LeonLenclos/camera-obscura/contenu/technique/abaque.md

**Ces abaques ont étés mesurés empiriquement avec la première série de process lens testée, à priori, ces objectifs ne seront pas utilisés dans la remorque.**

En fait c'est drôle parce que à l'époque où on a fait ces abaques on avait vraiment zéro connaissance théorique. Un peu après on a appris l'existence de *la relation de conjugaison* :

> l'inverse de la focale est égale à la somme des inverses des distances objet-lentille et image-lentille

Et du coup ces données quand on les regarde aujourd'hui on peut voir qu'ils vérifient cette loi (de manière très approximative car on ne mesurait pas vraiment les distances au centre optique de la lentille). 

## Les abaques

Pour le Apo-Nikkor 610mm posé contre la vitre à l'intérieur de la CO

| Distance Objet-Vitre | Distance Vitre-Image |
|---|---|
| 70 cm | 320 cm |
| 100 cm | 155 cm |
| 200 cm | 91 cm |
| 800 cm | 70 cm |
| infini | 68 cm |

Pour le Apo-Nikkor 610mm sur la planchette du soufflet de la caméra 04 (sprinter)

| Distance Objet-planchette | Distance plachette-Image |
|---|---|
| 295 cm | 77 cm |
| 149 cm | 100 cm |
| 110 cm | 125 cm |
| 97 cm | 150 cm |

Pour le Rotenstock 360mm posé contre la vitre à l'intérieur de la CO

| Distance Objet-Vitre | Distance Vitre-Image |
|---|---|
| 40 cm | 172 cm |
| 70 cm | 72 cm |
| 100 cm | 57 cm |
| 200 cm | 46 cm |
| 800 cm | 41 cm |
| infini | 39 cm |

Pour le Wray Lustrar 1060 mm sur la planchette du soufflet de la caméra 04 (sprinter)

| Distance Objet-planchette | Distance plachette-Image |
|---|---|
| infini | 117 cm |
| 360 cm | 150 cm |
| 280 cm | 175 cm |
| 210 cm | 200 cm |
