LeonLenclos/camera-obscura/contenu/technique/futs.md

# Fûts d'objectifs

Les lentilles sont placées dans des fûts qui se montent sur la tourelle.

Les dimensions de nos fûts sont calquées sur celles d'un fût acheté avec une lentille de 2250mm ø154

On identifie un fût avec un nom indiquant le diamètre de la lentille et la version. Par exemple la première version des fûts pour lentilles de ø154 s'appelle *154V1*

{% include pdf.html url="/contenu/plans/fut.pdf" %}

## Découpe laser

Fichiers :
- [Plan 138V1](/contenu/plans/fut138V1-laser.dxf)
- [Plan 154V1](/contenu/plans/fut154V1-laser.dxf)
- [Plan 80V1](/contenu/plans/fut80V1-laser.dxf)

## Détails

Les fûts sont fabriqués avec un assemblage de bagues découpées à la découpeuse laser. Chaque bague est identifiée par un nom gravé sur la bague. Le nom de la bague indique le modèle du fût et une lettre par exemple, la première bague d'un fût 154V1 porte le nom *154V1/A*

Bagues :

- Bague A : Son diamètre exterieur permet de s'encastrer dans la tourelle.
- Bague B : Il y en a 2. Ce sont les bagues les plus larges, elle maintiennent la lentille.
- Bagues C : Le diamètre interieur de ces bagues est ajusté au diamètre de la lentille. Selon l'epaisseur de la lentille il peut y avoir 0, 1 ou plusieurs bagues de ce type.
- Bague D : Une bague dans un autre materiaux d'une epaisseure choisie pour adapter le fût à l'epaisseur de la lentille.

Vis :

- 6 vis M3. L = epaisseur de la lentille + 18
- 3 vis M6. L = epaisseur de la lentille + epaisseur de la tourelle + 6
