LeonLenclos/camera-obscura/contenu/ecriture/conduite.md

{% include alert.html type="mettre-a-jour" %}

# Ébauche de conduite

- PLAQUE : titre (Générique début)
- FOCALE FACE : 750 mm
- OBTURATEUR : FACE
- DECORS SOL : chambre

---

- OBTURATEUR : NOIR
- PLAQUE : Prologue
- OBTURATEUR : FACE
- OBTURATEUR : NOIR

---

- PLAQUE : titres (Matin)
- OBTURATEUR : FACE

---

- OBTURATEUR : NOIR
- PLAQUE : OUT
- FOCALE FACE : 1000 mm
- MIROIR 45 : IN
- OBTURATEUR : FACE

---

- OBTURATEUR : NOIR
- MIROIR 45 : OUT
- PLAQUE : titre (niveau de l'eau)
- FOCALE FACE : 750 mm
- OBTURATEUR : FACE

---

- OBTURATEUR : NOIR
- PLAQUE : niveau de l'eau
- OBTURATEUR : FACE

---

- OBTURATEUR : NOIR
- PLAQUE : titre (plein emploi)
- OBTURATEUR : FACE

---

- FOCALE AMICI : 2000 mm
- OBTURATEUR : AMICI

---

- OBTURATEUR : NOIR
- FOCALE FACE : 750 mm
- PLAQUE : titre (periode heureuse)
- OBTURATEUR : FACE

---

- OBTURATEUR : NOIR
- PLAQUE : periode heureuse
- OBTURATEUR : FACE

---

- OBTURATEUR : NOIR
- PLAQUE : titre (lune)
- OBTURATEUR : FACE

---

- OBTURATEUR : NOIR
- DECORS AMICI: cuisine
- FOCALE AMICI : 1000 mm
- OBTURATEUR : AMICI

---

- OBTURATEUR : NOIR
- FOCALE FACE : 750 mm
- PLAQUE : titre (bon sens)
- OBTURATEUR : FACE

---

- PLAQUE : journal

---

- DECORS AMICI : OUT
- OBTURATEUR : AMICI
- FOCALE AMICI : 1000 mm

---

- PLAQUE : OUT
- REFLECTEUR : OUT
- FOND NOIR : IN
- FOCALE FACE : 1000 mm
- OBTURATEUR : FACE

---

- FOCALE FACE : 2000 mm

---

- OBTURATEUR : fondu au noir
- OBTURATEUR : NOIR
- PLAQUE : titre (mutation)
- FOND NOIR : OUT
- REFLECTEUR : IN
- FOCALE FACE : 750 mm
- OBTURATEUR : FACE

---

- OBTURATEUR : NOIR
- PLAQUE : mutation
- OBTURATEUR : FACE

---

- OBTURATEUR : NOIR
- PLAQUE : titre (vacances)
- OBTURATEUR : FACE

---

- PLAQUE : photo vacances 1

---

- PLAQUE : photo vacances 2

---

- PLAQUE : photo vacances 3

---

- OBTURATEUR : NOIR
- PLAQUE : titre (podium)
- OBTURATEUR : FACE

---

- OBTURATEUR : NOIR
- PLAQUE : podium
- OBTURATEUR : FACE

---

- OBTURATEUR : NOIR
- PLAQUE : titre (embouteillage)
- OBTURATEUR : FACE

---

- OBTURATEUR : NOIR
- DECORS AMICI : voiture 1
- FOCALE AMICI : 1000mm
- OBTURATEUR : AMICI

---

- PLAQUE : maquette printemps
- FOCALE FACE : 750mm
- OBTURATEUR : FACE

---

- FOCALE AMICI : 1000mm
- OBTURATEUR : AMICI

---

- FOCALE FACE : 750mm
- OBTURATEUR : FACE

---

- DECORS AMICI : voiture 2
- FOCALE AMICI : 1000mm
- OBTURATEUR : AMICI

---

- PLAQUE : maquette hiver
- FOCALE FACE : 750mm
- OBTURATEUR : FACE

---

- OBTURATEUR : NOIR
- PLAQUE : titre (blague)
- OBTURATEUR : FACE

---

- DECORS AMICI : OUT
- FOCALE AMICI : 750mm
- OBTURATEUR : AMICI

---

- OBTURATEUR : NOIR
- PLAQUE : titre (periode malheureuse)
- OBTURATEUR : FACE

---

- PLAQUE : periode malheureuse

---

- OBTURATEUR : NOIR
- PLAQUE : titre (golden record)
- OBTURATEUR : FACE

---

- PLAQUE : golden record 1

---

- PLAQUE : golden record 2

---

- PLAQUE : golden record 3

---

- OBTURATEUR : NOIR
- PLAQUE : titre (froid)
- OBTURATEUR : FACE

---

- FOCALE AMICI : 1000 mm
- OBTURATEUR : AMICI

---

- OBTURATEUR : NOIR
- PLAQUE : titre (comportement)
- FOCALE FACE : 750mm
- OBTURATEUR : FACE

---

- PLAQUE : comportement 1

---

- PLAQUE : comportement 2

---

- OBTURATEUR : NOIR
- PLAQUE : titre (mode)
- OBTURATEUR : FACE

---

- PLAQUE : photo mode

---

- OBTURATEUR : NOIR
- PLAQUE : titre (conversation)
- OBTURATEUR : FACE

---

- FOCALE AMICI : 750 mm
- OBTURATEUR : AMICI

---

- MIROIR 45 : IN
- PLAQUE : OUT
- DECORS SOL : briques
- FOCALE FACE : 1000mm
- OBTURATEUR : FACE

---

- FOCALE AMICI : 1000 mm
- OBTURATEUR : AMICI

---

- FOCALE FACE : 750mm
- OBTURATEUR : FACE

---

- FOCALE AMICI : 1000 mm
- OBTURATEUR : AMICI

---

- FOCALE FACE : 750mm
- OBTURATEUR : FACE

---

- OBTURATEUR : NOIR
- MIROIR 45 : OUT
- PLAQUE : titre (chanson)
- OBTURATEUR : FACE

---

- PLAQUE : OUT
- MIROIR 45 : IN

---

- MIROIR INCRUST : IN

---

- OBTURATEUR : NOIR
- PLAQUE : epilogue 1
- OBTURATEUR : FACE

---

- PLAQUE : epilogue 2

---

- PLAQUE : titre (generique de fin)

---

- OBTURATEUR : NOIR
