LeonLenclos/camera-obscura/contenu/objet/photos.md

# Photos

Si possibles imprimées en positif sur papier transparent (comme des diapositives). 1000×730 mm

- 3 photos de vacances à Saint-Tropez
- Une photo typique des années 2200
- La photo du journal.
