LeonLenclos/camera-obscura/contenu/prototypes/camera00.md

#  Mini Camera obscura

| prototype n° | 00 |
|---|---:|
| nom vernaculaire |  Mini camera obscura |
| début construction | mars 2023 |
| nombre de spectateur·ices | 1 |
| taille de l'image | 4×4 cm |
| distance de tirage min-max  | 45.5mm |
| dimensions exterieures | ? |
| objectif monté | Helios 44-2 / 2/58mm |

mini_chambre_2

## Description générale
En regardant à l'intérieur de cette camera obscura, on découvre une image à l'endroit d'environ 4 cm x 4 cm de ce qui est devant nous.

proto_0

## Allure
Une boite noire de forme parallélépipédique. L'image est projetée sur un dépoli à l'arrière du tube. Un prisme de Dove est placé devant l'objectif.

mini_chambre_3
## Matériaux

### Parois
- Carton-bois

### Écran
- Toile de rétroprojection (translucide/dépoli) tendue sur cadre acier

### Objectif
- objectif 24x36 monture M42 (Helios 44-2 / 2/58mm) 

### Accessoires
- L'objectif et le dépoli sont fixés sur des planchettes maintenues dans des rigoles.

## Évaluation des avantages et des inconvénients

### Avantages
- très léger
- parfait pour des tests

### Inconvénients
- image petite et tronquée
