LeonLenclos/camera-obscura/contenu/prototypes/camera03.md

#  Chambre grand format

| prototype n° | 03 |
|---|---:|
| nom vernaculaire | Chambre grand format |
| début construction | mars 2023 |
| nombre de spectateur·ices | 1 |
| taille de l'image | 100×73 cm |
| distance de tirage min-max  | ? |
| dimensions exterieures | ? |
| objectif monté | Process lens NIKON APO NIKKOR 9/610mm |

chambre_grand_format

## Description générale

En regardant dans le viseur situé à l'arrière de cette camera obscura, on observe une image à l'envers d'environ 100 cm x 73 cm (format 1,37) de ce qui est devant nous.

chambre_grand_format

## Allure

Une boite noire de forme pyramidale couchée, fixée sur un pied de projecteur fait office de viseur de champ. Elle est prolongée par un long soufflet blanc construit en deux parties et se termine par le support de l'objectif, lui-même fixé sur un pied. La forme évoque les chambres photographiques ultra grand format. Un pied intermédiaire limite l'affaissement du soufflet.

proto_03

## Matériaux

### Chassis
- Tube d'acier soudé (20 mm x 20 mm).

### Parois
- Contreplaqué 5 mm

chambre_grand_format

### Écran
- Toile de rétroprojection (translucide/dépoli) tendue sur cadre bois

### Objectif
- Process lens NIKON APO NIKKOR 9/610mm

apo_nikkor_9_610mm_2

### Accessoires

- Pour retourner l'image, il est envisagé d'utiliser un prisme en toit d'Amici, fabriqué avec 2 miroirs à 90°.

## Évaluation des avantages et des inconvénients

### Avantages
- image dans l'axe
- grand format
- grande amplitude de réglage du tirage

chambre_grand_format

### Inconvénients
- encombrement (ne passe pas les portes)
- à l'envers

## Usage

Ce prototype n'existe plus car le grand soufflet sert aussi au prototype sprinter et sera utilisé dans la remorque définitive. 

## Détails de construction et description technique

cotes proto02

### Soufflet

chambre_grand_format_1

- [Patron soufflet A en dxf](/contenu/plans/soufflet-cam03-A.dxf)
- [Patron soufflet A en pdf pour aperçu](/contenu/plans/soufflet-cam03-A.pdf)
- [Patron soufflet B en dxf](/contenu/plans/soufflet-cam03-B.dxf)
- [Patron soufflet B en pdf pour aperçu](/contenu/plans/soufflet-cam03-B.pdf)

Grand Soufflet :

- Grand cadre : 1000mm x 733mm (collage exterieur)
- Petit cadre : 740mm x 540mm (collage exterieur)
- Largeur plis : 100mm
- nombre de plis : 16

Petit Soufflet : 

- Grand cadre : 740mm x 540mm (collage exterieur)
- Petit cadre : 456mm x 373mm (collage exterieur)
- Largeur plis : 100mm
- nombre de plis : 16

cotes soufflet
cotes soufflet
