LeonLenclos/camera-obscura/contenu/prototypes/camera04.md

#  Chambre Sprinter

## Description générale
Un vehicule type Sprinter Mercedes est transformé en camera obscura en adaptant l'arrière du véhicule pour qu'il accueille un système soufflet/objectif. Un cadre sur lequel est fixé l'écran de 1,40 m x 0,95 m est installé à l'intérieur du camion. plusieurs personnes peuvent visionner simultanément l'image.

[une vidéo de test de la chambre sprinter au Quai des savoirs :](https://vimeo.com/showcase/10324493/video/826499165)

<div style="padding-bottom: 56.25%; max-width: 100%; position: relative;"><iframe src="https://player.vimeo.com/video/826499165?title=0&portrait=0&byline=0" width="800px" height="450px" style="position: absolute; top: 0px; left: 0px; width: 100%; height: 100%;" frameborder="0"></iframe></div>

## Allure
Un utilitaire avec un soufflet qui dépasse à l'arrière.

proto_04

Sprinter au Quai des savoirs

### Chassis
- Sprinter Mercedes

### Écrans testés
- Toile de rétroprojection (translucide/dépoli) tendue sur cadre

### Objectifs testés
- Process lens Wray Lustrar 1060 mm - f/16

wray_lustrar_16_1075mm_1

- Process lens Nikon APO Nikkor 610 mm - f/9
- Lentilles brutes d’opticien 2000mm 1500mm 1000mm 750mm - dia 65mm (ménisque)
- Lentille achromatique 2250 mm - f/14,6
 
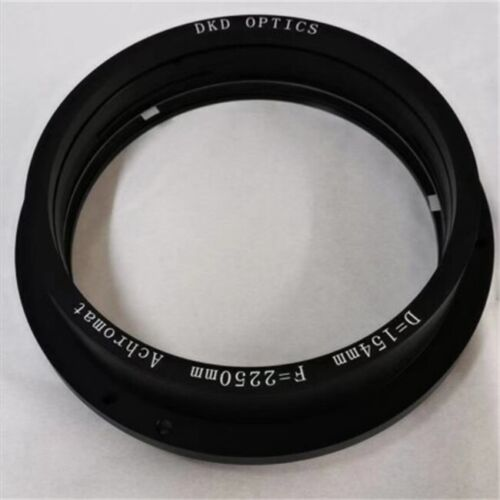
[picture p19: contenu/photos/acchromatic_154mm_f2250.jpg]
Achromatic lens dia:154mmm -_2250mm


### Accessoires
- Pour retourner l'image, un prisme en toit d'Amici, fabriqué avec 2 miroirs à 90°.

test prisme en toit au Quai des savoirs

## Évaluation des avantages et des inconvénients

### Avantages
- image dans l'axe
- ultra grand format

## Construction et améliorations
- Essais en résidence au quai des savoirs et à MIMA avec un écran dépoli.
- Au Quai des Savoirs, l'écran testé est un Teviloj retro translucide. Très lumineux mais trop directif, ce qui explique en partie le vignetage sur les tests.
- À MIMA, l'ecran testé est un Showtex GREY plus de 1300 x 840 mm. moins clair mais plus tolérant sur l'angle de vision.

## Détails de construction et description technique
cotes proto02
