LeonLenclos/camera-obscura/contenu/plans/implantation-carte-ves.pdf

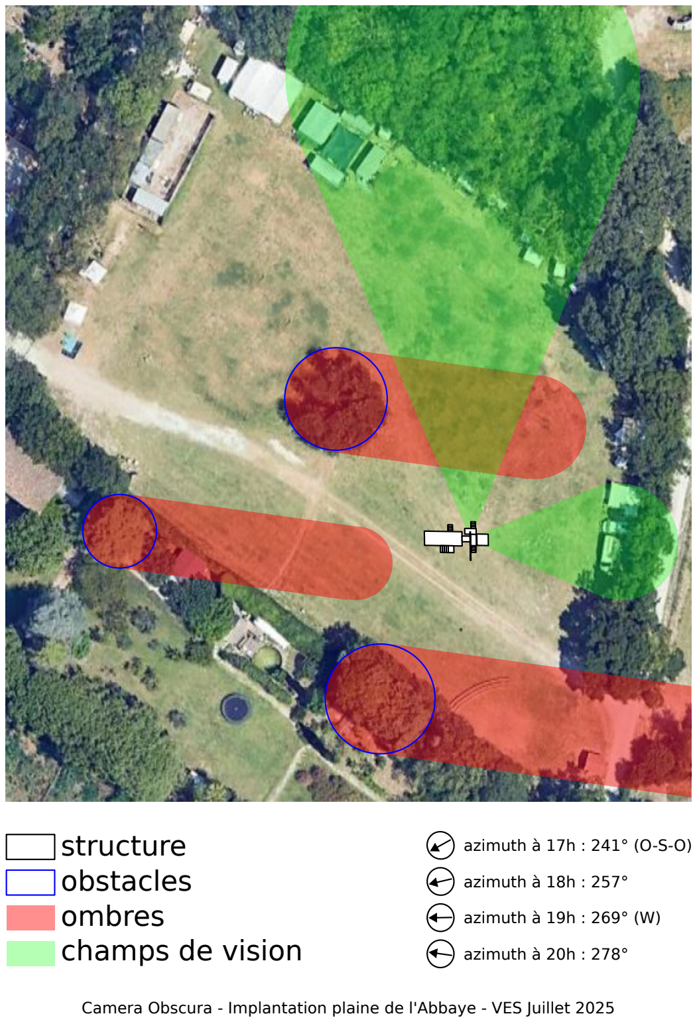
[picture p30: page 1]

# structure obstacles ombres champs de vision

Camera Obscura - Implantation plaine de l'Abbaye - VES Juillet 2025 azimuth à 17h : 241° (O-S-O)

azimuth à 19h : 269° (W)

azimuth à 20h : 278°

azimuth à 18h : 257°
