LeonLenclos/camera-obscura/contenu/plans/implantation-carte-cognac.pdf

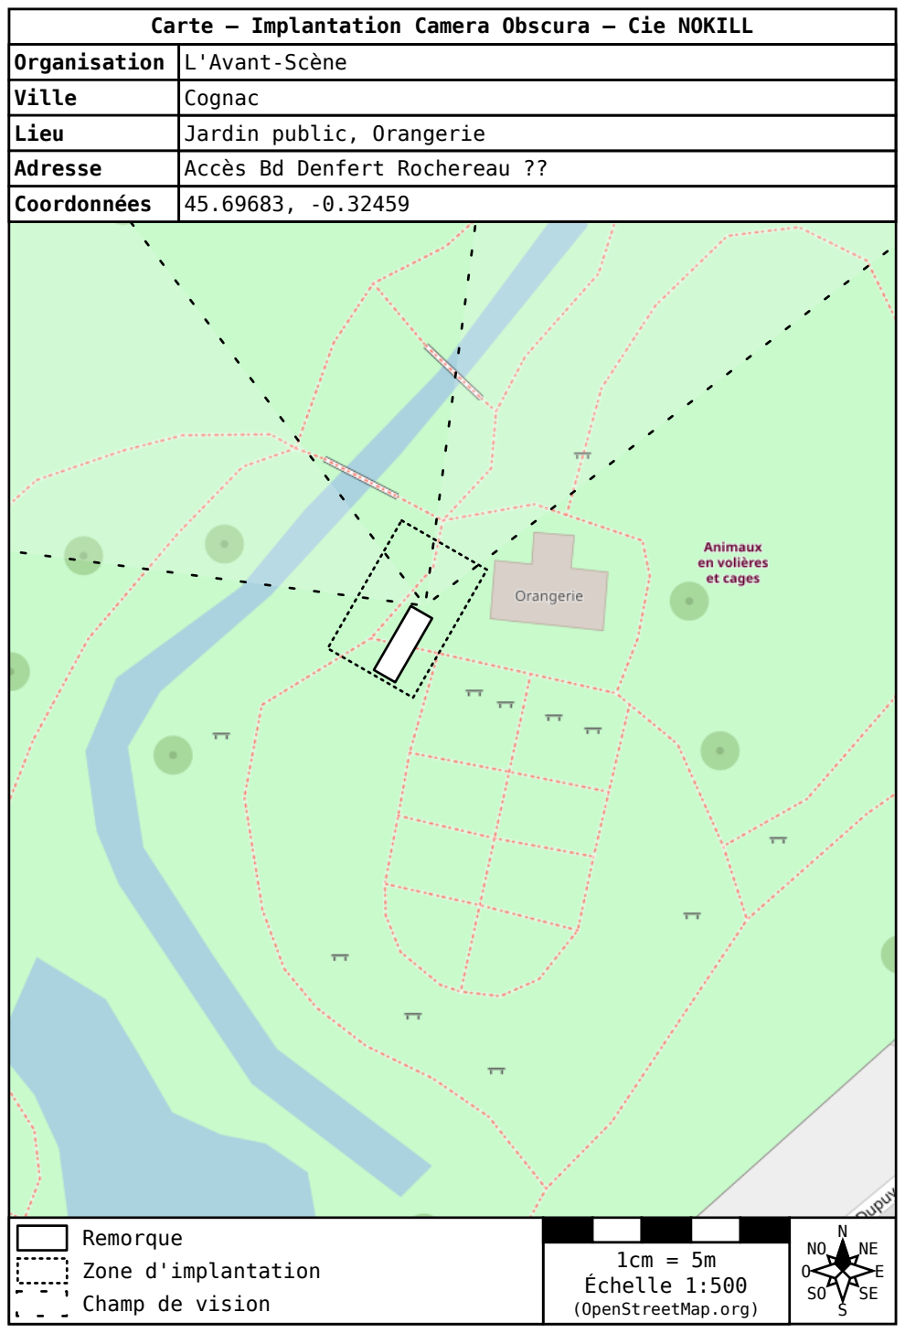
[picture p31: page 1]

Carte — Implantation Camera Obscura — Cie NOKILL
Organisation | L'Avant-Scène
Ville | Cognac
Lieu | Jardin public, Orangerie
Adresse | Accès Bd Denfert Rochereau ??
Coordonnées | 45.69683, -0.32459

(OpenStreetMap.org)

NO | NE
SO | SE

N

S

O | E

Remorque
Zone d'implantation
Champ de vision

Échelle 1:500

1cm = 5m
