LeonLenclos/camera-obscura/contenu/plans/implantation-carte-periscope.pdf

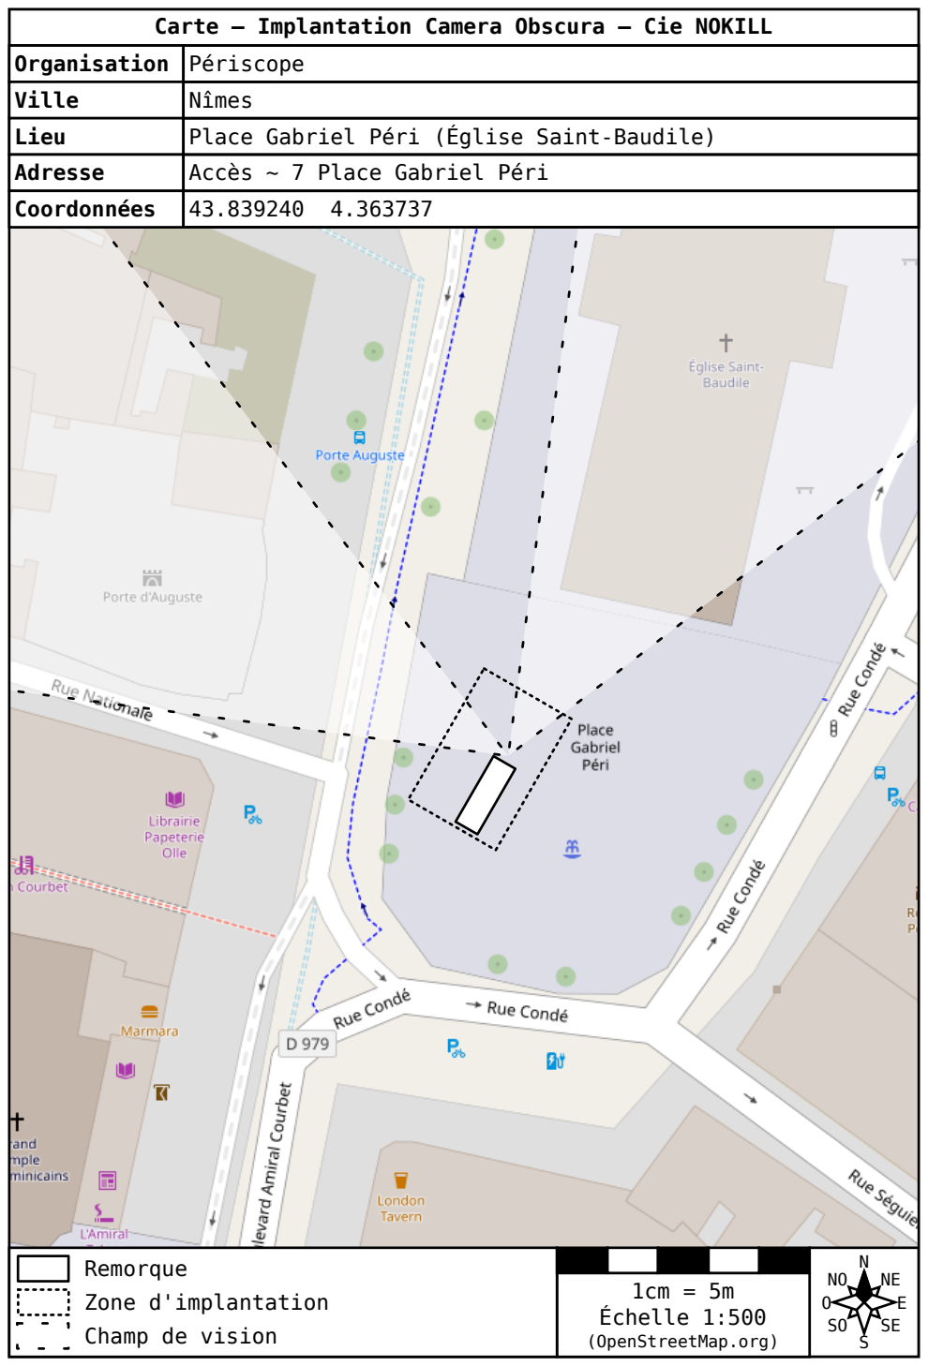
[picture p32: page 1]

Carte — Implantation Camera Obscura — Cie NOKILL
Organisation | Périscope
Ville | Nîmes
Lieu | Place Gabriel Péri (Église Saint-Baudile)
Adresse | Accès ~ 7 Place Gabriel Péri
Coordonnées | 43.839240 4.363737

(OpenStreetMap.org)

NO | NE
SO | SE

N

S

O | E

Remorque
Zone d'implantation
Champ de vision

Échelle 1:500

1cm = 5m
