LeonLenclos/camera-obscura/contenu/objet/rouleau-photo.pdf

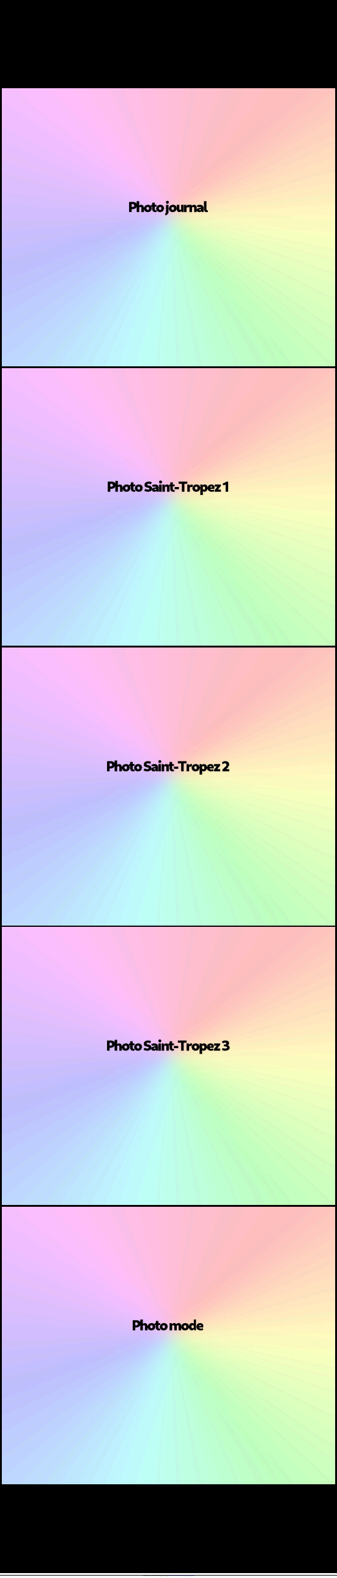
[picture p34: page 1]

Ce document a été généré le 28/05/2024 à partir de la page camera-obscura.cienokill.fr/contenu/objet/rouleau-photo.md
