LeonLenclos/camera-obscura/contenu/plans/implantation-carte-mima.pdf

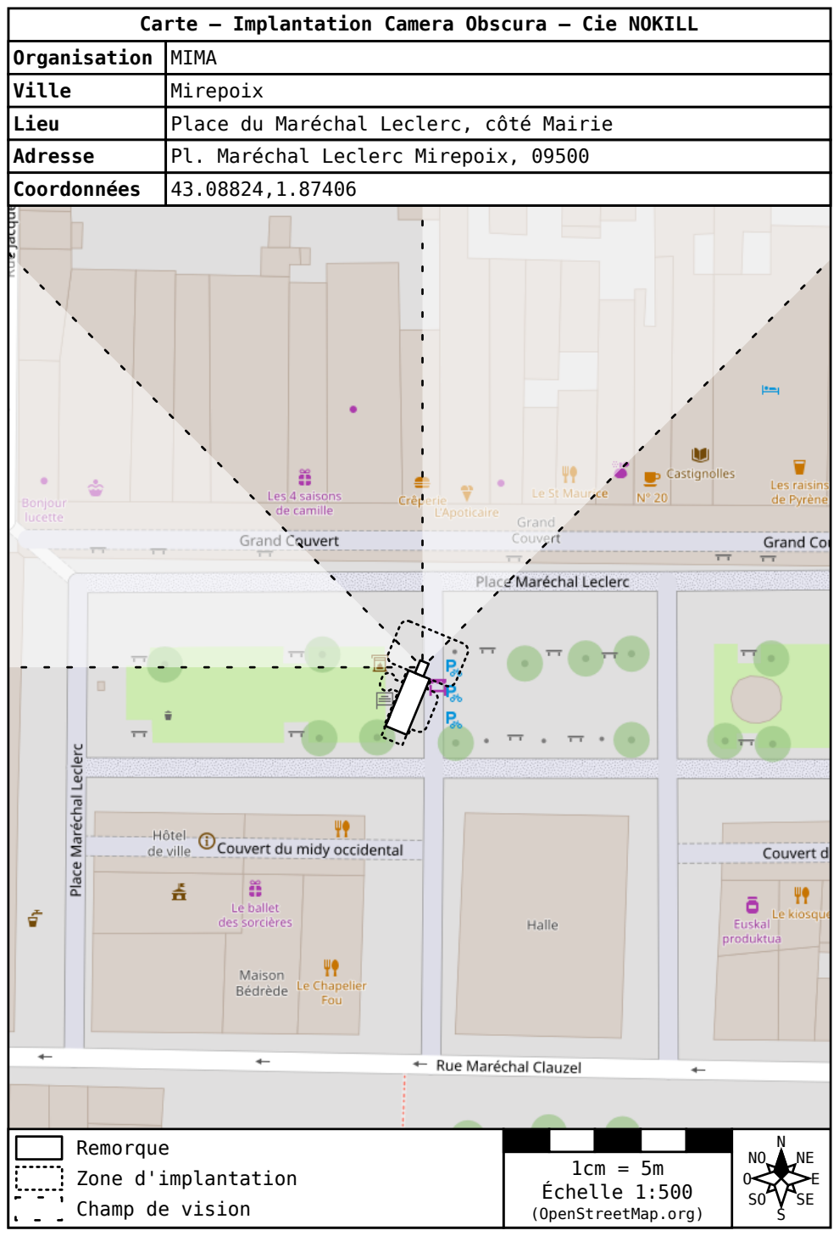
[picture p35: page 1]

Carte — Implantation Camera Obscura — Cie NOKILL
Organisation | MIMA
Ville | Mirepoix
Lieu | Place du Maréchal Leclerc, côté Mairie
Adresse | Pl. Maréchal Leclerc Mirepoix, 09500
Coordonnées | 43.08824,1.87406

(OpenStreetMap.org)

NO | NE
SO | SE

N

S

O | E

Remorque
Zone d'implantation
Champ de vision

Échelle 1:500

1cm = 5m
