LeonLenclos/camera-obscura/contenu/plans/implantation-carte-arto.pdf

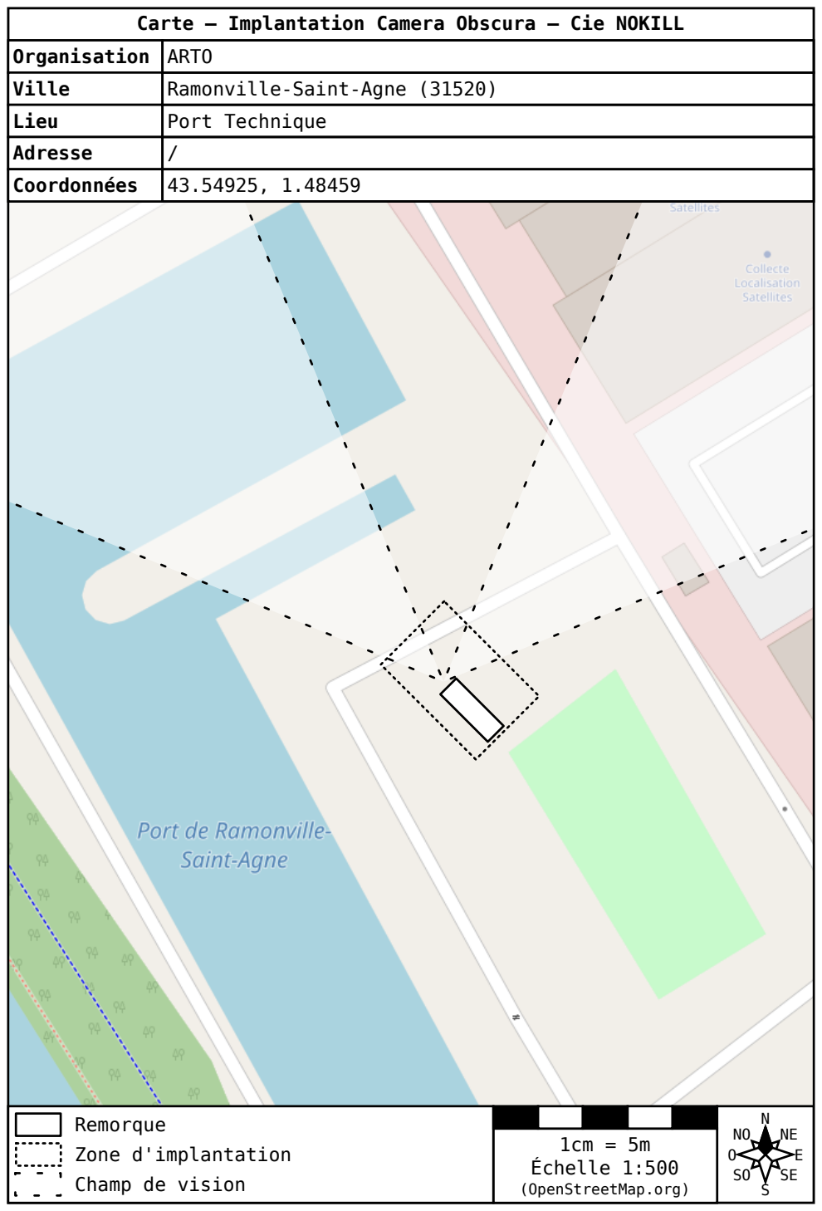
[picture p36: page 1]

Carte — Implantation Camera Obscura — Cie NOKILL
Organisation | ARTO
Ville | Ramonville-Saint-Agne (31520)
Lieu | Port Technique
Adresse | /
Coordonnées | 43.54925, 1.48459

(OpenStreetMap.org)

NO | NE
SO | SE

N

S

O | E

Remorque
Zone d'implantation
Champ de vision

Échelle 1:500

1cm = 5m
