LeonLenclos/camera-obscura/contenu/legal/README.md

# Légal

## Rappel

Camera Obscura est une création de la Cie Nokill, c'est une remorque aménagée en salle de spectacle itinérante. 

## Homologation du véhicule

À compléter

## Établissement Itinérant Recevant du Public

Camera Obscura est un Établissement Recevant du Public (ERP) Itinérant. Cette classification nous oblige à respecter un certain nombre de règles détaillées ci-dessous.

### Classification de l'établissement

Camera Obscura est un **Établissement Recevant du Public Itinérant** (ERP Itinérant) au sens de l'[arrêté du 4 mai 2023 portant expérimentation d'itinérance des établissements recevant du public*](https://www.legifrance.gouv.fr/jorf/id/JORFTEXT000047533626)) car toujours installé pour une durée inférieure à six mois, destinés par conception à être clos et dans lesquels l'effectif admis est inférieur à 700 personnes.

Camera Obscura est un **ERP de type L** au sens du classement établis par l'[article GN1 de l'Arrêté du 25 juin 1980 portant approbation des dispositions générales du règlement de sécurité contre les risques d'incendie et de panique dans les ERP](https://www.legifrance.gouv.fr/loda/article_lc/LEGIARTI000045143487)

Pour rappel Camera Obscura __n'est pas__ soumis aux contraintes s'appliquant aux **Locaux destinés au sommeil** tel que défini par l'[article GN1](https://www.legifrance.gouv.fr/loda/article_lc/LEGIARTI000045143487)

Camera Obscura est un **Établissement Recevant du public** (ERP) de **Catégorie 5** tel que défini par l'[article R143-19 du Code de la construction et de l'habitation](https://www.legifrance.gouv.fr/codes/article_lc/LEGIARTI000043818977) et par l'[Article PE2 de l'Arrêté du 25 juin 1980](https://www.legifrance.gouv.fr/loda/article_lc/LEGIARTI000045143485) car c'est un Établissements de type L (Salle de spectacles, de projections) dans lequel l'effectif admis est inférieur à 50 personnes.

Camera Obscura est un **ERP du second groupe** tel que défini par [Article GN1 de l'arrêté du 25 juin 1980](https://www.legifrance.gouv.fr/loda/article_lc/LEGIARTI000045143487)

Les Ossatures destinées à supporter des personnes (OP) de Camera Obscura sont Catégorisées **OP1** par l'[article 4 de l'annexe de l'arrêté du 25 juillet 2022 fixant les règles de sécurité et les dispositions techniques applicables aux structures provisoires et démontables](https://www.legifrance.gouv.fr/jorf/article_jo/JORFARTI000046144010), car leur hauteur de chute est inférieure à 1,20 mètre.

Les Ossatures d'équipements scéniques (OS) de Camera Obscura sont Catégorisées **OS1** par le [même article](https://www.legifrance.gouv.fr/jorf/article_jo/JORFARTI000046144010), car leur point le plus haut est inférieur à 3,50 mètre.

### Obligations de contrôle, de vérification et d'inspection en matière de solidité et de stabilité

Vu l'[arrêté du 4 mai 2023 portant expérimentation d'itinérance des établissements recevant du public](https://www.legifrance.gouv.fr/jorf/id/JORFTEXT000047533626) ;  
Vu l'[arrêté du 25 juillet 2022 fixant les règles de sécurité et les dispositions techniques applicables aux structures provisoires et démontables](https://www.legifrance.gouv.fr/jorf/id/JORFTEXT000046143966),  

Nous sommes tenu à certaines obligations de contrôle.

#### Partage des obligations entre la compagnie et l'organisation de l'évènement

Les obligations sont partagées entre la compagnie et l'organisation de l'évènement où est joué le spectacle.

La compagnie s'acquitte des obligation désignés comme :

- **obligations du fabricant** (par l'arrêté du 25 juillet 22) ;
- **obligations du propriétaire** (par l'arrêté du 25 juillet 22) ;
- **obligations de l'installateur** (par l'arrêté du 25 juillet 22).

L'organisation de l'évennement s'acquitte des obligations désignées comme :

- **obligations de l'organisateur** (par l'arrêté du 25 juillet 22).

Les obligations désignées comme **obligation de l'exploitant** (par l'arrêté du 4 mai 2023) sont partagées au cas par cas entre la compagnie et l'organisation de l'événement.

#### Obligation de l'organisation de l'événement

La compagnie laisse à la charge de l'organisation de l'événement les obligations suivantes :

- **Inspection en exploitation** : faire procéder à une inspection par un technicien compétant avant l'admission du public conformément à l'[article 40 de l'arrêté du 25 Juillet 2022](https://www.legifrance.gouv.fr/jorf/article_jo/JORFARTI000046144050)
- **Obtenir l'autorisation du maire** : faire parvenir au maire les documents fournis par la compagnie conformément à l'[article 6 de l'arrêté du 4 mai 2023](https://www.legifrance.gouv.fr/jorf/article_jo/JORFARTI000047533639) Pour qu'il délivre une autorisation d'implantation. Ces documents sont le [registre de sécurité](registre-securite.md) (contenant l'attestation de conformité) et le [contrôle de conception](attestation-fabricant-controle-conception.md) (attestation du fabricant). 

Note : L'[article 3 de l'arrêté du 4 mai 2023](https://www.legifrance.gouv.fr/jorf/article_jo/JORFARTI000047533634) dispense l'exploitant de l'obligation d'établir le dossier de sécurité demandé par l'[article 39 de l'arrêté du 25 Juillet 2022](https://www.legifrance.gouv.fr/jorf/article_jo/JORFARTI000046144049)

#### Notice technique

Voir le document : [**Notice technique**](notice-technique.md)

L'[article 36 de l'arrêté du 25 Juillet 2022](https://www.legifrance.gouv.fr/jorf/article_jo/JORFARTI000046144046) nous oblige à fournir une notice technique en tant que fabriquant. Le modèle de cette Notice technique est donné à l'annexe I de l'[arrêté](https://www.legifrance.gouv.fr/jorf/id/JORFSCTA000046143987).

#### Contrôle de la solidité et de la stabilité à la conception (Contrôle de conception)

Voir le document : [**Attestation du fabricant**](attestation-fabricant-controle-conception.md)

L'[article 37 de l'arrêté du 25 Juillet 2022](https://www.legifrance.gouv.fr/jorf/article_jo/JORFARTI000046144047) nous dispense, en tant qu'ensemble démontable de catégories **OP1** et **OS1** de faire l'objet d'un contrôle par un Organisme accrédité ou un Contrôleur technique agréé. 

Nous avons simplement l'obligation de fournir une déclaration du fabricant attestant du respect des dispositions relatives à la solidité et à la stabilité de ce même arrêté.

L'[arrêté du 4 mai 2023](https://www.legifrance.gouv.fr/jorf/id/JORFTEXT000047533626) confirme que cela s'applique à notre établissement en tant qu'**EIRP du second groupe**. 

#### Inspection annuelle

Voir le document : [**Inspection annuelle**](inspection-annuelle.md)

L'[article 7 §3 de l'arrêté du 4 mai 2023](https://www.legifrance.gouv.fr/jorf/article_jo/JORFARTI000047533640) rappelle l'obligation de faire établir un rapport d'inspection annuel par un·e technicien·ne compétent·e. Un tel rapport doit être établis chaque année suite à une visite du ou de la technicien·ne dans un contexte d'exploitation.

#### Vérification de montage

Voir le document : [**Attestation de bon montage**](attestation-bon-montage.md)

L'[article 38 de l'arrêté du 25 Juillet 2022](https://www.legifrance.gouv.fr/jorf/article_jo/JORFARTI000046144048) Précise qu'en tant qu'ensemble démontable de catégories **OP1** et **OS1**, une attestation de bon montage établit à chaque montage par l'installateur vaut document de vérification (L'organisateur n'a pas besoin de faire intervenir un organisme accrédité).

L'attestation pré-remplie ci-dessus a été rédigée en suivant le modèle de l'annexe V de l'[arrêté](https://www.legifrance.gouv.fr/jorf/id/JORFSCTA000046143987)

L'[arrêté du 4 mai 2023](https://www.legifrance.gouv.fr/jorf/id/JORFTEXT000047533626) confirme que cela s'applique à notre établissement en tant qu'**EIRP du second groupe**. 

#### Registre de sécurité

Voir le document : [**Registre de sécurité**](registre-securite.md)

Les articles 6 et 7 de l'[arrêté du 4 mai 2023](https://www.legifrance.gouv.fr/jorf/id/JORFTEXT000047533626) précise qu'un registre de sécurité doit être tenu et mis à disposition des autorités.

Le registre de sécurité est composé de deux parties, la première partie constitue l'[**attestation de conformité**]](contenu-attestation-conformite.md) qui est délivrée par le Préfet pour une durée d'un an. La deuxième partie est le [**registre d'exploitation**](contenu-registre-exploitation.md)

#### Documents annexes

Les documents cités ci-dessus nécessitent d'autres documents en annexes :

- [**Schéma d'implantation**](../technique/implantation) (Ce document est spécifique à chaque évennement)
- [**Notice de montage**](../technique/notice-montage.md)
- **Rapport de vérifications des installations électriques**  (voir [Cet article (§2 en ce qui nous concerne)](https://www.legifrance.gouv.fr/jorf/article_jo/JORFARTI000046144037))
- **Plan des installations de ventilation**
- [**Consignes de sécurité**](consignes-de-securite.md)
- **Historique des exercices contre l'incendie**
- [**PV de réaction au feu**](pv-reaction-feu.pdf)

#### Lettre type

Voir le document : [**Demande d'attestation de conformité**](lettre-prefet.md)

## TODO

### TODO Administratif 

- Passage à la DREAL
- Finir de rédiger tous les documents ci-dessus
- Demande d'attestation de conformité au prefet

### TODO Materiels

Modification matérielles a effectuer pour etre en accord avec tous les trucs cités au dessus

#### Mise aux normes de l'installation électrique

- Installer un tableau

#### Installer un extincteur

- 6L à eau pulverisée

#### Marquages des éléments démontables 

Selon [cet article](https://www.legifrance.gouv.fr/jorf/article_jo/JORFARTI000046144015)

Il faut marquer :

- tous les éléments des escaliers
- les éléments de la structure scénique

Il faut indiquer :

- le nom ou le sigle du fabricant
- la référence du produit
- l'année de fabrication

Un marquage au feutre indélibile peut convenir. La reference de l'element est deja souvent présente il faut ajouter "NOK 2024".
