LeonLenclos/camera-obscura/contenu/ecriture/README.md

# Écriture

*En travaux*

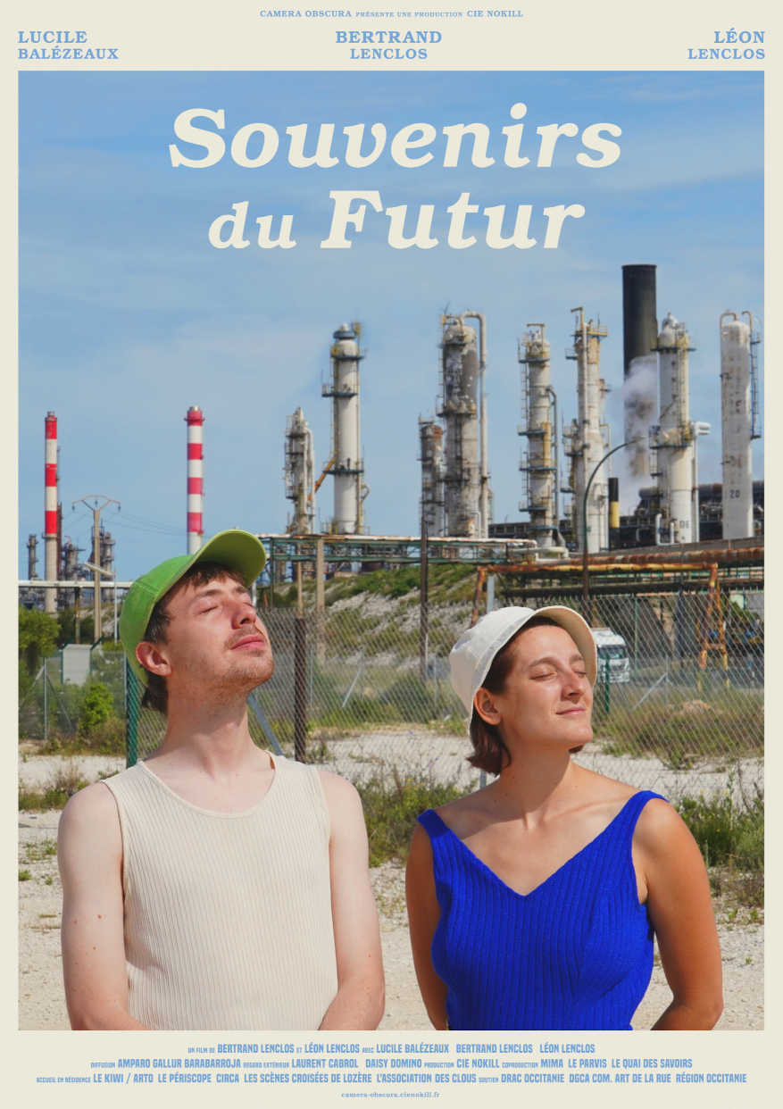
[picture p37: contenu/photos/affiche-souvenirs.png]
Affiche Sovenirs du futur
   

Souvenirs du Futur un court metrage de 30 minutes sous forme de notes ou de fragments qui s'enchaînent.

## écriture en cours
- [Le manifeste pour souvenirs du futur](manifeste.md), les règles qui guident l'écriture.
- [*Souvenirs du futur*](souvenirs-du-futur.md), Le film.
- [Textes voix-off](textes-voix-off.md), les textes interprétés pendant le films
- [Story Board](storyboard.md), Storyboard pour *Souvenirs du futur*.
- [intro](intro.md), Le texte d'intro pour accueillir les gens dans la camera obscura.
- [Conduite Léon](conduite-leon.md), Une ébauche de conduite.
- [Conduite Lucile](conduite-lucile.md), Une ébauche de conduite.

## archives

- [Texte de présentation](presentation.md)
- [Narratologie](narratologie.md), Comment construire le film (questions obsolètes)
- [Jeu d'impro](jeuimpro.md), Un petit jeu à jouer.
- [Scenario 1](scenar1.md), Le scénario qu'on avait mis dans le dossier de création.
- [Scenario 2](scenar2.md), Le bout de scenario à tester à Mirepoix.
- [Scenario 3](scenar3.md), Un autre vieux bout de scénario.
- [Sequences](sequences.md), Des idées de séquences.
- [Vrac](vrac.md), Des idées en vrac.
- [Conduite](conduite.md), Une vieille ébauche de vieille conduite.
