LeonLenclos/camera-obscura/contenu/bibliographie.md

# La bibliothèque du spectacle

(Livres que l'on a en physique)

- [*Bases d'optique géométrique*, Olivier Morizot, aux Presses Universitaires de Provence, 2016](https://presses-universitaires.univ-amu.fr/bases-doptique-geometrique-0)
- [*Analogue photography*, ars-imago Vetro, 2018](https://vetroeditions.com/products/analogue-photography)
- [*Lanterne magique, avant le cinéma*, Jérôme Prieur, fario, 2021](https://editionsfario.fr/livre/lanterne-magique/)
- [*Je me souviens*, Georges Pérec, Fayard, 2013 (ed. originale : 1978)](https://www.fayard.fr/livre/je-me-souviens-9782213677972/)
- [*Semi Science-Fiction*, Léa Murawiec, Flutiste, 2023](http://flutiste.fr/2023/07/23/semi-science-fiction/)
- [*Le livre Oracle*, Xavier Bouyssou, éditions 2024, 2023](https://www.editions2024.com/livres/le-livre-oracle)

## Bibliothèque rêvée

(Livres qu'on a pas)

- [*Magie lumineuse : Du théâtre d'ombres à la lanterne magique*, Jac Remise, Pascale Remise, Régis Van de Walle, ed. Balland, 1979](https://ccfr.bnf.fr/portailccfr/ark:/16871/0019045076)
- [*Lanterne magique et film peint*, Laurent Mannoni, Donata Pesenti Campgnoni, éditions de la Martinière, 2009](https://eman-archives.org/CinEx/files/show/87) (catalogue d'une exposition à la cinémathèque française, le livre a l'air magnifique)
- [*Optical amusements: magic lanterns and other transforming images. A catalog of popular entertainments.*  	Richard Balzer, 1987(?)](https://www.bdcmuseum.org.uk/explore/item/39169/) (par Dick Balzer le grand collectionneur de jouets optique)
 
# Papiers scientifique / Thèses / Mémoires

- [Claude Martin-Rainaud. *Dans le regard de la chambre*. Art et histoire de l’art. Université d’Avignon, 2015](https://theses.hal.science/tel-01248530)
- [*Le végétal est photographie*, Mariève Pelletier (Mémoire)](https://www.esam-c2.fr/IMG/UserFiles/docs/memoires/2017_pelletier_marieve.pdf)
- [*Lanterne magique, Avant le cinéma*, Jérôme Prieur, aux éditions fario, 2021](https://editionsfario.fr/livre/lanterne-magique/)
- [*Optique, Une approche experimentale et pratique*, Sylvain Houard, aux éditions de boeck,  2011](https://www.deboecksuperieur.com/ouvrage/9782804163396-optique)

# Liens

## Théorie

- [Schema interactifs d'optique géométrique](https://phyanim.sciences.univ-nantes.fr/optiqueGeo/index.php)
- [chaîne youtube de photo avec pas mal de contenus intéressants](https://youtube.com/@PhotoGraal)
- [geogebra](https://www.geogebra.org/calculator/hahmryyn)
- [logiciel (payant) pour créer des optiques](https://www.zemax.com/)
- [Peut on considérer qu'un objectif (assemblage de lentilles) est géométriquement équivalent à une lentille mince](https://www.galerie-photo.com/un-objectif-photo.html)
- [Calculer l'equation d'un plan](https://onlinemschool.com/math/assistance/cartesian_coordinate/plane/)
- [Calculer l'angle entre deux plans](https://onlinemschool.com/math/assistance/cartesian_coordinate/plane_angl/)
- [Calculer l'angle entre deux vecteurs 3D](https://openclassrooms.com/forum/sujet/mathsespace-3d-calculer-l-angle-entre-2-vecteurs-87922)

## Gramophone

- https://forum.talkingmachine.info/viewtopic.php?f=3&t=30997
- [forum Talking machine](https://forum.talkingmachine.info/)
- [Vidéo à propos du HMV 102](https://www.youtube.com/watch?v=AYn7aZZBMRA)

## Soufflets

- [Tuto détaillé général](https://www.galerie-photo.com/construire-soufflet-chambre-photo.html)
- [Tuto plus précis](http://www.disactis.com/soufflet/soufflet.php)
- [Tuto de monsieur Smets](https://docplayer.fr/12405417-Fabriquez-votre-soufflet.html)
- [Article de blog avec photos HD d'un vieux soufflet](https://delalumieredanslatelier.blogspot.com/2019/06/appareil-photo-soufflet-marque-nagel-n.html)

## Animation 

- [Terry Gilliam, cutout anim](https://youtu.be/KOqcHCEqO1k)

## Photo très grand format

- [Article sur des photographes très grand format](https://fstoppers.com/diy/photographer-creates-gigantic-ultra-large-format-digital-camera-571295)
- [Article de blog sur l'ultra-grand format](https://photographylife.com/ultra-large-format-cameras)
- [Définition de process lens discutée sur un forum de photo](https://www.photo.net/forums/topic/48909-what-is-a-process-lens/)
- [John Chiara photographe qui a une CO remorque pour faire du très grand format](https://www.johnchiara.com/films)

## Objectifs très grands formats / process lens

- [Doc technique détaillée sur les objectifs grands formats de Rodenstock](http://www.dmin-dmax.fr/chambre/archives_techniques/rodenstock_2000.html)

## Sténopé 

- [Tuto détaillé sur la photo au sténopé](https://galerie-photo.com/stenope.html)
- [Video stenopé numérique](https://www.youtube.com/watch?v=yWew2kOWTiA)

## Papier inversible 

- [Discussion autour du papier inversible sur un forum de photo ](http://www.galerie-photo.info/forumgp/read.php?3,239522)
- [DIRECT POSITIVE PAPER harman chez Ilford](https://www.ilfordphoto.com/harman-direct-positive-paper-roll)
- [direct positiv paper, différentes refs (eshop)](https://www.macodirect.de/en/paper/direct-positive-papers/)

## Camera obscura

- [Camera Obscura & World of Illusions , un musée à Édinburgh](https://www.camera-obscura.co.uk/attractions/the-camera-obscura)
- [Site très riche à propos de la CO par un restaurateur/créateur de CO](http://www.camera-obscura.org.uk/Camera_Obscura/Welcome.html)
- [Thomas Mezzanotte, artiste ayant notamment construit une CO dans une sorte de tente](https://thomas-mezzanotte.squarespace.com/)
- [Double CO sur un bateau sur le danube](https://olafureliasson.net/artwork/camera-obscura-fuer-die-donau-2004/)
- [CO sur une plage vers San Fransisco](https://youtu.be/qvwpDIlN25o)

## Miroirs caustiques

- [Rayform, fabriquant de miroirs caustiques](https://rayform.ch/)
- [Vidéo à propos des miroirs caustiques de rayform](https://www.youtube.com/watch?v=wk67eGXtbIw)

## True mirrors

- [Prisme en toit d'Amici](https://fr.wikipedia.org/wiki/Prisme_en_toit_d%27Amici)
- [La boutique](https://store.truemirror.com/)
- [La vidéo où le createur dit qu'il utilise des first surface mirror](https://www.youtube.com/watch?v=oHeOf9MZ49o)
- [la vidéo du mec là](https://www.youtube.com/watch?v=x2owiSx0biU)

## First surface mirror

- [How to Make a Front Surface Mirror (Quick & Easy Techniques)](https://medium.com/geekculture/how-to-make-a-front-surface-mirror-quick-easy-techniques-c1ba3ecf6347)
- [FSM (Fournisseur)](https://firstsurfacemirror.com/)

## prismes

- [tuto prisme eau ](https://www.instructables.com/Optical-Water-Prism/)

## Lanternes magiques

- [Super blog sur les projections d'images fixes avec une bonne piste de liens](http://diaprojection.fr/)
- [Lanternes magiques](https://en.wikipedia.org/wiki/Magic_lantern)
- [petit Doc en anglais](https://youtu.be/w1XkqtzLfKo)
- [Collection de jouets optique de Dick Balzer, notament lanternes magiques (archive)](https://wayback.archive-it.org/12244/20190603142755/https://www.dickbalzer.com/)

## Historique

- [Objectif de CO avec prisme intégré 18e sciècle :](http://www.niepce-daguerre.com/objectif_de_camera_obscura.html)

## Antotypes

- [Anthotypes: explore the darkroom in your garden - Le livre de ref](http://leonlenclos.net/pro/pirate/anthotypes-explore-the-darkroom-in-your-garden-and-make-photographs-using-plants-1466261005-9781466261006_compress.pdf)
- [Recette à base d'épinard](http://wiki.scienceamusante.net/index.php/Les_anthotypes)
- [Mary Somerville, inventeuse oubliée de l'anthotypie ](https://en.wikipedia.org/wiki/Mary_Somerville)

# Spectacles / Camera Obscura

- Voir le travail d'Anne Bitrand, qui a travaillé avec des camera obscura https://www.remouleurs.com/spectacles/in-situ/exprojections
- Voir le travail de tricyclique dol avec des camera obscura https://vousetesicitricycliquedol.wordpress.com/l-e-s-p-e-c-t-a-c-l-e/
- Voir le Roulot‘ographe de Neckel Scholtus (une camera obscura)
- Voir le travail de Manual Cinema à Chicago https://manualcinema.com
