LeonLenclos/camera-obscura/contenu/remorque.md

#  Chambre Remorque

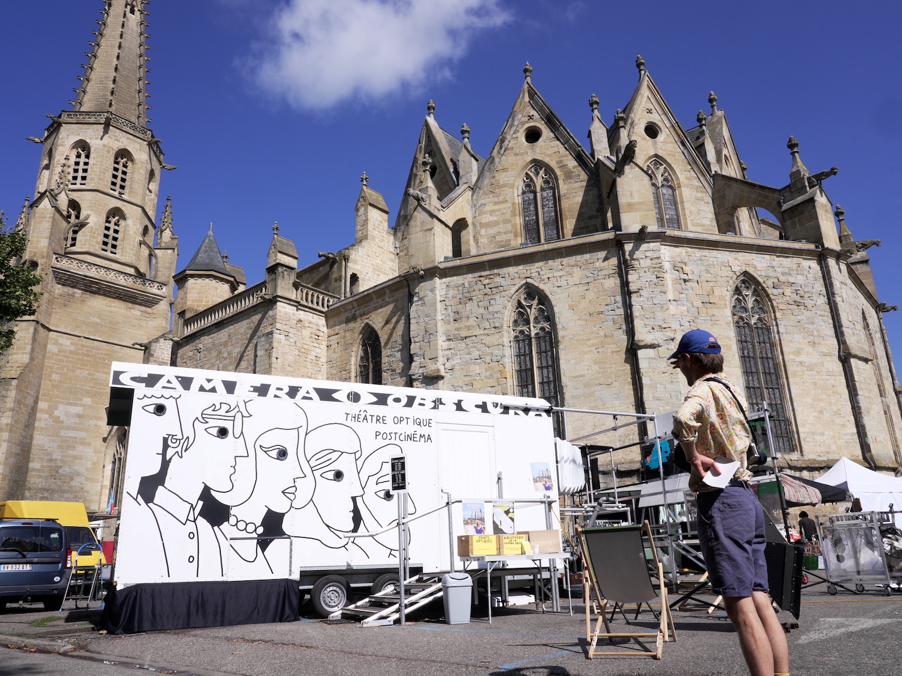
[picture p38: contenu/photos/co-mima-2.JPG]
Photo de la remorque à MIMA


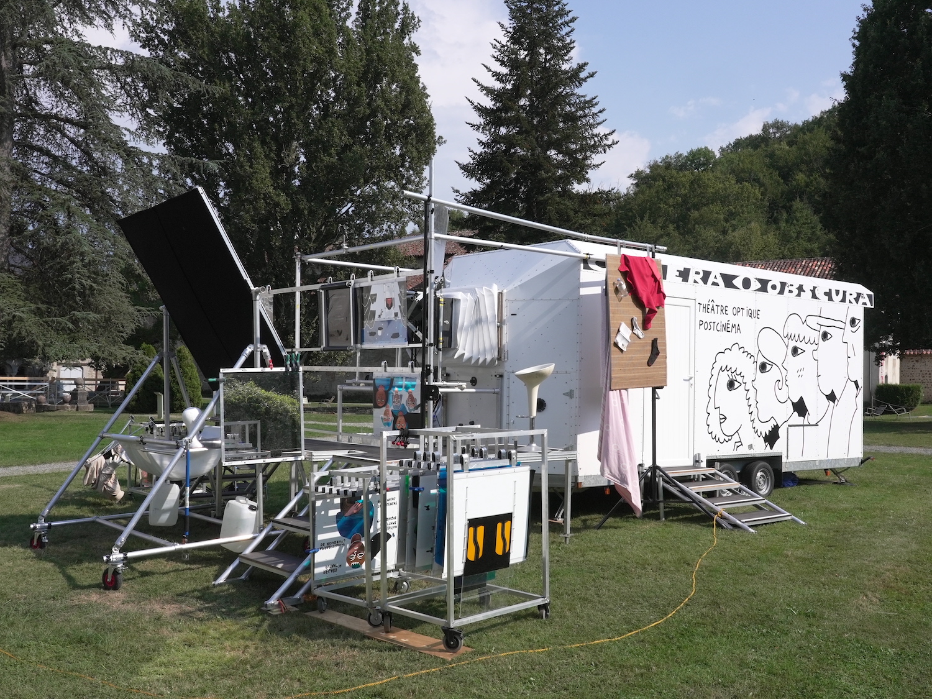
[picture p39: contenu/photos/co-escaladieu-1.JPG]
Photo de la remorque à l'escaladieu


## Description de la remorque

Le spectacle *Camea Obscura* se regarde de l'intérieur d'une remorque, un cinéma itinérant construit sur mesure équipé d'un gradin de 25 places et d'un écran de 1,80 m de large. La remorque se déploie avec un système optique (soufflet, objectifs, obturateurs, etc.) à l'avant du dispositif, de larges escaliers pour l'accès public et une structure scénique servant d'espace de jeu et de manipulation.

## Matériaux

### Chassis et structure
- Remorque BW TINY HOUSE CH 600 en galva, charpente et carosserie en alu.

### Isolation et finition
- Laine de coton 100mm, Panneau de bois et molleton.

### huisserie
- Porte isolante alu et hublot double vitrage.

### Écran
- Toile de rétroprojection (translucide/dépoli) tendue sur cadre.

### Fauteuils
- Structure en alu, assise et dossier en contre-plaqué, mousse et tissus.

### souflet
- skay blanc, carton et coton gratté noir.

### Objectif
- bonnettes macros pour objectifs cinéma (dia : 138 mm) et palets bruts d'opticien en polycarbonate (dia : 80 mm).

### Miroirs
- Pour retourner l'image, on utilise un prisme en toit d'Amici, fabriqué avec 2 miroirs à 90° fixés sur un cadre alu.

### Exostructure et praticables
- structure en tube alu carré 30 et rond 50 mm et 35 mm, plancher en CP antidérapant
  
## Évaluation des avantages et des inconvénients

### Avantages
- image dans l'axe
- ultra grand format
- très confortable pour le public
- ensemble relativement léger
- montage rapide

### Inconvénients
- climatisation et ventilation correcte mais perfectible

## Date de construction
Du 1 octobre 2023 au 15 juillet 2024

## Détails de construction et description technique
- écran : 1,80 m x 1,31 m (format 1,37) 
- dimension hors-tout caisse + chassis : 7473 x 2550 x 3000
- dimension hors-tout caisse : 6600 x 2450 x 2452
- dimension utile intérieur : 6400 x 2250 x 2252
- épaisseur isolation plafond ou mur : 100
- épaisseur isolation sol : 100
- entraxe siège : 450
- largeur traversée : 450

## Photos

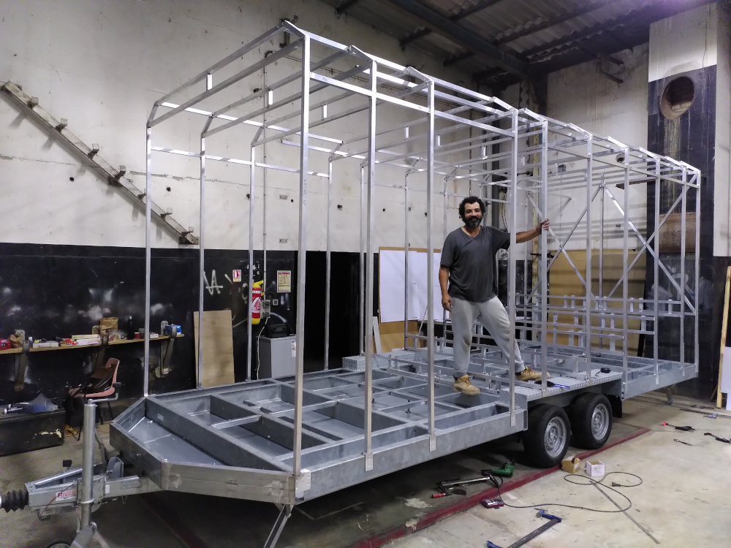
[picture p40: contenu/photos/remorque-structure.jpg]
Photo de la structure de la remorque

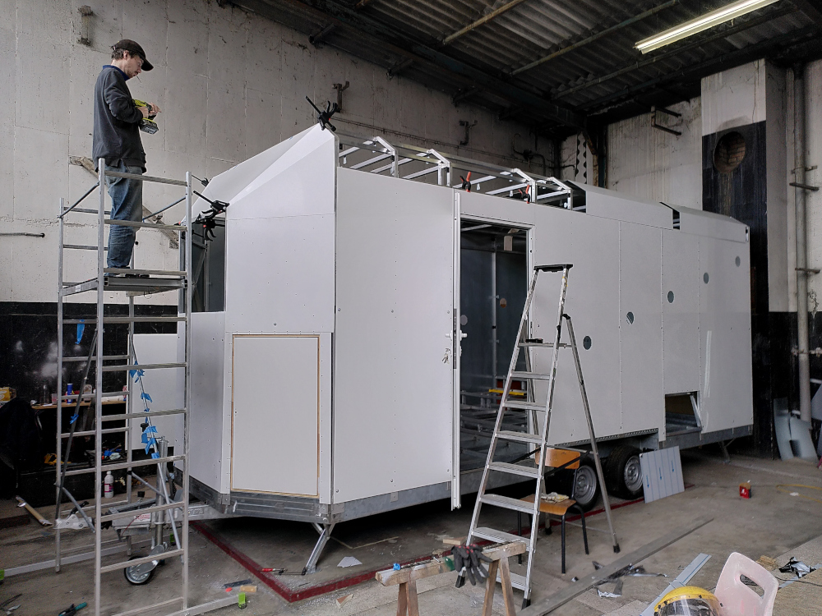
[picture p41: contenu/photos/remorque-chantier-carosserie-1.jpg]
Photo du chantier carosserie

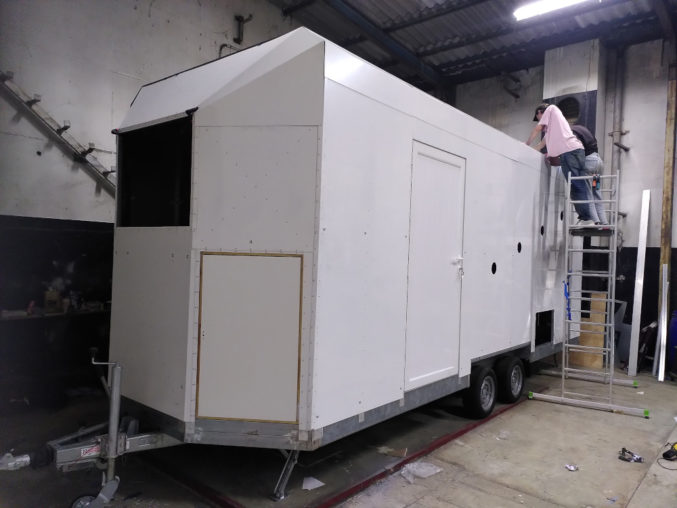
[picture p42: contenu/photos/remorque-chantier-carosserie-2.jpg]
Photo du chantier carosserie

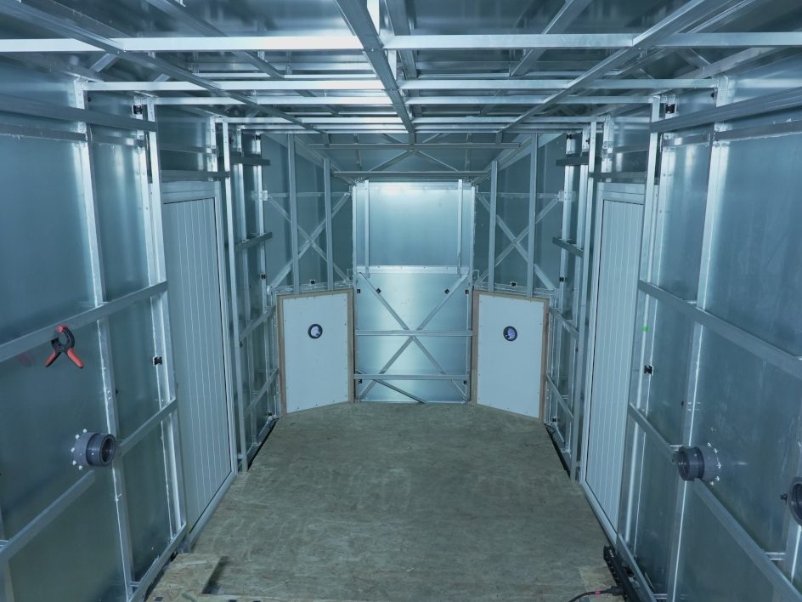
[picture p43: contenu/photos/remorque-chantier-interieur-1.jpg]
Photo de l'intérieur de la remorque en chantier

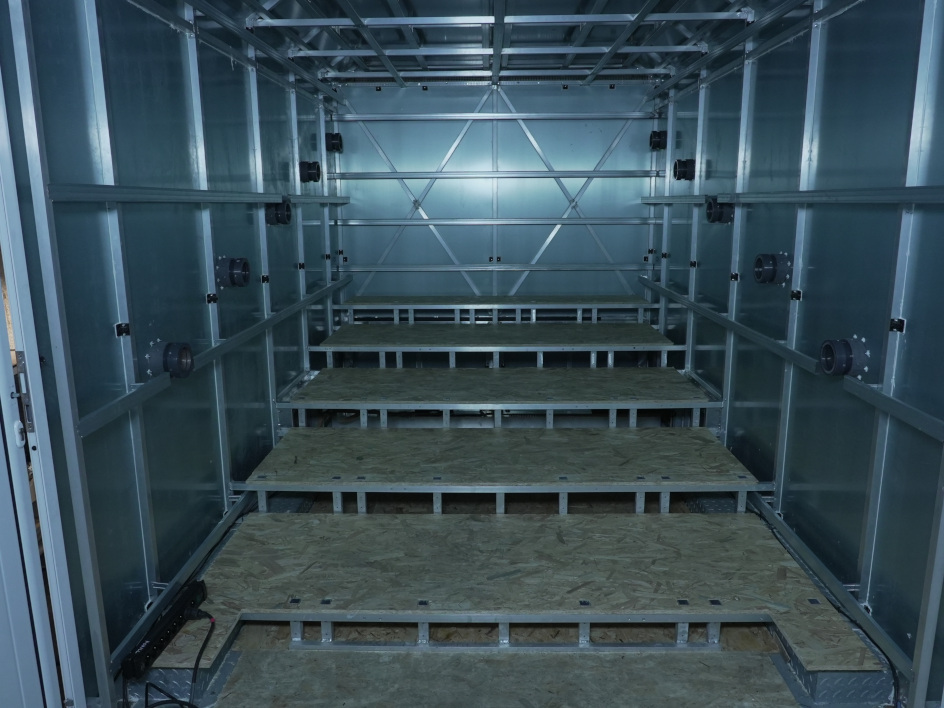
[picture p44: contenu/photos/remorque-chantier-interieur-2.jpg]
Photo de l'intérieur de la remorque en chantier

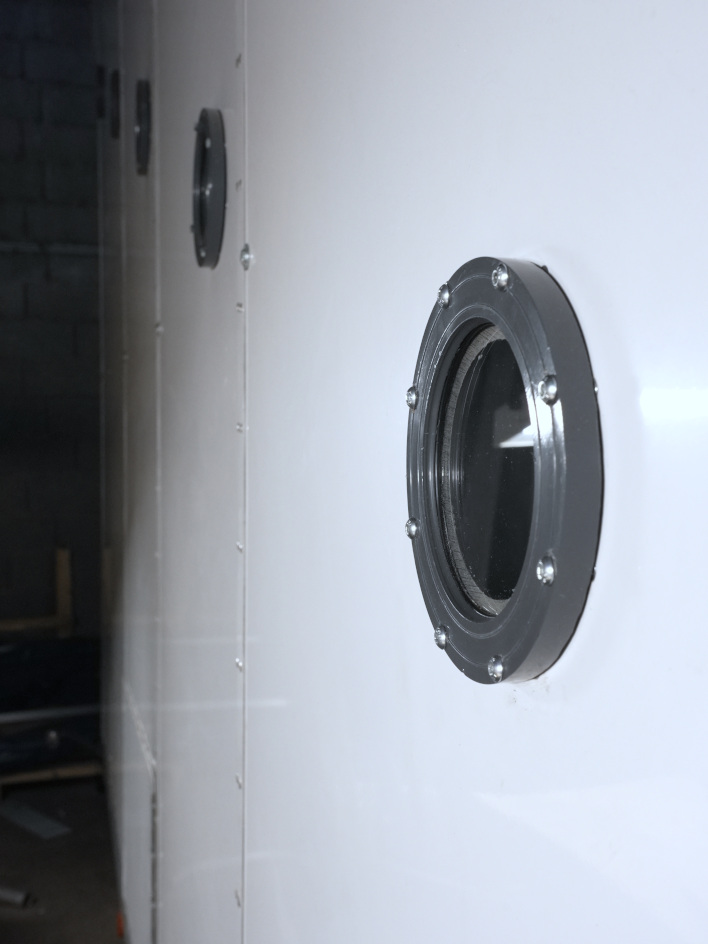
[picture p45: contenu/photos/hublots.jpg]
Photo des hublots

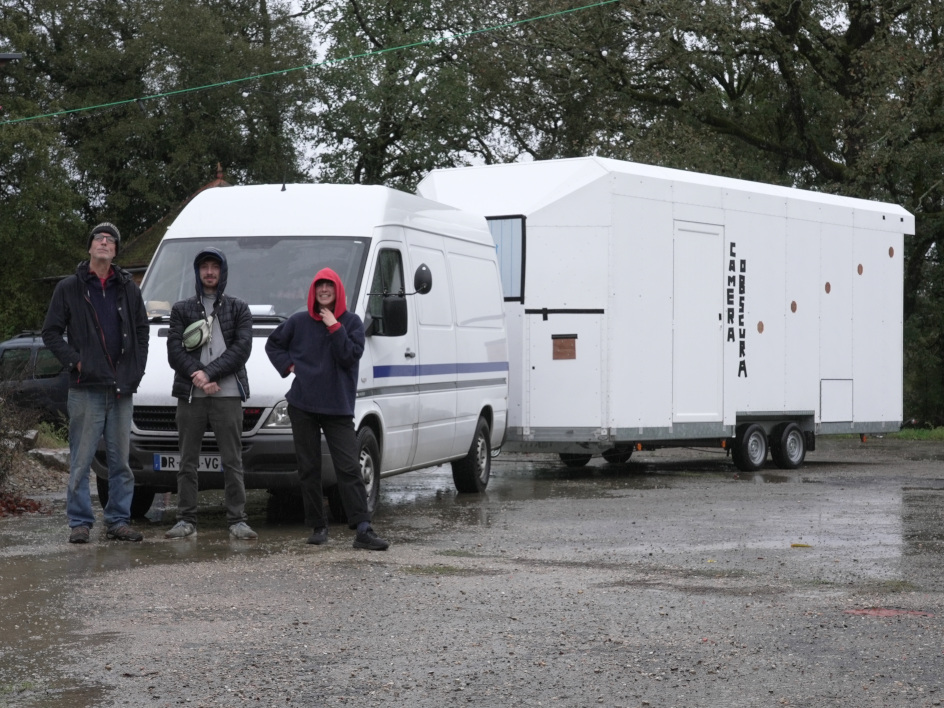
[picture p46: contenu/photos/remorque-assier.jpg]
Photo de la remorque à Assier


## Affichage

Notes sur :

- Disques de vitesse : pas obligatoire pour nous mais on les met quand-même (Voir : [Arrêté](https://www.legifrance.gouv.fr/loda/id/JORFTEXT000000163897))
- Signalisation position angles morts : pas obligatoire pour nous mais on met juste un message texte (Voir : [Arrêté](https://www.legifrance.gouv.fr/codes/article_lc/LEGIARTI000042534807))
- À porpos des plaques voir : [Arrêté](https://www.legifrance.gouv.fr/jorf/id/JORFTEXT000042865682)

## Plans

## Première série de plans

Dessin de la remorque

proto_05

## Deuxième série de plans

[plan chassis remorque](/contenu/plans/doc_bw_tiny_house_ch600.pdf)

plan chassis remorque

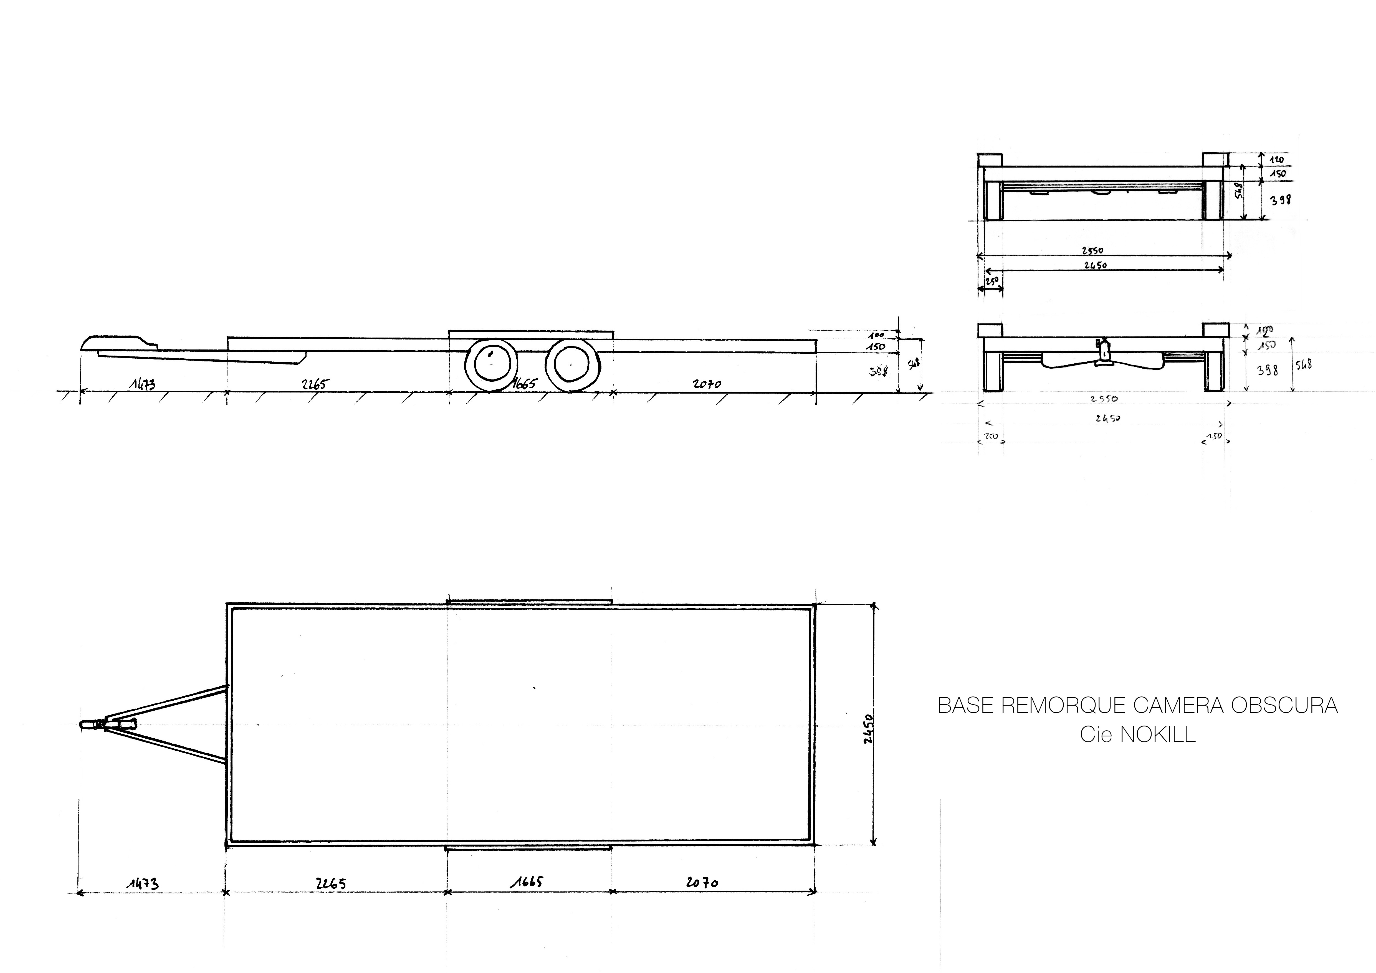
[picture p47: contenu/plans/remorque_base_V02.jpeg]
base remorque


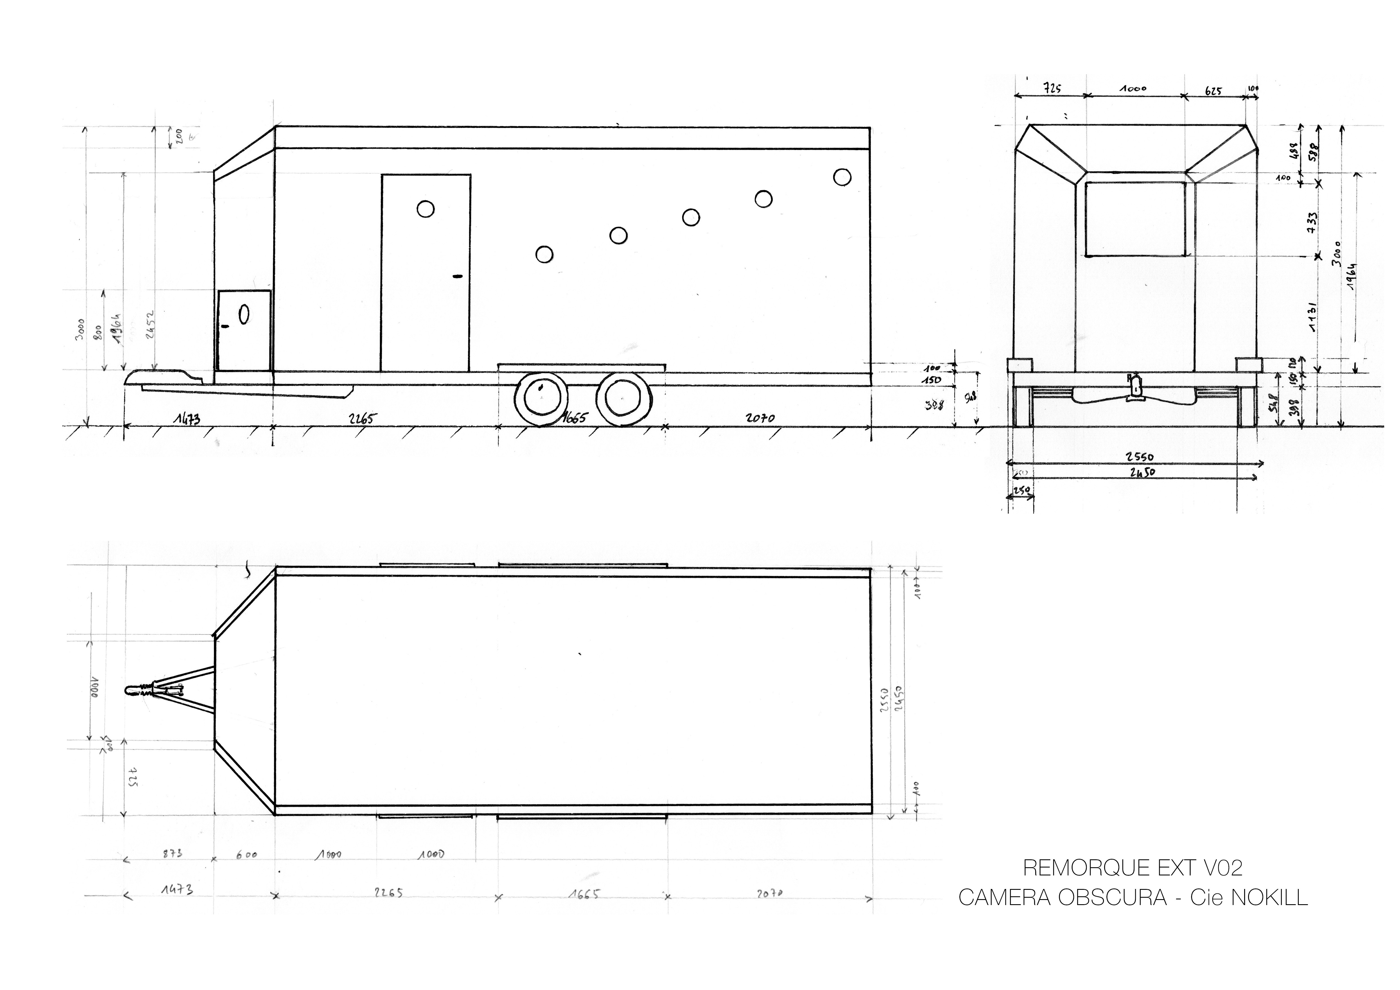
[picture p48: contenu/plans/remorque_ext_V02.jpeg]
extérieur remorque


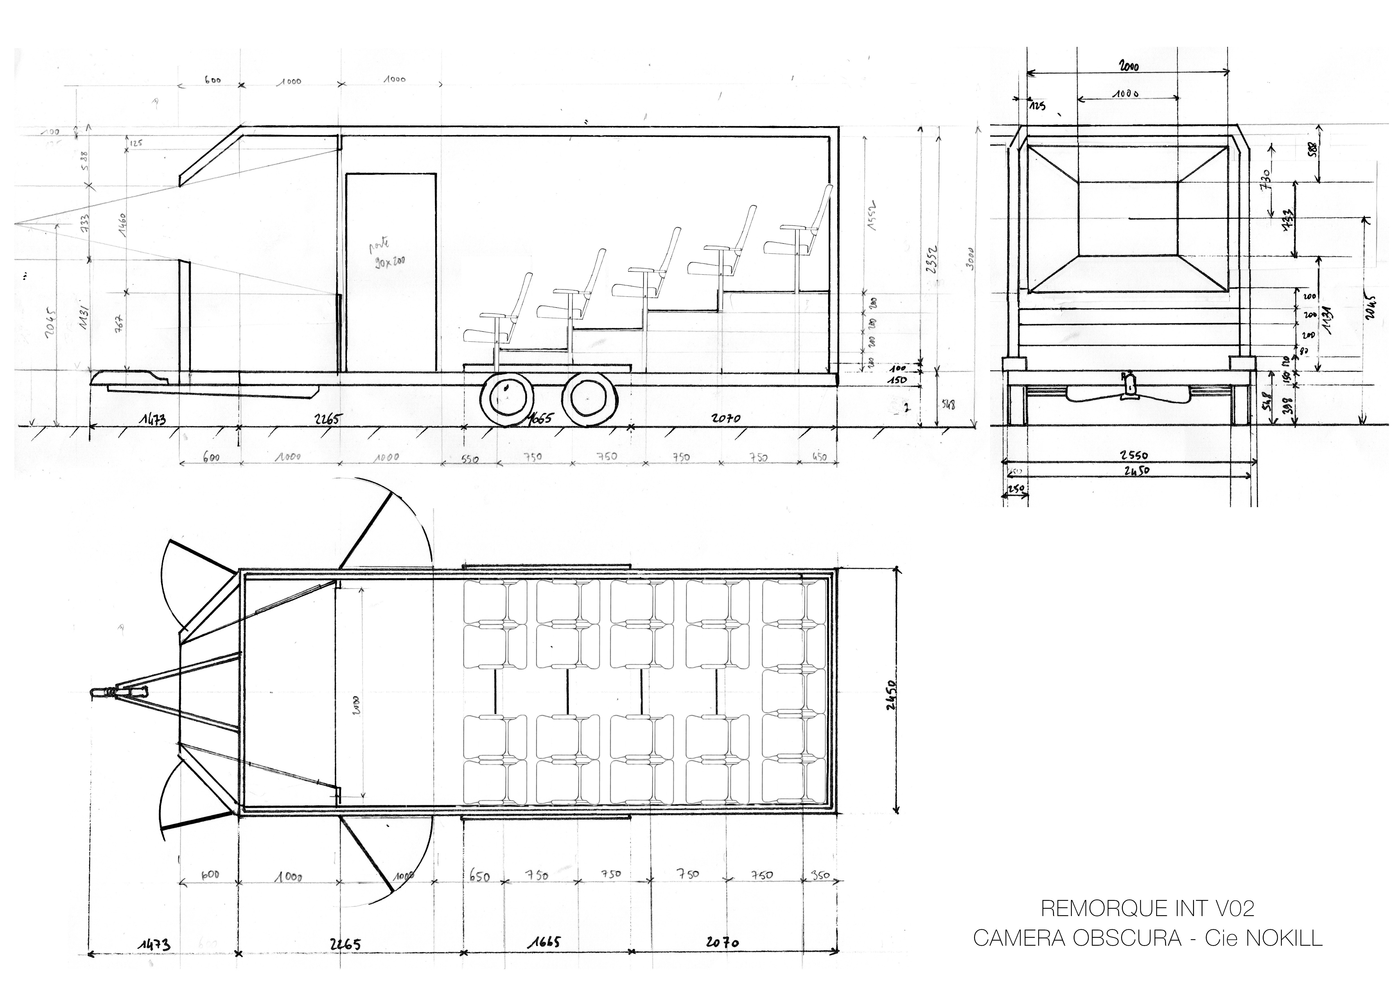
[picture p49: contenu/plans/remorque_int_V02.jpeg]
intérieur remorque


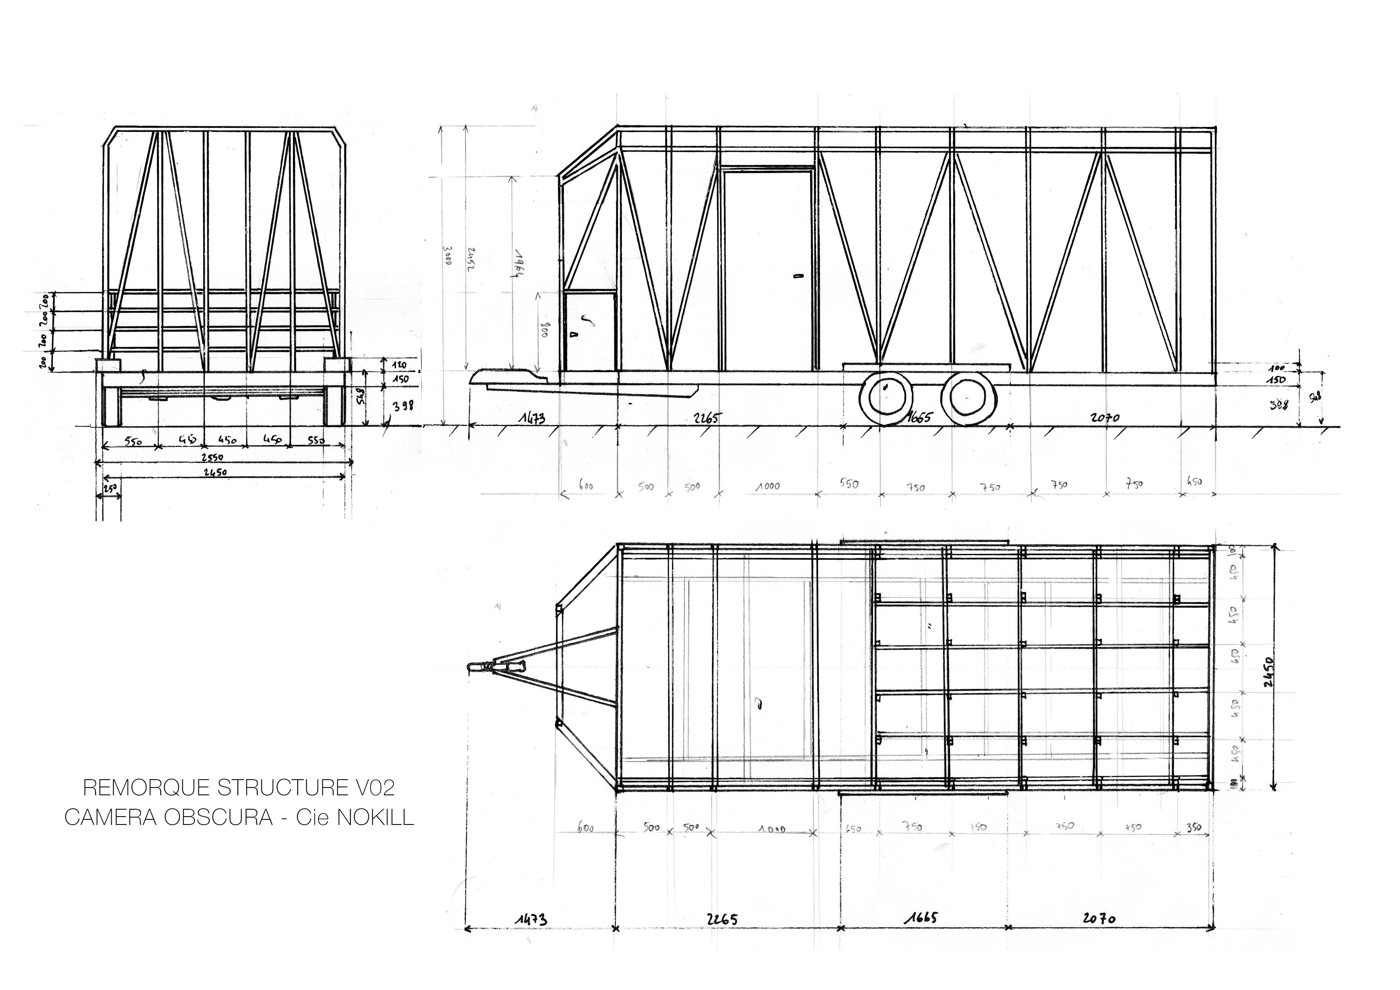
[picture p50: contenu/plans/remorque_structure_V02.jpeg]
structure remorque


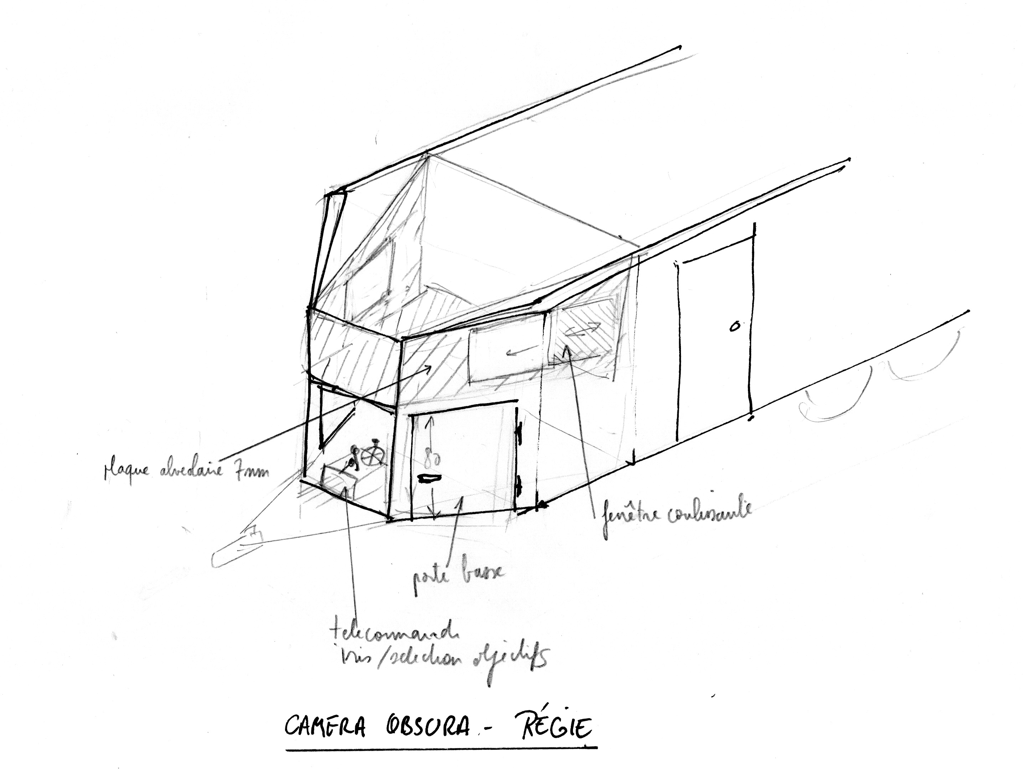
[picture p51: contenu/plans/remorque_regie_V01.jpeg]
régie remorque


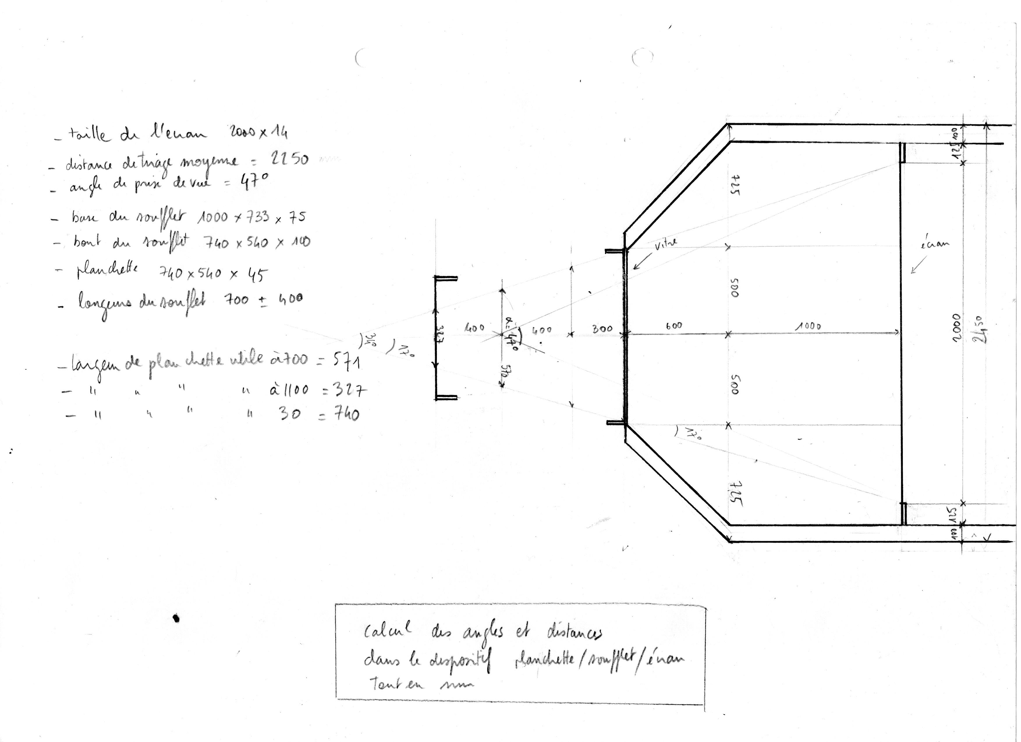
[picture p52: contenu/plans/planchette_largeur_utile_V02.jpeg]
plan jonction remorque et soufflet


## Troisième série de plans

{% include pdf.html url="/contenu/plans/remorque-arches.pdf" %}

{% include pdf.html url="/contenu/plans/remorque-aspect.pdf" %}

{% include pdf.html url="/contenu/plans/remorque-caisses-clim.pdf" %}

{% include pdf.html url="/contenu/plans/remorque-carosserie.pdf" %}

{% include pdf.html url="/contenu/plans/remorque-detail-arches.pdf" %}

{% include pdf.html url="/contenu/plans/remorque-detail-divers-toles.pdf" %}

{% include pdf.html url="/contenu/plans/remorque-detail-plaques-carosserie.pdf" %}

{% include pdf.html url="/contenu/plans/remorque-listes.pdf" %}

{% include pdf.html url="/contenu/plans/remorque-plateau.pdf" %}

{% include pdf.html url="/contenu/plans/remorque-renforts.pdf" %}

{% include pdf.html url="/contenu/plans/remorque-sieges.pdf" %}

{% include pdf.html url="/contenu/plans/remorque-sol.pdf" %}

{% include pdf.html url="/contenu/plans/remorque-structure.pdf" %}

{% include pdf.html url="/contenu/plans/remorque-repartition-pieces-par-plaques.pdf" %}

Voir aussi :
- Tous les plans A1 dans un fichier [plans-remorque-merged.pdf](/contenu/plans/plans-remorque-merged.pdf)
- Le DXF de toutes les pièces qui passent par Schiavon [pieces-toles-schiavon.dxf](/contenu/plans/pieces-toles-schiavon.dxf)
- Le DXF de comment répartir les pièces en tôle laquée coupées par Aquabrasion sur 9 plaques : [pieces-par-plaque-aquabriasion.dxf](/contenu/plans/pieces-par-plaque-aquabriasion.dxf)
- Le plan A3 des pieces en tôle laquées pour Schiavon [remorque-pieces-tole-laquee-schiavon.pdf](contenu/plans/remorque-pieces-tole-laquee-schiavon.pdf)
- Le plan A3 des autres pieces en tôle pour Schiavon [remorque-detail-divers-toles-schiavon.pdf](contenu/plans/remorque-detail-divers-toles-schiavon.pdf)
