LeonLenclos/camera-obscura/contenu/404.md

---
permalink: /404.html
---

## Erreur 404

**Cette page n'existe plus, pas ou pas encore.**

→ [Cliquez ici pour retourner à la page d'accueil](/) ←

ovni
