LeonLenclos/camera-obscura/contenu/objet/rouleau-titre.md

---
type: rouleau-titre
---

### Camera Obscura <small>présente</small>

### <small>Une production</small>Cie NOKILL

# Souvenirs du Futur

## Le jour où<br/>personne ne s'est levé

## Le niveau de l'eau

## Le plein emploi

## La mode

## Une période heureuse<small>les gens étaient heureux<br/>même dans les files d'attente</small>

## Le jour où la Lune<br/>s’est écrasée sur Terre

## Le bon sens

## La mutation

## Les vacances<br/>à Saint-Tropez

## Le podium

## La blague

## Une période malheureuse<small>les gens étaient malheureux<br/>même dans les parcs d'attraction</small>

## Le golden record

## La température idéale

## Le comportement

## La conversation

## L’ultime chanson

#### Un film de

- Bertrand Lenclos
- Léon Lenclos

#### Avec

- Lucile Balézeaux
- Bertrand Lenclos
- Léon Lenclos

<dl>
<dt>Diffusion</dt><dd>Myléna Profit</dd>
</dl>

<dl>
<dt>Soudure</dt><dd>Fabien Durand</dd>
<dt>Construction</dt><dd>Ninon Lenclos</dd>
</dl>

<dl>
<dt>Regard extérieur</dt><dd>Laurent Cabrol<br/>Daisy Domino</dd>
</dl>

<dl>
<dt>Costume</dt><dd>Lucile Balézeaux</dd>
<dt>Musique et design sonore</dt><dd>Bertrand Lenclos</dd>
<dt>Dessin</dt><dd>Léon Lenclos</dd>
<dt>Prothèse-marionnette</dt><dd>Steffie Bayer</dd>
</dl>

<dl>
<dt>Couture</dt><dd>Éva Ricard</dd>
<dt>Vitrerie</dt><dd>Jean-Claude Azemar</dd>
<dt>Menuiserie</dt><dd>Laurent Fayard</dd>
<dt>Habillage carrosserie</dt><dd>Ulysse Lopez</dd>
<dt>Peinture carrosserie</dt><dd>Didier Pons</dd>
<dt>Réflecteur</dt><dd>Marco Cohen</dd>
</dl>

<dl>
<dt>Production</dt><dd>NOKILL</dd>
<dt>Coproduction</dt><dd>MIMA<br/>Le Parvis<br/>Le Quai des Savoirs</dd>
<dt>Accueil en résidence</dt><dd>Le Kiwi / ARTO<br/>Le Périscope<br/>Circa<br/>Les Scènes Croisées de Lozère<br/>L'Association Des Clous</dd>
<dt>Soutien</dt><dd>DRAC Occitanie<br/>DGCA Com. Art de la Rue<br/>Région Occitanie</dd>
</dl>

#### Merci à

- Théo Abadie
- Eric Amblard
- Sylvain Bahos
- Elio Balezeaux
- Ronan Bouvier 
- Joël Boya
- CréaLab de Graulhet
- Claude Canac
- Patricia Canac
- Élise de Couleurs Papilles
- Angèle Dumont
- Amparo Gallur Barbarroja
- Paco Labat
- Florence Laffitte
- Thomas Letellier
- Frédéric Lombardo
- Francis Lopez
- Anna Mano
- Loup-Étienne Margerie
- Juan P. Martínez Pastor
- Théo Petit
- Les Plasticiens Volants
- Marc Reynaud
- Evelyne Salançon
- Virginie Talou
- Gérard Tayeb
- Cie Titanos
- Arnaud Vidal
- Léa Zanotti

<dl>
<dt>Fournisseurs</dt><dd>Aquabrasion<br/>Capus<br/>Ferrières<br/>Schiavon<br/>Vieu</dd>
</dl>

#### Logiciels libres

- Git / GIMP / Inkscape / LibreCAD / Scribus

#### Musique additionnelle

- *Marina*, Georges Briez et son orchestre

#### <small>Ce film vous était présenté par</small>

- *Camera Obscura*

<small>camera-obscura.cienokill.fr</small>
