LeonLenclos/camera-obscura/contenu/dossier/camera-obscura.md

---
type: dossier
pagedjs: false
---



<div class="page-texte" markdown=1>
 
# Camera Obscura

Théâtre optique post-cinéma

Cie NOKILL

Dossier de présentation

</div>

<div class="page-images" markdown=1>

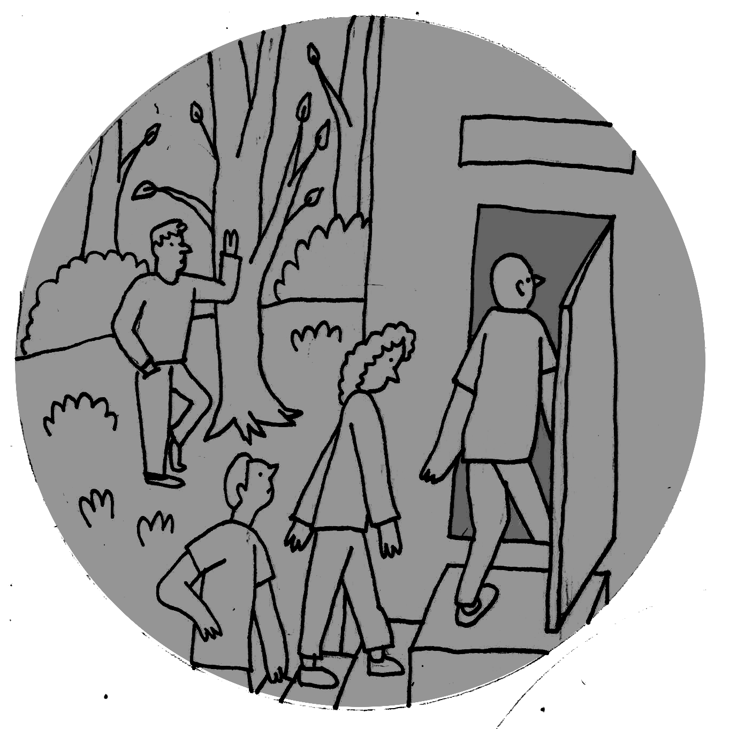
[picture p53: contenu/dessins/macaron_1.png]


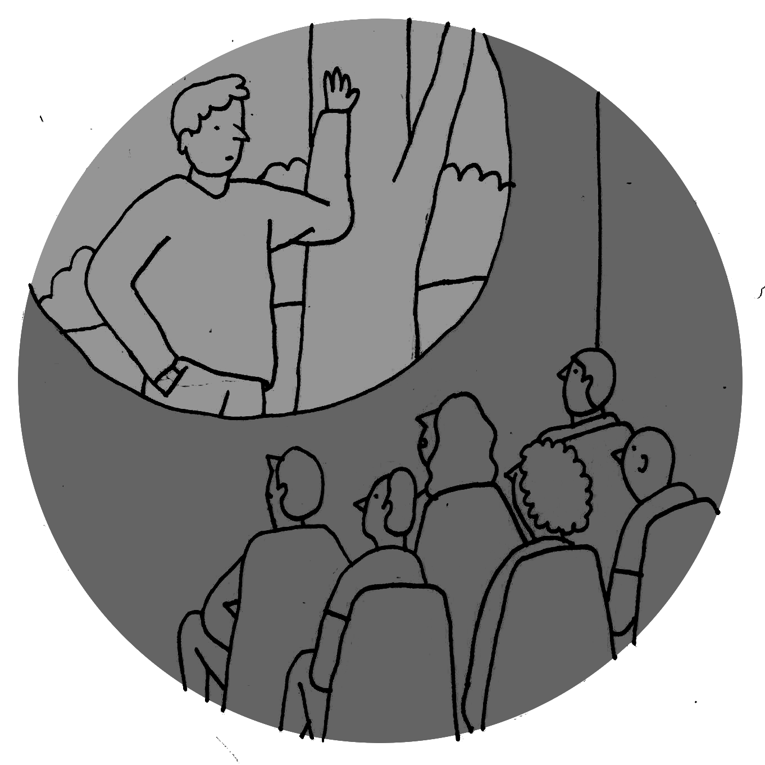
[picture p54: contenu/dessins/macaron_2.png]


</div>

<div class="page-texte" markdown=1>

<blockquote>
 <a href="/contenu/ecriture/intro#intro">Intro</a>
</blockquote>

<small>Texte d'introduction dit par Léon à l'entrée du public dans la Camera Obscura</small>

</div>

<div class="page-images" markdown=1>

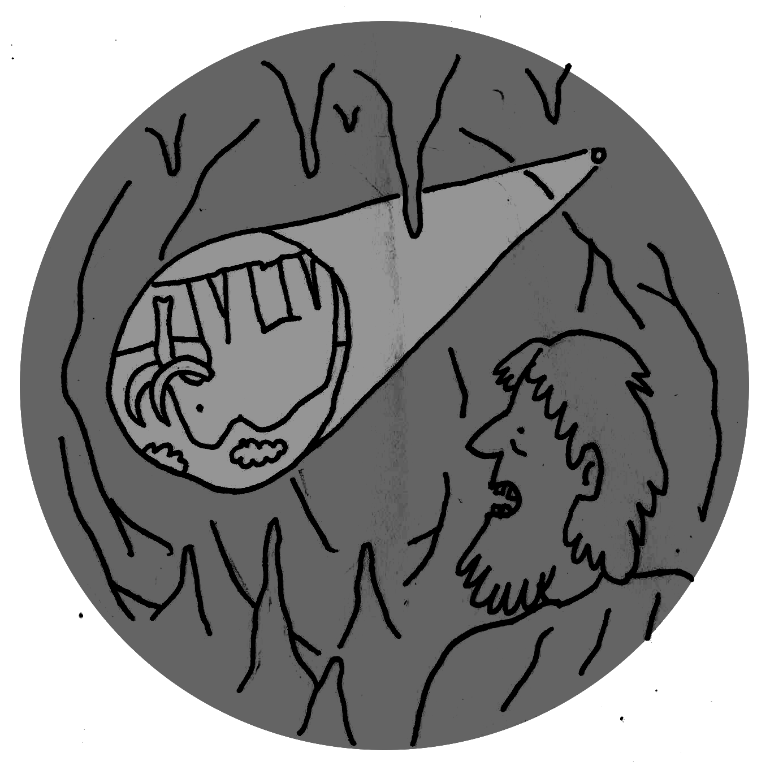
[picture p55: contenu/dessins/macaron_7.png]


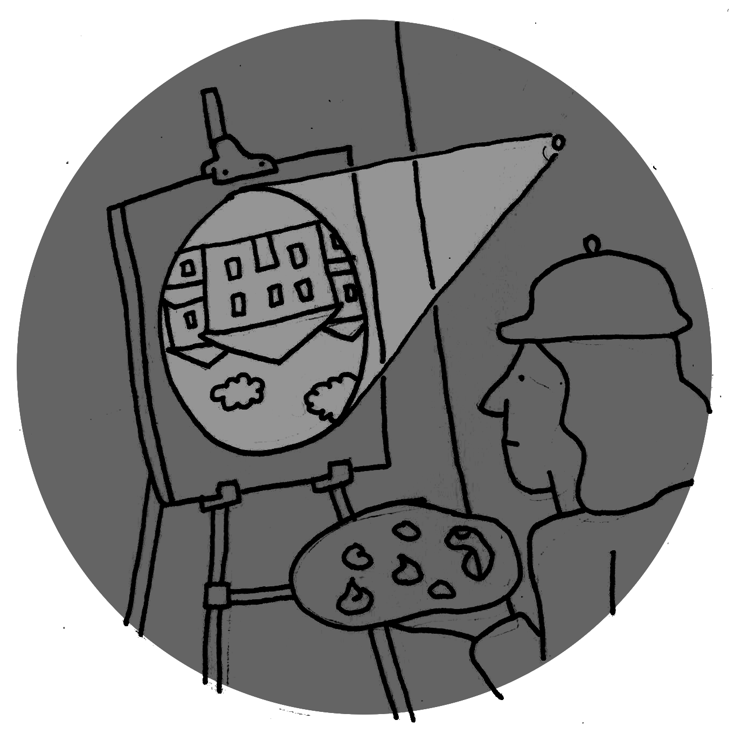
[picture p56: contenu/dessins/macaron_8.png]


</div>

<div class="page-texte" markdown=1>

# Le dispositif

[Dispositif](/#le-dispositif)

# La remorque

[Description de la remorque](/contenu/remorque#description-de-la-remorque)

</div>

<div class="page-images" markdown=1>



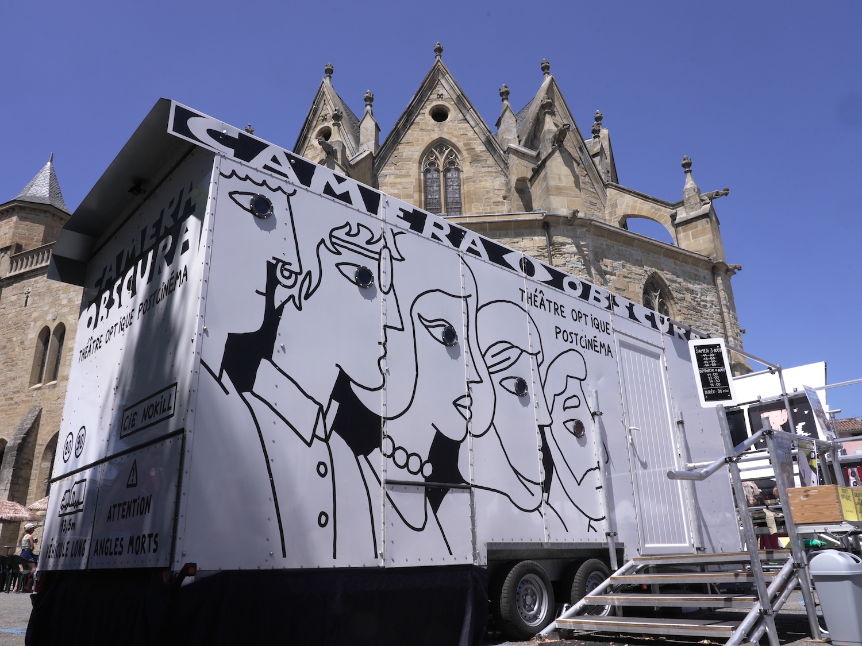
[picture p57: contenu/photos/co-mima-1.JPG]


</div>

<div class="page-texte" markdown=1>

# Souvenirs du futur

[Souvenirs du futur](/#souvenirs-du-futur)

[Construction](/contenu/ecriture/souvenirs-du-futur#construction)

</div>

<div class="page-images" markdown=1>

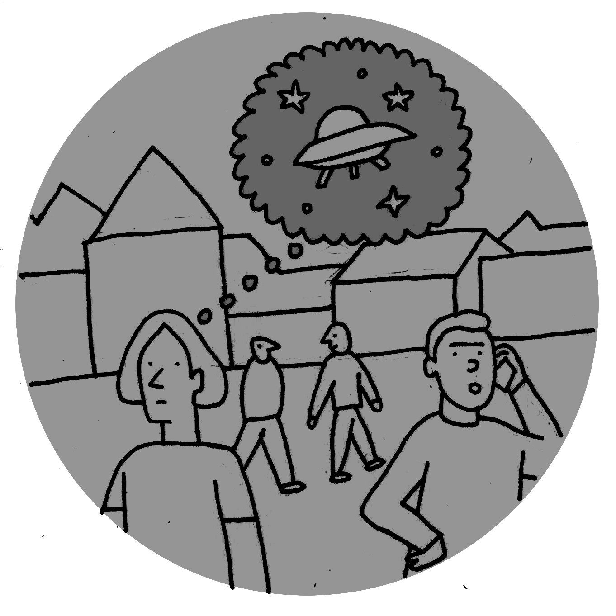
[picture p58: contenu/dessins/macaron_5.png]


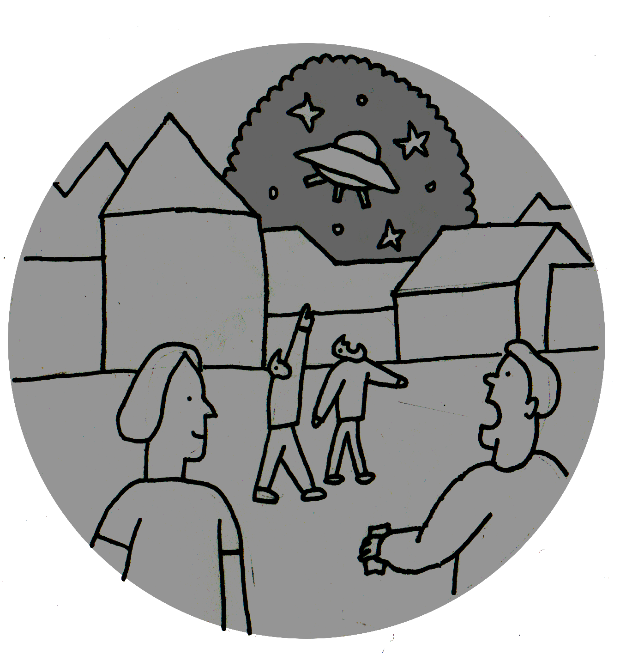
[picture p59: contenu/dessins/macaron_6b.png]


</div>

<div class="page-texte" markdown=1>

<blockquote>
 <a href="/contenu/ecriture/textes-voix-off#1-prologue">Prologue</a>
</blockquote>

<small>Le prologue de Souvenirs du futur</small>

</div>

<div class="page-images" markdown=1>

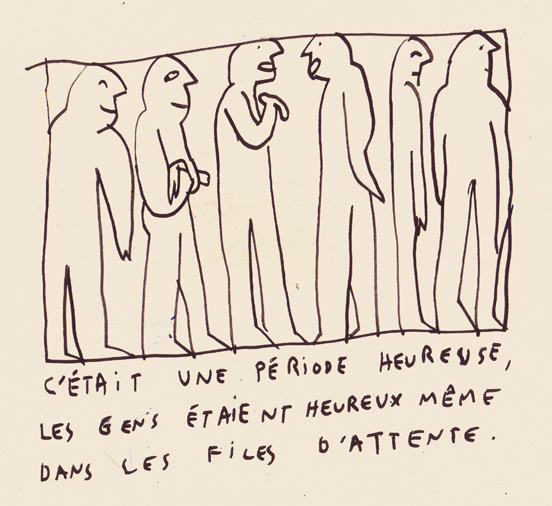
[picture p60: contenu/dessins/files-d-attente.jpg]


</div>

<div class="page-texte" markdown=1>

# Historique de la création

[Historique de la création](/contenu/production.html#historique-de-la-création)

</div>

<div class="page-images" markdown=1>

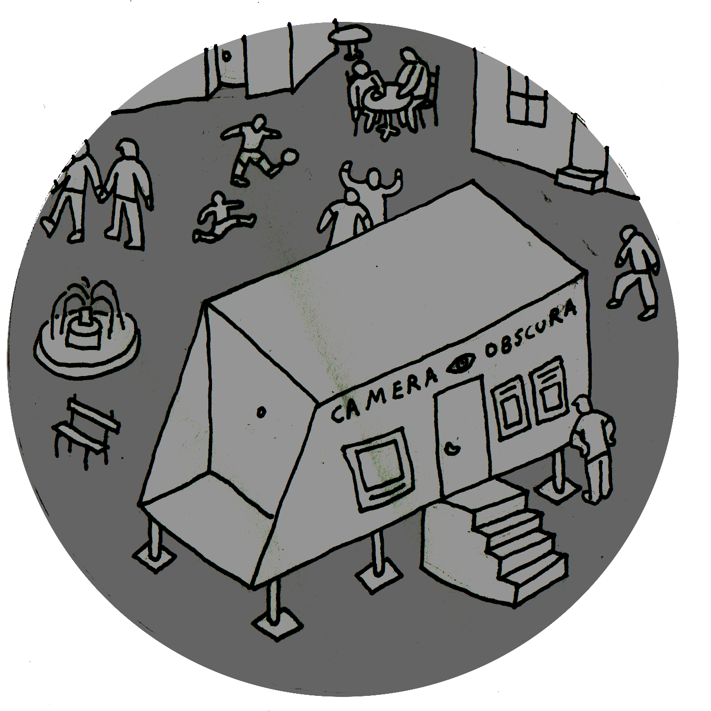
[picture p61: contenu/dessins/macaron_9.png]


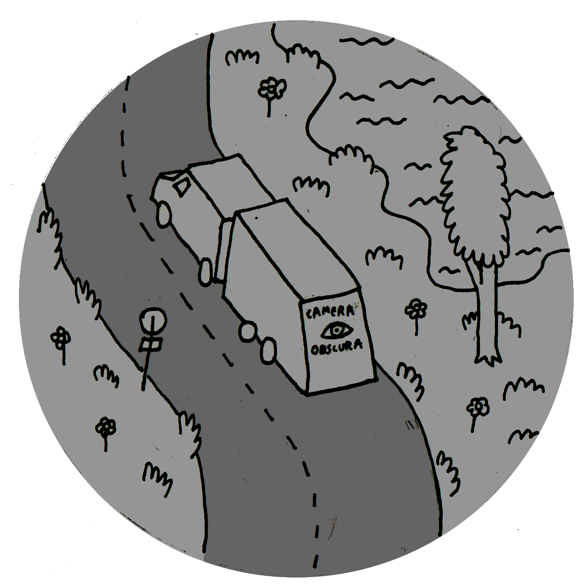
[picture p62: contenu/dessins/macaron_10.png]


</div>

<div class="page-texte" markdown=1>

## Pour plus d'informations

<article markdown=1>

Nous vous invitons à consulter :

- Le site du spectacle : https://camera-obscura.cienokill.fr
- Le site de la compagnie : https://cienokill.fr
- La fiche technique du spectacle :<br/>https://camera-obscura.cienokill.fr/contenu/technique/fiche-technique.pdf

</article>

## Équipe

<article markdown=1>

En tournée, l'équipe artistique et technique est composée de

- Lucile Balézeaux
- Bertrand Lenclos
- Léon Lenclos

</article>

## Contact

<article markdown=1>
 
La diffusion de *Camera Obscura* est assurée par Myléna Profit

- Téléphone : 06 11 99 24 73
- Mail : diff@nokill.fr
  
</article>

</div>

 <script src="/assets/js/aggregate.js"></script>
