LeonLenclos/camera-obscura/contenu/technique/instrumentarium.md

## Instruments de musique et bruitage

- Guitare folk en open tuning Cm avec bottle neck
- Harmonium (standard mini Bhava) modifié pour pouvoir activer le soufflet au pied.
- Lame sonore *Alexis* (Scie musicale)
- Daf
- Sanza
- Spring drum, tambour tonerre (un tom avec un ressort)
- Chapelet de coquillages
- Key Shimes (avec des vrais clés)
- Tube alu accordé en Ré
- Cymbale gong
- Tige filetée sonore (plusieurs rondelles en liberté sur une tige filetée)
- 1 taka-taka grenouille
- Cymbale splash 8" (libre)
- Appeau (à coulisse)
- Grand pavillon de gramophone et tube (pour la voix)
- Papier (journal, livre)
- Bassine et éponge (pour les bruits d'eau)
- talon aiguille (bruitage des pas)
- Ocean Drum (bruitage du ressac)
- Machine à vent
- Machine à pluie

### Baguettes

- Mailloche
- Baquette de batterie (stick)

### à trouver

- Machine à  applaudissement

## Gramophone 

On a retapé un gramophone HMV 102.
On joue dessus des 78 tours. C'est des disques en shellac. Malheureusement on ne sais pas en graver.

Liens au sujet des aiguilles :
- [https://forum.retrotechnique.org/t/aiguille-gramophone/24555]
- [http://collection-frioud.ch/view.php?E=36&P=1879#]

### Disques joués

- *Marina*, Georges Briez ([écouter sur archive.org)[https://archive.org/details/78_marina_georges-briez-et-son-orchestre-georges-briez_gbia0435352a])

### Disques abandonnés

- Sonate Pathétique N°8 op.13, 1e mv. 1e pt., Beethoven
- Sonate Pathétique N°8 op.13, 3e mv. 1e pt., Beethoven (qu'on utilisait juste pour le son craquement du début)
