LeonLenclos/camera-obscura/contenu/legal/consignes-de-securite.md

---
type: legal
---

# Camera Obscura

## Consignes de sécurité

### Plan d'évacuation et d'implantation des moyens d'extinction.

Plan d'évacuation

### Matériel de secours contre l'incendie

L'établissement est équipé d'un extincteur à eau pulvérisée de 6L.

### Modalités d'évacuation

- Le comédien qui fait l’introduction du spectacle à l’intérieur de la remorque indique au public la présence des 2 panneaux directionnels sortie de secours. 
- L’alerte est donnée avec un sifflet et à voix nue par le comédien présent derrière l’écran (responsable sécurité) à l’intérieur de la remorque.
- Une fois que l’alerte est donnée, l’évacuation se fait par deux issues de chaque côté de la structure.
- Le personnel rappelle les consignes d’évacuation et aide le public à évacuer.
- Les premiers rangs (en particulier les personnes à mobilité réduite) sont évacués en priorité.
- Le public et le personnel se rassemble à au moins 7 m de la structure.
- On contrôle qu’il ne reste personne à l’intérieur.
- On attaque le feu sans prendre de risque.
- On alerte les secours si nécessaire (en cas d’incendie : 18 ou 112 ; en cas d’accident : 15 ou 112).

### Rappel des consignes de sécurité

Consignes préventives :
- les issues de secours sont laissées libres ;
- le matériel de secours n’est pas encombré ;
- des exercices contre l’incendie sont menés périodiquement ;

Consignes d’évacuation :
- Garder son calme ;
- ne pas revenir en arrière ;
- utiliser les deux issues si possible ;
- ne pas se précipiter dans les escaliers.
