LeonLenclos/camera-obscura/contenu/technique/accessibilite.md

À propos de l'accessibilité du spectacle *Camera Obscura*.

## Accessibilité auditive

Le son a une place essentielle dans l’appréciation et la compréhension du spectacle, une personne sourde ou malentendante manquera des éléments majeurs pour comprendre le propos.

Le spectacle comporte les sons suivants : musique live,  musiques enregistrées, dialogues, bruitages et voix off.

Pas de son susceptible de gêner des personnes sensibles.

## Accessibilité visuelle

Le visuel a une place essentielle dans l’appréciation et la compréhension du spectacle. Une personne malvoyante ou aveugle manquera des éléments majeurs pour comprendre le propos.

Les types d’images suivantes sont présentes : projection, art visuel, décor et scénographie, textes à lire.

Pas de lumière susceptible de gêner des personnes sensibles.

## Accessibilité physique

Le spectacle est fixe. Les spectateur·ices sont assis·es dans des sièges avec dossier repartis sur un gradin. (Hauteur de marche : 16 cm).

2 places pour fauteuils roulants sont disponibles au 1er rang dans la remorque. En cas d'utilisation de ces places, 2 places normales sont supprimées par fauteuil.

Important : Afin de préparer les places pour fauteuils roulants, nous avons besoin d'être prévenus à l’avance.

L’accès à la remorque se fait par un escalier principal aux normes (Hauteur de marche : 16 cm / Largeur de marche : 1,2m / Main courante). Cet accès peut convenir pour des personnes qui se déplacent avec difficulté.

Une entrée secondaire est équipée d'une rampe amovible à la norme TPMR permettant, avec l'aide d'une personne valide, l'accès aux fauteuil roulant mécaniques ou électriques (pente 25 %).

Important : Prévoir 1 personne pour aider.

## Accessibilité cognitive et contenu du spectacle

Il y a dans le spectacle quelques références culturelles, historiques ou scientifiques qui peuvent enrichir sa compréhension. Cependant, le spectacle peut être vu et apprécié sans ces références.

Il n’y a pas de prise de paroles en langue étrangère. Les thèmes abordés ne sont a priori pas susceptible d'heurter la sensibilité des publics (pas de violence, pas de
sexualité, pas de nudité, pas d'humour noir…)

## Claustrophobie 

Du fait de sa dimension, la remorque dans laquelle les spectateur·ices sont assises peut s'avérer inconfortable pour des personnes sujettes à la claustrophobie.
