LeonLenclos/camera-obscura/contenu/legal/contenu-registre-exploitation.md

---
type: legal
---

# Camera Obscura

## Contenu du registre d'exploitation

Note : la numérotations des parties de ce document est celle de l'annexe 1 de l'arrêté du 4 mai 2023 portant expérimentation d'itinérance des établissements recevant du public.

#### 2.1. Réparation ou remplacement.

##### 2.1.1. Structure (cf. 2° de l'article 40 de l'arrêté du 25 juillet 2022 fixant les règles de sécurité et les dispositions techniques applicables aux structures provisoires et démontables).

Aucune réparation ou remplacement concernant la structure  n'a été effectuée à ce jour.

##### 2.1.2. Aménagements intérieurs.

Aucune réparation ou remplacement concernant les aménagements intérieurs n'a été effectuée à ce jour.

##### 2.1.3. Installations électriques.

Aucune réparation ou remplacement concernant les installations électriques n'a été effectuée à ce jour.

##### 2.1.4. Installations de chauffage et de ventilation.

Aucune réparation ou remplacement concernant les installations de chauffage et de ventilation  n'a été effectuée à ce jour.

##### 2.1.5. Autres installations techniques.

Aucune réparation ou remplacement concernant les autres installations techniques n'a été effectuée à ce jour.

#### 2.2. Vérifications (4) conformément à l'article 2 de l'arrêté du 4 mai 2023 portant expérimentation d'itinérance des établissements recevant du public.

Conformément à cet article et en tant qu'ERP itinérant de catégorie 5, en matière de vérifications techniques nous appliquons l'article PE 4 de l'arrêté du 25 juin 1980 portant approbation des dispositions générales du règlement de sécurité contre les risques d'incendie et de panique dans les ERP.

##### 2.2.1. Structures : rapport d'inspection annuelle de moins de douze mois prévu (cf. 3° de l'article 40 de l'arrêté du 25 juillet 2022 fixant les règles de sécurité et les dispositions techniques applicables aux structures provisoires et démontables).

Veuillez trouver ci-joint le dernier **rapport d'inspection annuelle**.

##### 2.2.2. Aménagements.

Ne s'applique pas, pas d'aménagements à vérifier. 

##### 2.2.3. Installations électriques.

Veuillez trouver ci-joint le **rapport de vérifications des installations électriques**.

##### 2.2.4. Eclairage.

Ne s'applique pas, les spécificité de l'exploitation de cet ERP itinérant font que le public n'est seulement reçu de jours par temps ensoleillé, l'éclairage naturel suffit. 

##### 2.2.5. Chauffage-ventilation.

Ne s'applique pas, pas d'installation de chauffage dans l'établissement. 

##### 2.2.6. Moyens de secours.

Ne s'applique pas en l'absence de locaux de sommeil (voir l'article PE 4 sus-cité).

#### 2.3. Exercices périodiques contre l'incendie.

Veuillez trouver ci-joint l'**historique des exercices contre l'incendie**.

#### 2.4. Incidents importants liés à l'exploitation.

Aucun incident liés à l'exploitation n'est à signaler à ce jour.

#### 2.5. Visites de contrôle.

Aucune visites de contrôle n'a été effectuée à ce jour.

#### 2.6. Visites inopinées.

Aucune visites inopinées n'a été effectuée à ce jour.
