LeonLenclos/camera-obscura/contenu/legal/lettre-prefet.md

---
type: legal
---

**Objet : Demande d'attestation de conformité d'un établissement recevant du public itinérant**

Madame/Monsieur le Préfet,

Conformément à l'article 4 de l'arrêté du 4 mai 2023 portant expérimentation d'itinérance des établissements recevant du public, je vous demande par la présente lettre de bien vouloir nous délivrer l'attestation de conformité de notre établissement recevant du public (ERP) itinérant.

En tant qu'ERP du second groupe ne comportant pas de locaux d'hébergement, l'article précise que la visite de la sous-commission départementale pour la sécurité contre les risques d'incendie et de panique dans les ERP **n'est pas requise**

L'article prévoit que l'attestation de conformité nous soit délivrée après **contrôle de la solidité et de la stabilité à la conception**. En tant qu'ERP itinérant du second groupe, c'est l'**attestation du fabricant** ci-jointe qui vaut contrôle de conception, l'intervention d'un organisme agréé ou accrédité n'est pas requise.

L'Annexe I de l'arrêté du 4 mai 2023 sus-cité fais la liste des informations et des pièces qui permettent d'établir l'Attestation de conformité. Cette liste est reprise dans le document **Contenu de l'attestation de conformité** ci-joint, sont jointes également toutes les les pièces en concernées.

Je vous prie de croire, Madame / Monsieur le Préfet, en l'assurance de mes respectueuses salutations.
