LeonLenclos/camera-obscura/contenu/objet/rouleau-photo.md

---
type: rouleau-photo
---

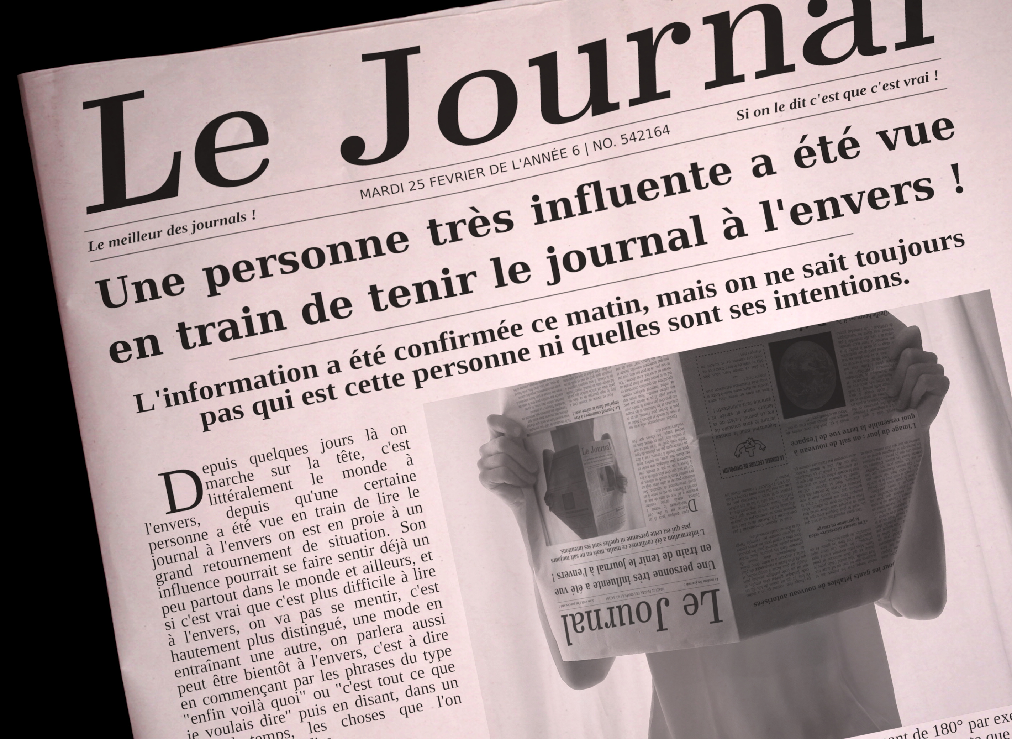
[picture p70: contenu/photos/rouleau-photo/photo-journal.jpg]

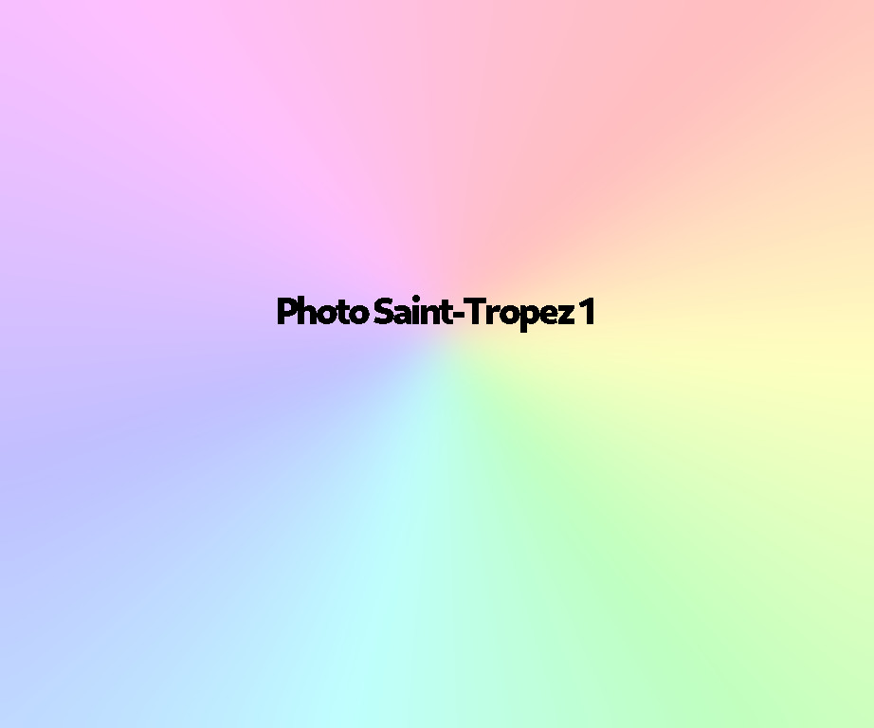
[picture p71: contenu/photos/rouleau-photo/photo-saint-tropez-1.jpg]

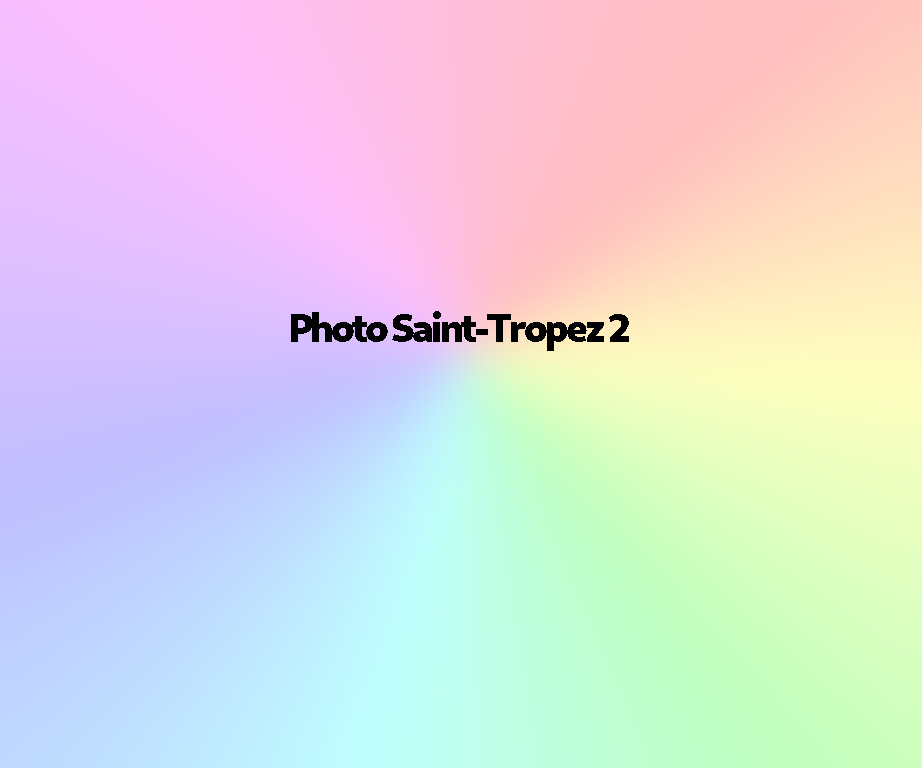
[picture p72: contenu/photos/rouleau-photo/photo-saint-tropez-2.jpg]

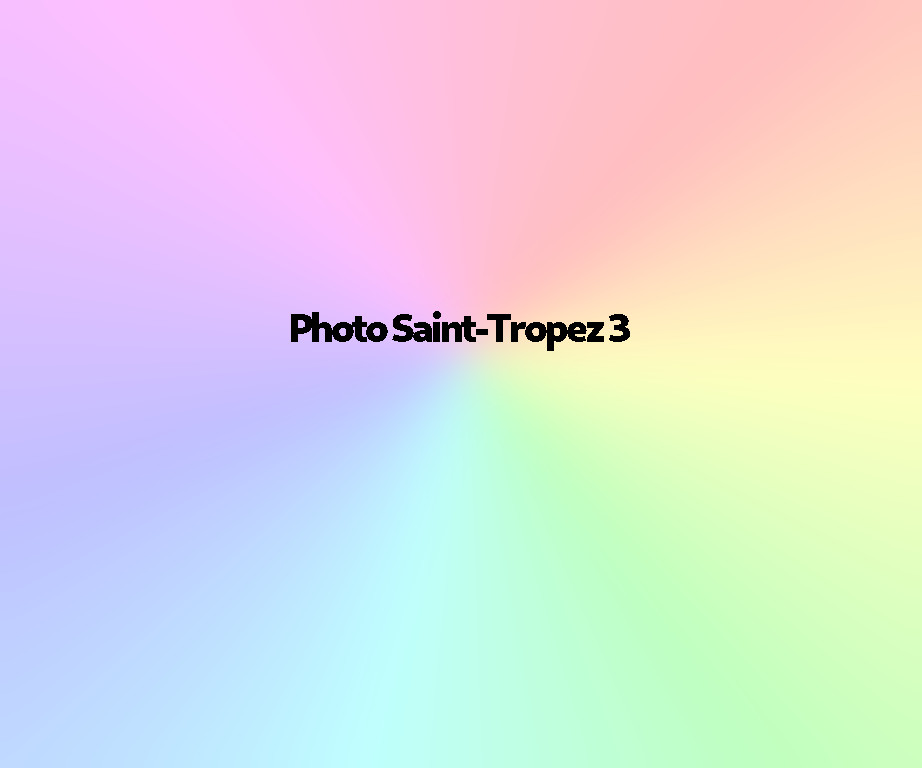
[picture p73: contenu/photos/rouleau-photo/photo-saint-tropez-3.jpg]
