LeonLenclos/camera-obscura/contenu/objet/costumes.md

# Costumes (et maquillage, coiffure)

Les costumes ont au moins deux fonctions :
- clairement differencier tous les personnages joués par les mêmes comédiens.
- véhiculer une certaine vision du futur. (pas cliché s.f. pas trop neutre. Peut-être actuel ou pas (cf. la mode)).

Environ 12 personnages en live et 4 en photo.

## Photos costumes St-Alban

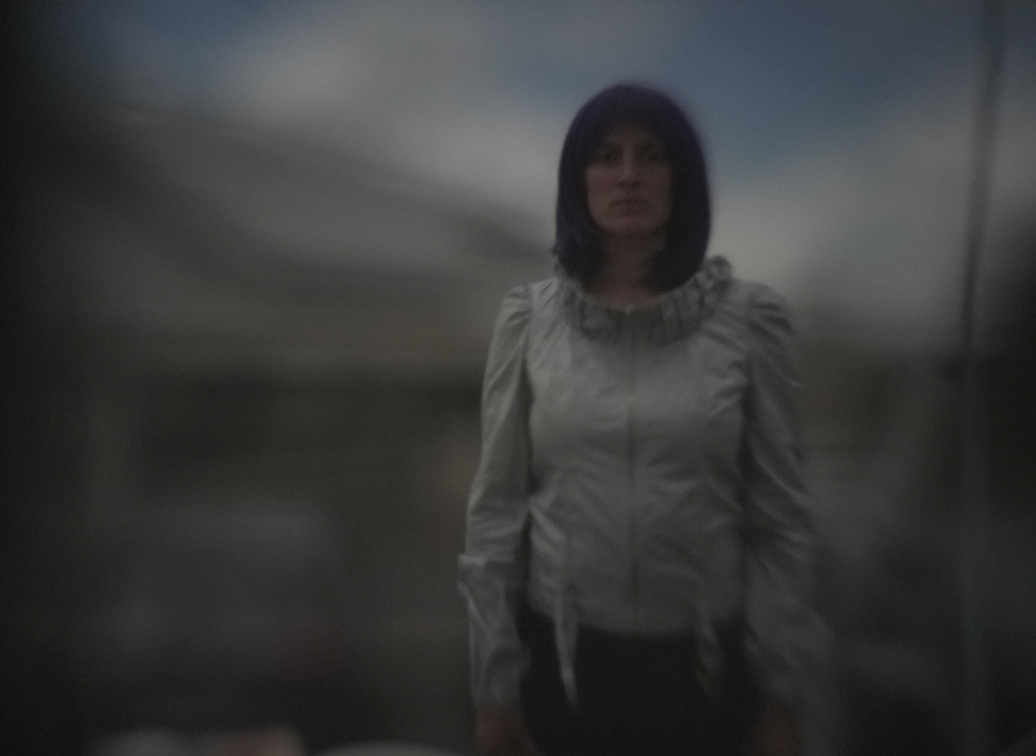
[picture p74: contenu/photos/costume-blague.JPG]
photo costume

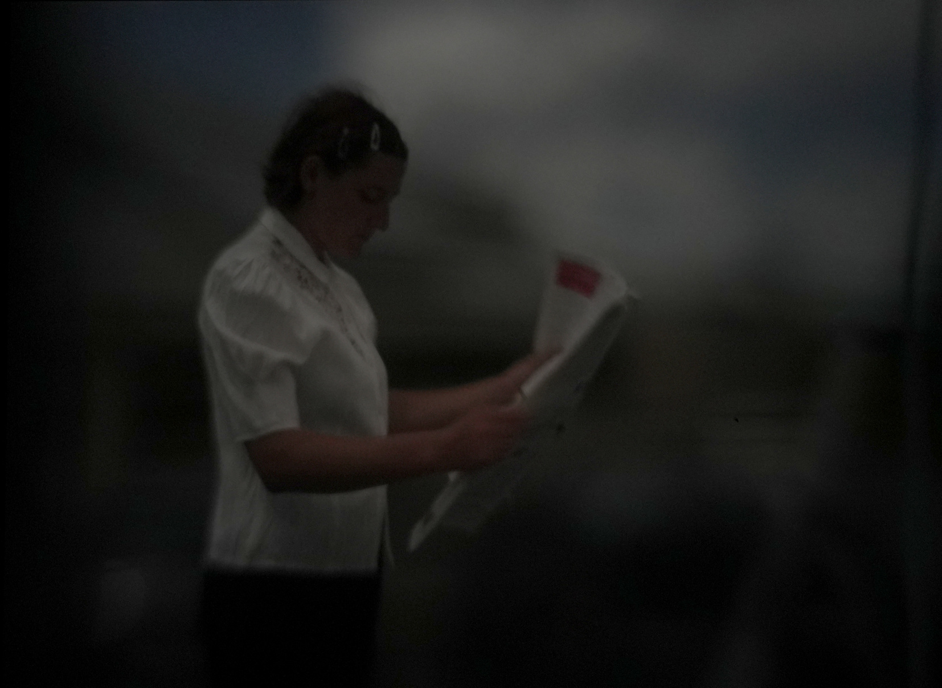
[picture p75: contenu/photos/costume-bon-sens-1.JPG]
photo costume

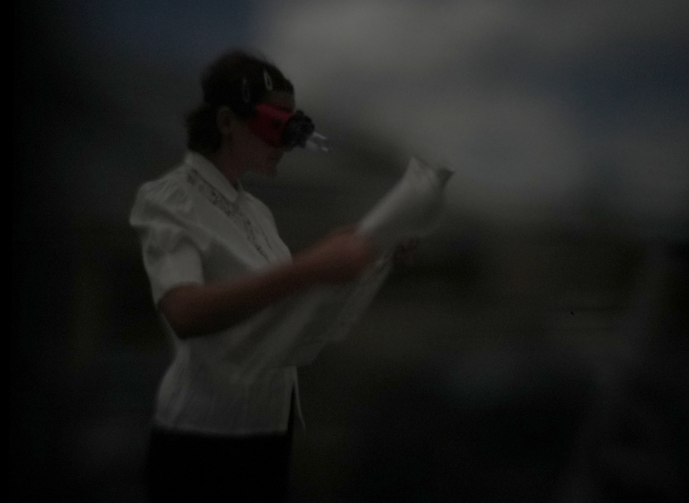
[picture p76: contenu/photos/costume-bon-sens-2.JPG]
photo costume

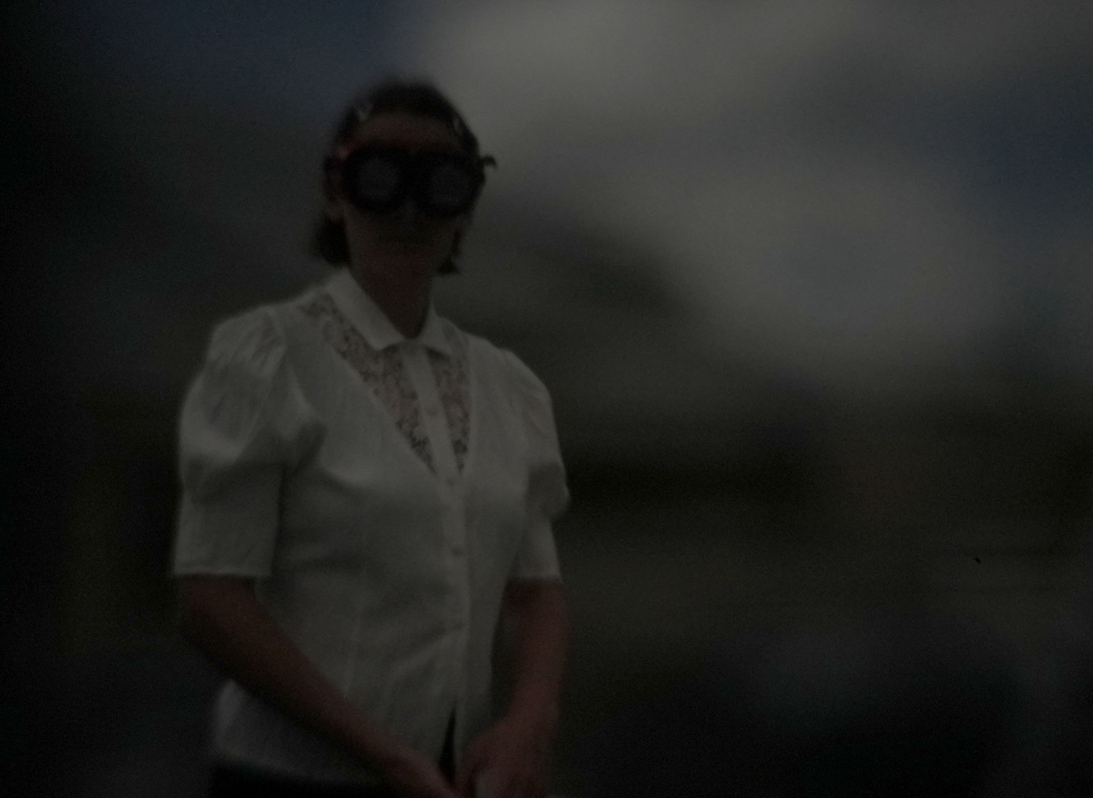
[picture p77: contenu/photos/costume-bon-sens-3.JPG]
photo costume

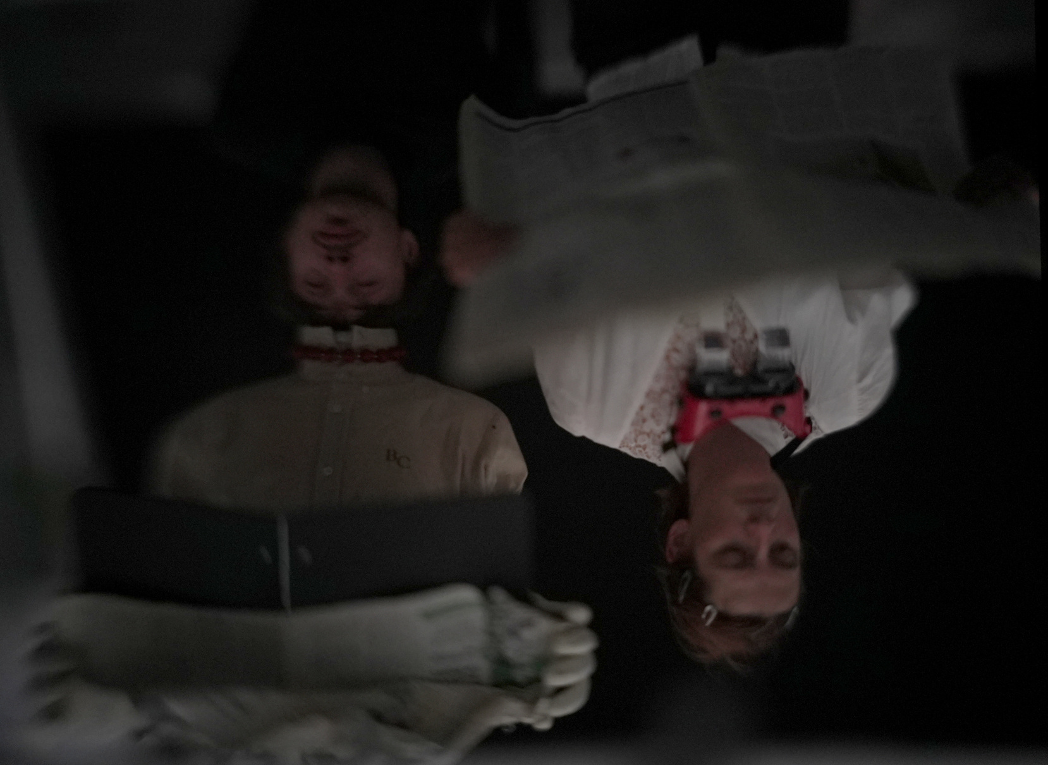
[picture p78: contenu/photos/costume-bon-sens-4.JPG]
photo costume

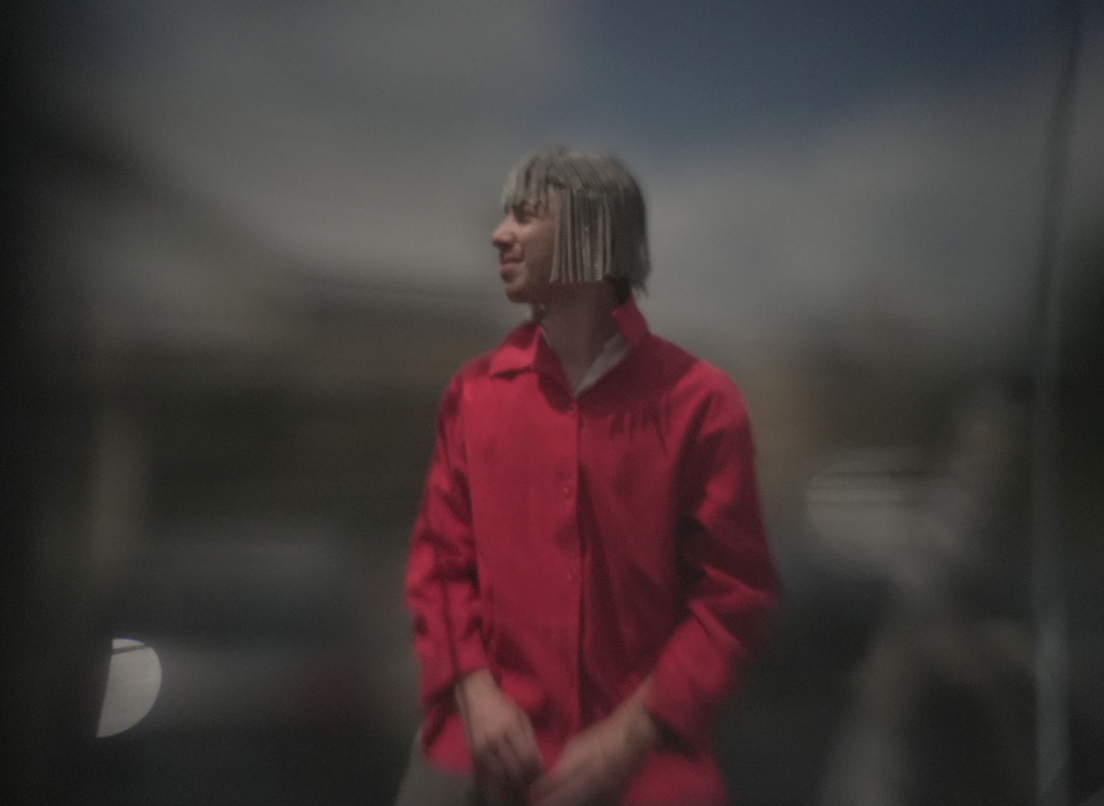
[picture p79: contenu/photos/costume-chanson-1.JPG]
photo costume

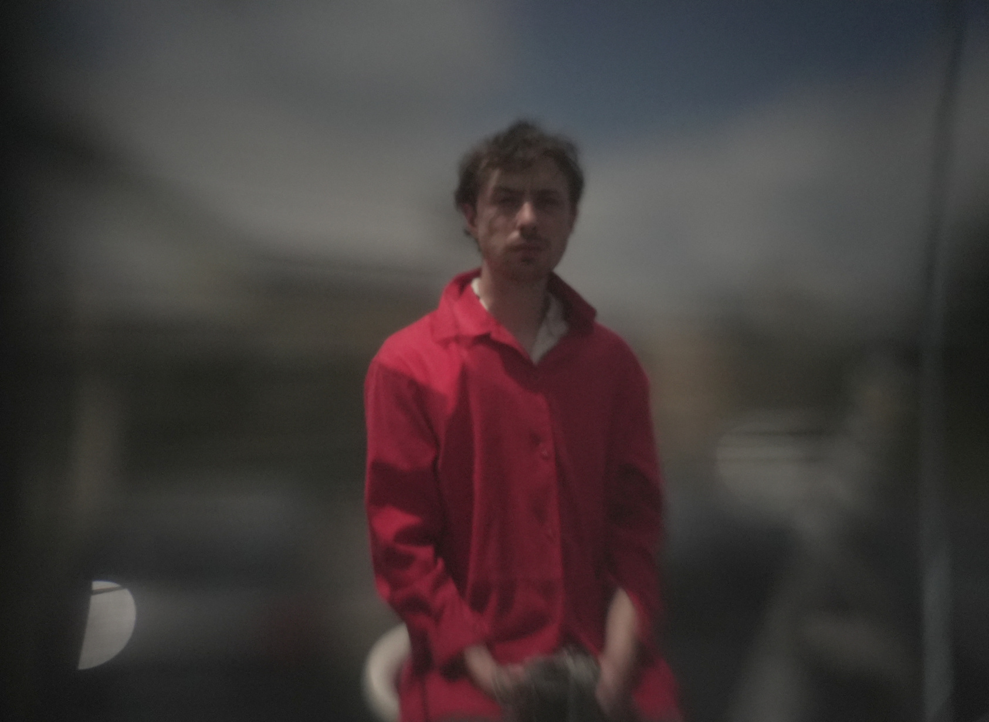
[picture p80: contenu/photos/costume-chanson-2.JPG]
photo costume

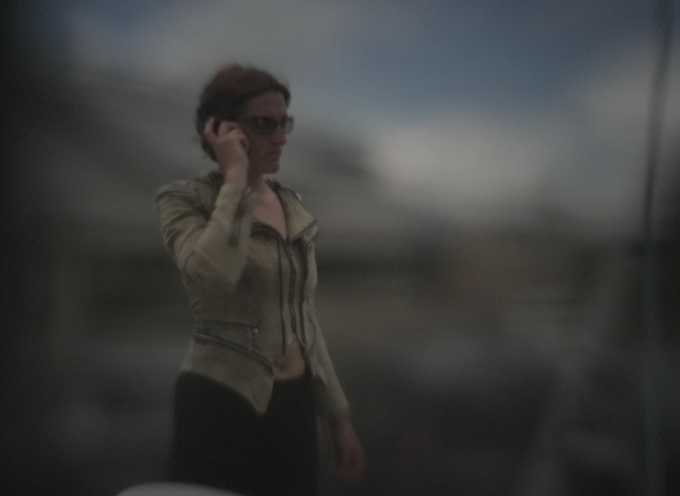
[picture p81: contenu/photos/costume-conversation-1.JPG]
photo costume

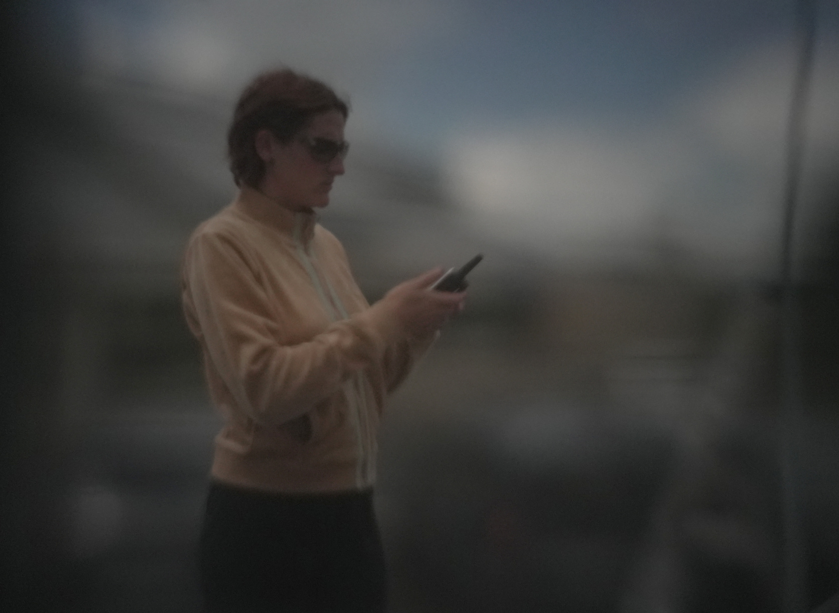
[picture p82: contenu/photos/costume-conversation-2.JPG]
photo costume

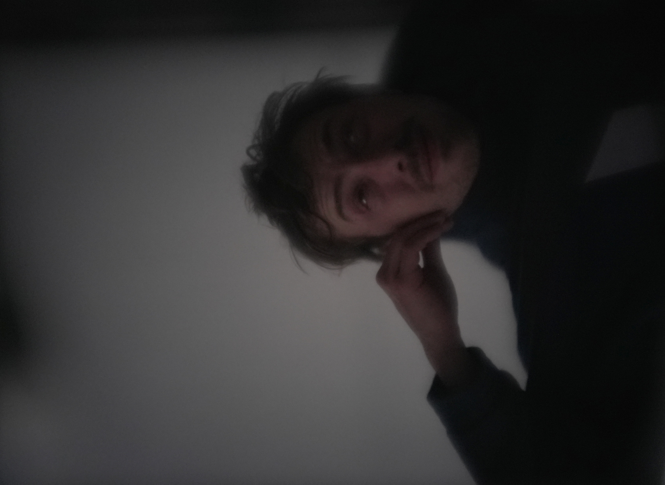
[picture p83: contenu/photos/costume-conversation-3.JPG]
photo costume

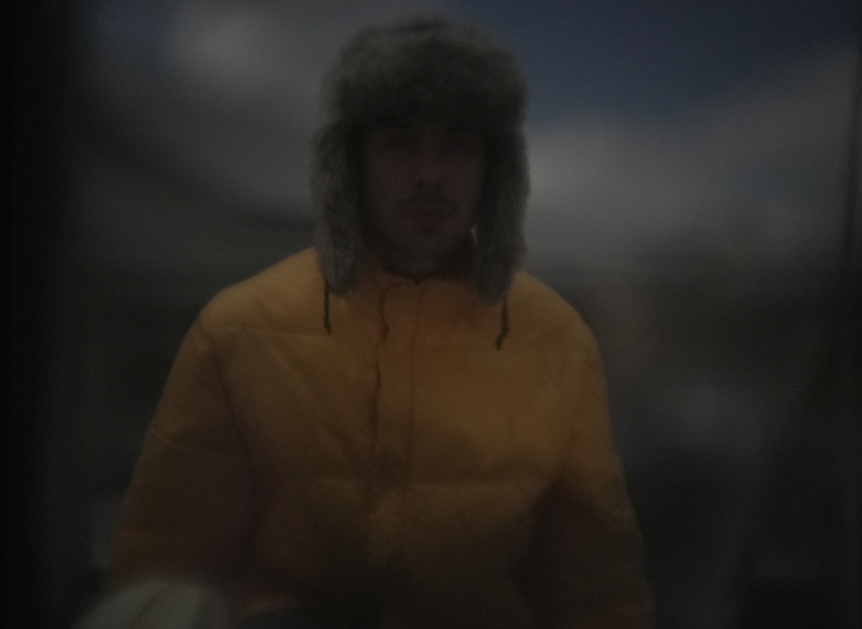
[picture p84: contenu/photos/costume-froid-1.JPG]
photo costume

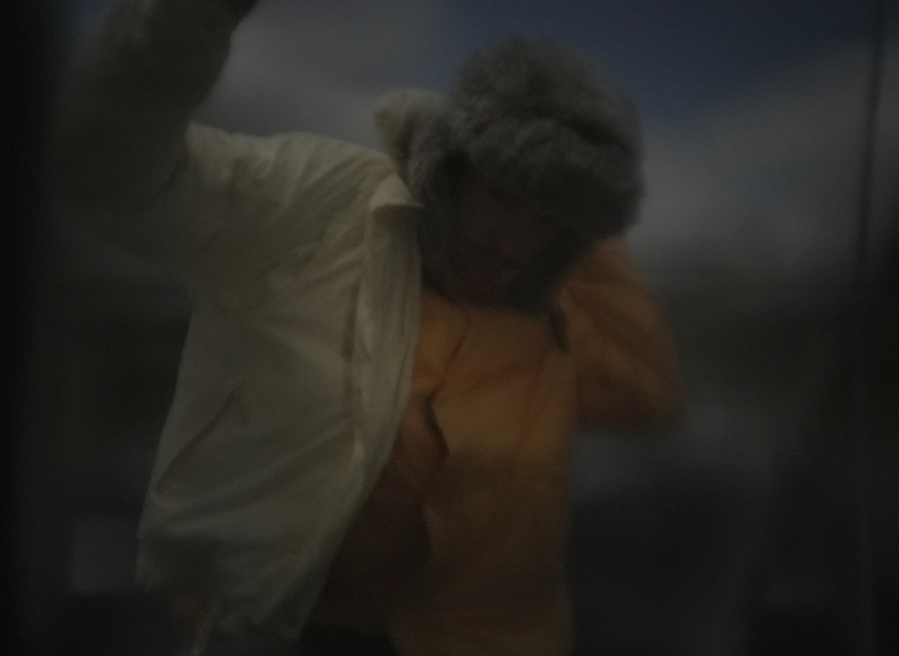
[picture p85: contenu/photos/costume-froid-2.JPG]
photo costume

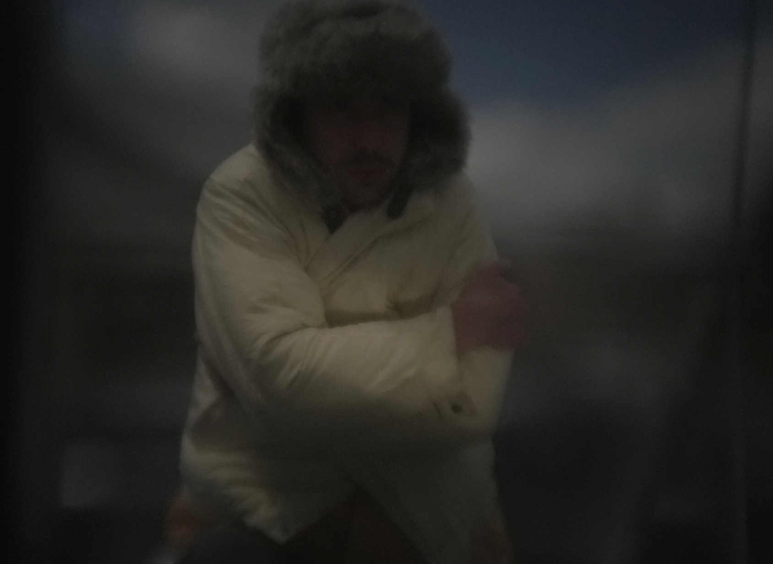
[picture p86: contenu/photos/costume-froid-3.JPG]
photo costume

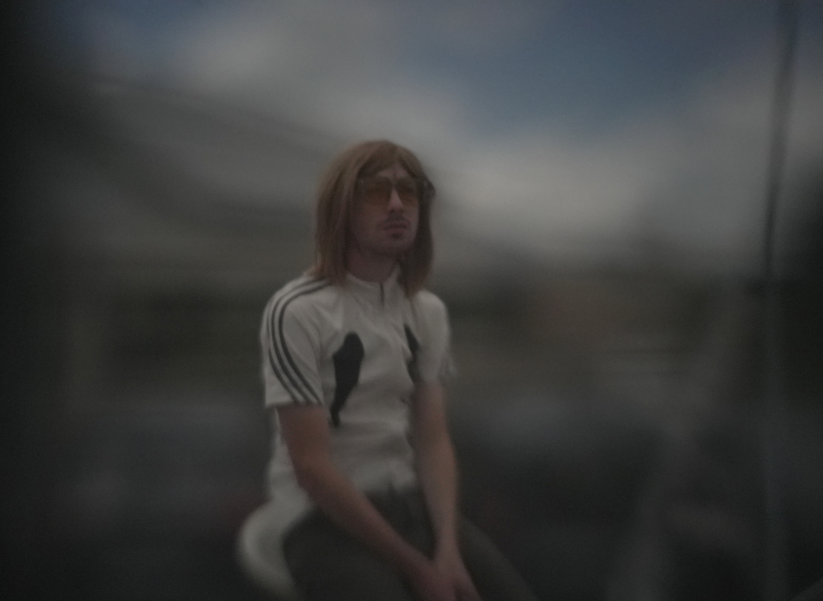
[picture p87: contenu/photos/costume-lune.JPG]
photo costume

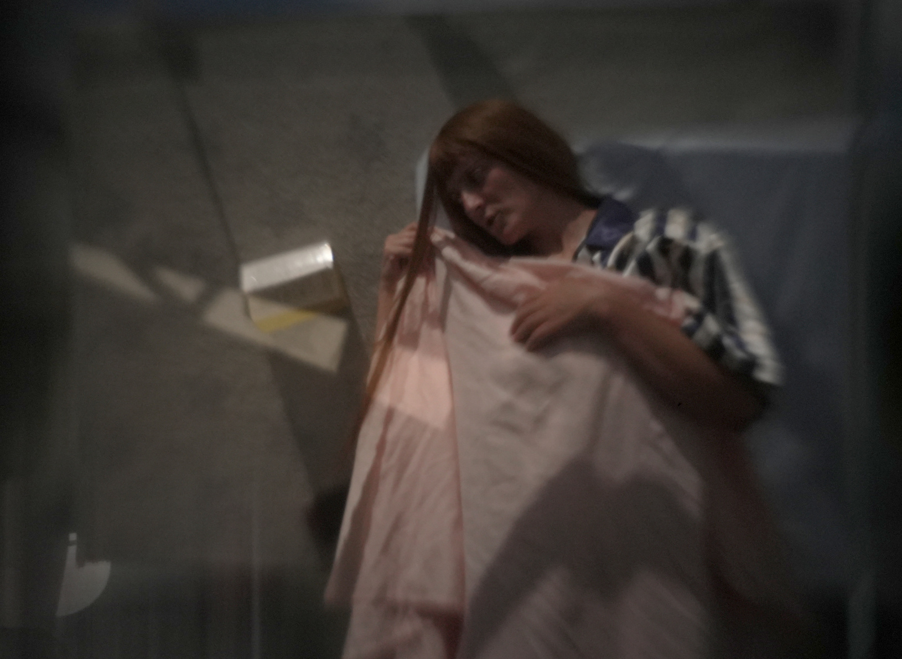
[picture p88: contenu/photos/costume-matin.JPG]
photo costume

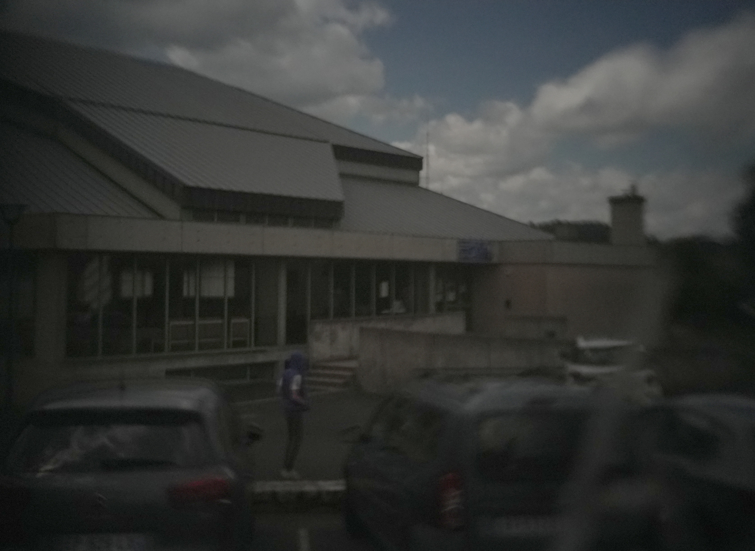
[picture p89: contenu/photos/costume-plein-emploi-1.JPG]
photo costume

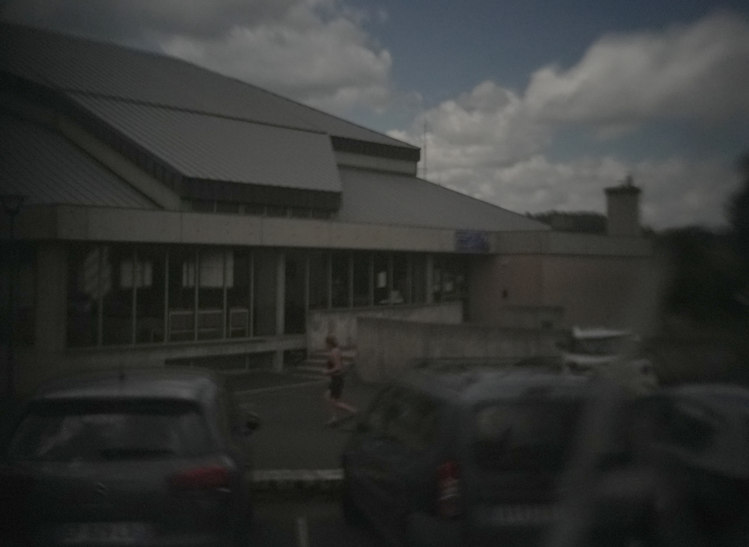
[picture p90: contenu/photos/costume-plein-emploi-2.JPG]
photo costume
