LeonLenclos/camera-obscura/contenu/technique/fauteuils.md

# Les fauteuils

21 fauteuils <del>extrêmement</del> confortables, compacts et légers.

## Structure

La structure est en alu soudé pour la légereté.

Facilement démontable et hauteur facilement réglable (Deux pieds qui se manchonnent au sol dans la structure de la remorque).

## Dossier et assise

Le dossier et l'assise sont démontables et sont composés de :
- 1 système de fixation (démontable sans outil pour l'assise et avec des vis pour le dossier)
- 1 planche de contre-plaqué ep. 5mm
- Un bloc de mousse CMHR prédécoupée
- Une housse housse en tissus amovible.

## La question des acoudoirs

On avait évoqué mettre des accoudoirs amovibles qui pouvaient se rabattre le long du dossier. Ça aurait été classe mais ça aurait rendu la place très étroite, après éssai, on s'est dit que la majorité des personnes préféreraient les rabattre et que du coup c'était peut-être pas la peine de les mettre.

## La question du tissu

Cuir trop cher, skaï pas confortable (collant sous la sueur), donc on voulait partir sur du tissus (couleur : bordeaux) de ce type :

* [Tissu velours Alisa](https://www.mondialtissus.fr/tissu-velours-alisa-bordeaux-230308.html)
* [Alcantara Bordeaux](https://www.de-tissus-en-couture.com/boutique/alcantara/tissu-imitation-daim-bordeaux.html)

Mais comme on avait un gros stock de Kalmut noir (commandé à l'origine pour le revêtement des murs interieurs de la remorque), on s'est dit qu'on allait plutôt utiliser ça.

## Dimensions

* entraxe siège : 450
* assise : 450
* hauteur dossier : 700
* largeur traversée : 450
* épaisseur de l'assise (mousse) : 50
* épaisseur du dossier (mousse) : 30

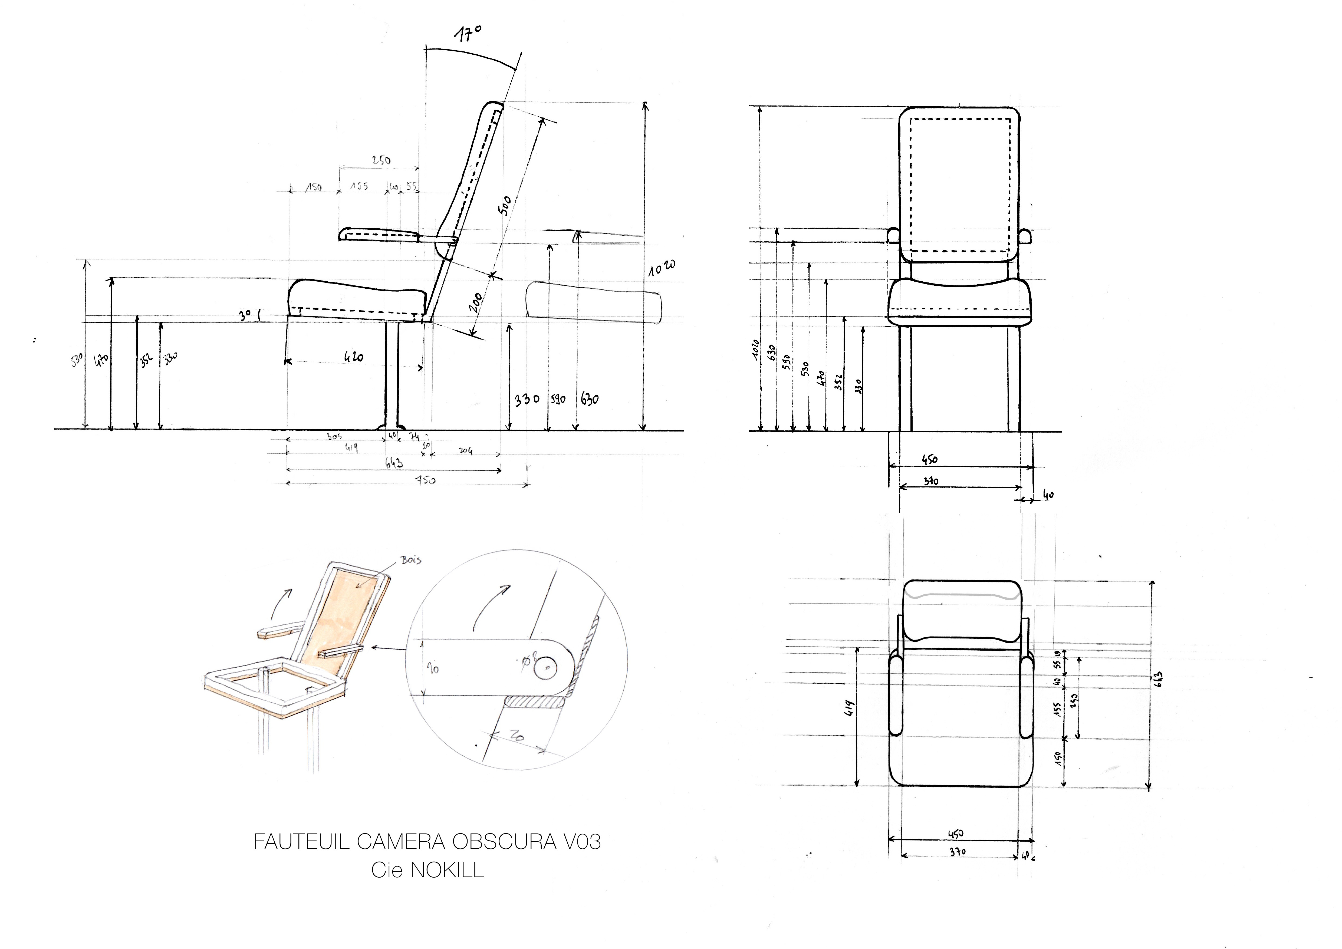
[picture p91: contenu/plans/fauteuil_V04.jpeg]
fauteuil V04


## Siéges amovibles

Au bord des marches on a 4 poufs qui sont fait tout pareil que les assises des fauteuils.

## Fabrication

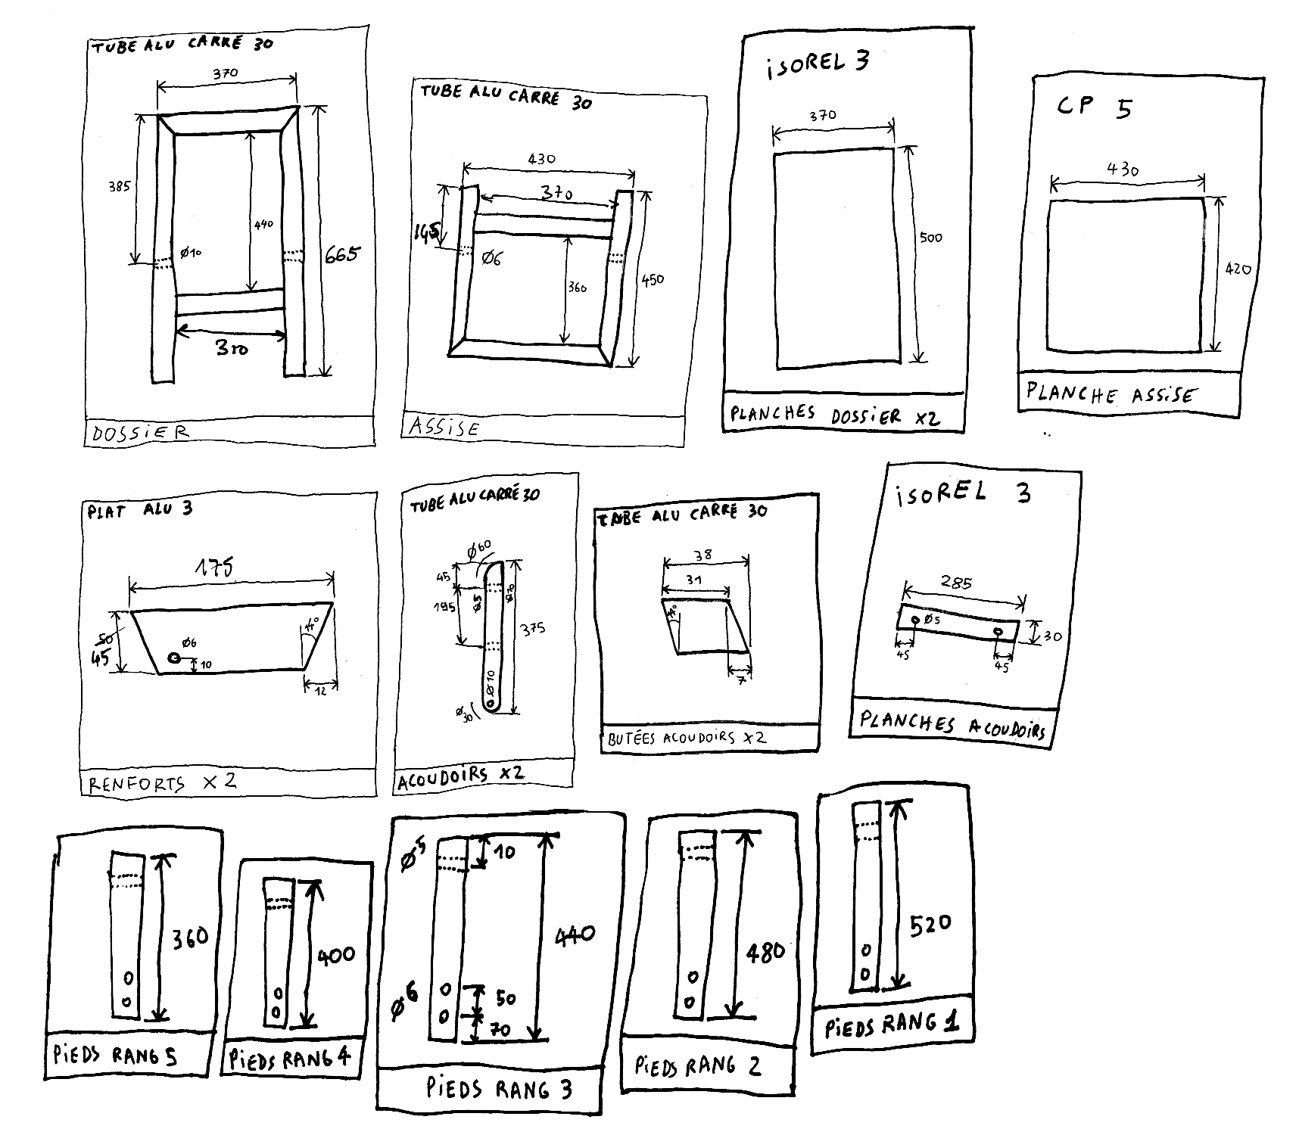
[picture p92: contenu/plans/fauteuil-structure.png]
fauteuil


## Implantation dans la remorque

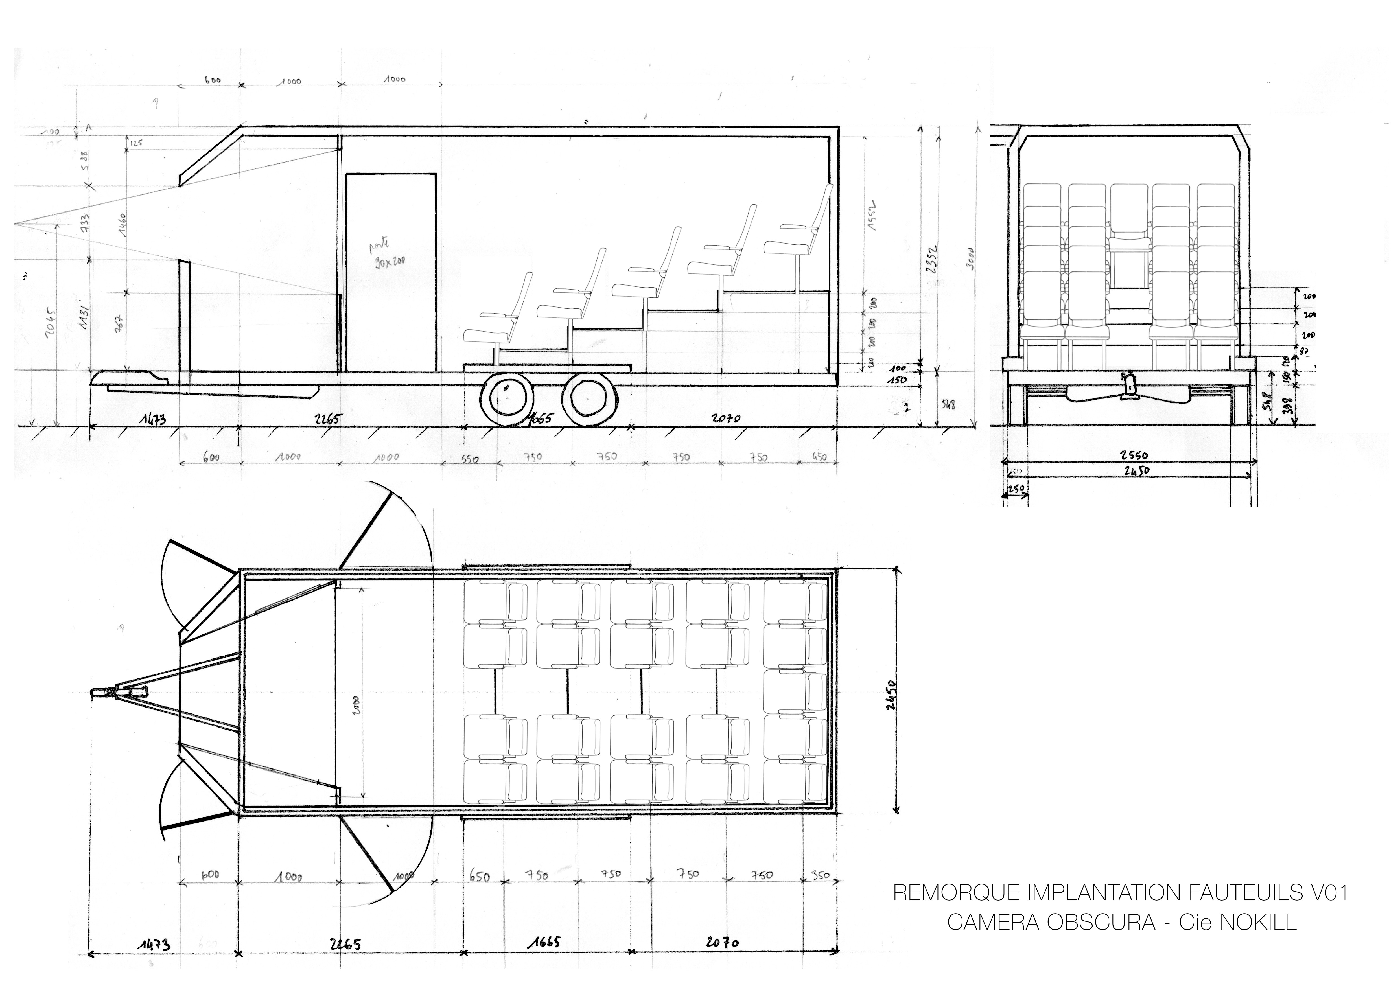
[picture p93: contenu/plans/remorque_implantation_fauteuil_V01.jpeg]
fauteuil V02
