LeonLenclos/camera-obscura/contenu/technique/fournisseurs.md

## Optiques, objectifs, prismes, verre

- [Camley - UK](www.camleyphotographic.com/)
- [Coprover - France](https://www.coprover.fr/)
- [bonfoton - Finland](https://bonfoton.com/products/bonfoton-camera-obscura-lens)
- [amazing camera obscura - UK](http://www.amazingcameraobscura.co.uk/shop.htm)
- [truemirror - USA](https://store.truemirror.com/collections/all?page=1)
- [bohroptics - Chine](http://bohroptics.com/en)
- [Legrand-Optique - France](https://www.legrand-optique.fr/)
- [Ruite-lentille télescope - Chine](https://fr.aliexpress.com/item/1005002190102811.html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)
- [AZ-lentille télescope - Chine](https://fr.aliexpress.com/item/1005003781677582.html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)
- [Concentrateur de pouvoir solaire - Chine](https://www.ebay.fr/itm/174584698996?hash=item28a60f1874:g:6mcAAOSwQbpc0Ogw)
- [Lens store - Chine](https://www.ebay.fr/str/ndg612)
- [Fresnel Lens shop - Chine](https://www.ebay.fr/str/niu4705)
- [Istar - USA](https://www.istar-optical.com/achromatic.html)
- [Intrument glasses - LONDON](https://www.instrumentglasses.com/)
- [Fossil Optical - LONDON](http://www.fossiloptical.com/work)

## Plaques animation

- [Antalis](https://www.antalis.fr/eshop/ws/html/catalog/resultPage?keyWord=oracal)
- [Plexiglas Shop](https://www.plexiglas-shop.com/fr/produits/plexiglas-xt)
- [The Solution Shop](https://www.thesolutionshop.com/fr/tube-m4-x-7-mm-plaqu%C3%A9-zinc-noir)

## Isolation
- [Nature liège](https://www.natureliege.fr/146-plaques-isolation-en-liege-isolation-phonique-et-thermique)

## Ecran, tissus, tulle, mousse
- [Showtex](https://www.showtex.com/fr/produits/ecrans-de-projection?page=1)
- [Teviloj](https://www.azur-scenic.com/produit/retro-translucide-depoli/)
- [Gerrietsj](https://www.gerriets.com/fr_fr/)
- [Guiraud mousse mazamet](https://www.guiraud-mousse.fr/)

## Carton
- [hermet](https://www.hermet.fr/)

## Peinture
- [adaptaville](https://www.adaptaville.fr/peinture-anti-chaleur-toit)

## Remorque
- [rouergue-remorque](https://www.rouergue-remorque.com/remorque/remorque-bw-tiny-house-ch-600-2/)
- [Adaico accessoires](https://www.adaico.com/fr/accessoires-de-carrosserie/fermetures.html?product_list_limit=60)

## Alu, tôle, mécanique
- [Plaques Alu avec finition - Arcelormittal](https://e-steel.arcelormittal.com/FR/fr/Aluminium/T%C3%B4le-Aluminium/T%C3%B4le-aluminium-laqu%C3%A9e/T%C3%B4le-aluminium-laqu%C3%A9e-poudre/p/P610030040)
- [ICI comp - paliers](https://www.ici-composants.com/)
