LeonLenclos/camera-obscura/contenu/technique/iris.md

L'utilisation d'Iris dans notre dispositif peut avoir deux fonctions :
- Servir d'obturateur, pour passer de l'image au noir ou d'une image à une autre.
- Servir de diaphragme, pour contrôler l'ouverture de la lentille (ce qui influe sur la luminosité mais aussi la netteté et la qualité de l'image)

Les lentilles que nous utilisons actuellement ne sont pas assez lumineuse pour qu'on puisse avoir envie de réduire leur ouverture donc nous avons décidé de ne pas utiliser d'iris et d'utiliser pour l'instant des obturateurs plus simples. Cette page rassemble les notes relatives à l'utilisation d'iris prisent avant la décision de ne pas en utiliser.

# Les iris

Pour enchainer les différents plans, une solution envisagée est de caler des diaphragmes à iris devant les objectifs et de concevoir un système de télécommande manuelle depuis la régie.

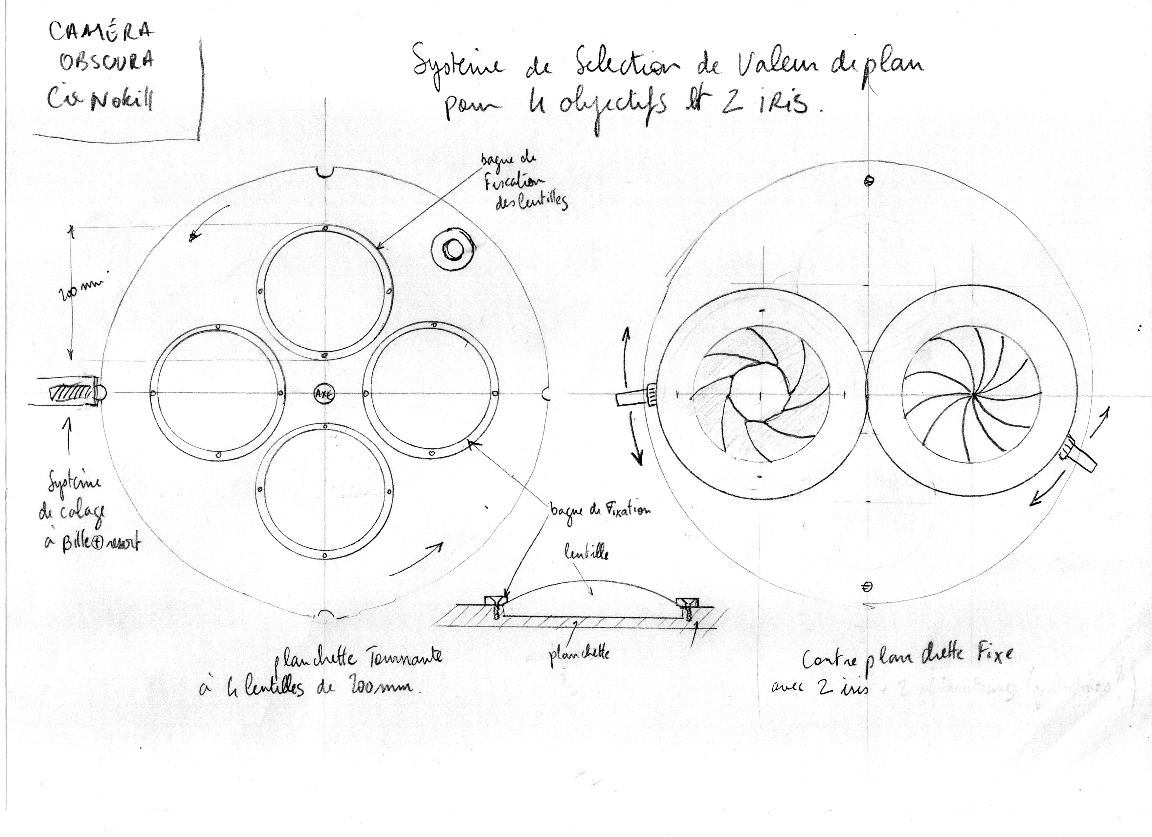
[picture p94: contenu/plans/planchette_V01.jpeg]
planchette et iris

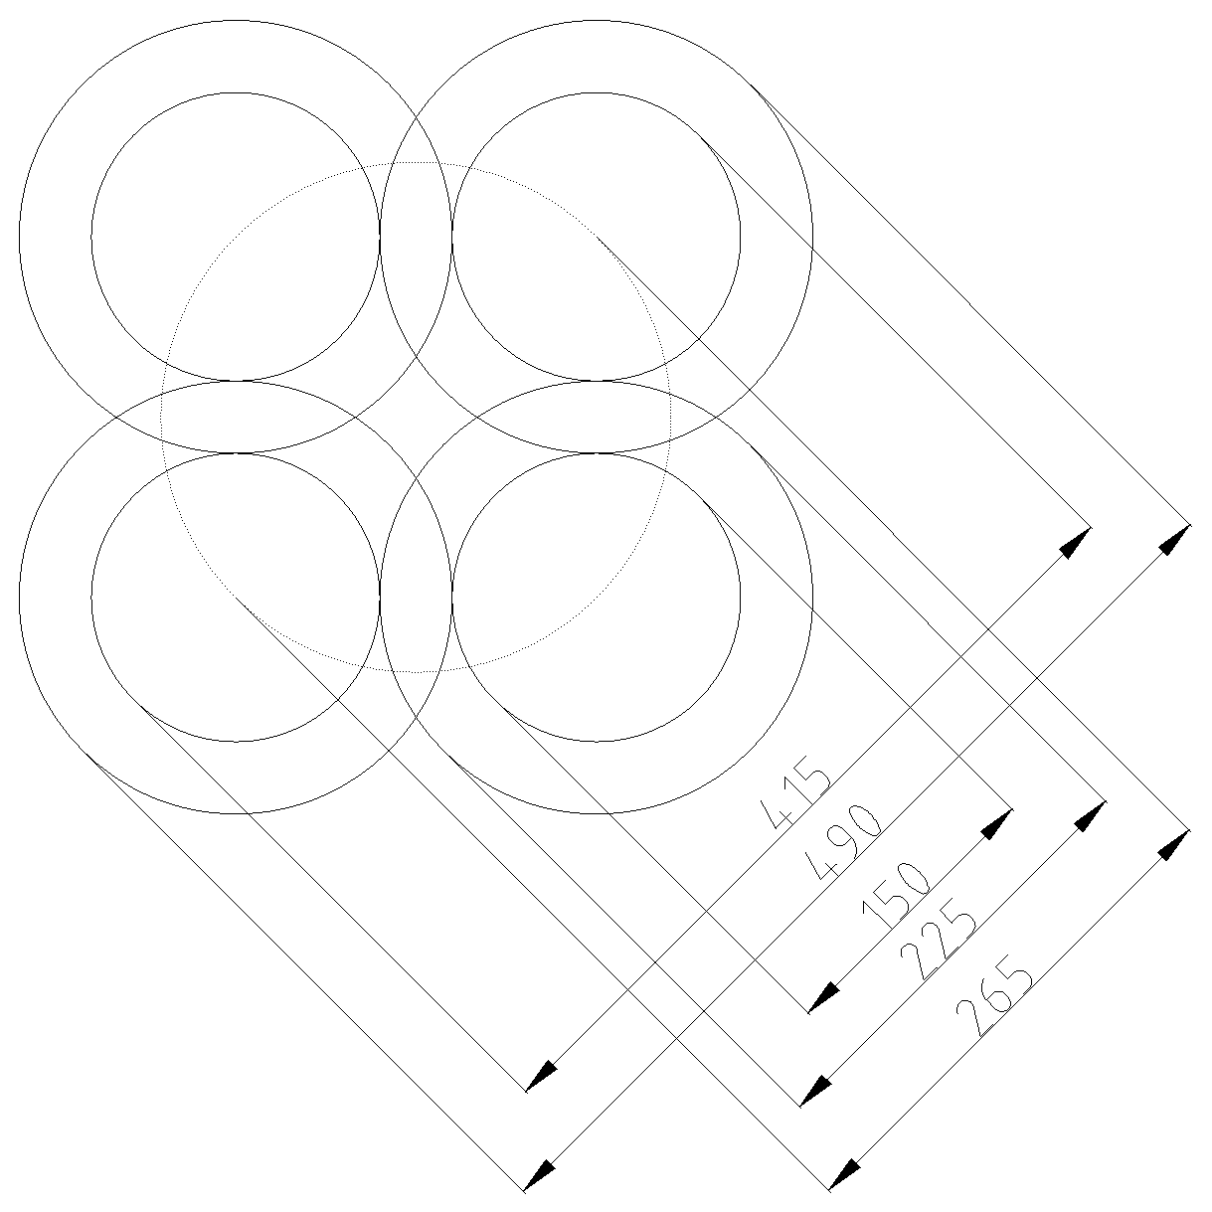
[picture p95: contenu/plans/planchette-draft.png]
Mesures planchette


Les diaphragmes à iris peuvent aussi être utilisés pour occulter les hublots de la remorque au début du spectacle.

Pour l'instant aucun modèle du commerce ne correspond aux dimensions des lentilles (Apperture max = 150 mmm). Par ailleurs les modèles à fermeture totale (Apperture min = 0 mmm) sont assez rares et très chers.

Une solution consiste à fabriquer des iris spéciquement pour notre usage.

## Conception

### Dimensions

Principales contraintes :
- Apperture max = 150 mmm
- Apperture min = 0 mmm
- Outside diameter max = 225 mm
- Remarque : plus il y a de lames, plus le diametre hors-tout est réduit, mais plus il y a de lames moins il est facile d'obtenir un faible minimum d'ouverture...

Un outil en ligne pour dessiner un iris :

[iris-calculator.com](https://iris-calculator.com/)

### type d'iris

Pour des raisons esthétiques et pratiques, le projet est de concevoir un iris à lames. Comme expliqué plus haut, il faut qu'il soit à fermeture totale. Voici plusieurs solutions pour concevoir une fermeture totale, infaisable avec un iris simple :

#### Modèle à double iris

- Principe : 2 jeux de lames décentrés se supperposent pour empêcher la lumière de passer.
- Remarque : l'obturation n'est pas "étanche" ce qui la rend suffisante pour les objectifs mais probablement pas pour les hublots.

[Un article sur les modèles à double iris](https://iris-calculator.com/full-closure/)

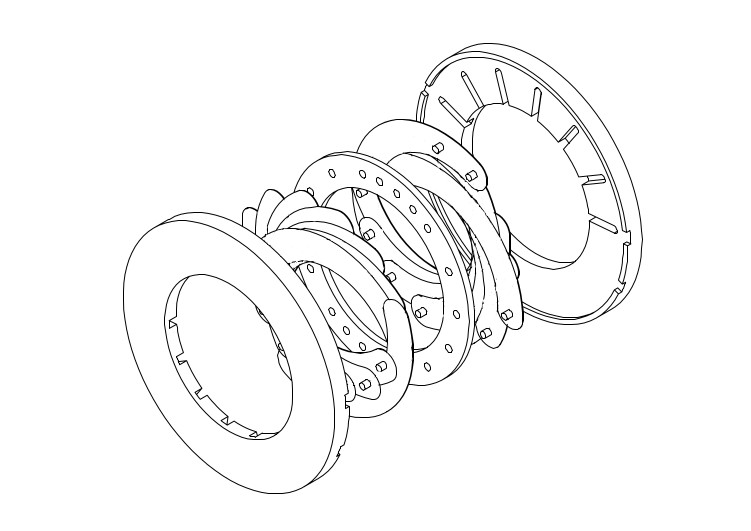
[picture p96: contenu/plans/dual_plane_iris.jpg]
iris double plan

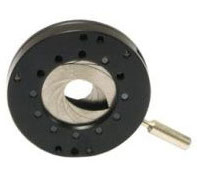
[picture p97: contenu/photos/iris_double.jpg]
iris double plan
  

#### Modèle à lame ocultante

- Principe : en bout de course, une lame de grande dimension vient occulter le diaphragme minimum restant.
- Remarque : pas trouvé de plan de ce système pour l'instant.
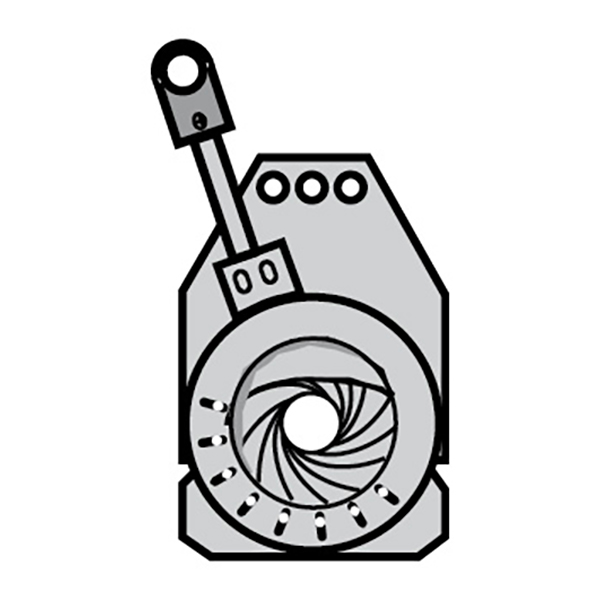
[picture p98: contenu/dessins/iris_lame_occultante.jpg]
iris lame occultante


#### Doublet iris/obturateur

- Principe : Pour chaque objectif, on peut commander depuis la régie un obturateur et un iris.

## Fabrication

### Matériaux

- lames en métal
- cadres métal ou bois
