LeonLenclos/camera-obscura/contenu/ecriture/conduite-leon.md

Dernière mise à jour : Résidence à Circa Avril 2024

## Générique de début

- Faire défiler les titres
- Passer à la plaque prologue (→) 

## Prologue

- Animer les vagues jusqu'à la fin du fondu au noir
- Passer à la plaque titre (←)

## Matin

- Ranger la plaque prologue
- Rapprocher la plaque niveau de l'eau
- Changer le titre
- S'assoir
- Préparer marionettes

## Niveau de l'eau

- Quand la lentille frontale est ouverte, Attendre (Lire)
- Passer à la plaque niveau de l'eau
- Animer marionette dame
- Quand Lucile a déscendu l'eau, Animer les poissons
- Quand Lucile a remonté l'eau, Attendre un peu, puis animer le linge.

## Plein emploi

- Passer dans le champ

## Période heureuse

- Aider Lucile à passer à la plaque période heureuse
- Changer le titre
- Manip avec Lucile jusqu'au deuxième pas
- Aller au décors
- Aider Lucile à passer à la plaque titre

## La lune

- Jouer la lune (prendre son temps)

## Bon sens

- Enlever costume lune, mettre col roulé noir
- Aller à la face (sans descendre des praticables)
- Passer à la plaque journal après la phrase musicale
- Descendre
- Dès que l'obturateur frontal est fermé, mettre le fond noir
- Prendre la prothèse
- Monter sur praticable frontal
- Éloigner plaque journal
- S'installer avec la prothèse (à genoux, fesses sur talons).
- Se faire chasser par Lucile,
- Vite enlever le fond noir

## Mutation

- Changer le titre
- Attendre que Lucile s'active pour remettre le reflecteur
- Amener Mutation 2 Par l'ouest
- Passer à la plaque Mutation 2 et l'animer
- Passer à la plaque Titre

## St tropez

- Ranger Mutation 2
- Changer le titre
- Amener Le podium par l'ouest et attendre avec le podium dans les mains

## Podium

- Poser podium sur le rail dès qu'il y a de la place
- Passer à la plaque podium
- Animer podium
- Passer à la plaque titre

## Blague

- Aller chercher Plaque periode malheureuse
- Changer titre

## Periode Malheureuse

- Passer à la plaque periode malheureuse et l'animer. (assis)
- Passer le titre

(Noté de tête à partir de là...)

## Golden Record

- Obturateur fermé : installer gr1
- Obturateur ouvert : animer gr1
- Obturateur fermé : installer gr2
- Obturateur ouvert : animer gr2
- Se faire pousser par Lucile (gr3)
- Amener les titres de l'autre côté (ouest) et en profiter pour le changer.
- Aller s'installer pour le froid

## Le Froid

- En gros plan, ne pas trop bouger (entrée/sortie de champs)

## Comportement

- Venir avec Comportement 2
- Animer Comportement 1 avec Lucile
- Animer Comportement 2
- Mettre le titre

## Mode 

- Mettre la mode
- Mettre le titre

## Conversation

- Au premier cut (après titre) : Ranger la mode et préparer le dernier titre
- À un moment, face cam, raccrocher et faire glisser le titre

## Chanson

- Se changer, prendre clavier,
- Jouer
- Partir quand lucile est en place

## Epilogue

- Préparer épilogue 2
- Animer épiolgue 2 avec lucile
- Noir, mettre le générique.
