LeonLenclos/camera-obscura/contenu/ecriture/conduite-lucile.md

Dernière mise à jour : Résidence à Circa Avril 2024

## Générique de début

- envoyer place prologue →
- Avec le son du bateau anim bateau (debout) être sortie vers « fumée sans feu »
- aller se placer dans le décor du matin
- Changer le titre (Je me souviens du jour où personne ne s’est levé)

## Je me souviens du jour où personne ne s’est levé

- dormir dans le lit, léger réveil
- Quand le titre du niveau de l’eau revient, changer le titre (Plein emploi)

## Je me souviens le niveau de l’eau

- anim du Niveau de l’eau (monté/descente avec la poulie)
- Pendant le noir désarmer la plaque de l’eau
- Descendre la plaque du Niveau de l’eau
- Enlever chemise

## Le plein emploi

- Changer le titre (Une période heureuse)
- Préparer l’anim de Période heureuse (vérifier qu’il y a bien l’écart pour chaque pas)
- Mettre costume du Bon sens (chemise / collier / gants)
- Envoyer plaque Période Heureuse →
- Anim Période heureuse (pas calé avec le dernier accord de guitare) + mettre une pince pour caler la plaque
- Enlever plaque Période Heureuse ← et mettre en place le titre

## Le jour où la lune est tombée sur terre

- Descendre plaque Période heureuse + mario Période heureuse
- Changer titre (Le Bon sens)
- Monter plaque Journal
- Finir de mettre costume Bon sens
- Après ouverture de l’obturateur et lecture du titre, envoyer plaque Journal →

## Le bon sens

- Aller se placer dans le décor latéral (journal + lunettes)
- Retourner le journal à (imiter), difficulté pour la lecture
- Mettre les lunettes quand Léon monte sur le pratos de face
- Après fermeture de l’obturateur latéral retirer les lunettes, et passer sur le pratos de face, Pano en squat, sortir du champs
- Descendre la prothèse
- Enlever les costumes
- Passer sous le praticable et préparer la plaque Mutation 1

## Mutation

- Quand l’obturateur se ferme, faire glisser le titre Mutation ←
- Faire glisser la plaque Mutation 1 ←
- Anim Mutation 1
- Descendre Mutation 1 ←
- Changer titre (Vacances à Saint Tropez)

## Les Vacances à Saint Tropez

- Envoyer titre Vacances à Saint Tropez →
- Envoyer plaque Vacances à Saint Tropez →
- Faire défilé les photos de Saint Tropez

## Le podium

- Descendre la plaque Vacances à Saint Tropez ←
- Anim du Podium (bras 4e / descendre podium / apparition 6e / descendre podium / décrocher podium et le monter pour le faire disparaitre)
- Descendre mario Podium ←
- Aller se placer dans le décor latéral
- Changer le titre (Blague)

## La Blague

- Scène de la blague : regard fixe objectif trouver une neutralité pleine de nuances
- Changer le titre (Golden Record) quand l’obturateur s’est fermé
- Monter Golden Record 1 ←
- Monter Golden Record 2 ←
- Monter Golden Record 3 ←
- Faire glisser Golden Record 3 ← (vérifier que le volet du visage est bien tiré au début)
- Anim Golden Record 3 (visage Jul)
- Envoyer plaque titre Le Froid →

## Le Froid

- Descendre GR 1 ←
- Descendre GR 2 ←
- Descendre GR 3 ←
- Changer titre (Comportement)
- Monter plaque Comportement 1 ←
 
## Comportement

- Anim Comportement 1 (regard / rougeurs / tremblements)
- Faire glisser Comportement 1 ←
- Changer titre La mode
- Descendre Comportement 1 ←
- Monter plaque La Mode →
- Envoyer Titre →
- Envoyer plaque La Mode →

## La Mode

- monter plaque Epilogue 1 →
- Se mettre en place pour La Conversation dans le décor latéral (accessoire téléphone)
 
## La conversation

- Trouver un top clair quand c’est le dernier plan sur moi
- Fermeture obturateur latéral
- Changer le titre ?? (Ultime chanson)
- descendre et / ou rentrer dans la régie

## L’Ultime chanson

- Chanson I will survive revisitée
- Sortir de la régie
- Envoyer Epilogue 1 →

## Epilogue

- Anim Epilogue 1 (le personnage sort de l’eau)
- Anim Epilogue 2
