LeonLenclos/camera-obscura/contenu/technique/vitres.md

# Les vitres

Nous utilisons :
- Des vitres simples pour protéger, isoler ou étancheifier l'interieur d'une chambre.
- Des miroirs pour les [renversements d'image](renversement.md) ou simplement changer l'angle de l'axe.

## Qualité des mirroirs

Trois problèmes lors de l'utilisation de miroirs dans nos systèmes optiques :
- perte de luminosité
- effet de double image
- trait central dans le prisme en toit d'Amici

Les deux premiers problèmes semblent pouvoir se régler avec l'utilisation de miroir extra clair (Verre anti reflet)

Le troisième problème doit pouvoir se contourner grace à l'utilisation de miroirs *first face*, c'est-à dire des miroirs dont la couche réfléchissante est devant le verre et pas derrière. L'utilisation de miroir *first face* éliminerait aussi les deux autres problèmes qui sont liés à la qualité du verre. Ces mirroirs sont plus difficiles à trouver, plus chers et plus fragiles.

## Travailler le verre

Monsieur Azemar nous aides sur pas mal de coupes et nous a fait un petit cours rapide pour couper le verre.

### Materiel necessaire

- Un coupe-verre
- Un pinceau
- Du pétrole

Éventuellement :

- Une pince à gruger
- Un contourneur

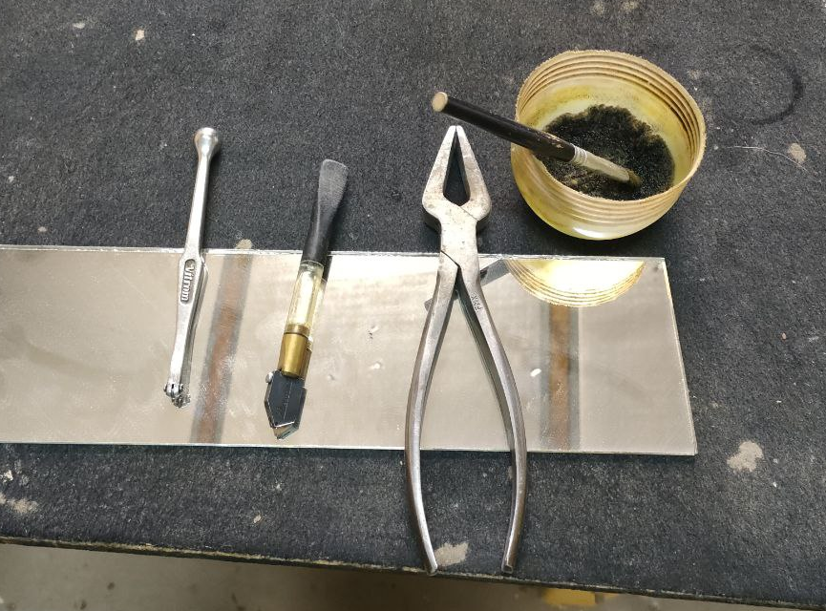
[picture p130: contenu/photos/outils_verre.png]
Outils de Monsieur Azemar


### Finitions

Pour que les bords de la vitre ne soient pas tranchants on peut les travailler avec du papier de verre (grain 80) sur une cale.

## Hublots

Pour les volets des hublots il faut une bague de diametre interieur 93.8 et de diametre exterieur 160 à visser dans la tranche du pvc.

Les hublots sont fait avec du tube pvc. Les references :

- manchons : D110PN16FF à coller
- tubes :D110PN16 PVC pression
