LeonLenclos/camera-obscura/contenu/ecriture/presentation.md

{% include alert.html type="archive" %}

# Texte de présention

*Camera Obscura* est un spectacle de rue qui plonge le spectateur dans un dispositif cinématographique ancestral, sans pellicule, ni vidéo, ni électricité, et qui n’utilise comme énergie que celle du soleil et des comédiens. Le public s’installe dans un lieu fermé, une chambre noire, et assiste à la projection d’un film dont les images sont des captations du monde extérieur qui transitent par un dispositif optique fait d’objectifs et de miroirs.

Dans la chambre noire, les voix, les sons et la musique sont produits et interprétés en direct sur un ensemble d’instruments acoustiques et mécaniques. Ces ondes sont traitées par des dispositifs acoustiques qui donnent l’illusion d’une bande pré-enregistrée diffusée à travers des hauts-parleurs.

Immergé dans cette proposition, le spectateur vit une expérience sensorielle unique composée de sons bruts et d’images hyper définies qui lui suggèrent de réinterpréter le monde qui l’entoure. La transformation du réel, de ce qui se passe à l’extérieur de la chambre noire, est renforcée par le choix du cadre et l’interprétation, la mise en fiction qui en est faite par les comédiens.
