LeonLenclos/camera-obscura/contenu/ecriture/scenar2.md

---
type: scenario
---

{% include alert.html type="archive" %}

*Plan large d'une place animée d'un centre ville. Des enfants courent, des passants passent, d'autres sont assis sur des bancs ou sur des marches.*

**VOIX OFF (IMPRO)**

L’homme que vous voyez là-bas au milieu de l’écran qui fume une cigarette assis à côté du type avec une chemise rose, c’est moi. J’ai eu une matinée difficile, pas mal de problèmes au boulot et je viens volontairement d'ignorer un appel téléphonique de mon chef. C’est la première fois que je fais ça...

**VOIX OFF**

Non pardon, c’est une blague en vrai je suis la personne avec la chemise rose.

*La personne avec la chemise rose fait un signe de la main en direction de l'objectif.*

**VOIX OFF**

Je m’ennuie et comme souvent quand je m’ennuie je choisis un passant au hasard et je fais semblant d’être lui. J'imagine sa vie, je me raconte son histoire. Ça fait une demi-heure que je joue à ça et je commence à en avoir marre, j’aimerais bien trouver une idée plus amusante...

*L'homme se lève et fait les 100 pas...*

*L'homme s'arrête brusquement.*

**VOIX OFF**

J’ai une idée ! On va se marrer. Je vais faire semblant que je vois une soucoupe volante qui traverse le ciel et les gens vont halluciner.

*Une boule de feu en forme de soucoupe volante traverse le ciel. L'homme la montre du doigt en criant dans l'indifférence générale.*

*L'homme regarde les gens autour de lui.*

**VOIX OFF**

Comment ça se fait que personne n'ait réagi en voyant la soucoupe volante ?

On est bien d'accord qu'il y a une socoupe volante au dessus de nous, je suis pas fous !

La seule explication possible, c'est que tous les autres sont de mèche pour me faire croire que les extraterrestres n'existent pas.

*L'homme se retourne. On le voit de dos.*

*Gros plan.*

**VOIX OFF**

Néanmoins j’ai de très bonnes raisons de penser que les extraterrestres existent...

*L'homme se retourne face à nous. C'est un alien.*

*Rire diabolique*

*Très Gros plan. *

**VOIX OFF**

Je rigole.

*Il enlève son masque.*
