LeonLenclos/camera-obscura/contenu/ecriture/sequences.md

---
type: scenario
---

{% include alert.html type="archive" %}

## Séquence : Ça pourrait être pire

*Une personne joue de la sanza, bruit de craquement.*

**VOIX OFF**

Oh non je me suis cassé un ongle ! Trop chiant

*Gros plan de la main avec le visage triste qui regarde les ongles*

**VOIX OFF**

Bon en vrai c'est pas si grâve j'aurais pu marcher dans une merde de chien

*La personne marche (gros plan pied), pose le pied dans une merde de chien*

**VOIX OFF**

Oh non relou ! Bon mais ça va ça aurait pu être pire j'aurais pu marché sur un clou

*Elle marche sur un clou*

**VOIX OFF**

Aïe ! Bon ça aurait pu être pire j'aurais pu me faire arrêté par la police

*Image de course poursuite avec la police*

**VOIX OFF**

ACAB ! Mais en vrai ça aurait pu être pire. Par exemple j'aurais pu oublier de mettre des vêtements en allant au travail ce matin.

*Ascensseur qui s'ouvre, personnage tout nu avec malette*

**VOIX OFF**

Oh merde ! Faut relativiser, ça aurait pu être pire, j'aurais pu plonger dans une piscine vide.

*Personnage plonge, sauts perilleux et arrive au fond de la piscine*

**VOIX OFF**

Ou pire j'aurai pu habiter sur un volcan.

*Maison sur un volcan en erruption, la maison est emportée par l'erruption dans les airs*

**VOIX OFF**

Ou encore pire j'aurais pu me faire manger par un requin

*Requin qui mache avec deux jambes qui depassent*

**VOIX OFF**

Mais ça aurait pu etre encore pire, j'aurais pu vivre sous un etat fasciste dans un pays en guerre.

*Des rangées de botte marchent dans un sens. Des chaussures dans l'autre sens sont forcées de faire demi-tour.*

**VOIX OFF**

Ou pire toute l'humanité aurait pu disparaitre dans une catastrophe nucléaire.

*Terre avec explosion*

**VOIX OFF**

Ou pire ça aurait pu être de ma faute.

*Perso glisse sur une peau de banane et appuie sur le bouton*

**VOIX OFF**

Mais ça aurait pu être pire, rien n'aurait pu jamais exister.

*Noir (ou la personne qui regarde ses ongles)*

## Séquence : Camionnette rouge

*2D : Une camionnette roule sur une route bordée d'arbres*

**VOIX OFF**

Un de ces jours où je devais me rendre à un certain endroit j'ai été pris en stop par une camionnette rouge.

On n'a presque pas parlé pendant une heure, peut-être même que j'ai un peu dormi. Et puis soudain la camionnette m'a dit :

*Conducteur au volant d'une voiture, parle à la caméra (doublé par la voix off)*

**VOIX OFF**

"Ce qui est le plus important, c'est de travailler son imagination, Pour ça il y a plein d'exercices que l'on peut faire au quotidien. Par exemple, s'imaginer ce qu'il y a derrière un mur, s'imaginer que telle chose que l'on regarde est d'une autre couleur.

Par exemple quand je suis assis à une table, j'imagine d'autres objets posés dessus. Il faut commencer par des objets familiers que l'on connait bien, puis on peut ajouter des objets inventés, Des objets animés, sonores, des objets lumineux qui éclairent d'autres objets.

On peut aller très loin comme ça. En fait tout est possible, le tout c'est de pratiquer tous les jours."

## Séquence : L'hiver.

*Gros plan personne toute en sueur*

**VOIX OFF**

Parfois en ces temps-ci, la chaleur de l'été est insuportable

*2D : schéma explicatif à la "C'est Pas Sorcier" de l'eau qui bout dans le corps*

**VOIX OFF**

Tout fond autour de moi et à l'intérieur de moi. L'eau de mon corps se met à bouillir, la vapeur ainsi produite envahit mon cerveau et tout devient brumeux. Le sol fond, mes chaussures fondent, elles collent au sol, je ne peux plus me déplacer, je deviens immobile, je perds ma mobilité, je deviens immeuble.

*Gros plan personne emmitoufflée dans une écharpe, de la buée sort de sa bouche, de la neige tombe.*

**VOIX OFF**

La technique consiste alors à s'imaginer qu'il fait froid, froid comme le coeur de l'hiver dans une région froide, vraiment froide, une région froide comme on n'en fait plus. Je resterais comme ça quelques minutes puis je retournerais à l'été juste avant de tomber malade.
