LeonLenclos/camera-obscura/contenu/technique/surimpression.md

{% include alert.html type="archive" %}

## Incrustation et surimpression

Parmi les effets visuels et trucages que nous envisageons d’explorer, il y a l’idée de développer des dispositifs d'incrustation ou de surimpression optique.
L’idée est de créer des systèmes optiques qui permettraient d'incruster un élément visuel venant soutenir la narration sur une petite partie de l’image.

### Cache contre cache (incrustation)

Avec un renvoi de miroir à 45 ° et une vitre à plat, des transparents ou des jeux d'ombres éclairés par le soleil, transitent par l'objectif pour apparaitre sur l'écran. 
Un système de cache et de contre cache permet d'éviter les surimpressions.

### Projection de diapo (surimpression)

Nous avons imaginé un système de lentilles placé à l’extérieur qui concentre la lumière du soleil.
Une fibre optique de gros diamètre qui transporte cette source vers un dispositif type mini-projecteur de diapo pouvant être manipulé à la main à l’intérieur de la remorque par l'opérateur dissimulé derrière l'écran. Dans ce cas l'image projetée se rajoute à celle qui apparaît sur l'écran pour créer un effet de surimpression type fantôme.

Pour l'instant cette piste n'a pas été testée.
