LeonLenclos/camera-obscura/contenu/technique/vrac.md

{% include alert.html type="pas-interessant" %}

- lyre retournement
- hublot iris
- est-ce qu'on peut graver des disques pour gramophone

### Courroie

Courroie trapezoidale plus adaptée pour la clim (transmission de puissance)

Courroie dentée plus adaptée pour la commande de la tourelle (synchrone)

#### Notes sur une spec alternative de poulie dentée

- Diamètre poulie : d = 76
- Périmètre poulie : p = d × π ≃ 238,76
- Largeur courroie : E = 20
- Pas : m = 8M
- Nombre de dents : n = d/m ≃ 30
- Caracteristique poulie : Poulie dentée moyeu amovible
- Référence poulie : PD8M30-20MA

### Notions mécanique

La force en N (Newton) c'est des kg·m·s<sup>-2</sup>. 1 N c'est donc la force qui appliqué à un objet d'1 kg pendant 1 s permet d'accéler cet objet d'1 m/s

Le couple parfois noté Nm en fait c'est des N·m. 1 N·m permet d'appliquer une force de 1 N à un objet situé à 1 m de l'axe de rotation.

### Plexi

#### Fournisseurs

Antalis

- Oracal 8300 : 8.5€/m² HT
https://www.antalis.fr/eshop/ws/html/catalog/resultPage?keyWord=oracal+8300
- Oracal noir 631 : 5.80€/m² HT

Plexiglas shop

- Dimensions 2050×1520 (4×1025×760)
- Site : https://www.plexiglas-shop.com/fr/produits/plexiglas-xt/pl0a000gt.html?force_sid=phuaot8ppp4ll38091l458mo28
- Prix au m2 : 32,02€ HT
- Prix par plaque 1000×700 : 25€ HT

Leroymerlin (qualité ??)

- Dimension plaque : 1000×700 
- Site : https://www.leroymerlin.fr/produits/menuiserie/verre-et-verre-synthetique/verre-synthetique/plaque-polycarbonate-transparent-lexan-ep-3-mm-100-x-70-cm-83592666.html
- Prix plaque : 48.82 € TTC

Plaqueplastique.fr

- Dimension plaque : sur mesure
- Site : https://plaqueplastique.fr/product/plaque-plexiglass-gs-3mm-transparent/
- Prix au m2 : 38,95€ HT
- Prix par plaque 1000×700 : 27,27€ HT
