LeonLenclos/camera-obscura/contenu/ecriture/storyboard.md

# Animatique

L'animatique est la version animée et sonorisée du storyboard. Le rythme, les sons, les intentions sont approximatives.

[Visionner l'animatique sur Viméo](https://vimeo.com/cienokill/animatic0124?share=copy)

# Storyboard

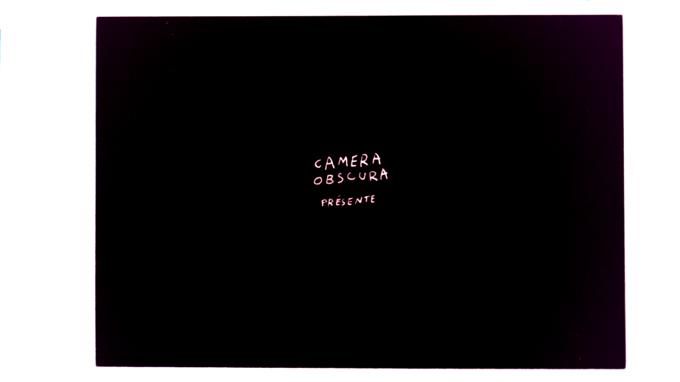
[picture p134: contenu/img/storyboard/001.png]

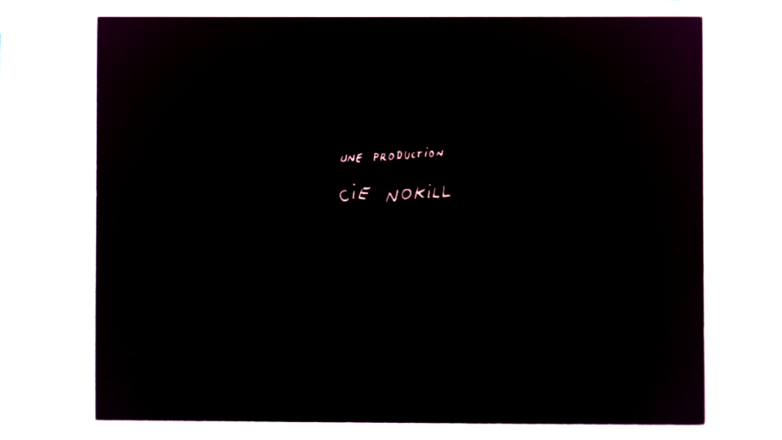
[picture p135: contenu/img/storyboard/002.png]

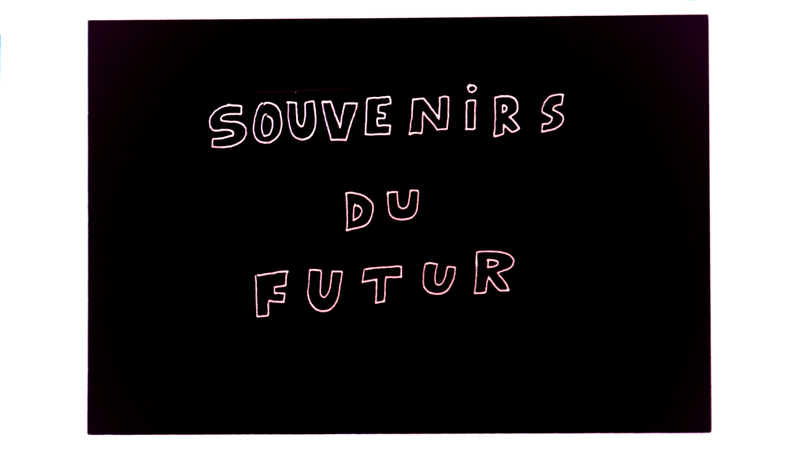
[picture p136: contenu/img/storyboard/003.png]

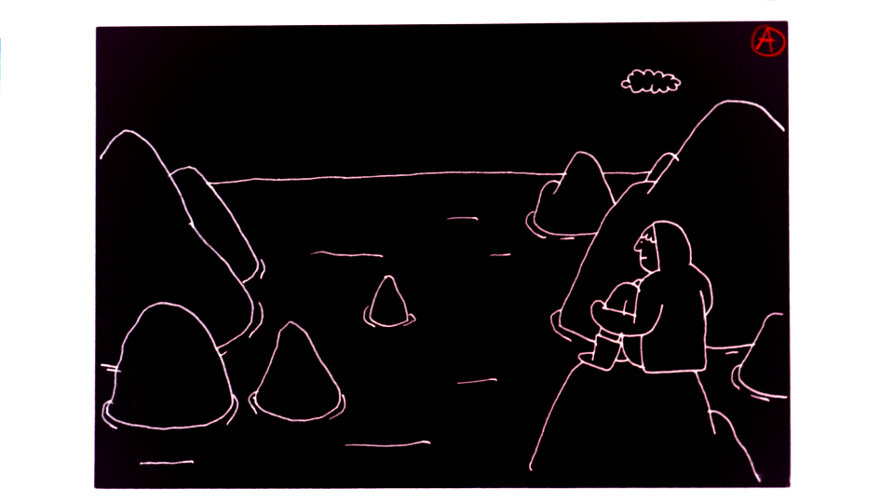
[picture p137: contenu/img/storyboard/004.png]

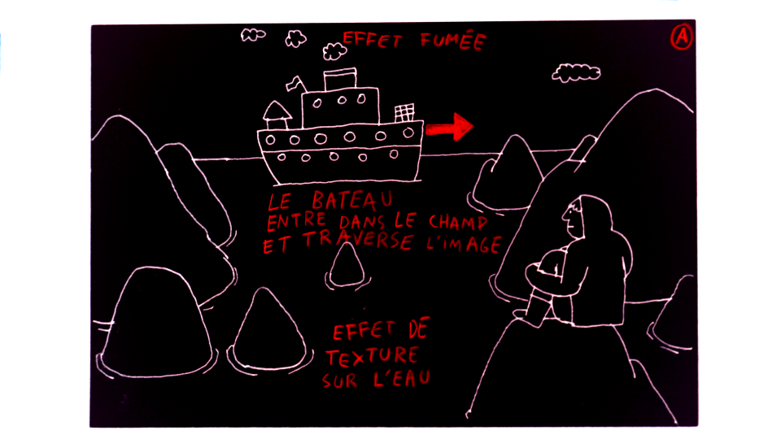
[picture p138: contenu/img/storyboard/005.png]

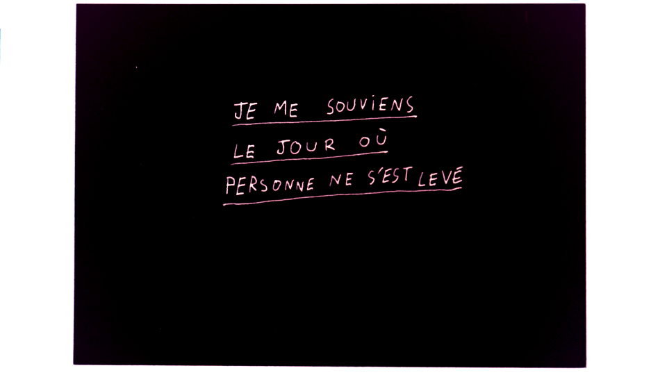
[picture p139: contenu/img/storyboard/006.png]

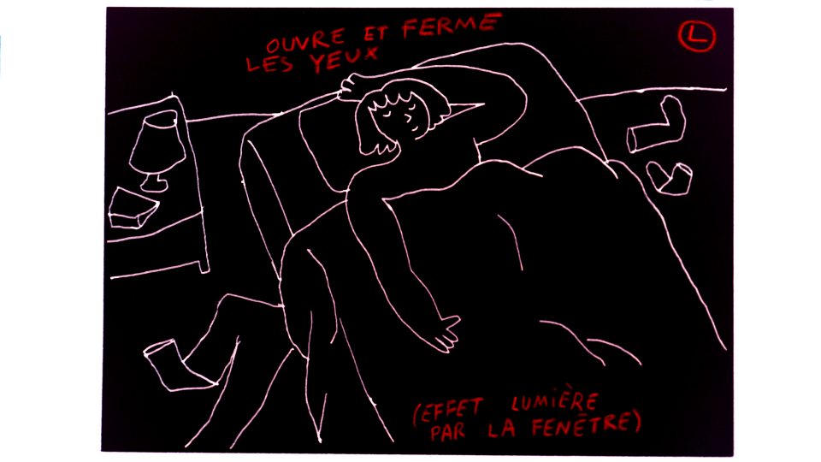
[picture p140: contenu/img/storyboard/007.png]

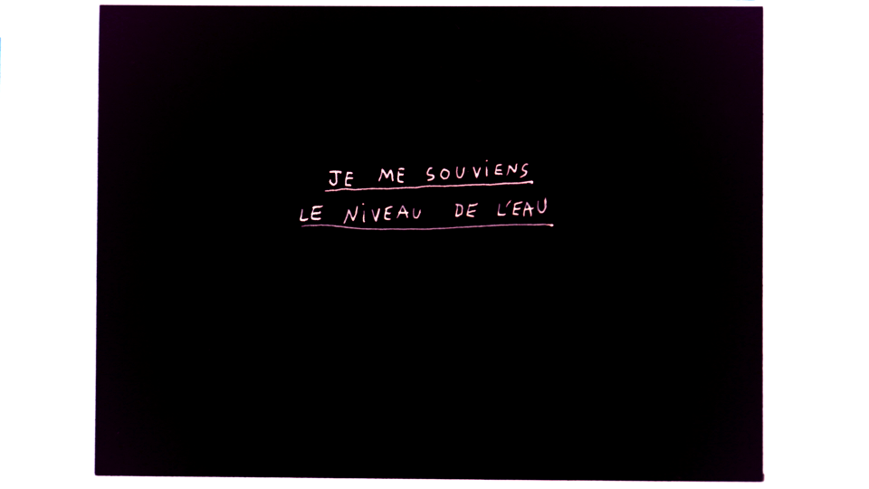
[picture p141: contenu/img/storyboard/008.png]

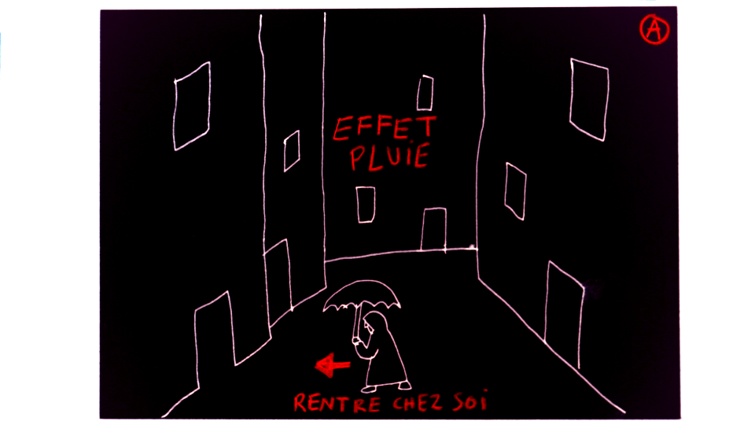
[picture p142: contenu/img/storyboard/009.png]

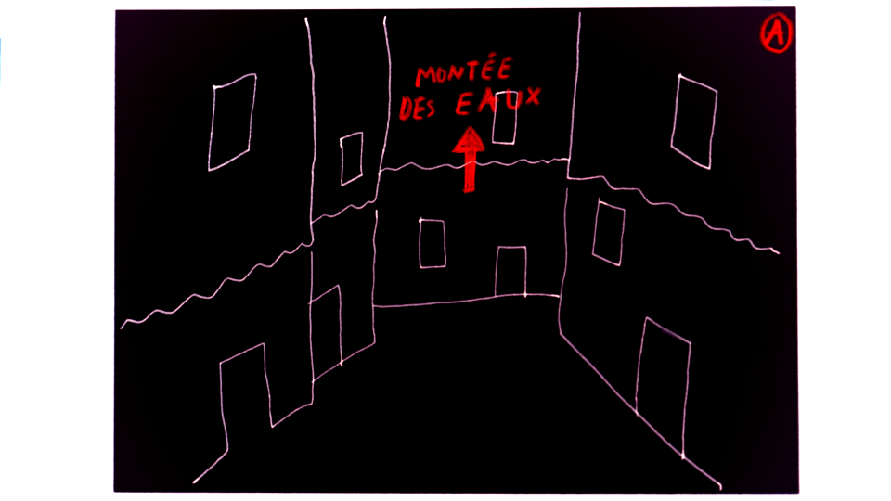
[picture p143: contenu/img/storyboard/010.png]

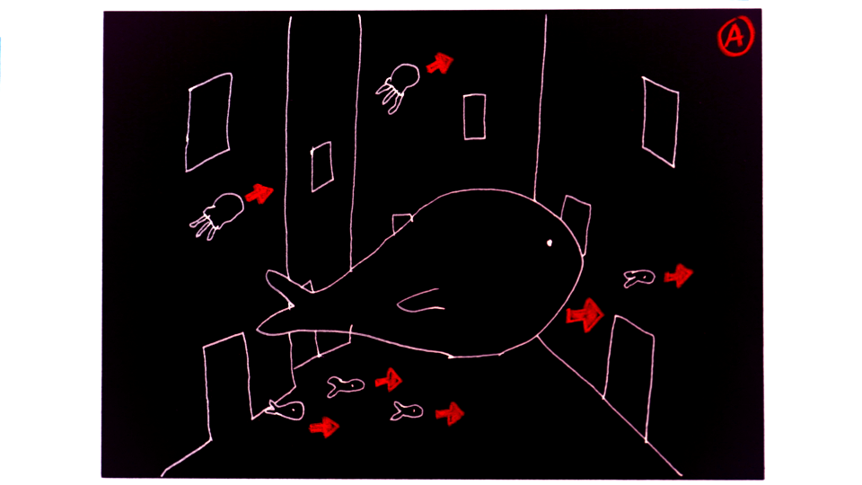
[picture p144: contenu/img/storyboard/011.png]

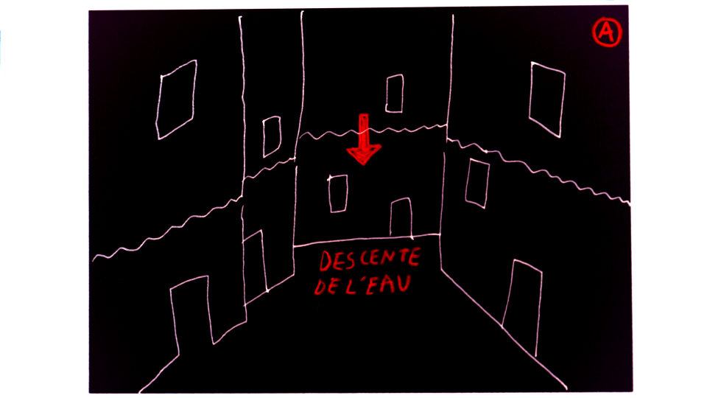
[picture p145: contenu/img/storyboard/012.png]

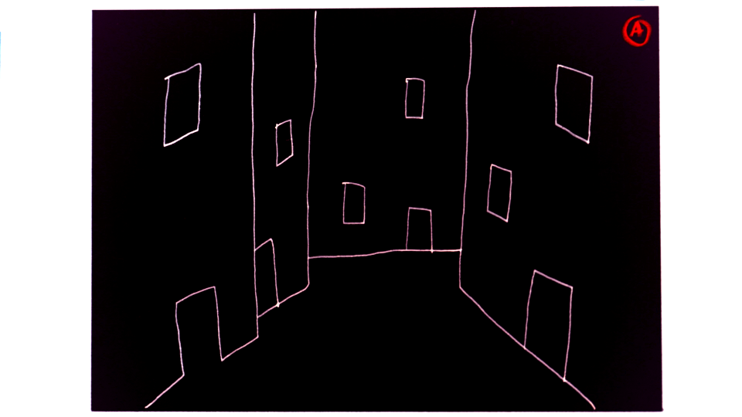
[picture p146: contenu/img/storyboard/013.png]

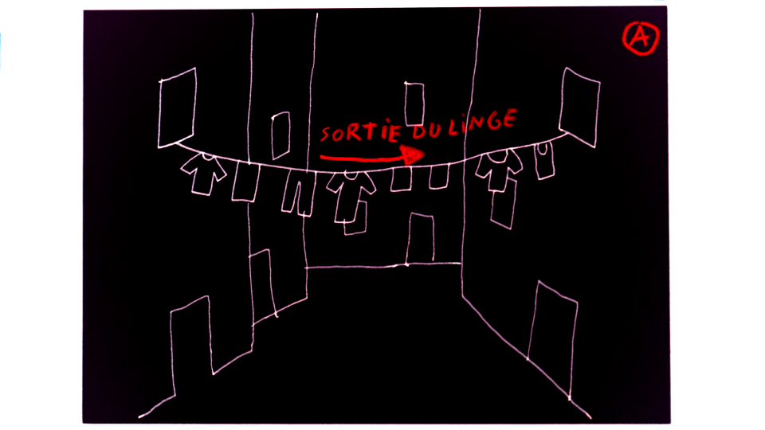
[picture p147: contenu/img/storyboard/014.png]

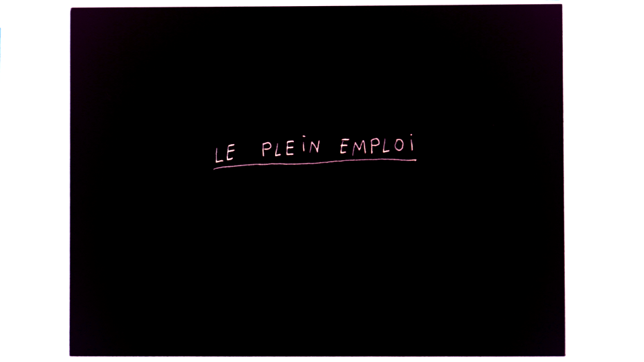
[picture p148: contenu/img/storyboard/015.png]

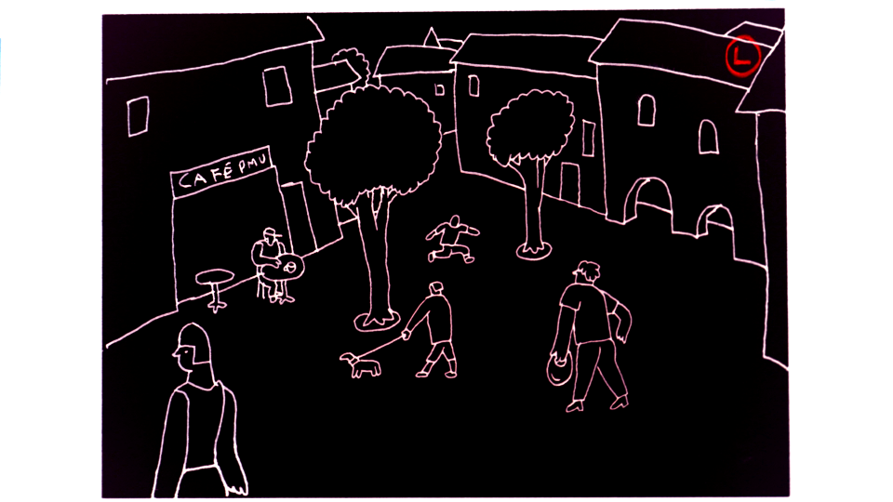
[picture p149: contenu/img/storyboard/016.png]

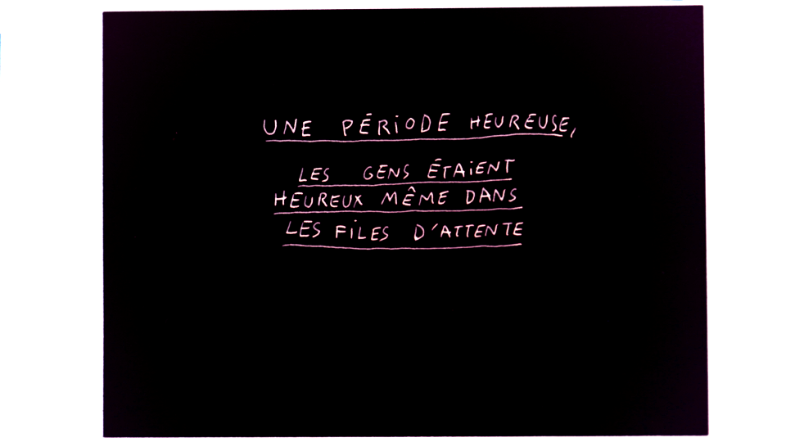
[picture p150: contenu/img/storyboard/017.png]

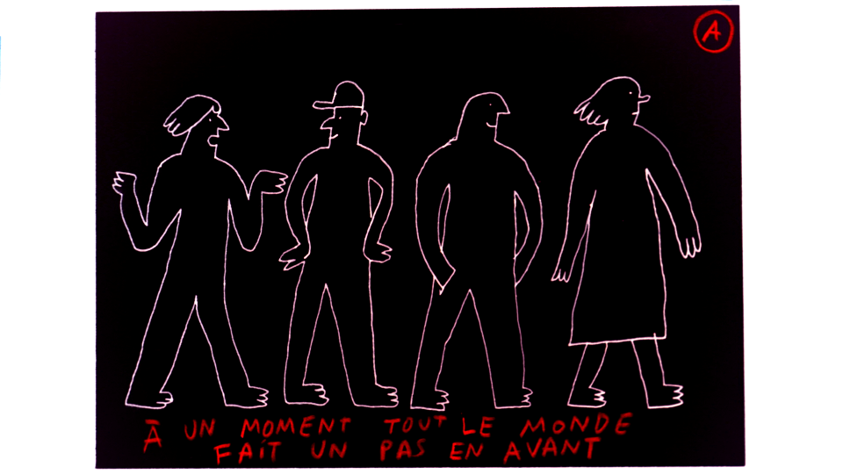
[picture p151: contenu/img/storyboard/018.png]

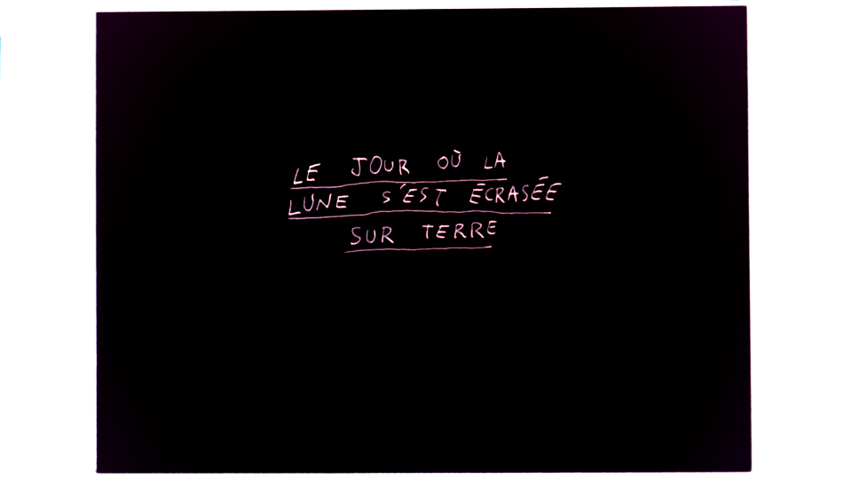
[picture p152: contenu/img/storyboard/019.png]

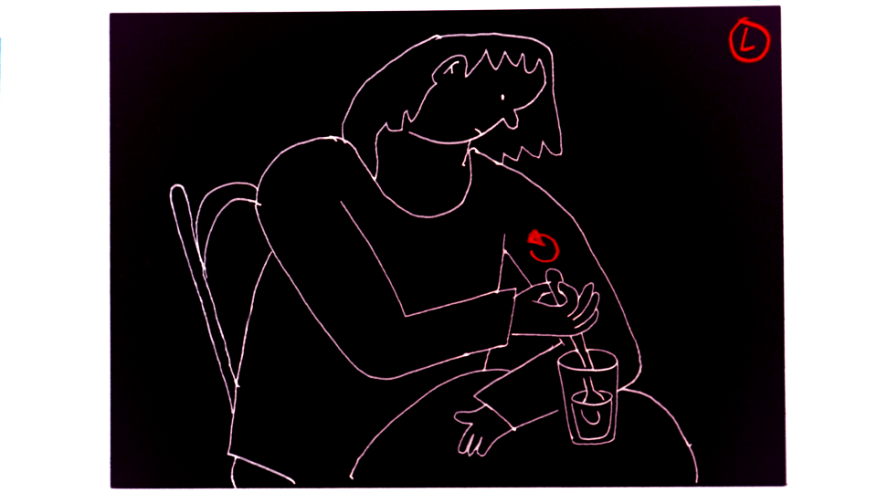
[picture p153: contenu/img/storyboard/020.png]

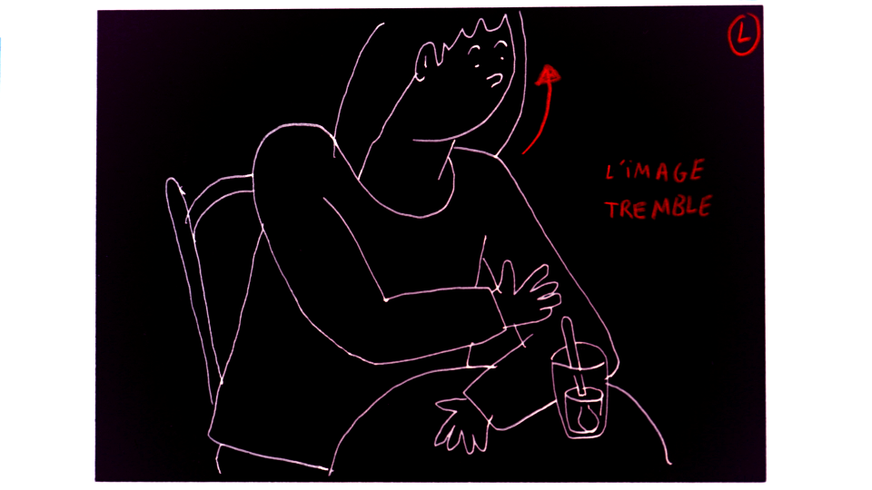
[picture p154: contenu/img/storyboard/021.png]

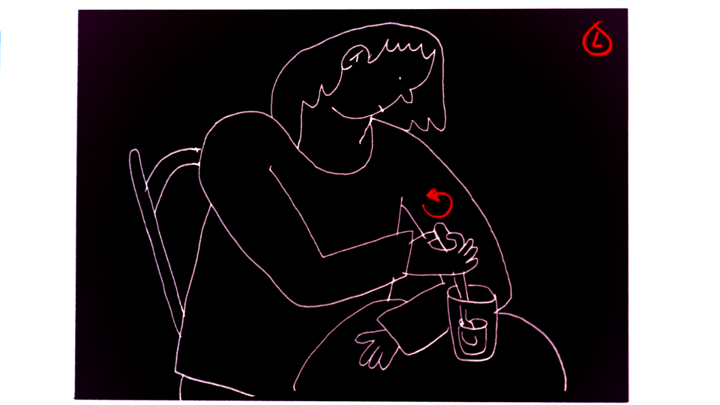
[picture p155: contenu/img/storyboard/022.png]

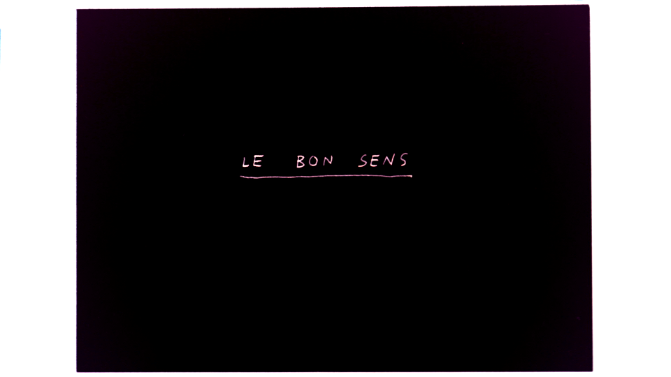
[picture p156: contenu/img/storyboard/023.png]

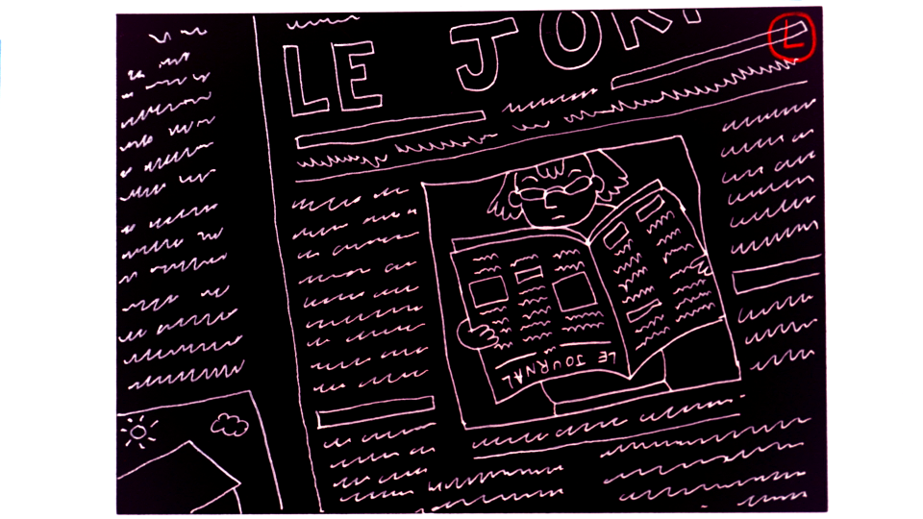
[picture p157: contenu/img/storyboard/024.png]

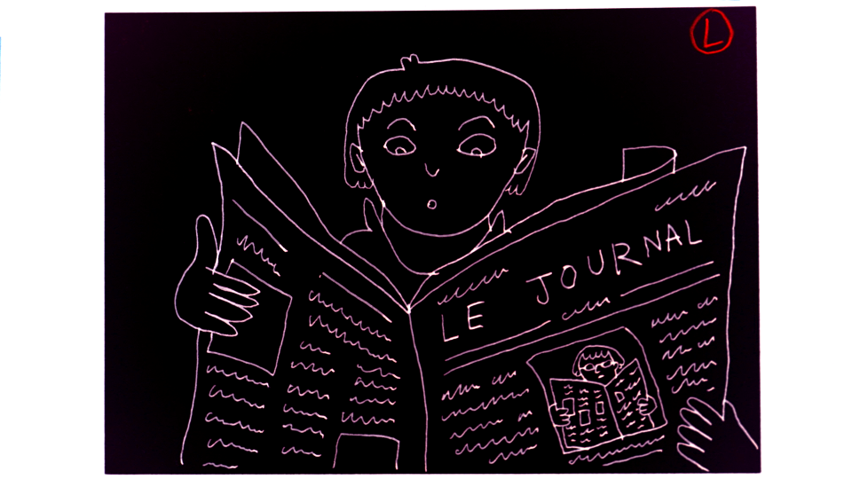
[picture p158: contenu/img/storyboard/025.png]

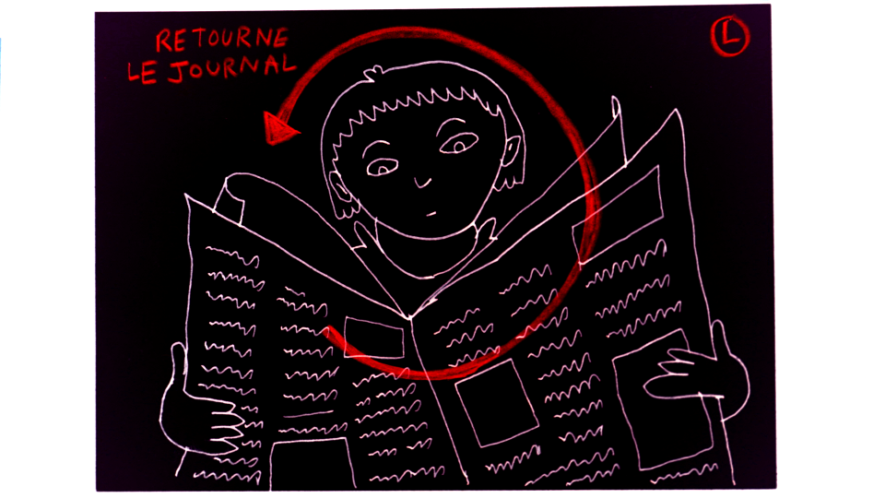
[picture p159: contenu/img/storyboard/026.png]

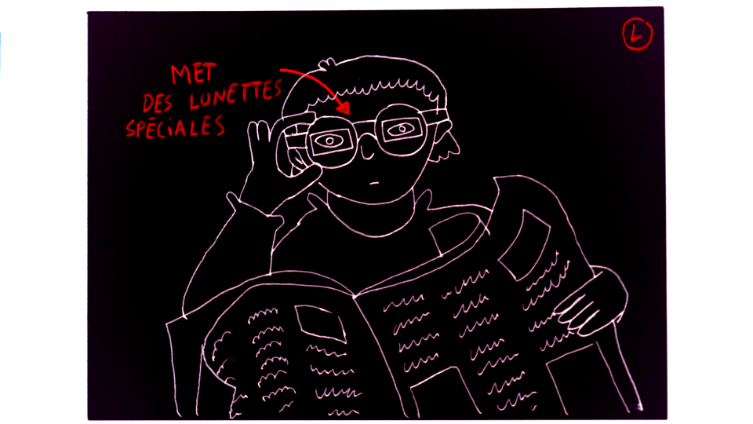
[picture p160: contenu/img/storyboard/027.png]

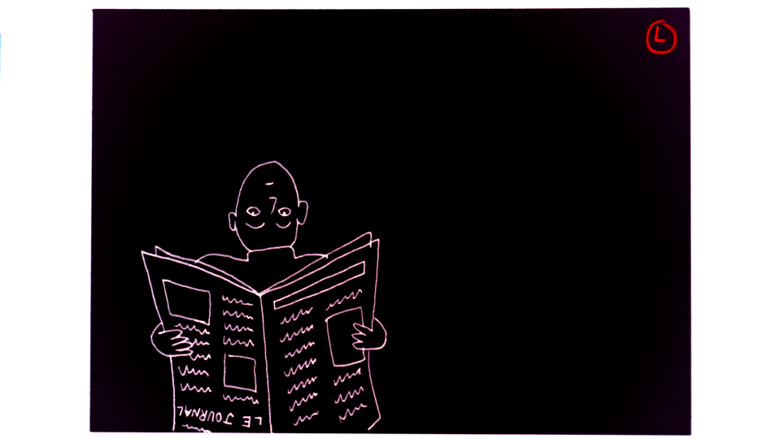
[picture p161: contenu/img/storyboard/028.png]

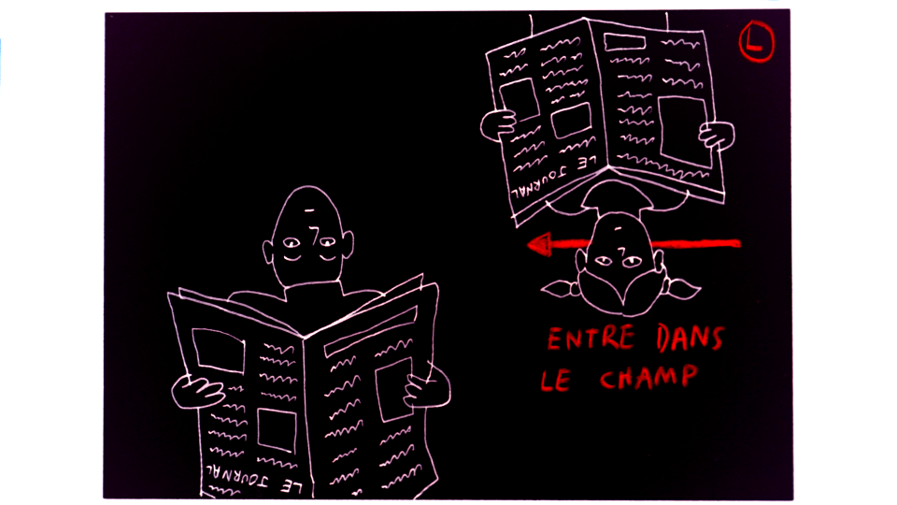
[picture p162: contenu/img/storyboard/029.png]

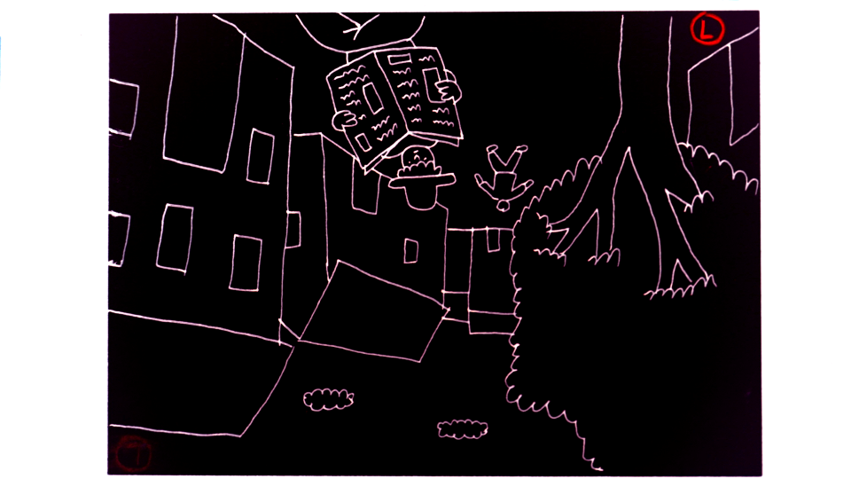
[picture p163: contenu/img/storyboard/030.png]

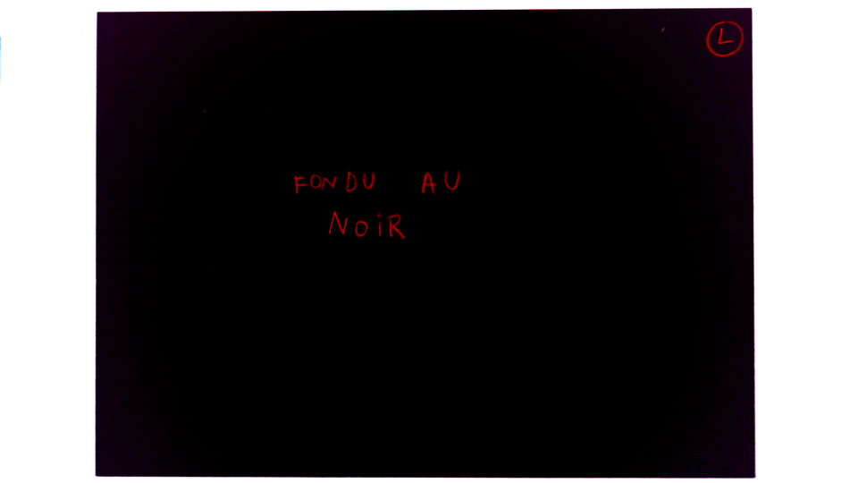
[picture p164: contenu/img/storyboard/031.png]

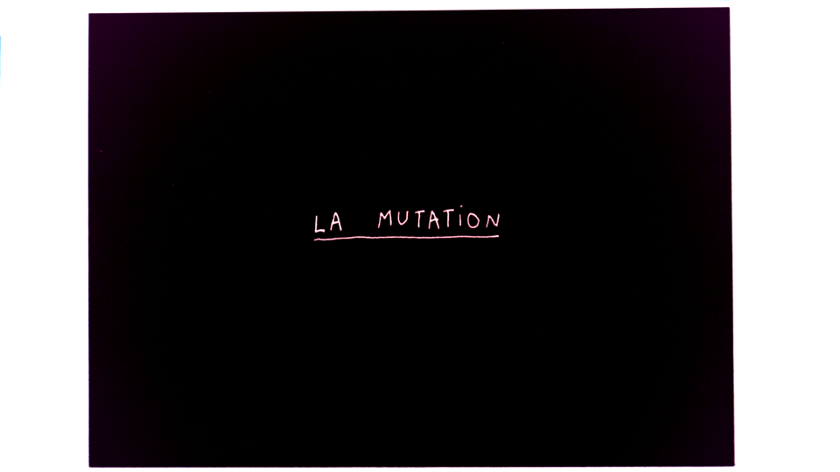
[picture p165: contenu/img/storyboard/032.png]

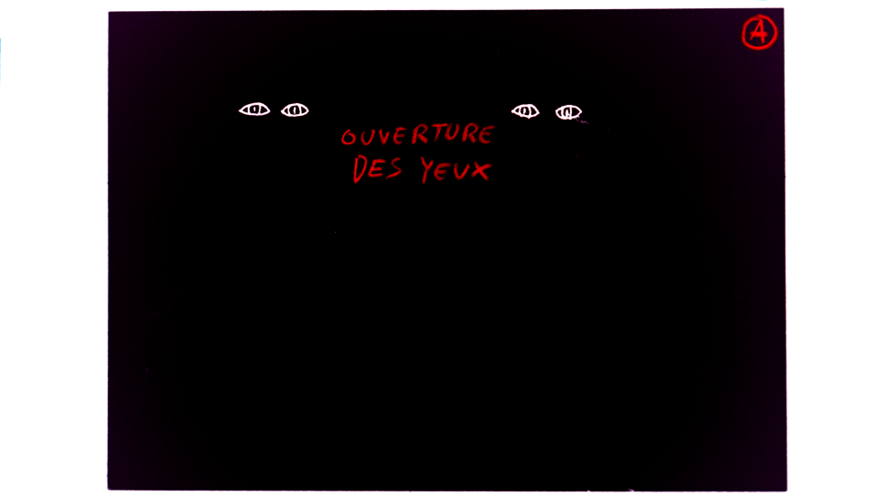
[picture p166: contenu/img/storyboard/033.png]

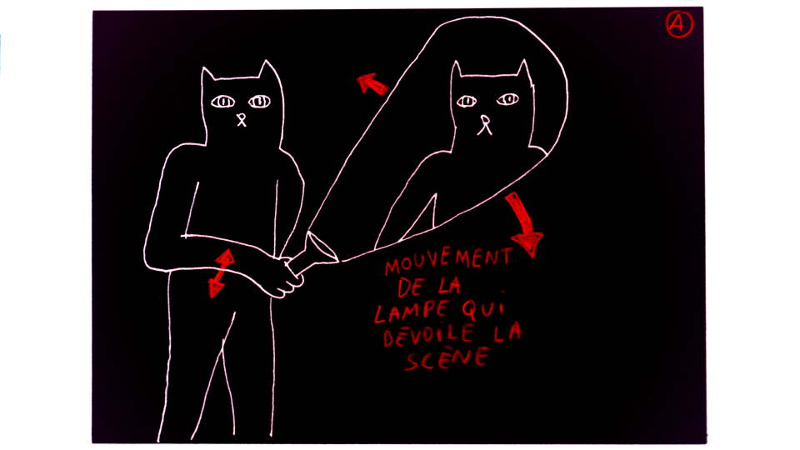
[picture p167: contenu/img/storyboard/034.png]

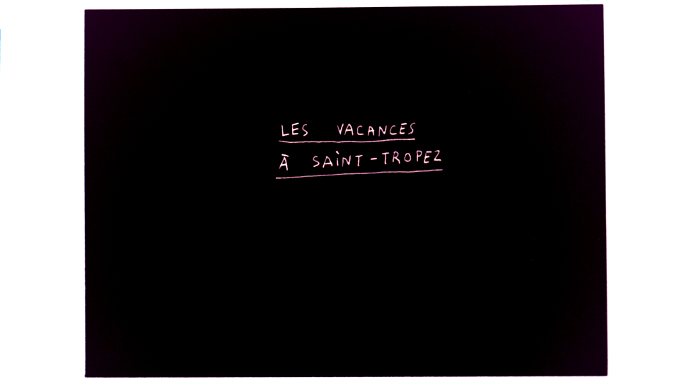
[picture p168: contenu/img/storyboard/035.png]

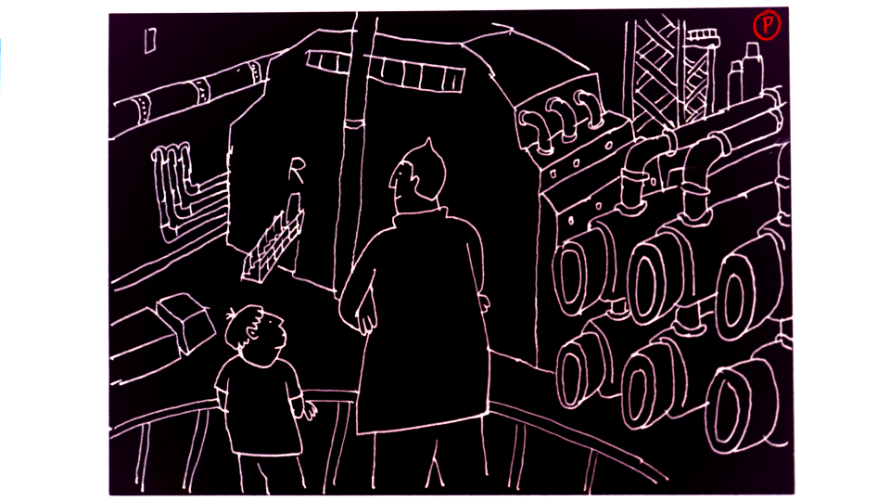
[picture p169: contenu/img/storyboard/036.png]

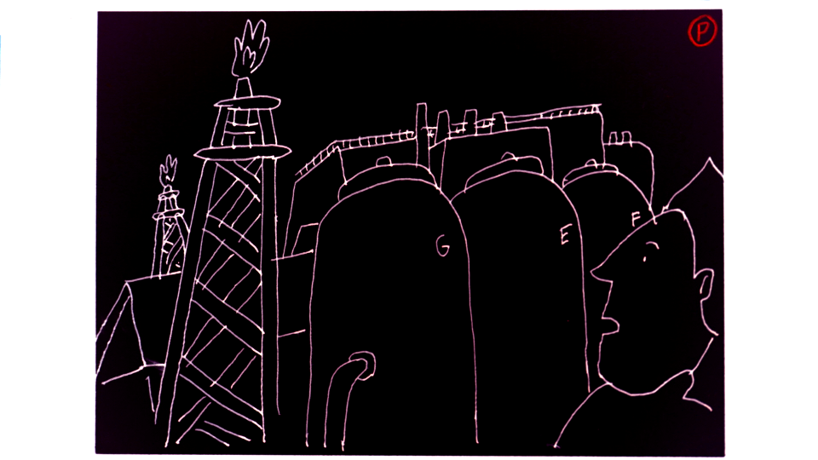
[picture p170: contenu/img/storyboard/037.png]

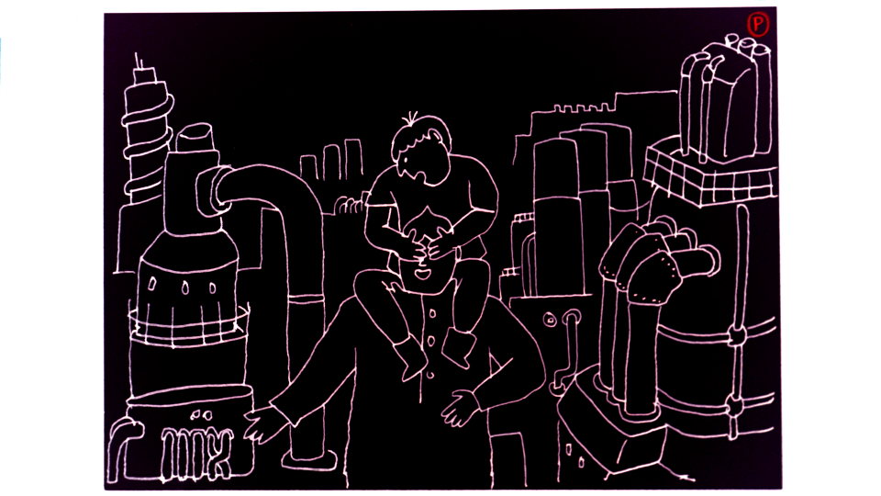
[picture p171: contenu/img/storyboard/038.png]

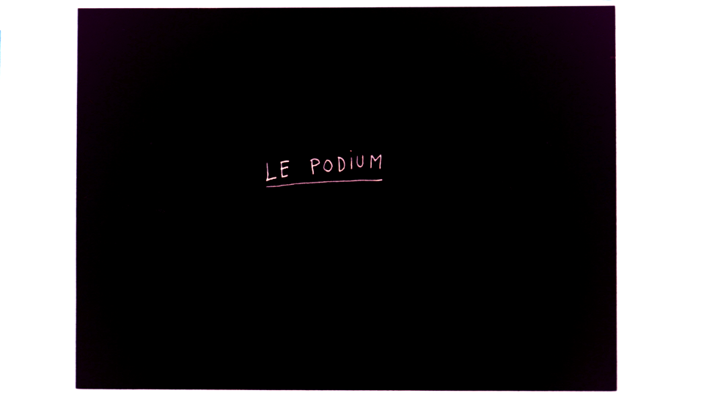
[picture p172: contenu/img/storyboard/039.png]

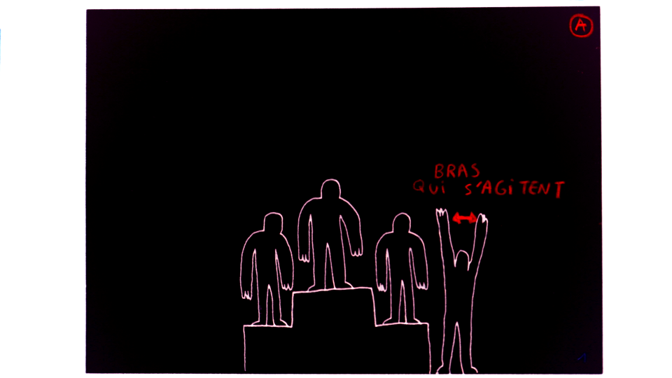
[picture p173: contenu/img/storyboard/040.png]

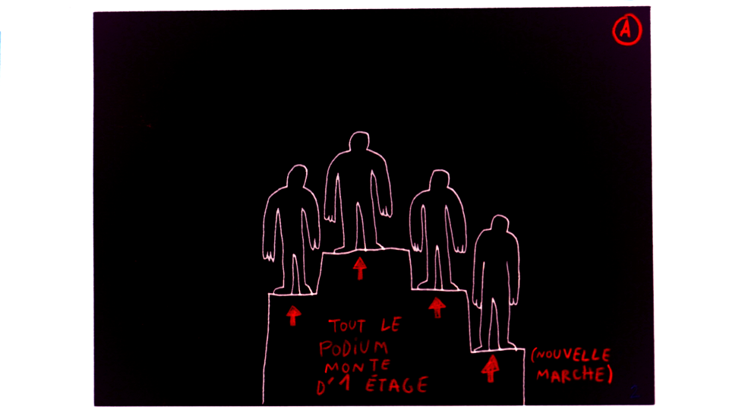
[picture p174: contenu/img/storyboard/041.png]

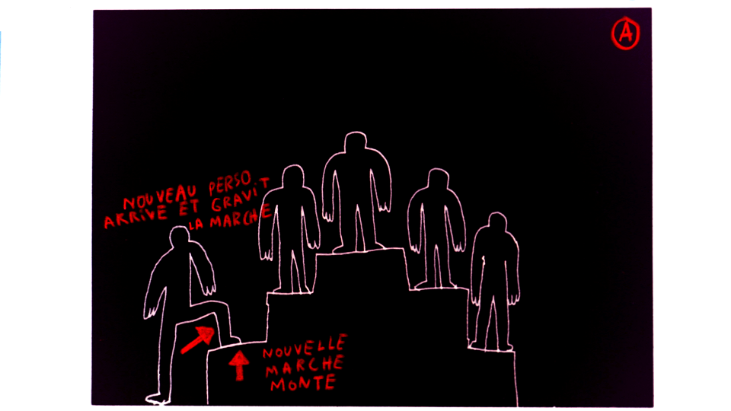
[picture p175: contenu/img/storyboard/042.png]

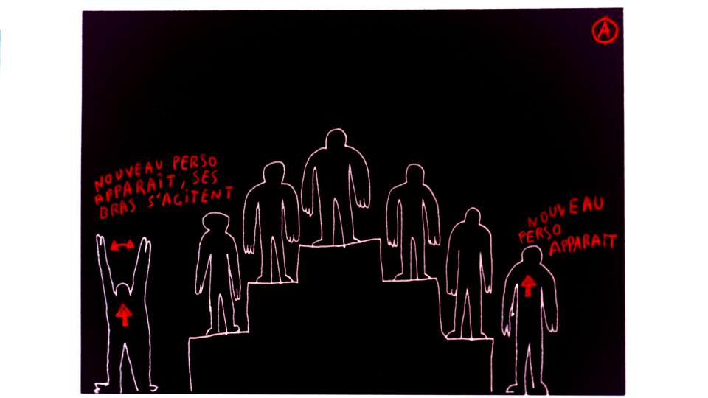
[picture p176: contenu/img/storyboard/043.png]

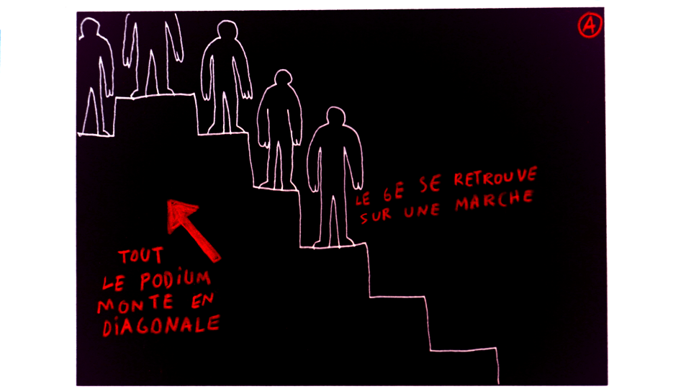
[picture p177: contenu/img/storyboard/044.png]

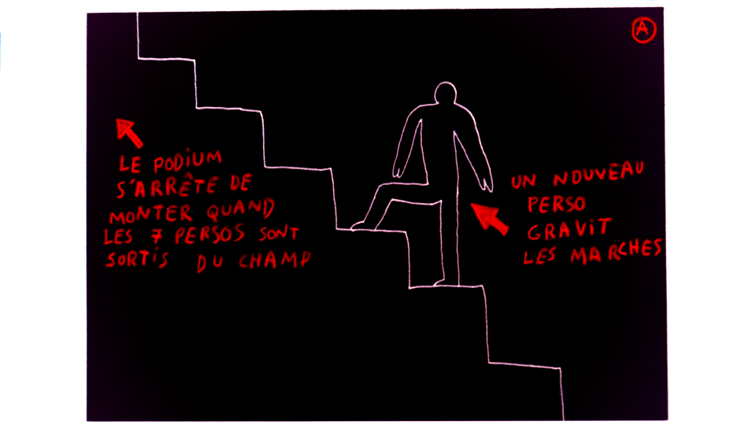
[picture p178: contenu/img/storyboard/045.png]

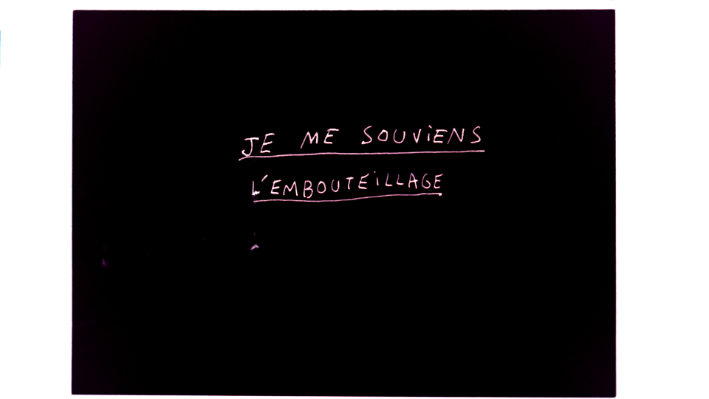
[picture p179: contenu/img/storyboard/046.png]

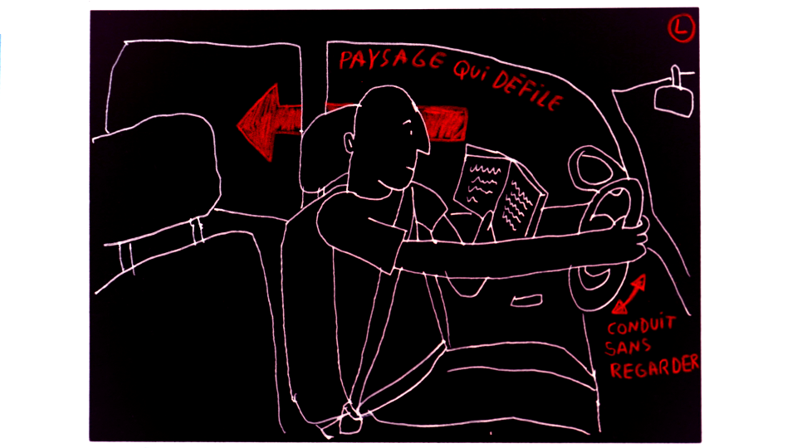
[picture p180: contenu/img/storyboard/047.png]

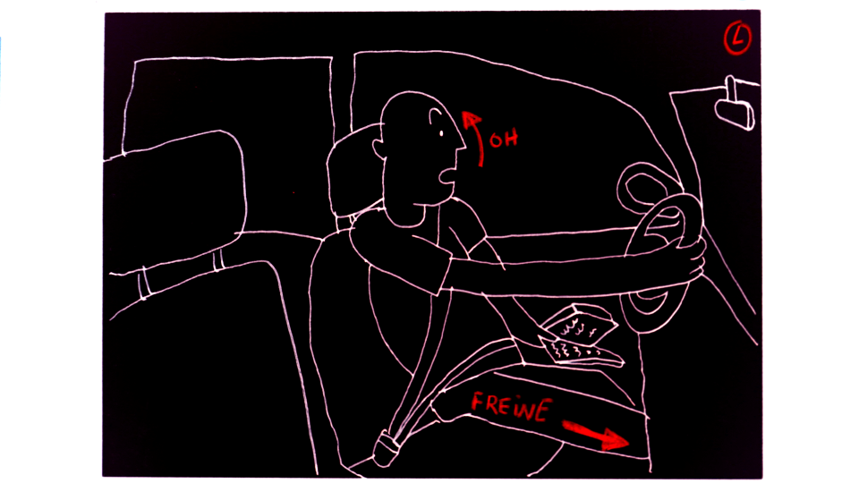
[picture p181: contenu/img/storyboard/048.png]

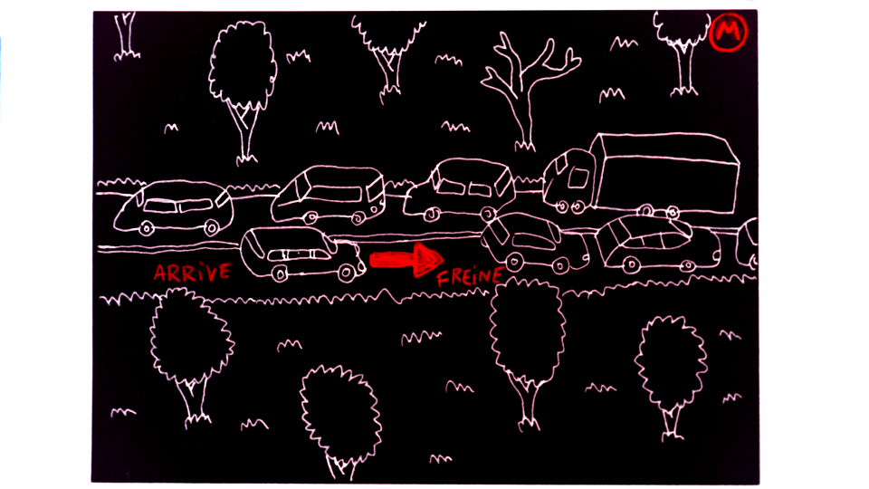
[picture p182: contenu/img/storyboard/049.png]

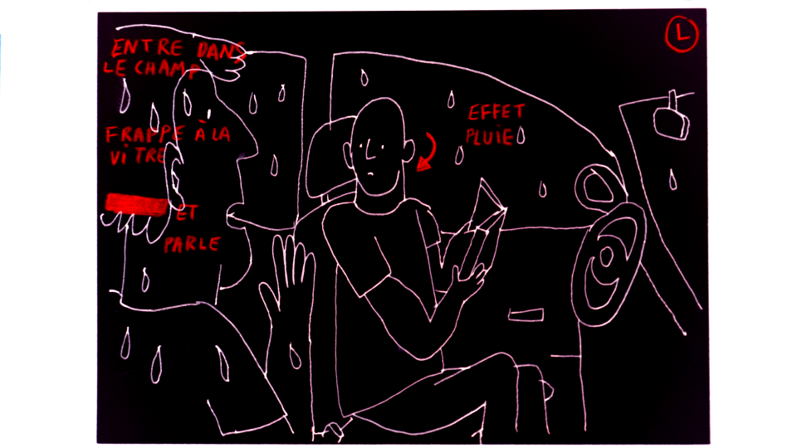
[picture p183: contenu/img/storyboard/050.png]

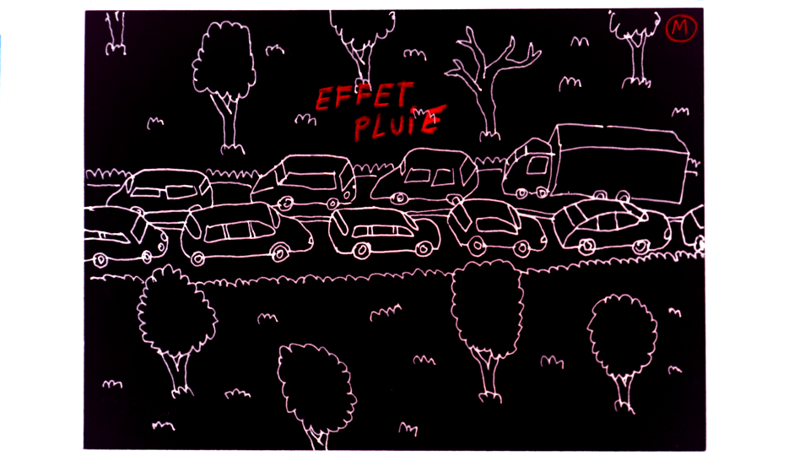
[picture p184: contenu/img/storyboard/051.png]

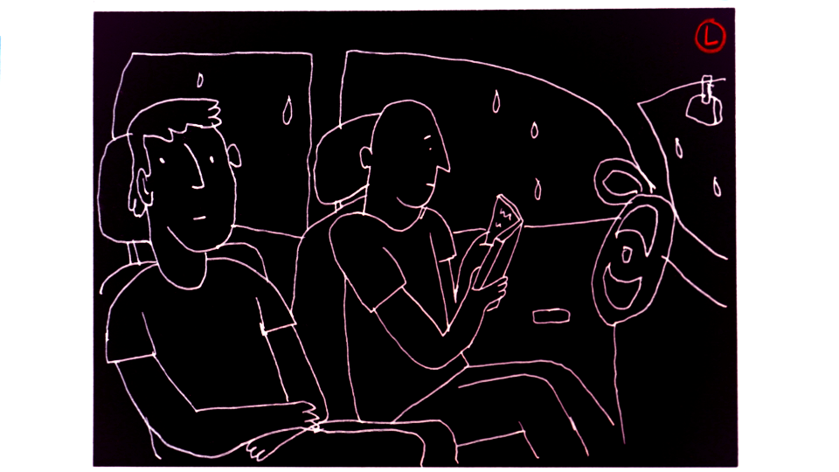
[picture p185: contenu/img/storyboard/052.png]

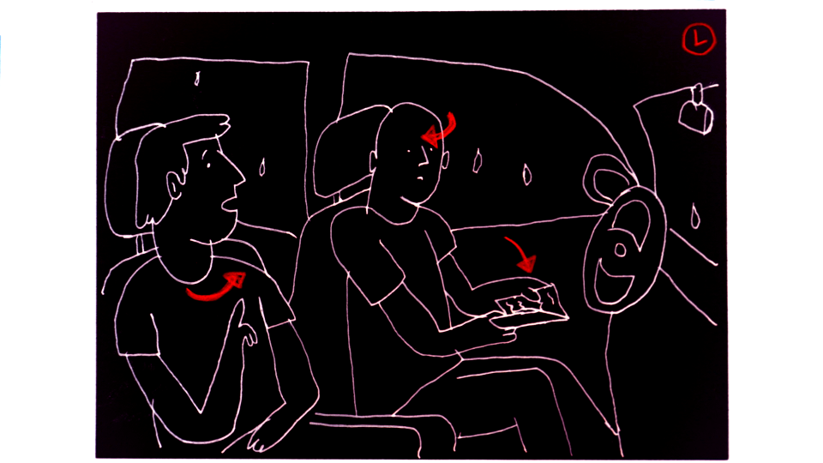
[picture p186: contenu/img/storyboard/053.png]

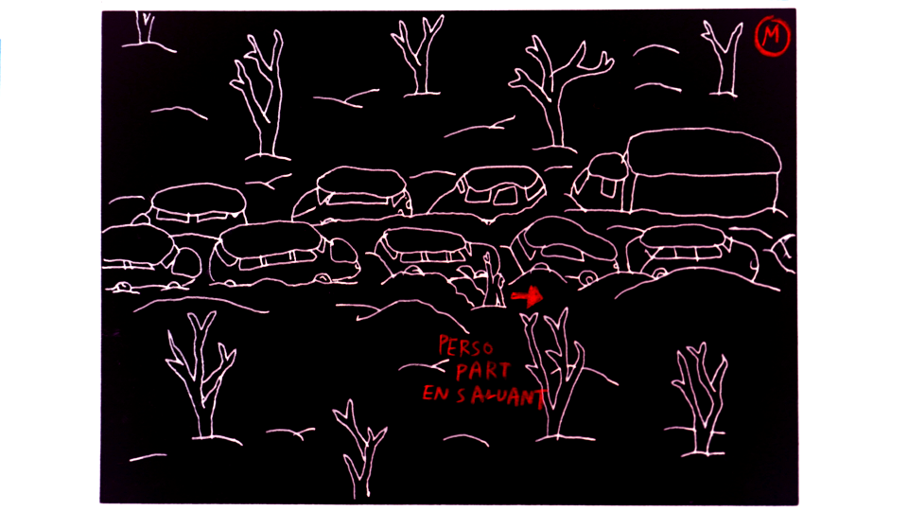
[picture p187: contenu/img/storyboard/054.png]

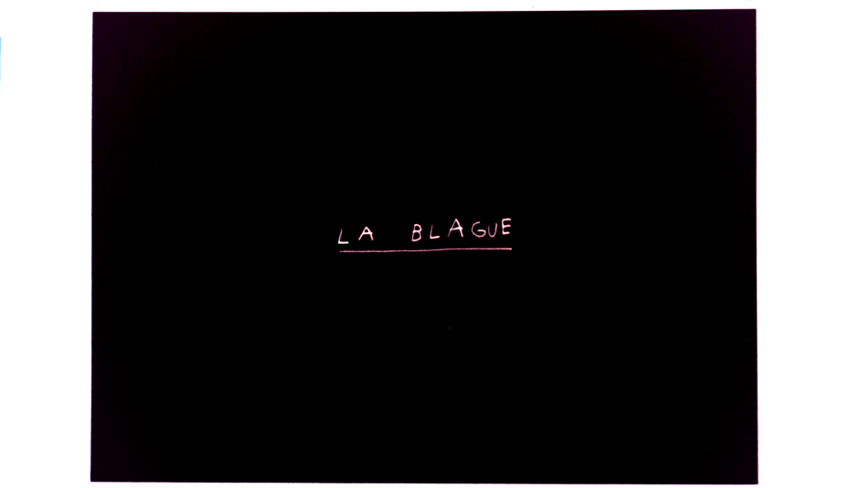
[picture p188: contenu/img/storyboard/055.png]

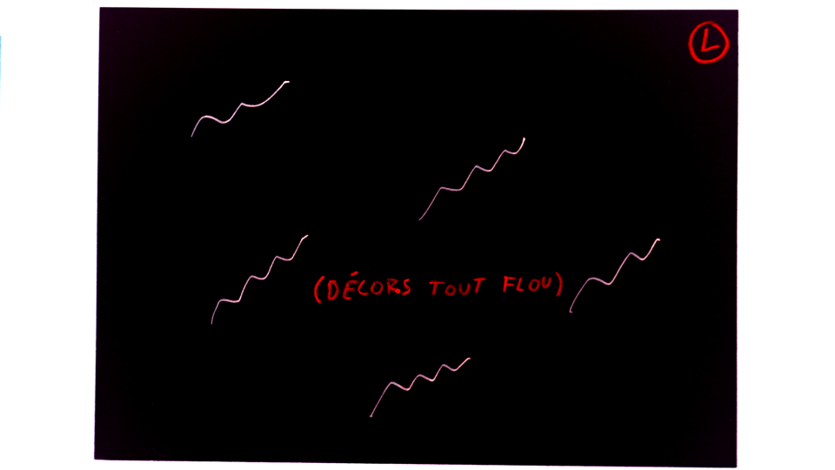
[picture p189: contenu/img/storyboard/056.png]

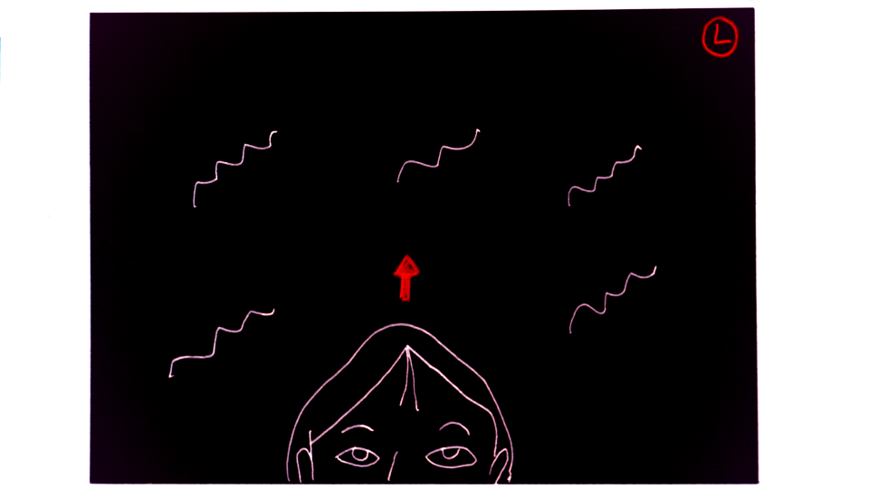
[picture p190: contenu/img/storyboard/057.png]

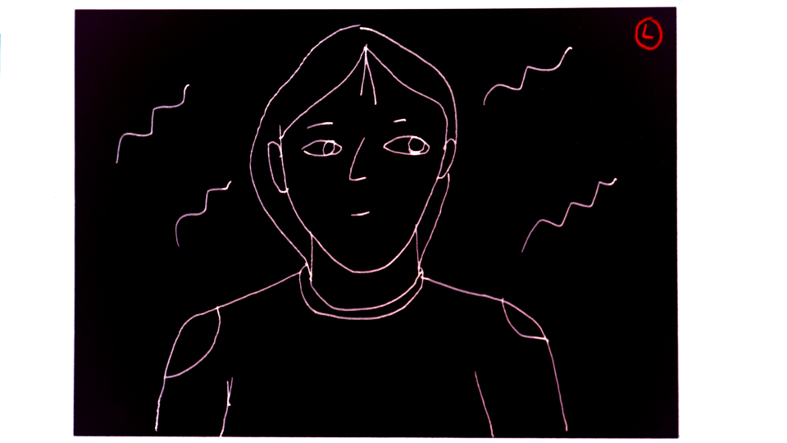
[picture p191: contenu/img/storyboard/058.png]

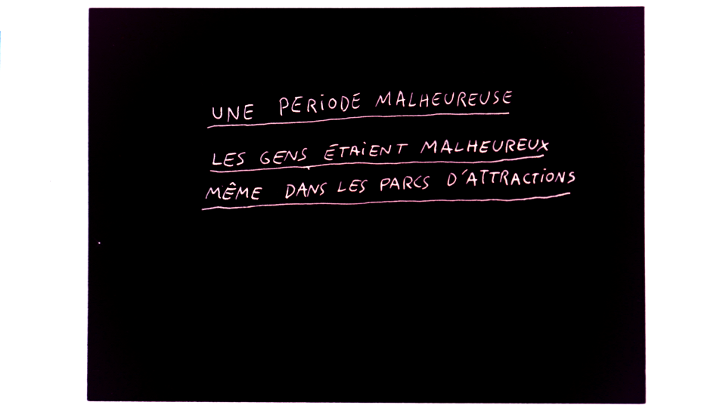
[picture p192: contenu/img/storyboard/059.png]

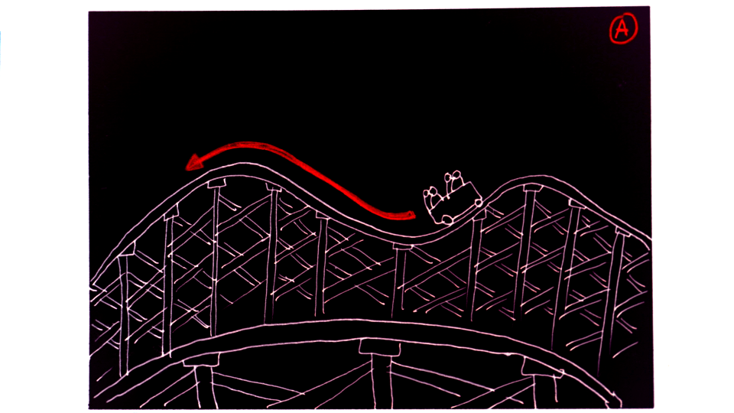
[picture p193: contenu/img/storyboard/060.png]

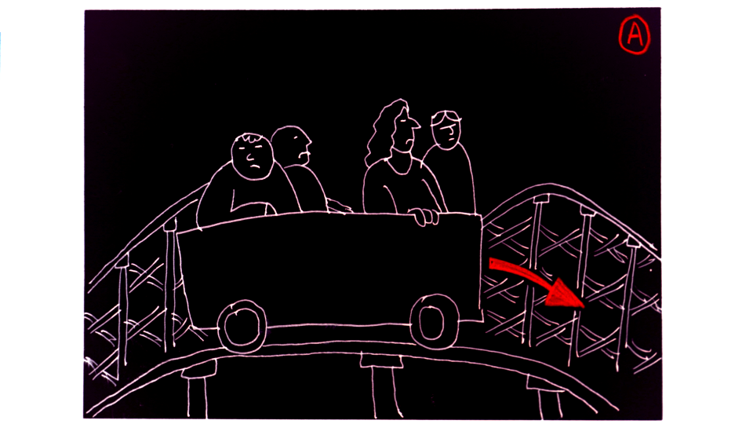
[picture p194: contenu/img/storyboard/061.png]

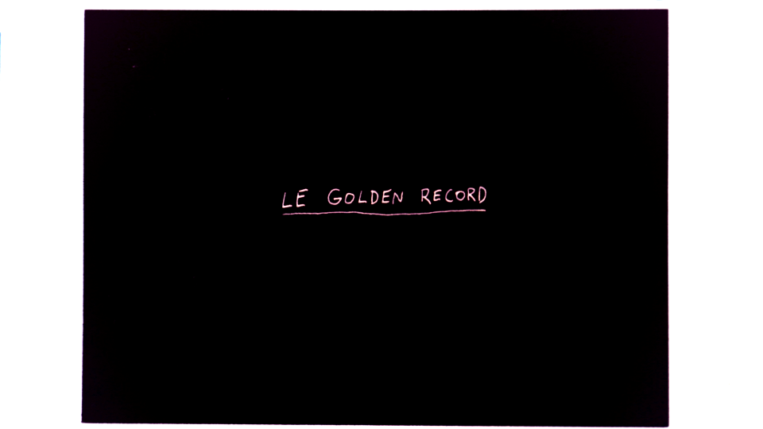
[picture p195: contenu/img/storyboard/062.png]

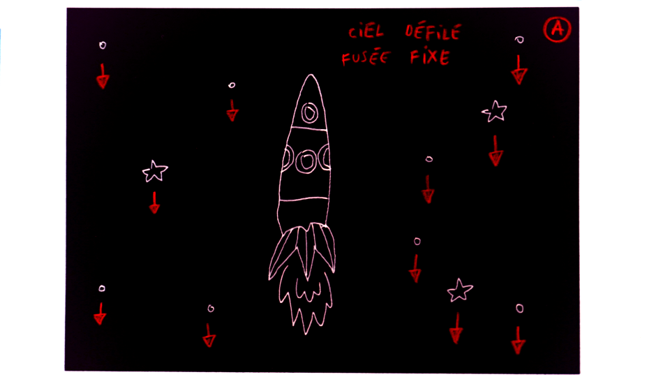
[picture p196: contenu/img/storyboard/063.png]

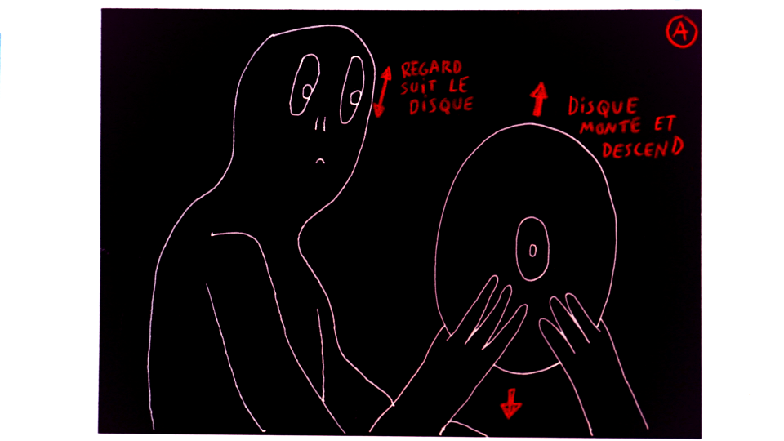
[picture p197: contenu/img/storyboard/064.png]

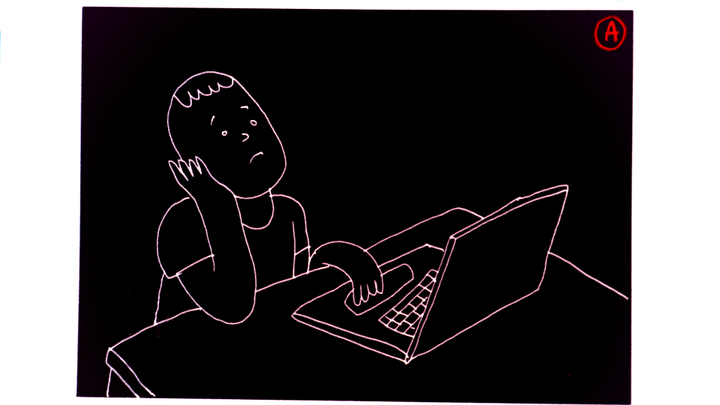
[picture p198: contenu/img/storyboard/065.png]

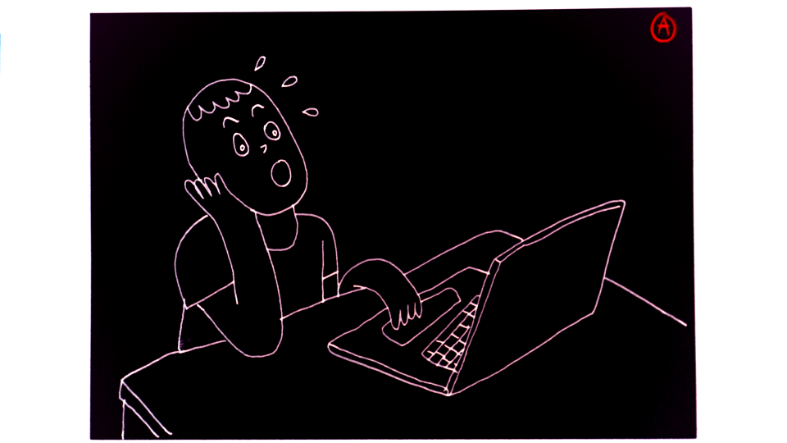
[picture p199: contenu/img/storyboard/066.png]

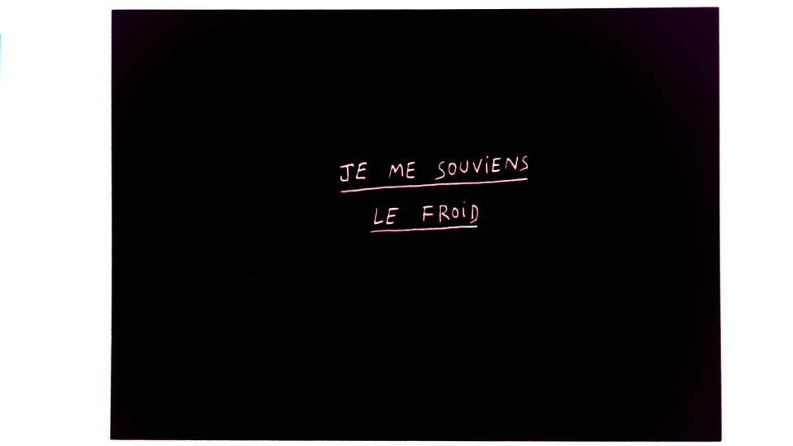
[picture p200: contenu/img/storyboard/067.png]

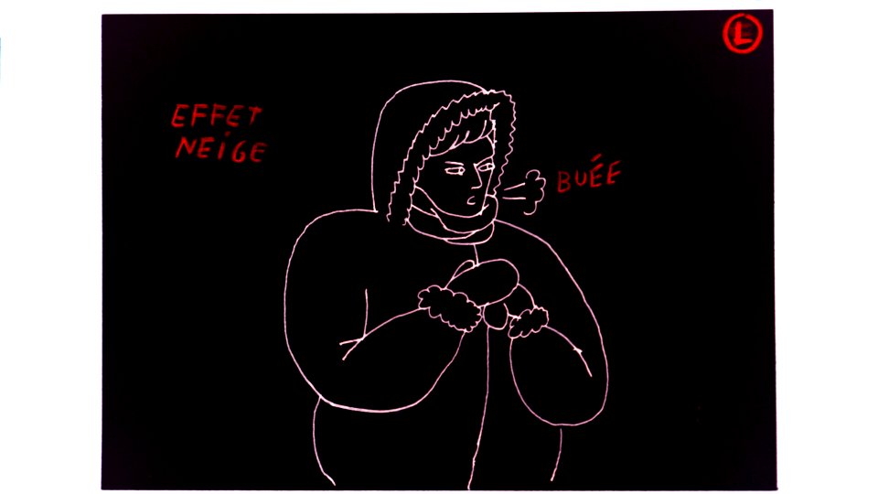
[picture p201: contenu/img/storyboard/068.png]

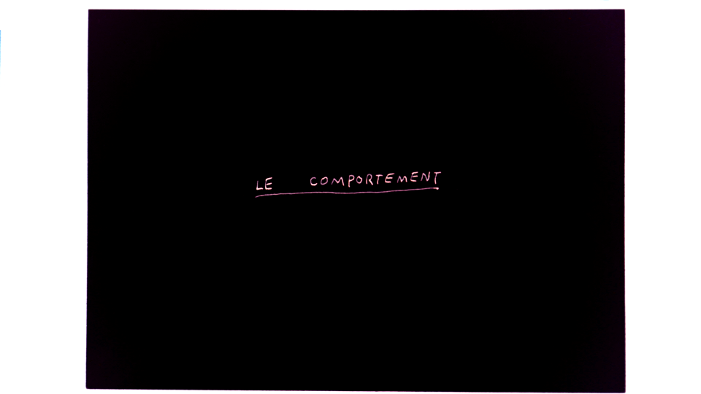
[picture p202: contenu/img/storyboard/069.png]

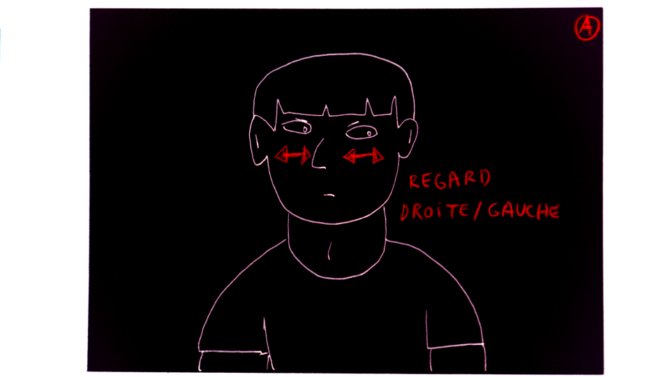
[picture p203: contenu/img/storyboard/070.png]

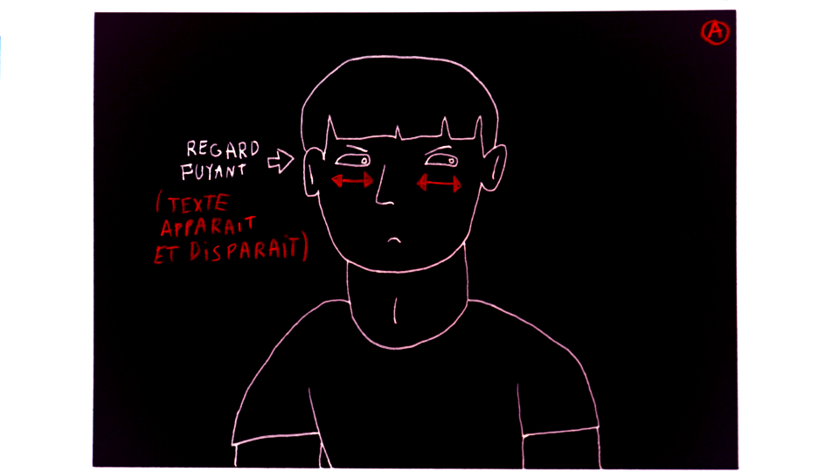
[picture p204: contenu/img/storyboard/071.png]

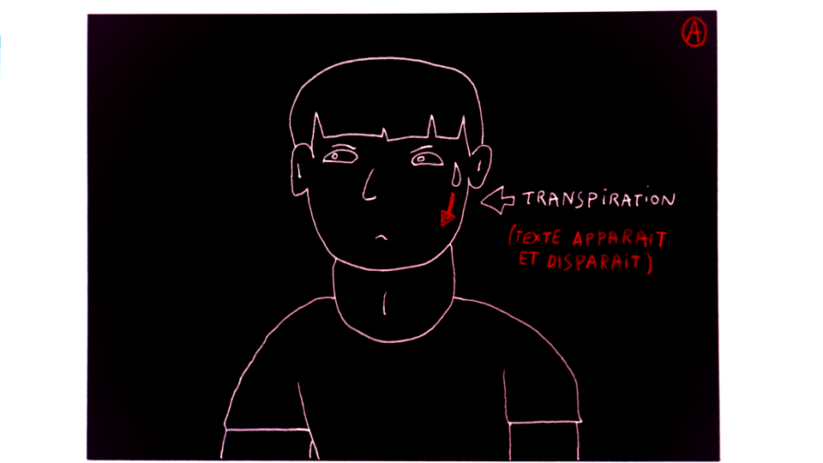
[picture p205: contenu/img/storyboard/072.png]

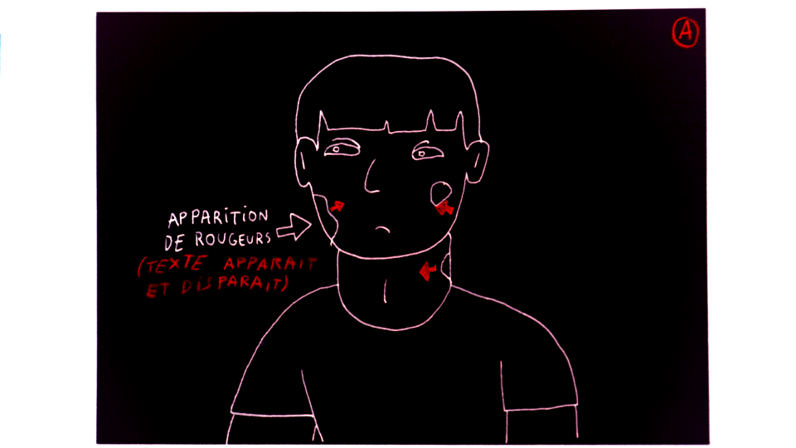
[picture p206: contenu/img/storyboard/073.png]

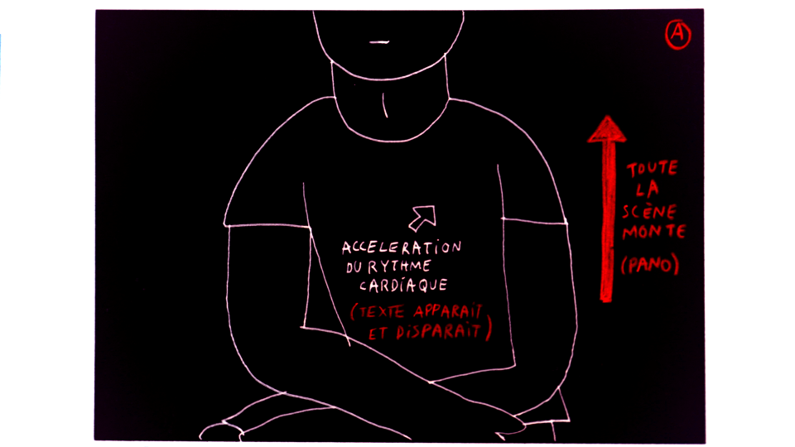
[picture p207: contenu/img/storyboard/074.png]

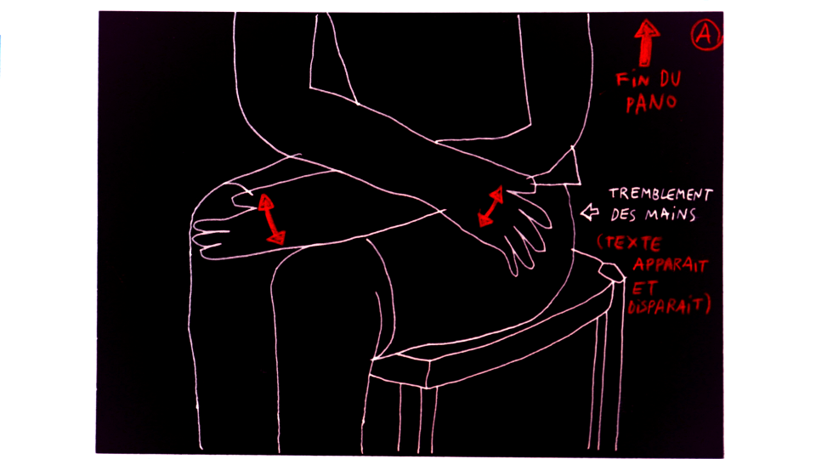
[picture p208: contenu/img/storyboard/075.png]

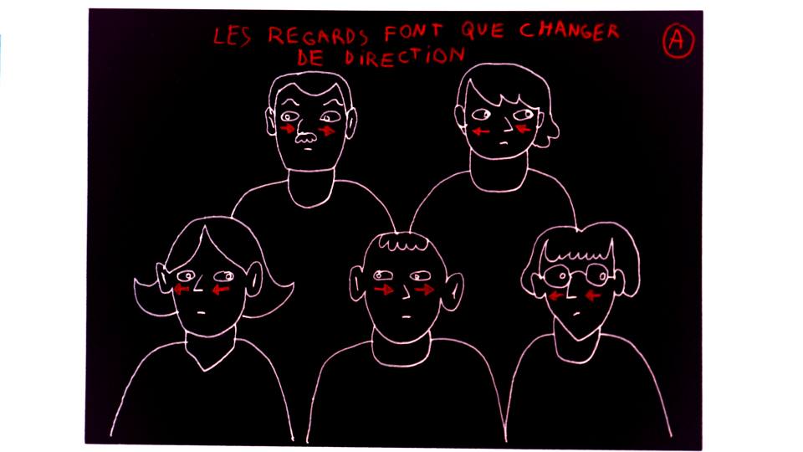
[picture p209: contenu/img/storyboard/076.png]

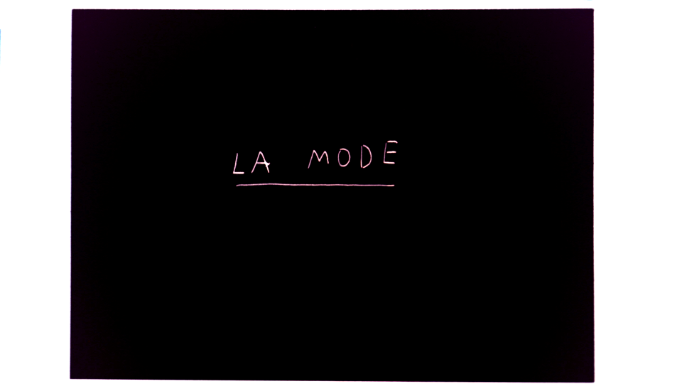
[picture p210: contenu/img/storyboard/077.png]

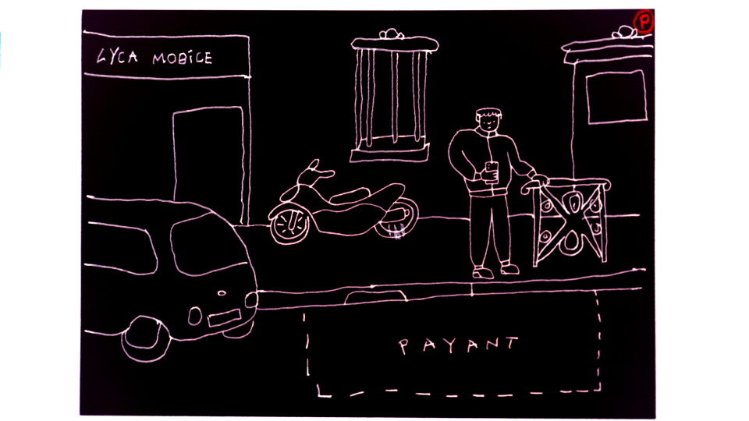
[picture p211: contenu/img/storyboard/078.png]

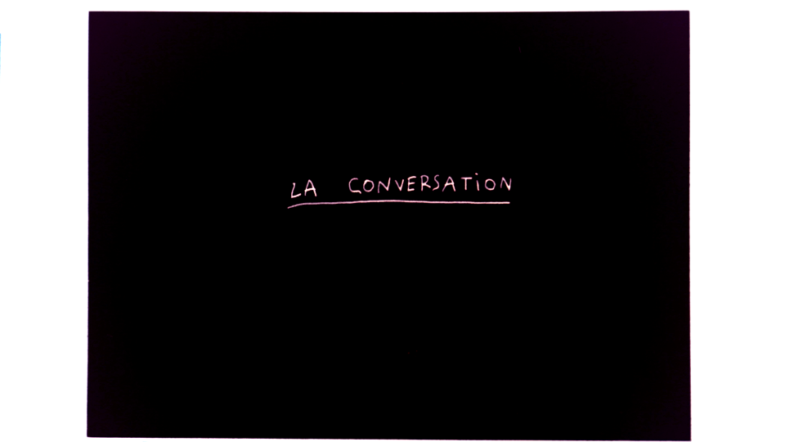
[picture p212: contenu/img/storyboard/079.png]

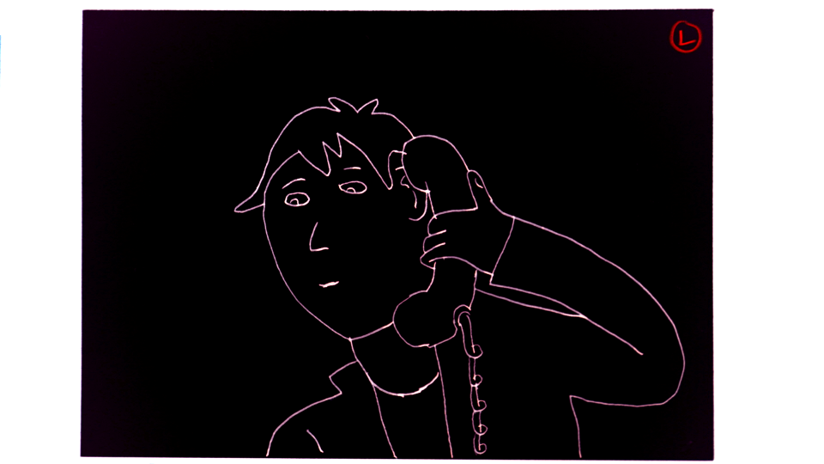
[picture p213: contenu/img/storyboard/080.png]

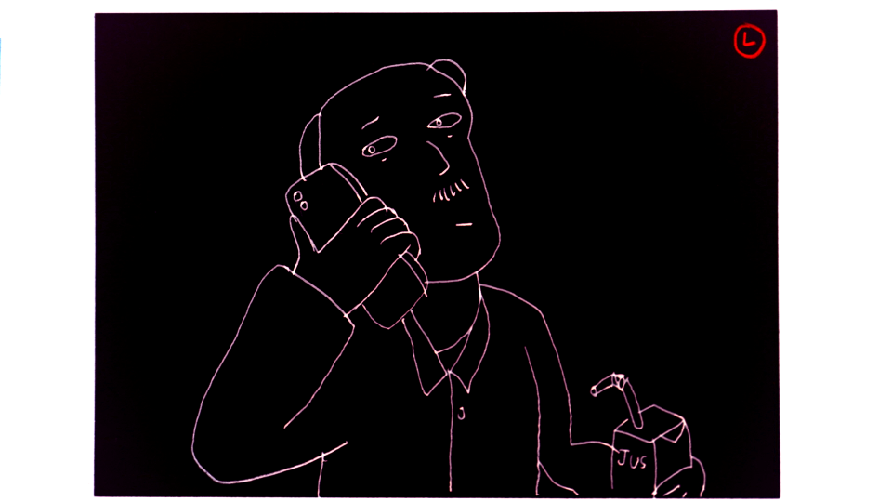
[picture p214: contenu/img/storyboard/081.png]

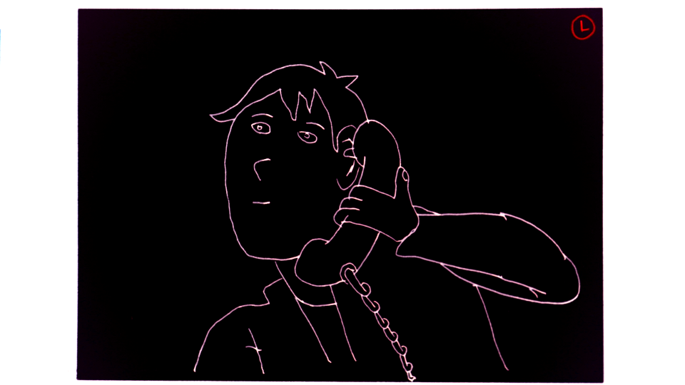
[picture p215: contenu/img/storyboard/082.png]

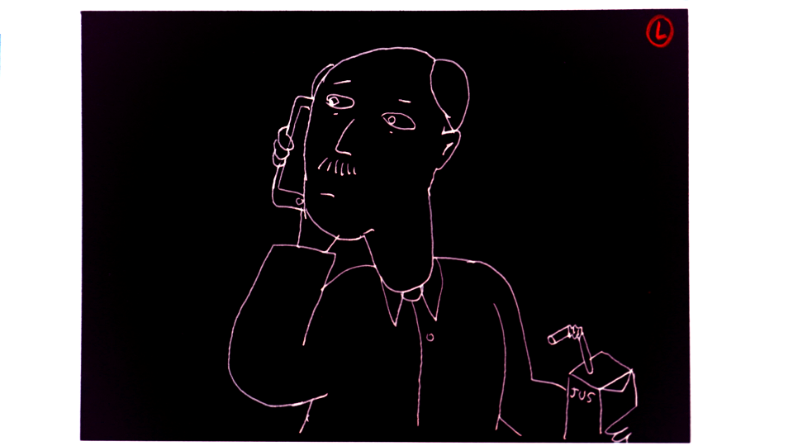
[picture p216: contenu/img/storyboard/083.png]

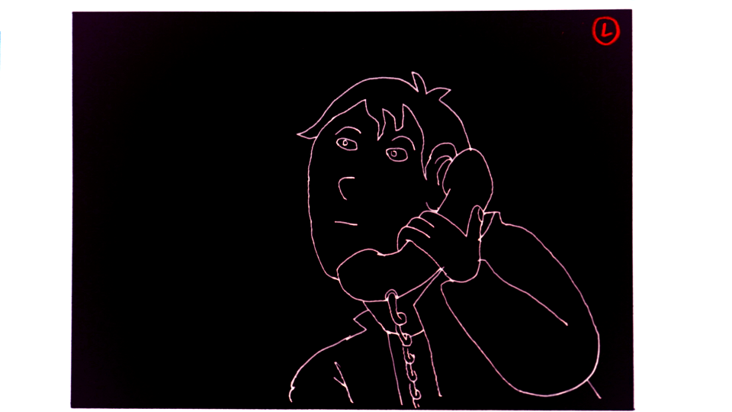
[picture p217: contenu/img/storyboard/084.png]

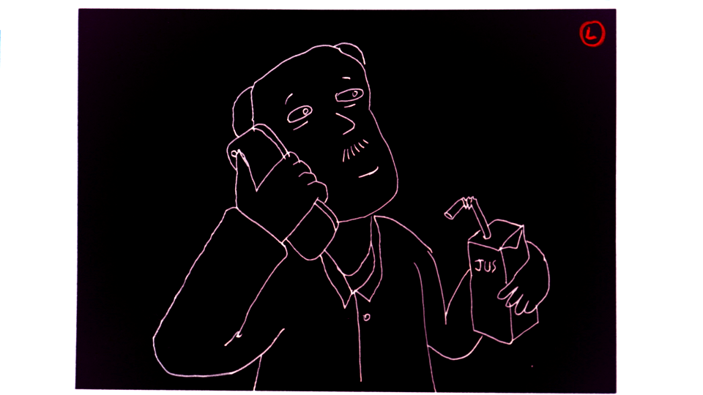
[picture p218: contenu/img/storyboard/085.png]

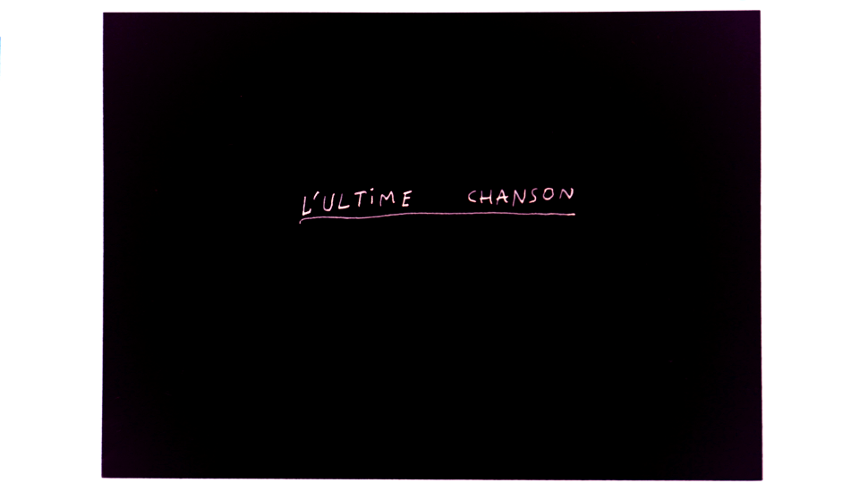
[picture p219: contenu/img/storyboard/086.png]

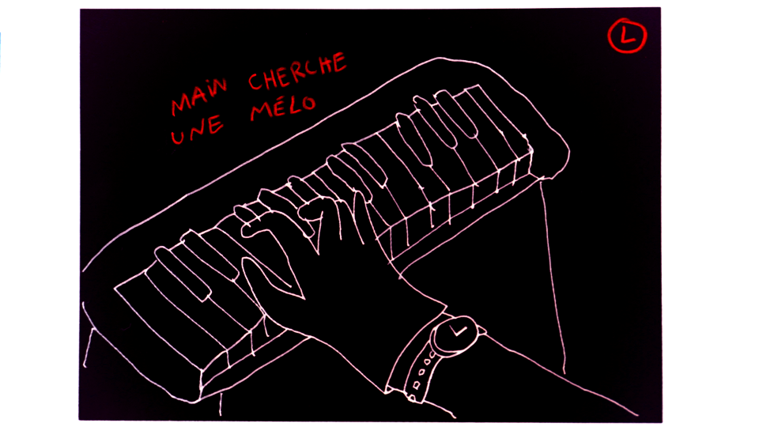
[picture p220: contenu/img/storyboard/087.png]

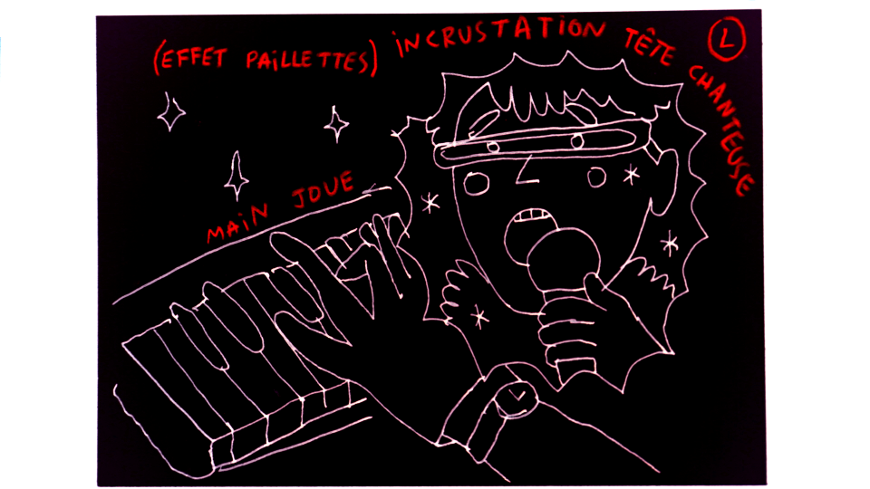
[picture p221: contenu/img/storyboard/088.png]

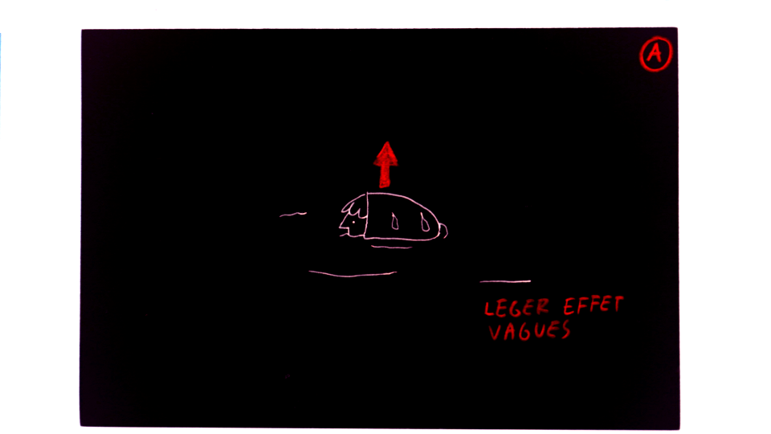
[picture p222: contenu/img/storyboard/089.png]

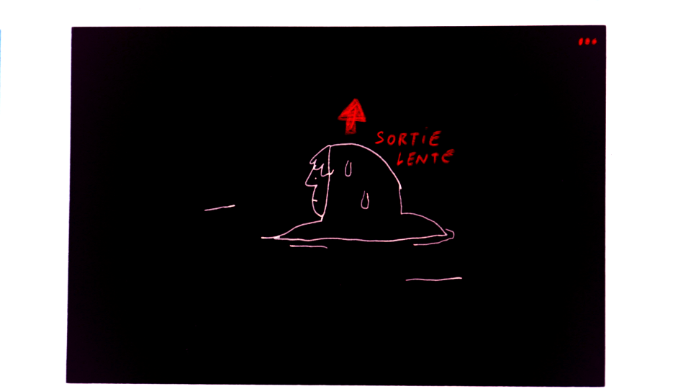
[picture p223: contenu/img/storyboard/090.png]

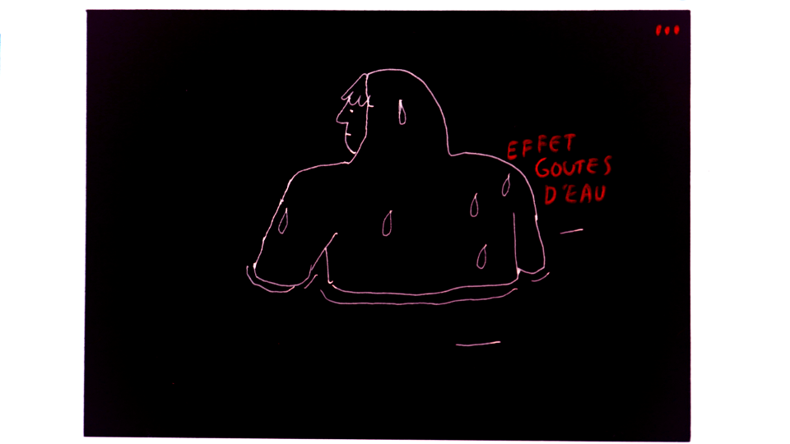
[picture p224: contenu/img/storyboard/091.png]

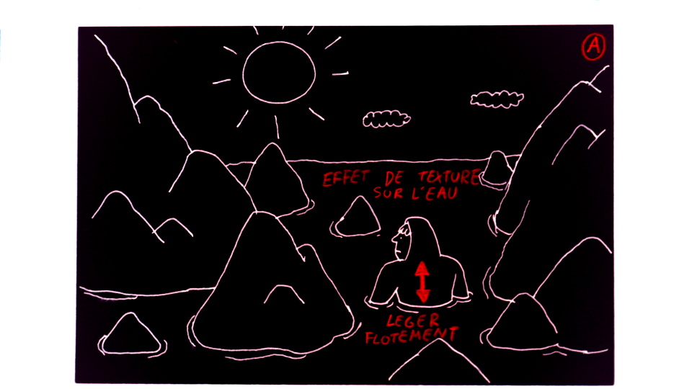
[picture p225: contenu/img/storyboard/092.png]

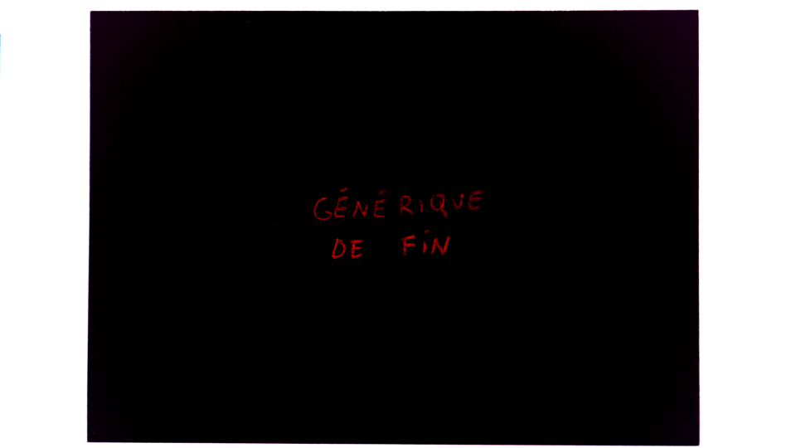
[picture p226: contenu/img/storyboard/093.png]

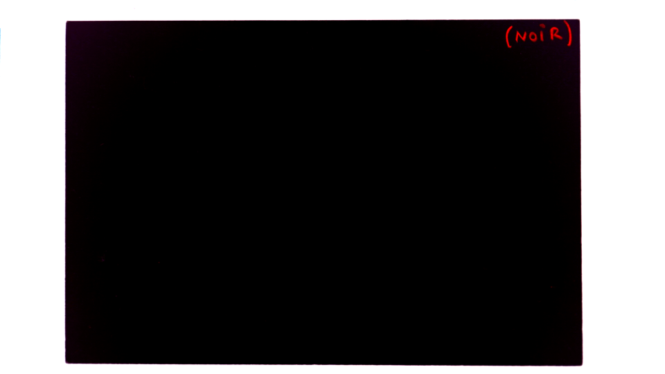
[picture p227: contenu/img/storyboard/094.png]
