LeonLenclos/camera-obscura/contenu/ecriture/jeuimpro.md

# Jeu d'impro

Placer la caméra dans l'espace public, faire un plan large avec beaucoup de passants.

Faire des séries d'impro sous la forme : "La personne que vous voyez là bas, [position dans le cadre ou dans le décors], [description physique ou de l'action en cours], c'est moi. Je suis [situation du quotidien ou dans la vie / état d'ésprit / état d'âme]"

Par exemple : "La personne que vous voyez là-bas, devant le platane, avec des cheveux blancs, des lunettes de soleil et deux sacs de courses, c'est moi. Je viens de remarquer un objet étrange sur la place, je pense que c'est une caméra. Vraiment ils en mettent partout en ce moment c'est plus possible. Bientôt ils mettront des cameras dans nos chambres à coucher et on pourra pas dire qu'on l'a pas vu venir."

Possible aussi d'en enchaîner en disant un truc du genre "Non je rigole. C'est pas moi. Moi je suis la personne [...]"
