LeonLenclos/camera-obscura/contenu/img/systeme-optique-besoins-et-variables.pdf

### une image nette

luminosité de l'exterieur
(éclairage de l'objet)

ouverture
(diamètre du trou, de l'objectif ou du diaphragme)

obscurité de l’intérieur
(qualité du noir dans la chambre)

nette partout pareil

demande une petite

plus nette à certains endroits qu'à d'autre utilisation d'un simple trou (sténopé)

requiert

utilisation de lentille

requiert

que la zone où les objets sont nets soit grande (profondeur de champ)

demande une petite

dans ce cas on veut

pouvoir choisir la distance de la zone où les objets sont nets (distance de mise au point)

dans ce cas on veut

taille de l'écran une grande image | dépend de

longueur du fût

demande une petite

utilisation de plusieurs lentilles juxtaposées | Utilisation d'une lentille simple
(objectif)

peut demander une grande

courbure de l'écran

focale de la lentille

en changeant

introduit la notion de

distance entre l'écran et la lentille.

en changeant

utilisation d'un soufflet

pour garantir

réglage permis par

montage de la planchette sur un rail

réglage permis par

plusieurs lentilles de différentes focales montées sur un barillet

réglage permis par

angle de champ

dépend de

dépend de

aberrations optiques

accentue

demande

demande une petite

dépend de

aberration chromatique

astigmatisme

aberration sphérique

courbure de champ

demande

qualité de l'écran

luminosité absolue

dépend de

demande une grande

dépend de

luminosité relative

dépend de

accoutumance rétinienne

dépend de

peut être

ou

ou

peut être

ou | ou

### une image lumineuse

## on veut

coûte cher

Résumé des liens entre nos besoins et les differentes variables d'ajustement.

# Camera Obscura - système optique

Les solutions abandonnées sont dans des cases grisées
