LeonLenclos/camera-obscura/contenu/plans/maquette.pdf

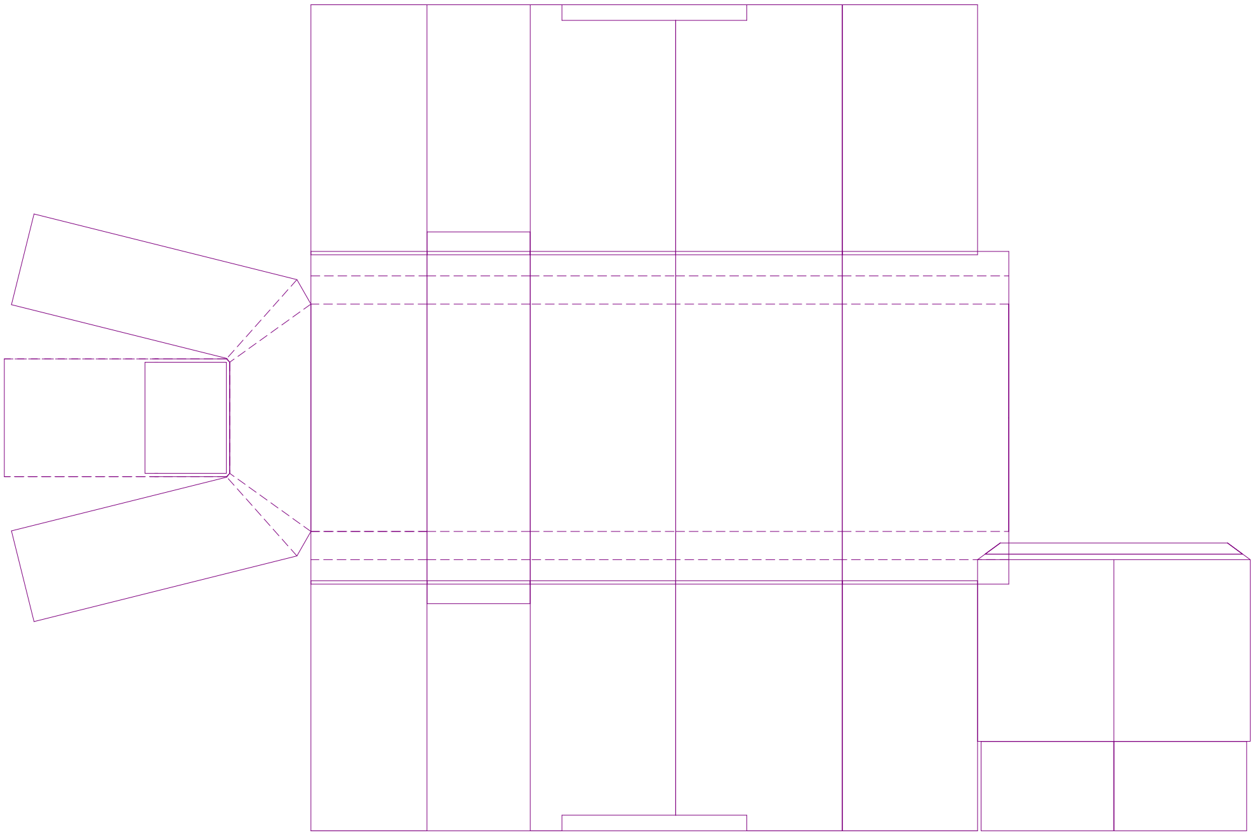
[picture p232: figure]
