LeonLenclos/camera-obscura/contenu/animations/goldenrecord-3-anim.png

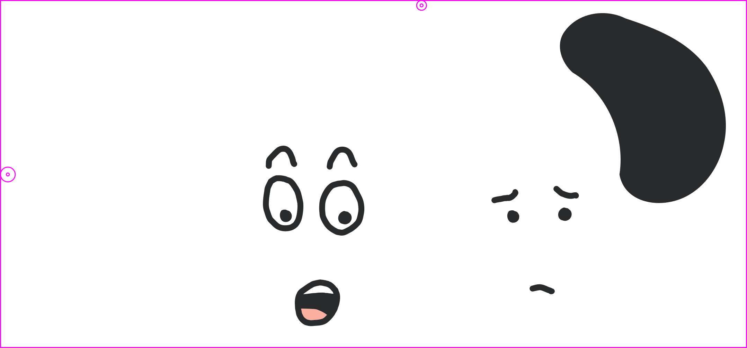
contenu/animations/goldenrecord-3-anim.png
