LeonLenclos/camera-obscura/contenu/animations/goldenrecord-3-fixe.png

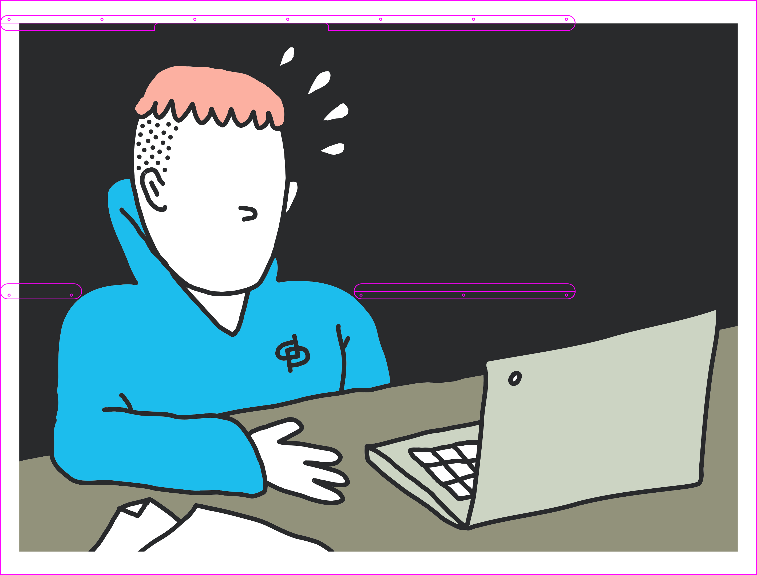
contenu/animations/goldenrecord-3-fixe.png
