LeonLenclos/camera-obscura/contenu/dessins/blav2.jpg

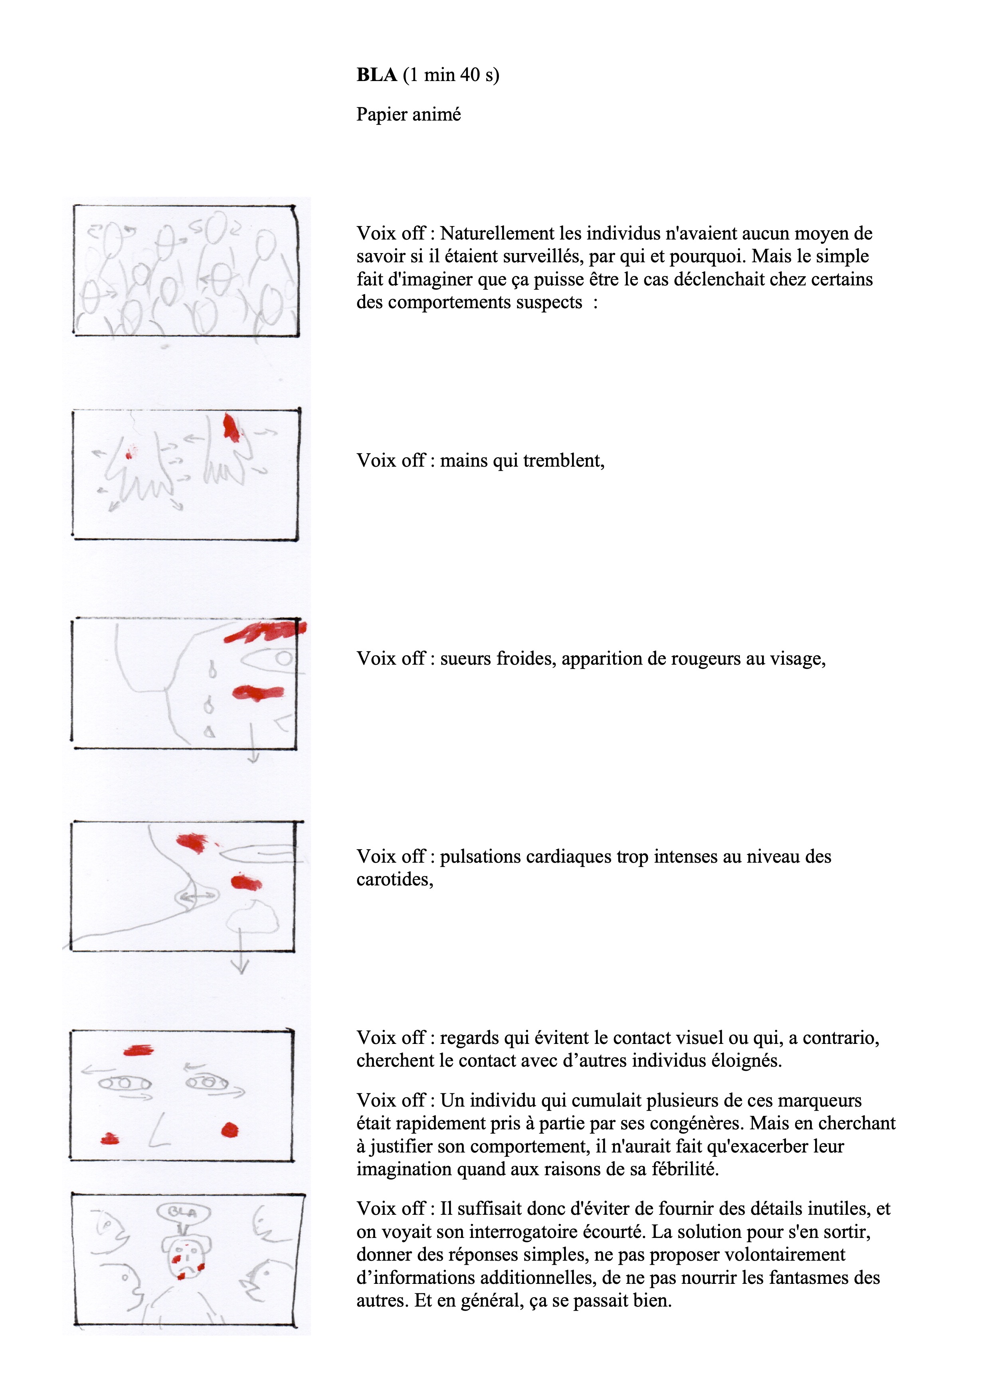
contenu/dessins/blav2.jpg
