LeonLenclos/camera-obscura/contenu/dessins/goldenrecordv1.jpg

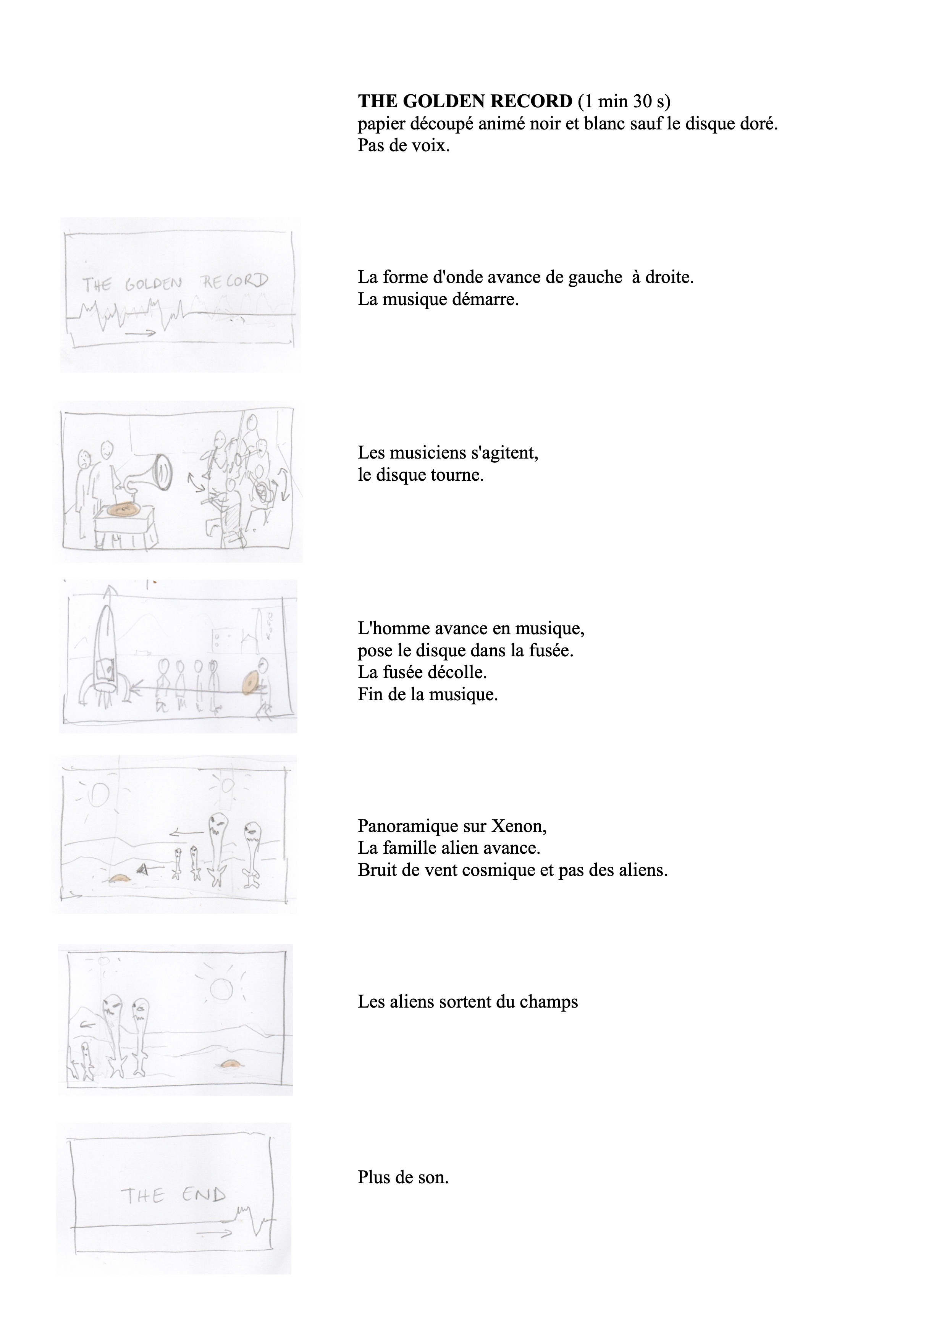
contenu/dessins/goldenrecordv1.jpg
