LeonLenclos/camera-obscura/contenu/img/machinerie_circa.png

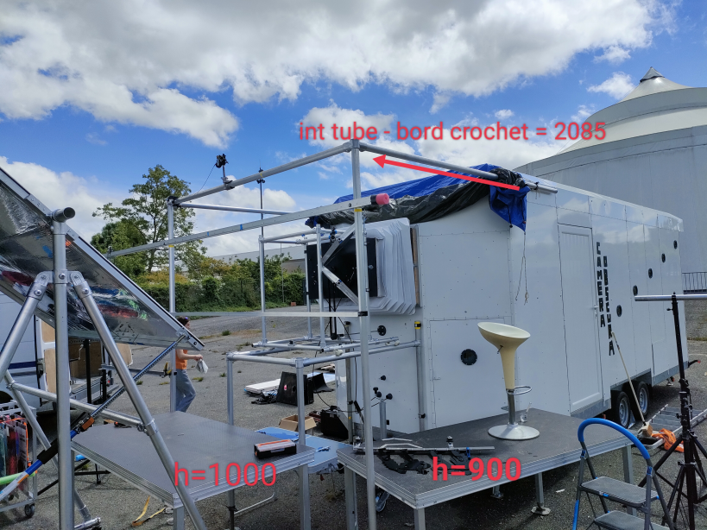
contenu/img/machinerie_circa.png
