LeonLenclos/camera-obscura/contenu/img/typo.gif

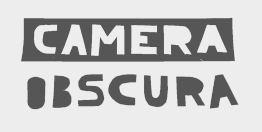
contenu/img/typo.gif
