LeonLenclos/camera-obscura/contenu/objet/billets/bg-1.png

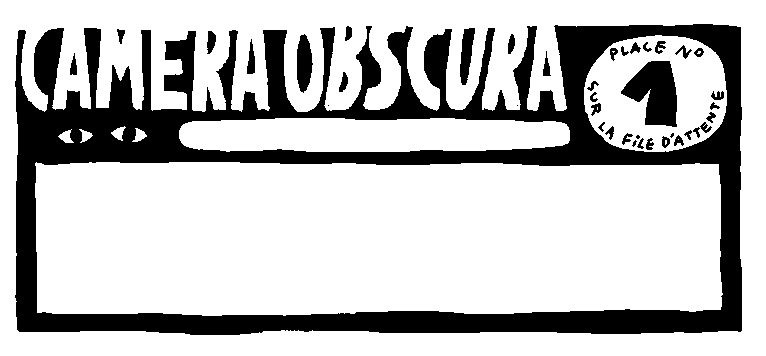
contenu/objet/billets/bg-1.png
