LeonLenclos/camera-obscura/contenu/objet/billets/bg.png

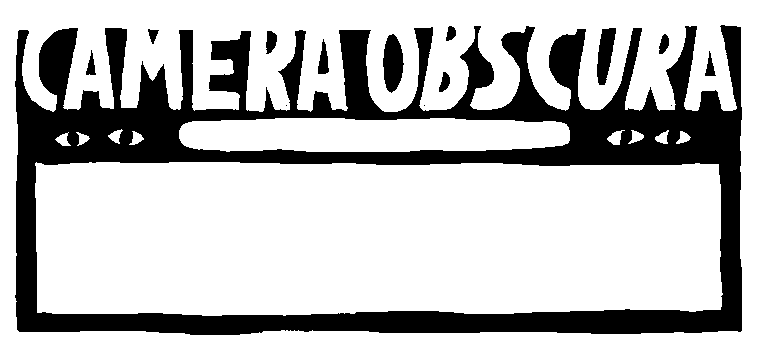
contenu/objet/billets/bg.png
