LeonLenclos/camera-obscura/contenu/photos/reference_voiture_1.jpg

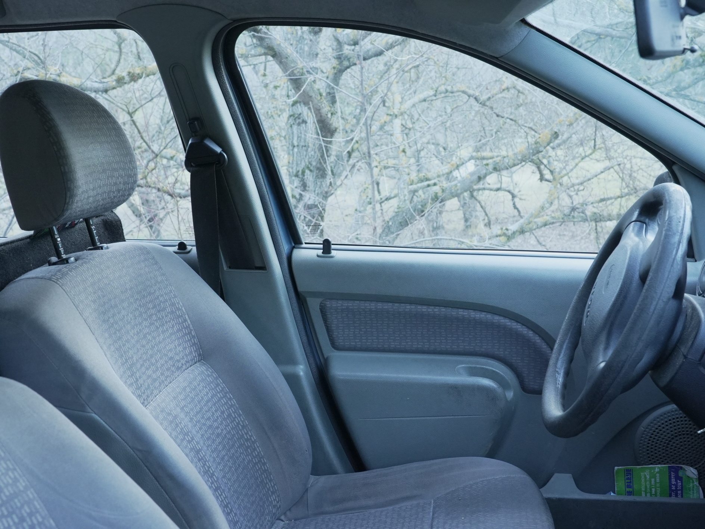
contenu/photos/reference_voiture_1.jpg
