LeonLenclos/camera-obscura/contenu/photos/reference_voiture_3.jpg

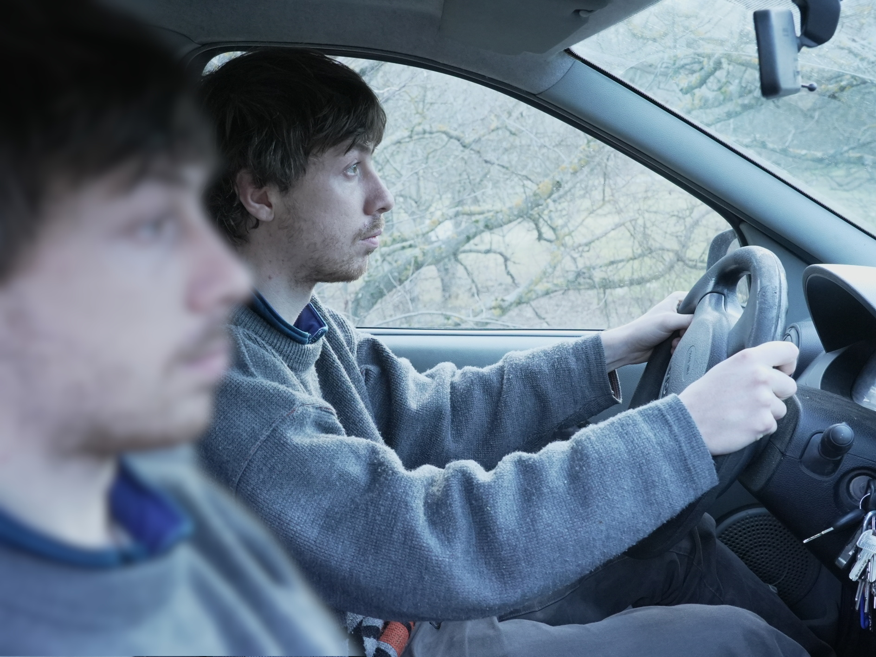
contenu/photos/reference_voiture_3.jpg
