LeonLenclos/camera-obscura/contenu/plans/base-fauteuils.png

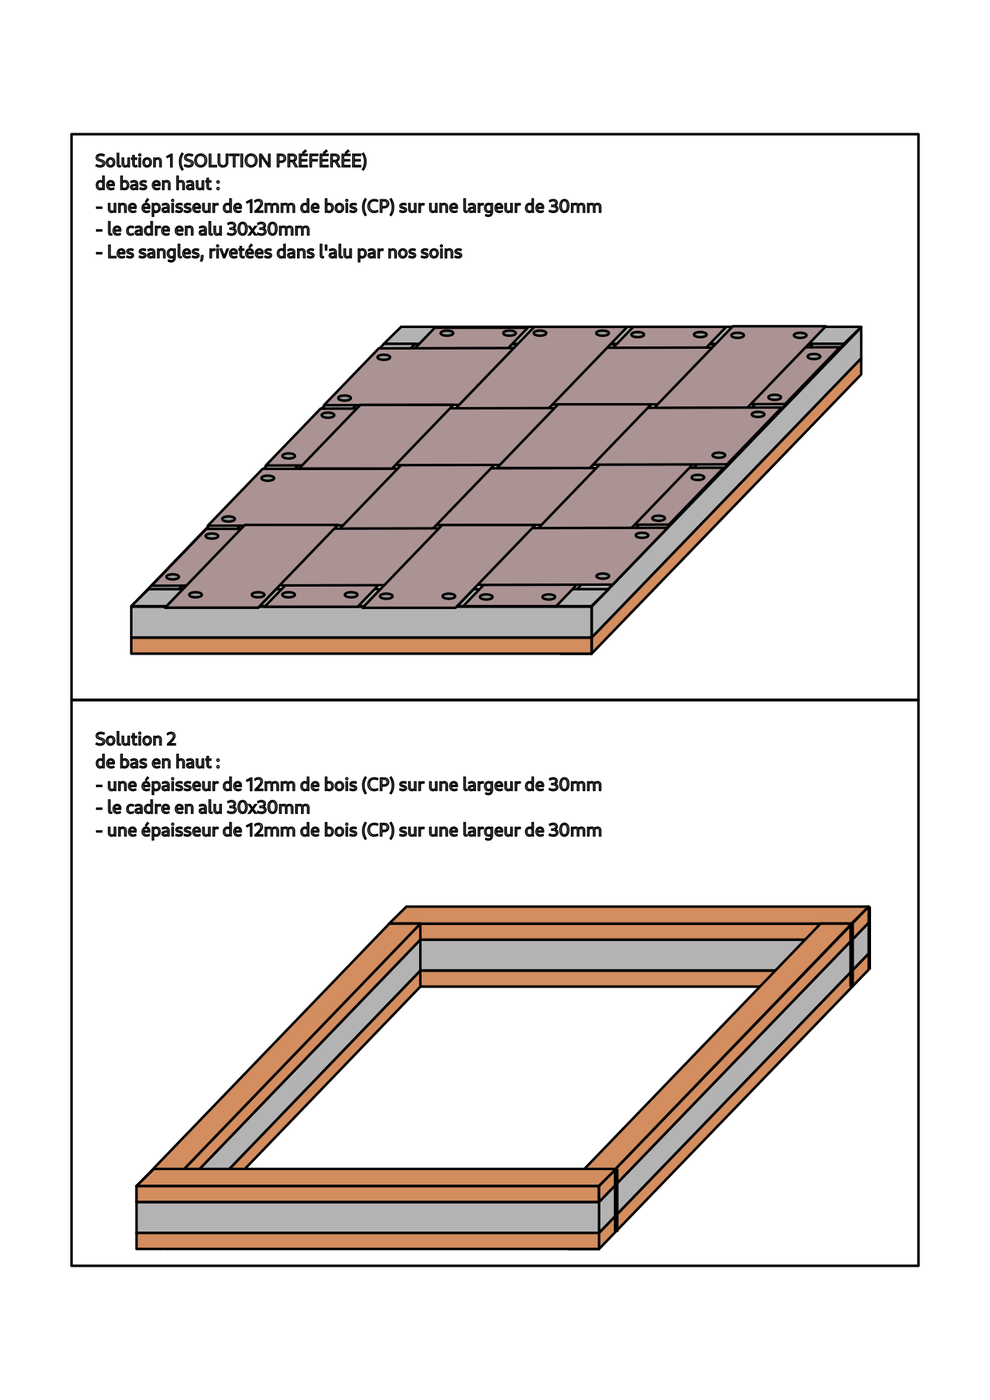
contenu/plans/base-fauteuils.png
