LeonLenclos/camera-obscura/contenu/plans/carte-arto.png

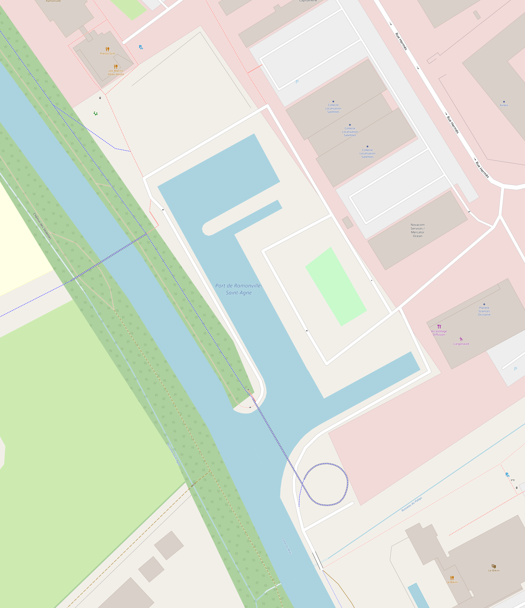
contenu/plans/carte-arto.png
