LeonLenclos/camera-obscura/contenu/plans/carte-chatillon.png

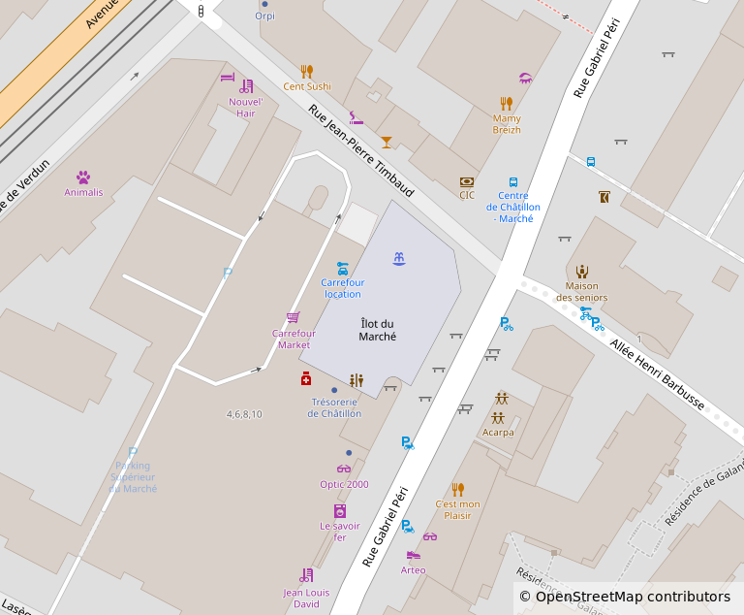
contenu/plans/carte-chatillon.png
