LeonLenclos/camera-obscura/contenu/plans/carte-cognac.png

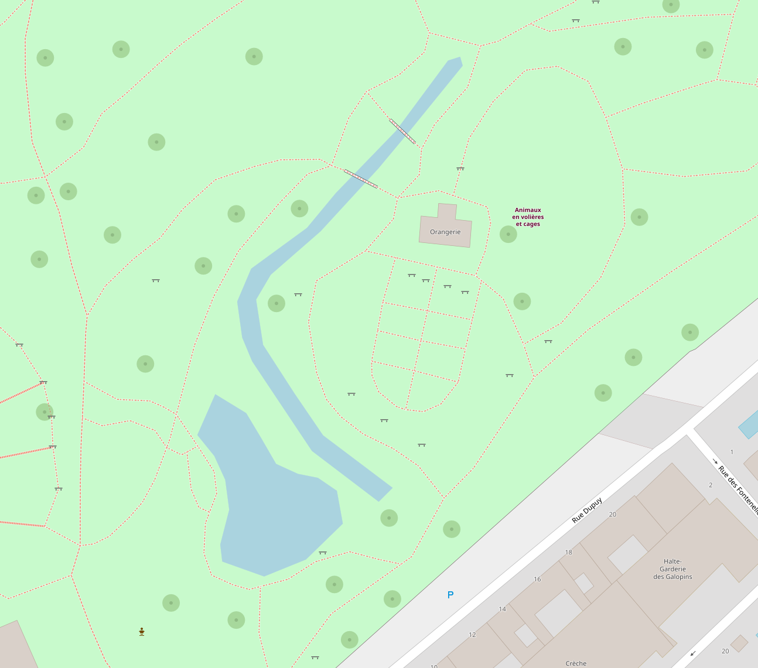
contenu/plans/carte-cognac.png
