LeonLenclos/camera-obscura/contenu/plans/carte-granville.png

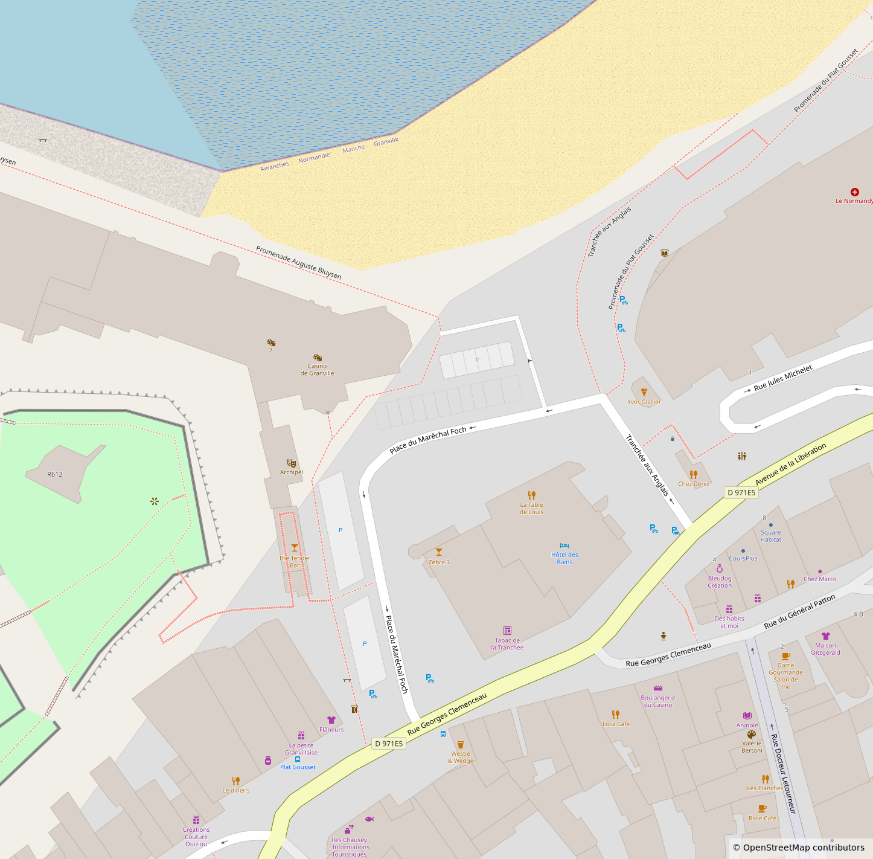
contenu/plans/carte-granville.png
