LeonLenclos/camera-obscura/contenu/plans/carte-mima.png

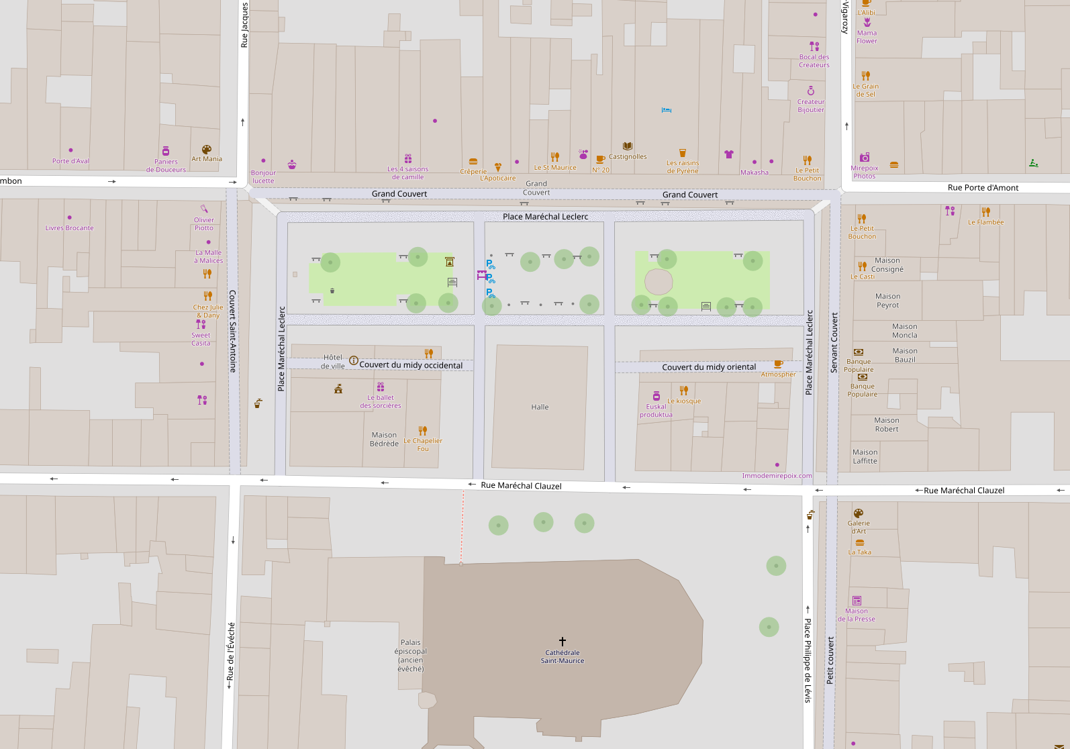
contenu/plans/carte-mima.png
