LeonLenclos/camera-obscura/contenu/plans/carte-ombres-cognac.png

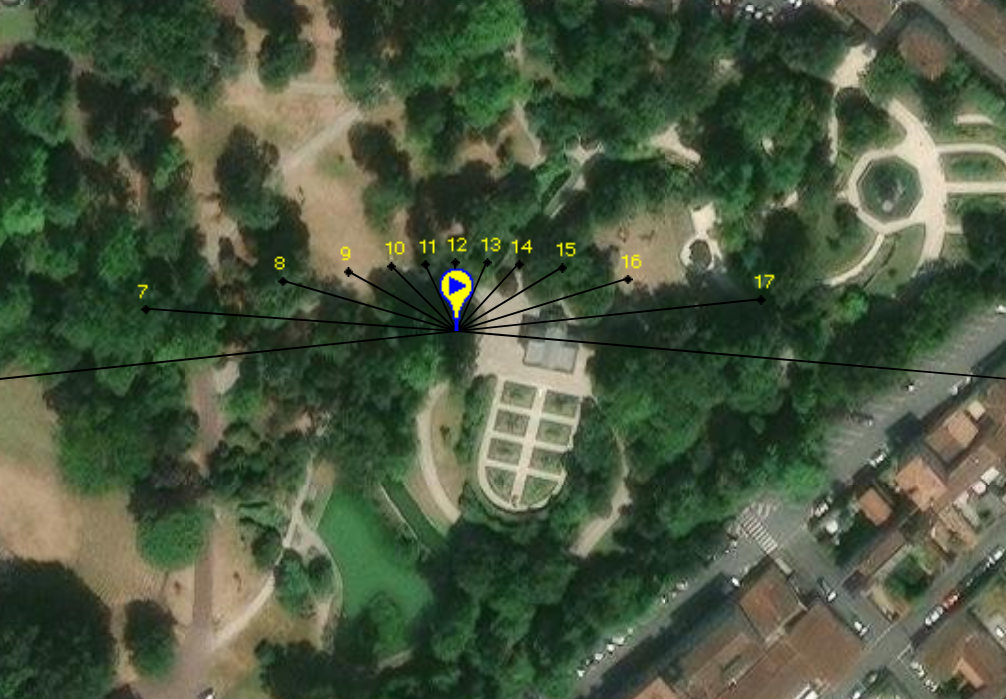
contenu/plans/carte-ombres-cognac.png
