LeonLenclos/camera-obscura/contenu/plans/carte-sat-cognac.png

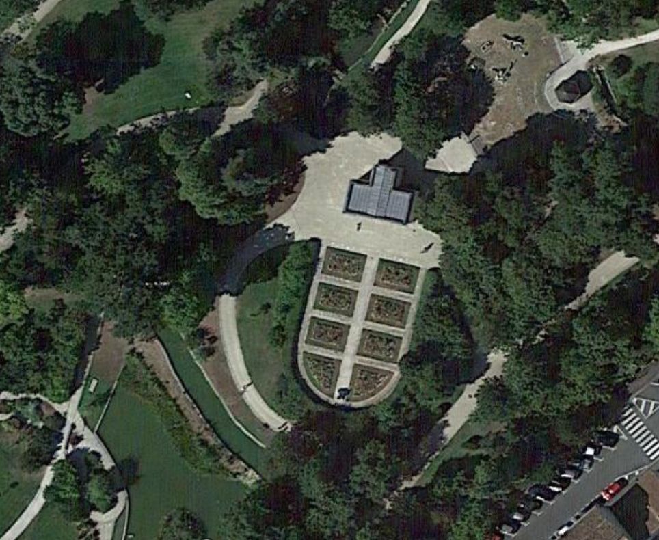
contenu/plans/carte-sat-cognac.png
