LeonLenclos/camera-obscura/contenu/plans/escalier-praticable.jpeg

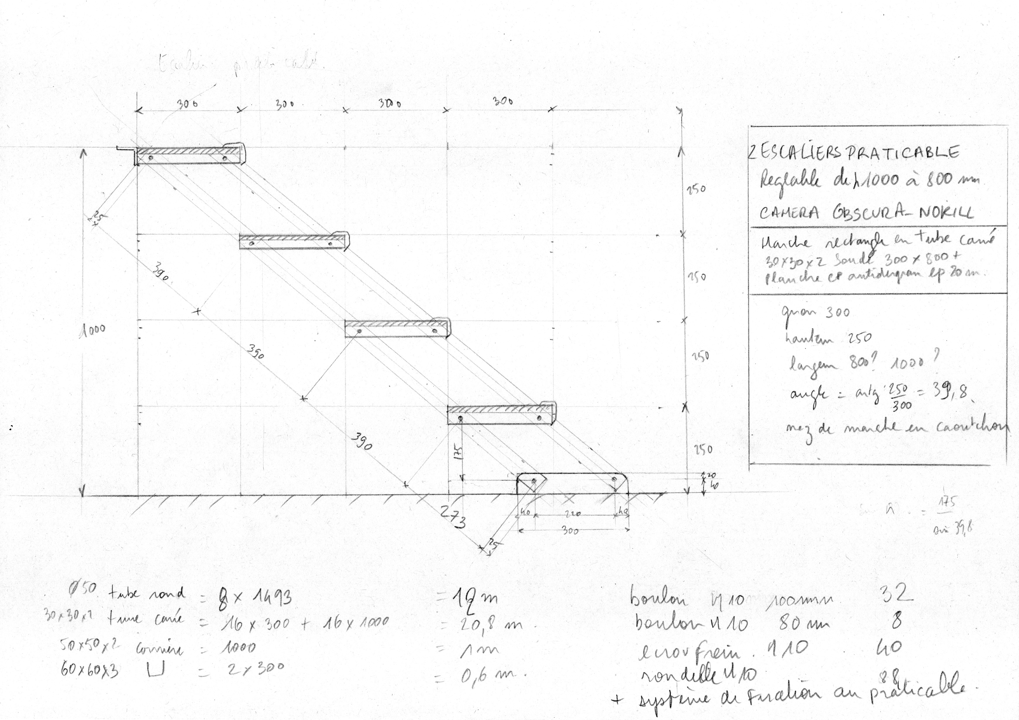
contenu/plans/escalier-praticable.jpeg
