LeonLenclos/camera-obscura/contenu/plans/escalier-remorque.jpeg

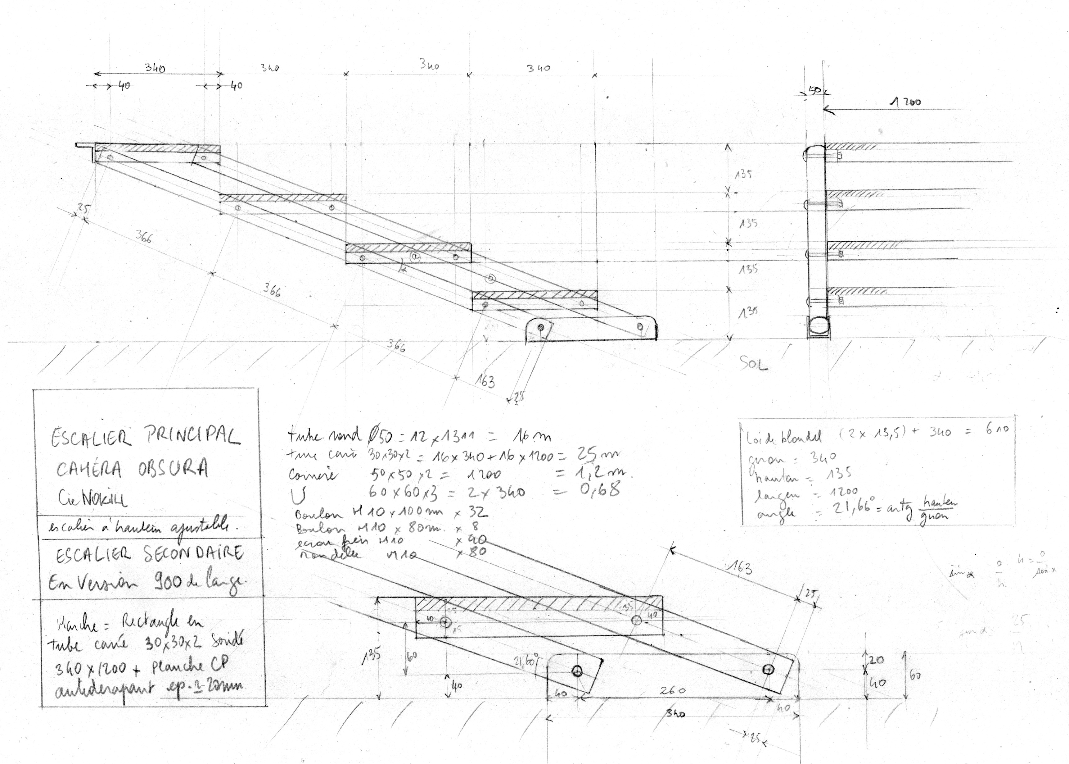
contenu/plans/escalier-remorque.jpeg
