LeonLenclos/camera-obscura/contenu/plans/extracteur_V01.jpeg

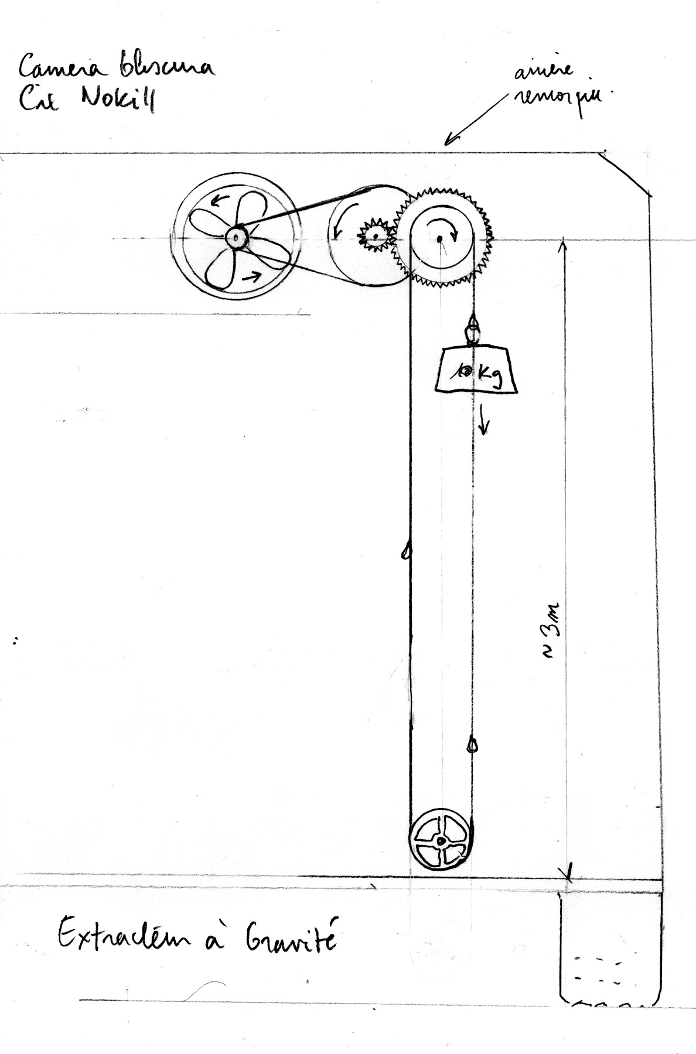
contenu/plans/extracteur_V01.jpeg
