LeonLenclos/camera-obscura/contenu/plans/fauteuil.png

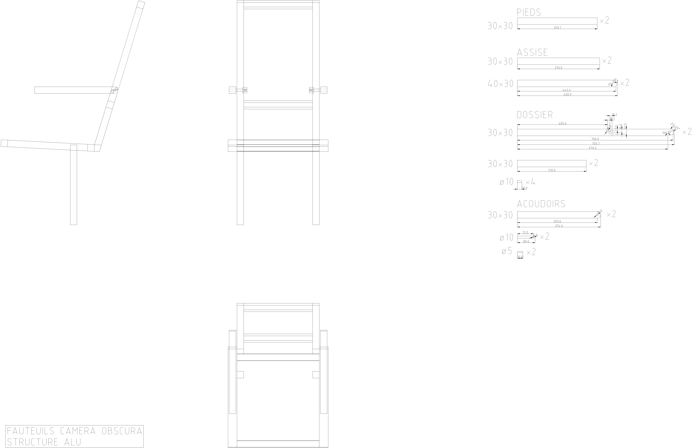
contenu/plans/fauteuil.png
