LeonLenclos/camera-obscura/contenu/plans/fauteuil_V02.jpeg

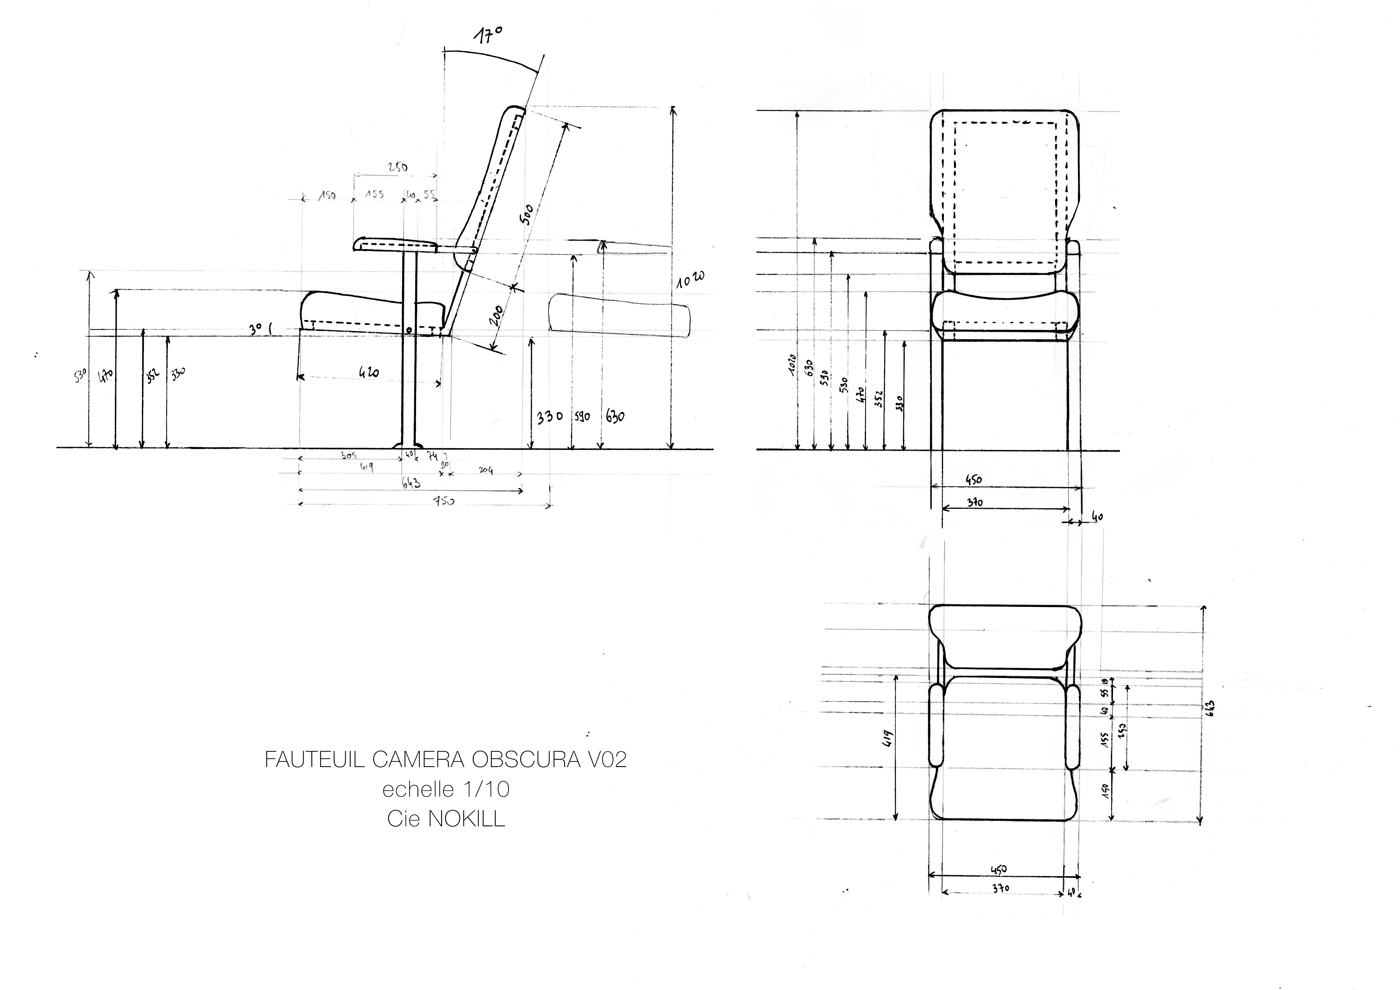
contenu/plans/fauteuil_V02.jpeg
