LeonLenclos/camera-obscura/contenu/plans/fut-lentilles.png

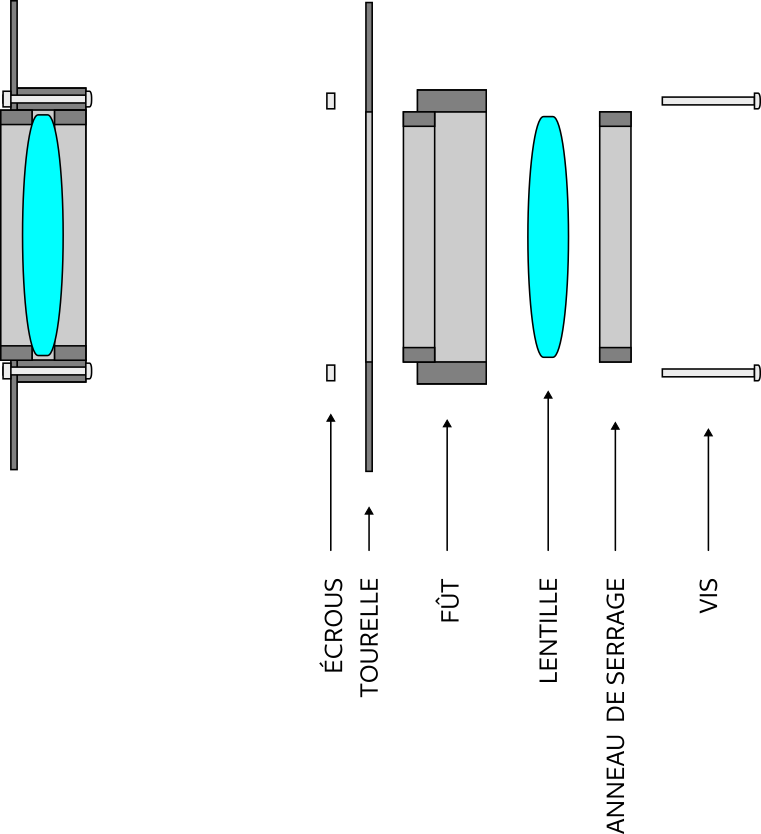
contenu/plans/fut-lentilles.png
