LeonLenclos/camera-obscura/contenu/plans/implantation.png

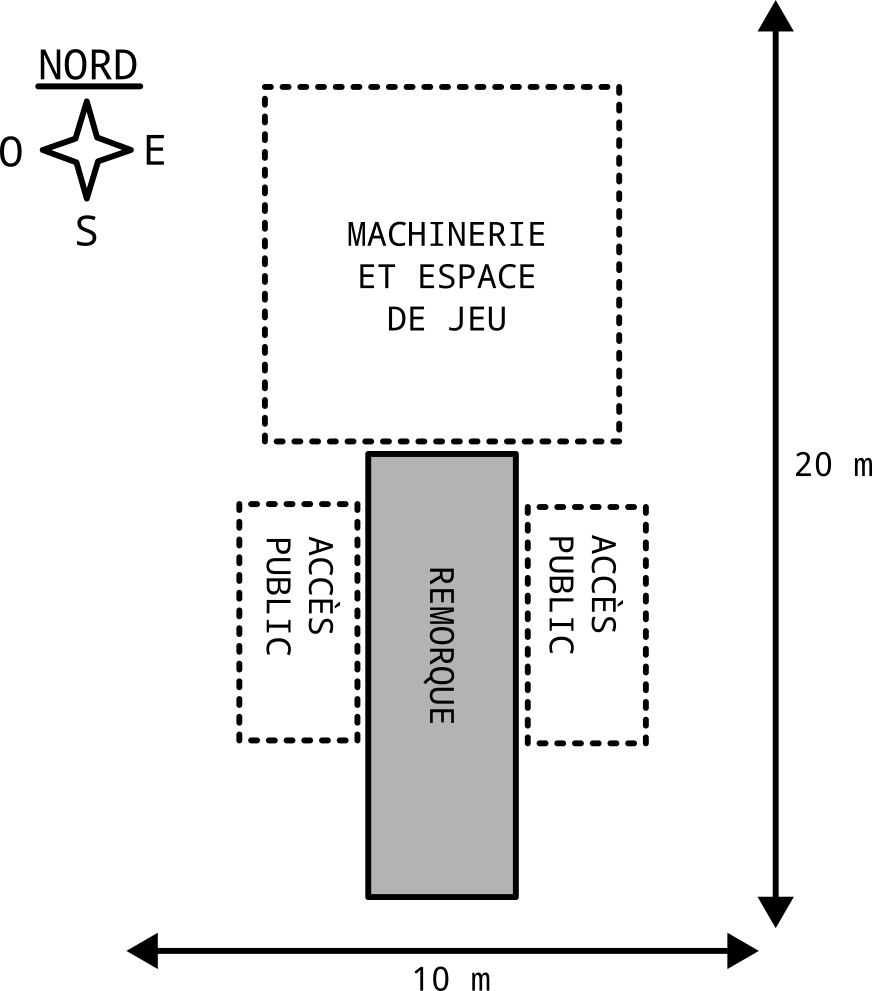
contenu/plans/implantation.png
