LeonLenclos/camera-obscura/contenu/plans/miroir-a-45-structure.png

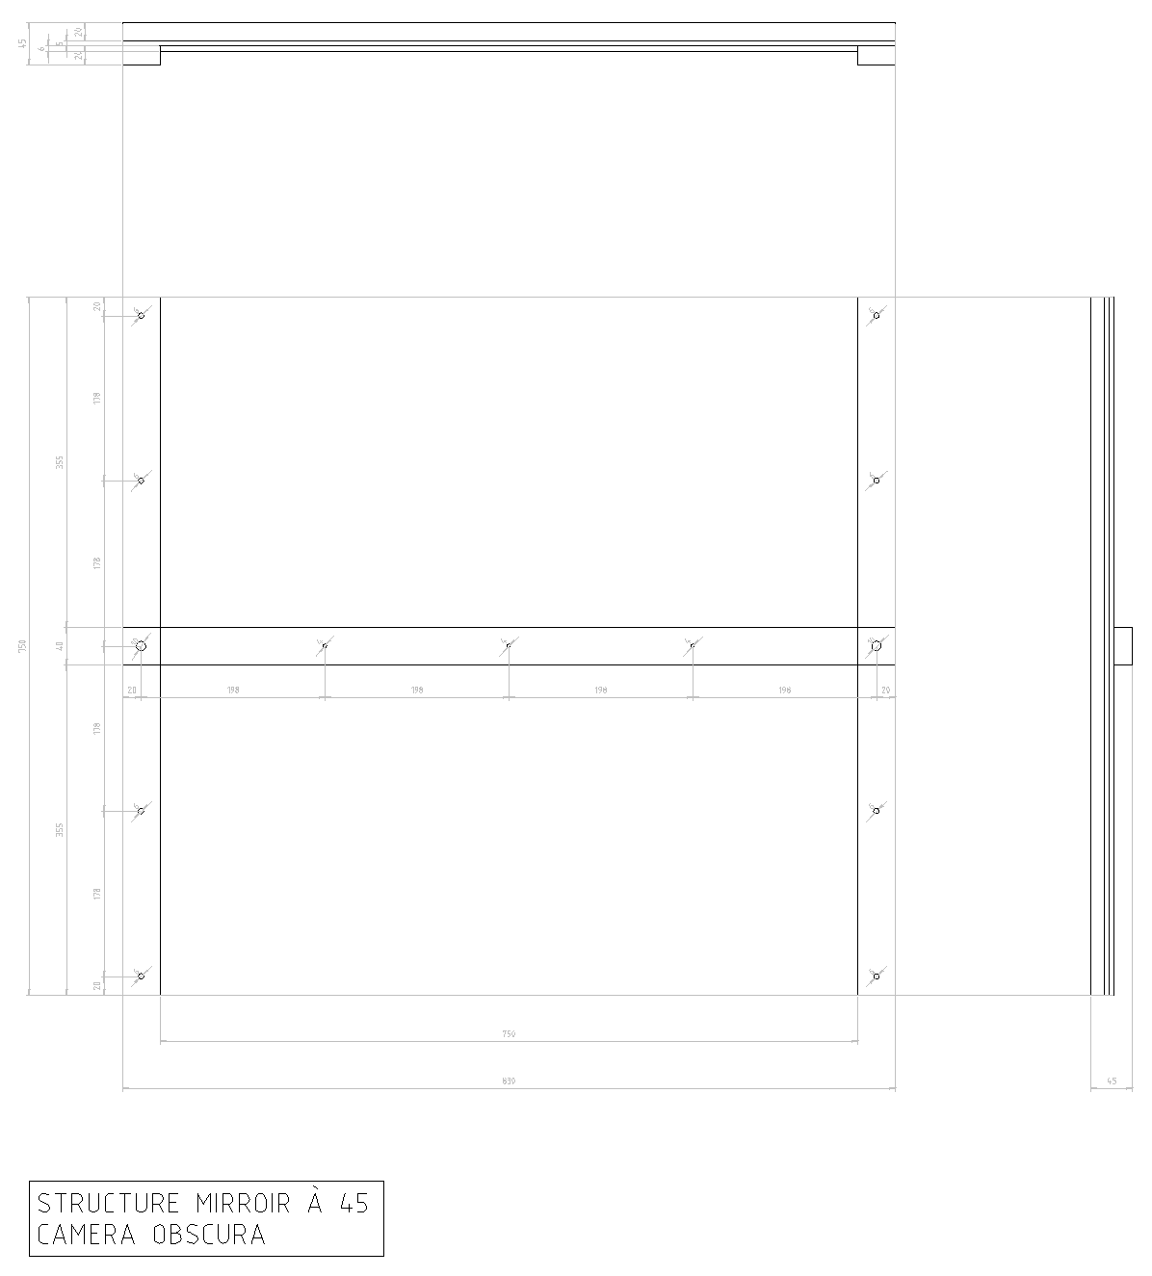
contenu/plans/miroir-a-45-structure.png
