LeonLenclos/camera-obscura/contenu/plans/plan-amenagement-1.png

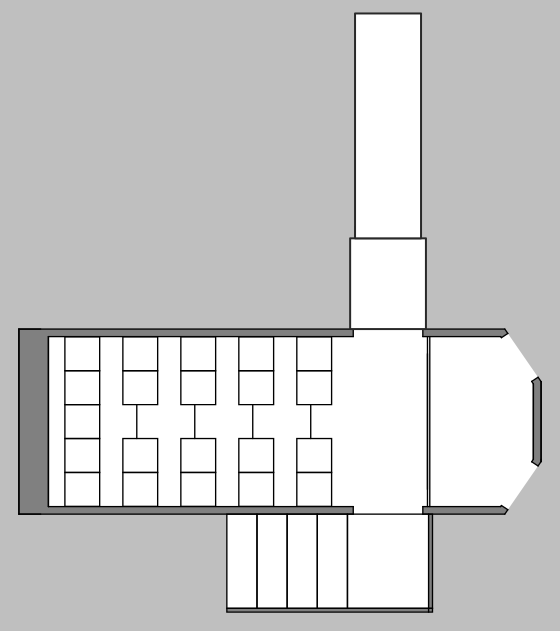
contenu/plans/plan-amenagement-1.png
