LeonLenclos/camera-obscura/contenu/plans/plan-amenagement-2.png

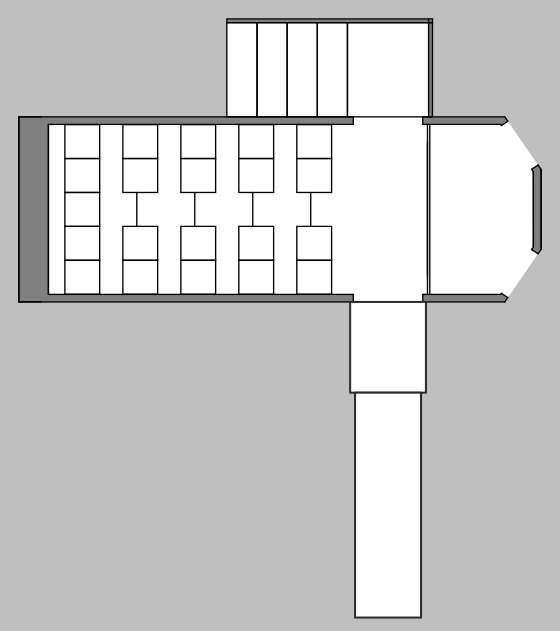
contenu/plans/plan-amenagement-2.png
