LeonLenclos/camera-obscura/contenu/plans/plan-dimensions.png

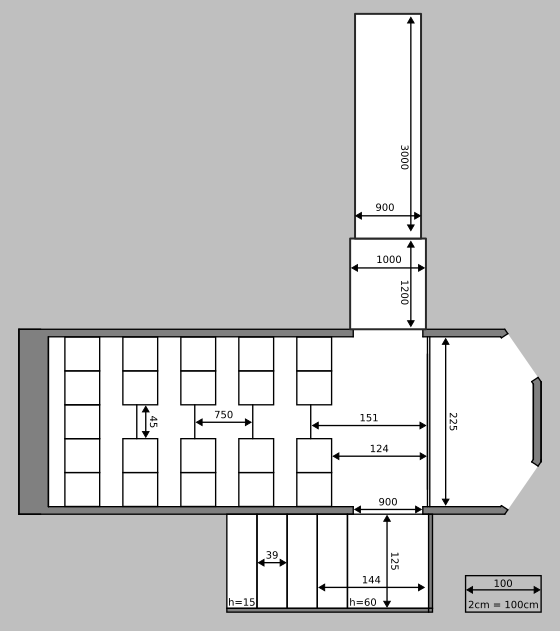
contenu/plans/plan-dimensions.png
