LeonLenclos/camera-obscura/contenu/plans/rack-xl.jpeg

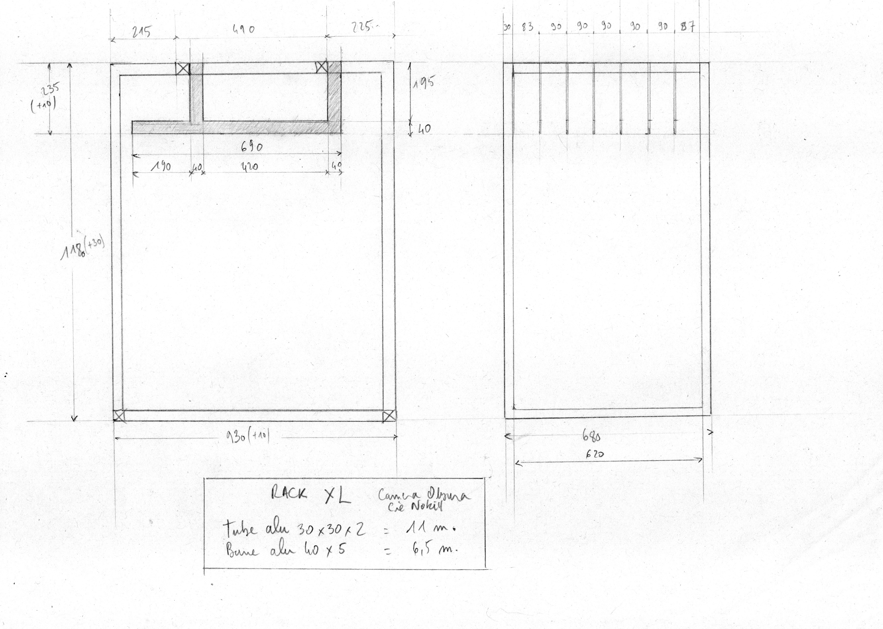
contenu/plans/rack-xl.jpeg
