LeonLenclos/camera-obscura/contenu/plans/toit-amici-simulation-3D.png

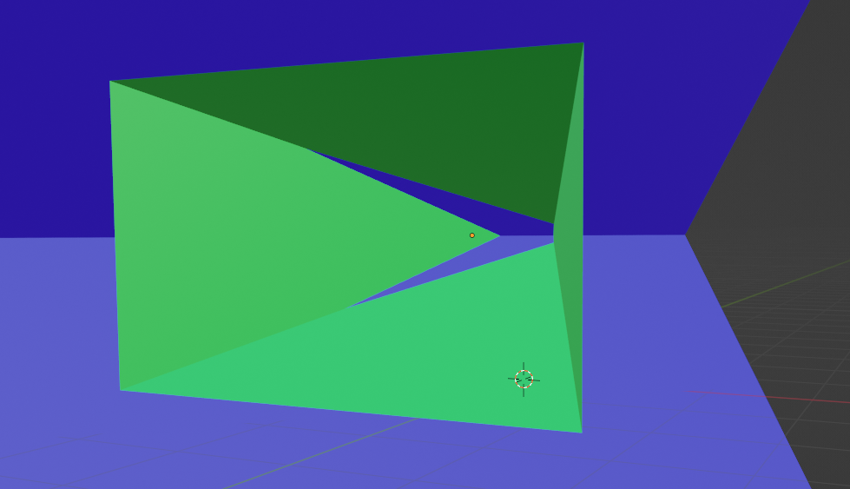
contenu/plans/toit-amici-simulation-3D.png
