LeonLenclos/camera-obscura/contenu/simulation/slides/disquedor3.png

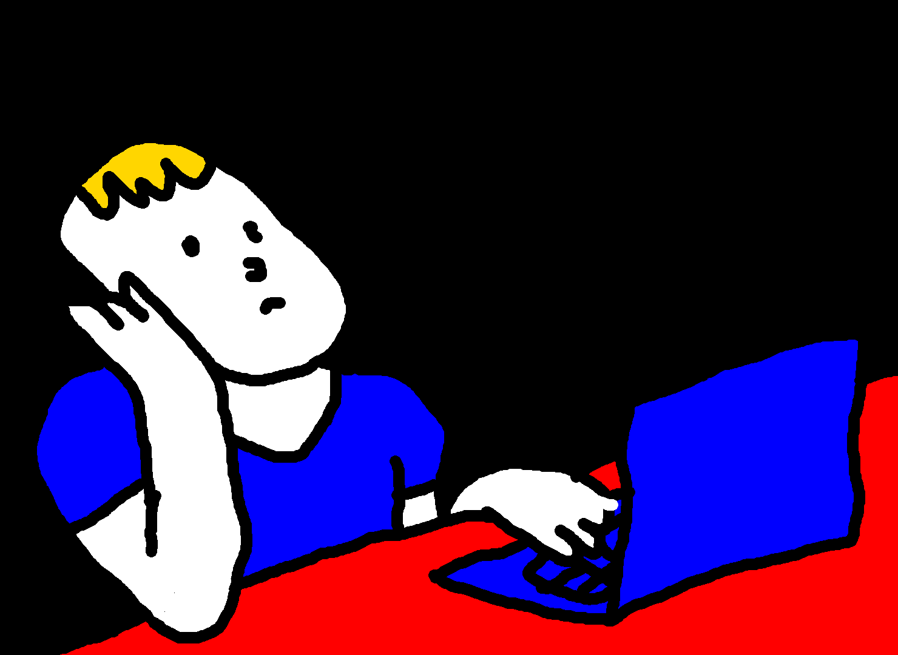
contenu/simulation/slides/disquedor3.png
