LeonLenclos/camera-obscura/contenu/animations/plexi/noir3-3.dxf

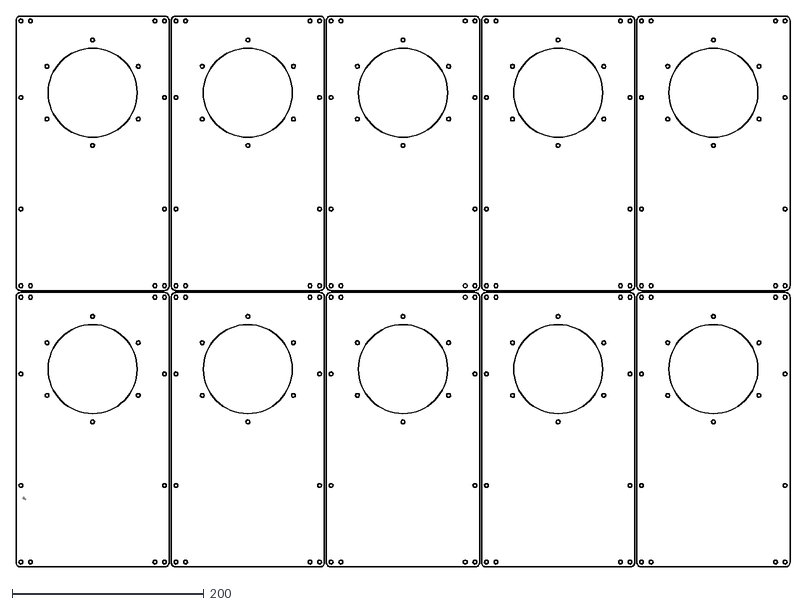
[picture p280: CAD file, 2024-04-01]
contenu/animations/plexi/noir3-3.dxf
808.0 x 575.0
