LeonLenclos/camera-obscura/contenu/plans/remorque-aspect-rouleau-5.dxf

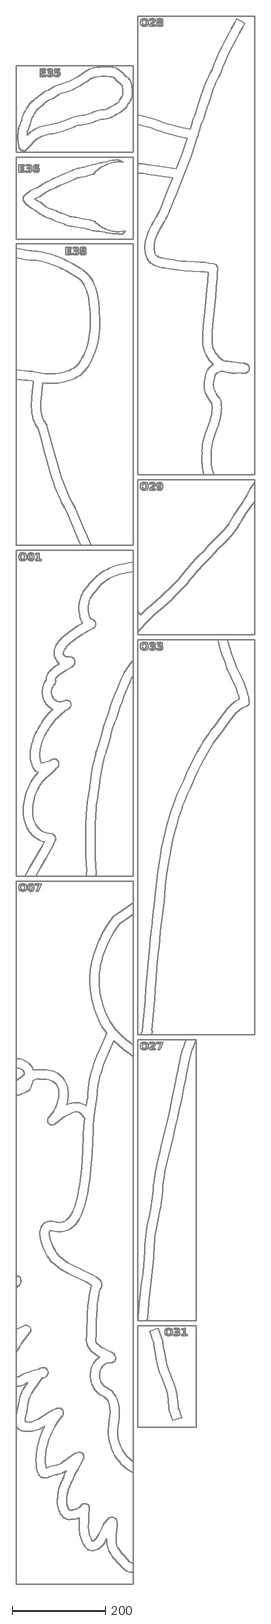
[picture p281: CAD file, 2024-07-08]
contenu/plans/remorque-aspect-rouleau-5.dxf
510.6 x 3359.4
