LeonLenclos/camera-obscura/contenu/animations/colo/M_070_A.dxf

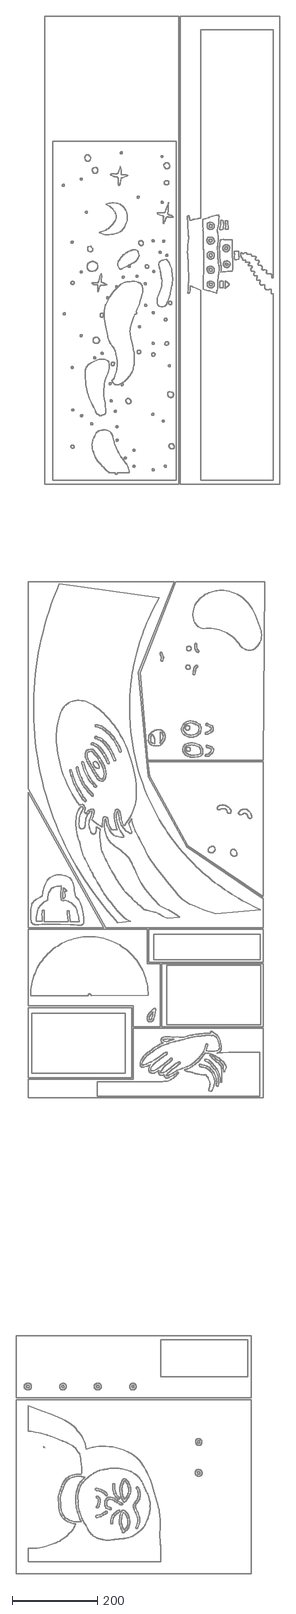
[picture p282: CAD file, 2024-04-04]
contenu/animations/colo/M_070_A.dxf
618.2 x 3650.6
