LeonLenclos/camera-obscura/contenu/animations/periodemalheureuse-colo-073.dxf

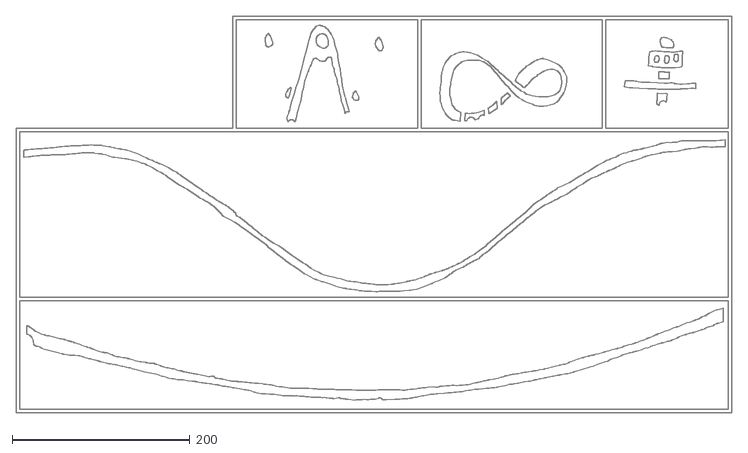
[picture p283: CAD file, 2024-05-27]
contenu/animations/periodemalheureuse-colo-073.dxf
806.0 x 447.1
