LeonLenclos/camera-obscura/contenu/animations/plexi/noir3-4.dxf

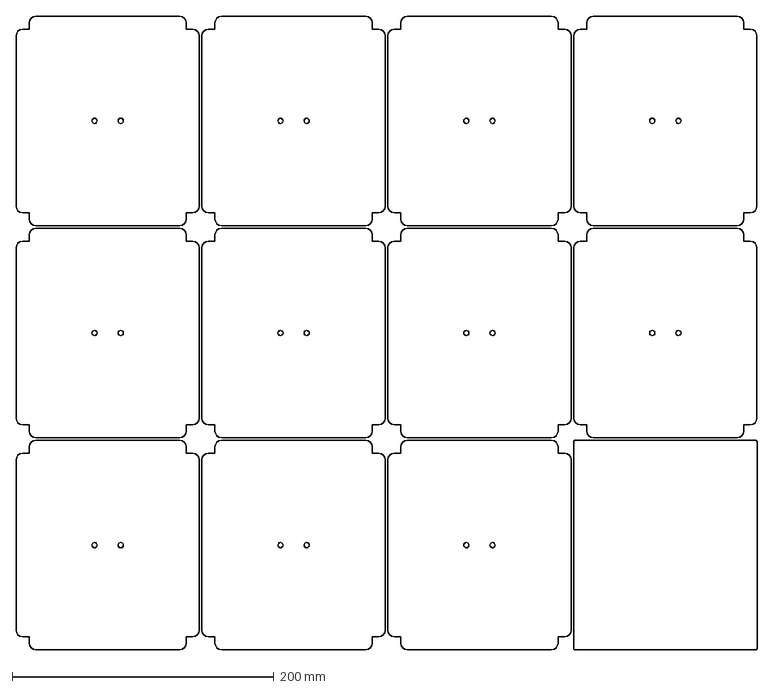
[picture p284: CAD file, 2024-04-01]
contenu/animations/plexi/noir3-4.dxf
566.0 x 484.0 mm
