LeonLenclos/camera-obscura/contenu/plans/remorque-aspect-rouleau-3.dxf

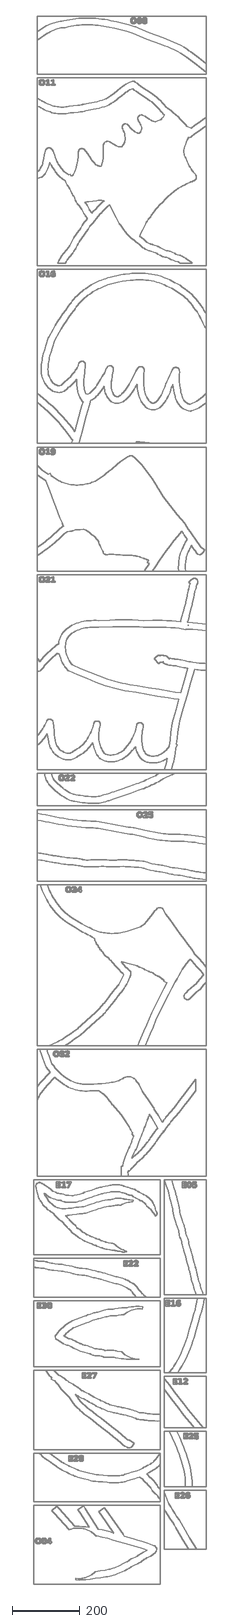
[picture p285: CAD file, 2024-07-08]
contenu/plans/remorque-aspect-rouleau-3.dxf
510.8 x 4638.1
