LeonLenclos/camera-obscura/contenu/animations/colo/M_069.dxf

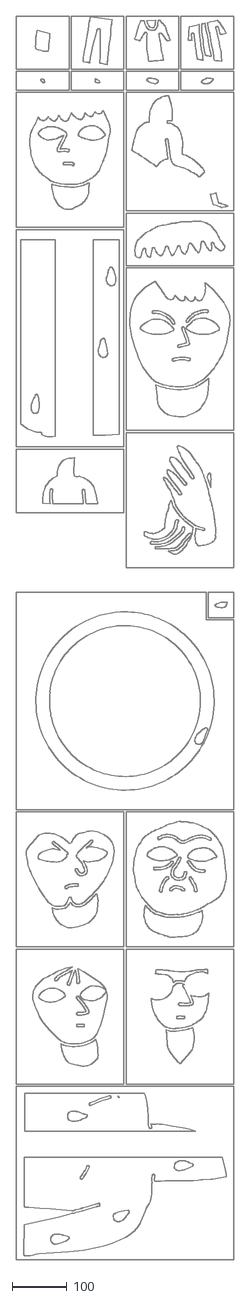
[picture p286: CAD file, 2024-04-03]
contenu/animations/colo/M_069.dxf
396.0 x 2265.5
