LeonLenclos/camera-obscura/contenu/animations/plexi-trans4mm-session-mai.dxf

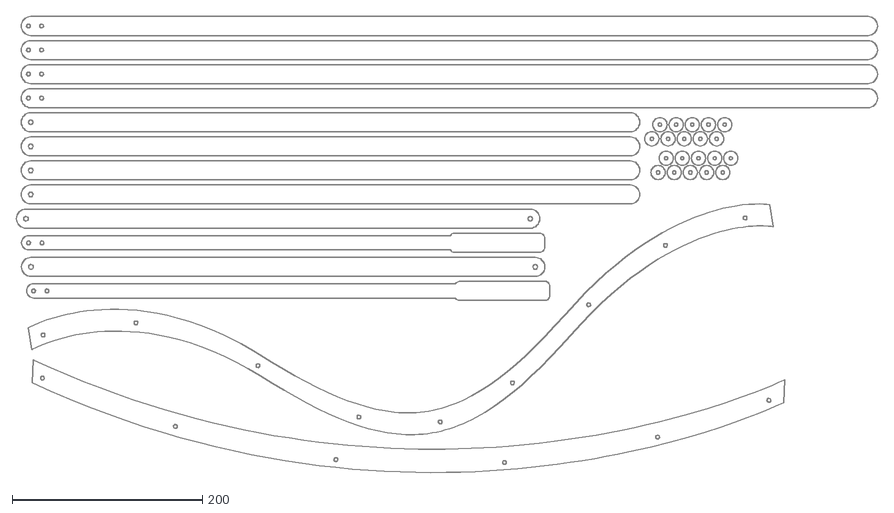
[picture p287: CAD file, 2024-05-27]
contenu/animations/plexi-trans4mm-session-mai.dxf
905.1 x 479.3
