LeonLenclos/camera-obscura/contenu/animations/plexi/trans3-1.dxf

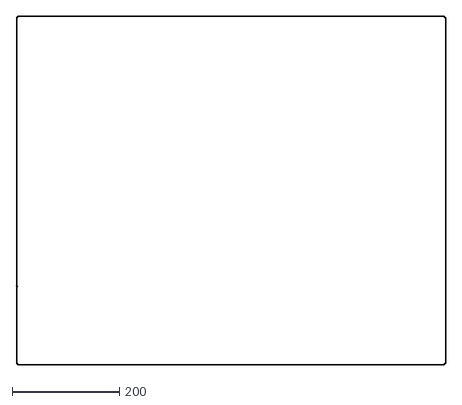
[picture p288: CAD file, 2024-04-01]
contenu/animations/plexi/trans3-1.dxf
800.8 x 650.0
