LeonLenclos/camera-obscura/contenu/plans/remorque-aspect-rouleau-juin.dxf

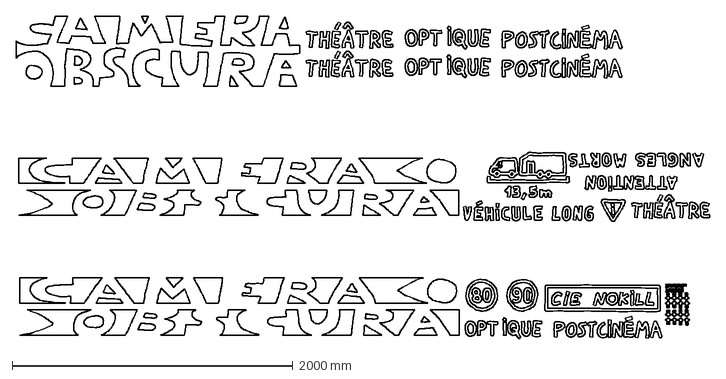
[picture p289: CAD file, 2024-06-13]
contenu/plans/remorque-aspect-rouleau-juin.dxf
4946.9 x 2298.1 mm
