LeonLenclos/camera-obscura/contenu/animations/colo/M_070.dxf

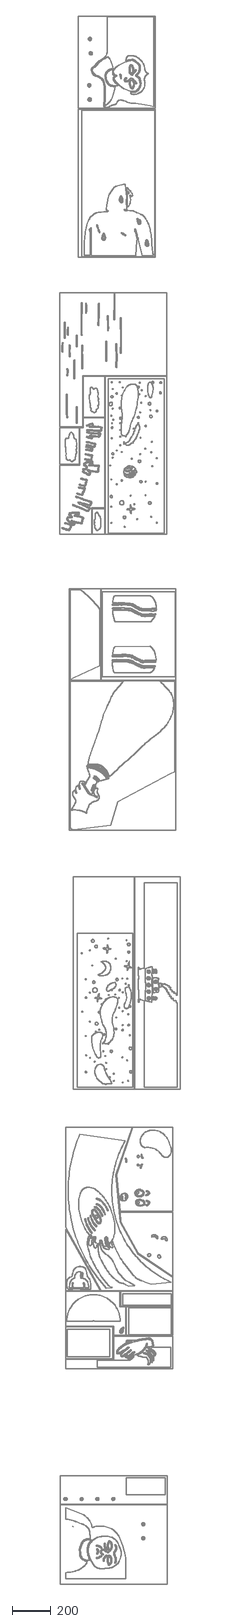
[picture p290: CAD file, 2024-04-03]
contenu/animations/colo/M_070.dxf
620.1 x 8090.7
