LeonLenclos/camera-obscura/contenu/animations/periodemalheureuse-colo-074.dxf

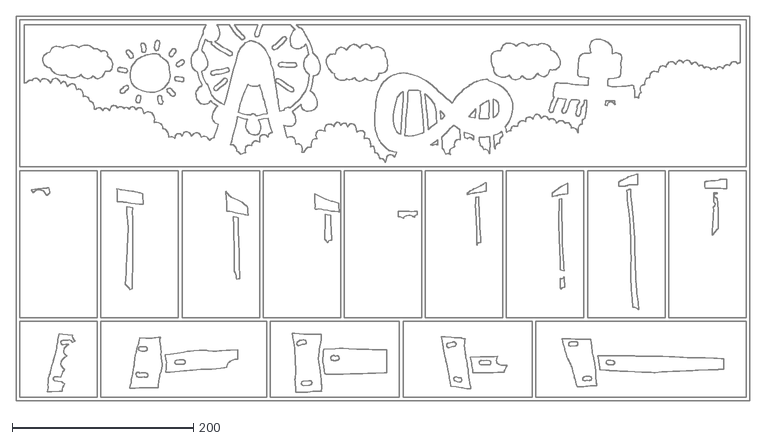
[picture p291: CAD file, 2024-05-27]
contenu/animations/periodemalheureuse-colo-074.dxf
809.3 x 424.4
