LeonLenclos/camera-obscura/contenu/animations/plexi/trans3-6.dxf

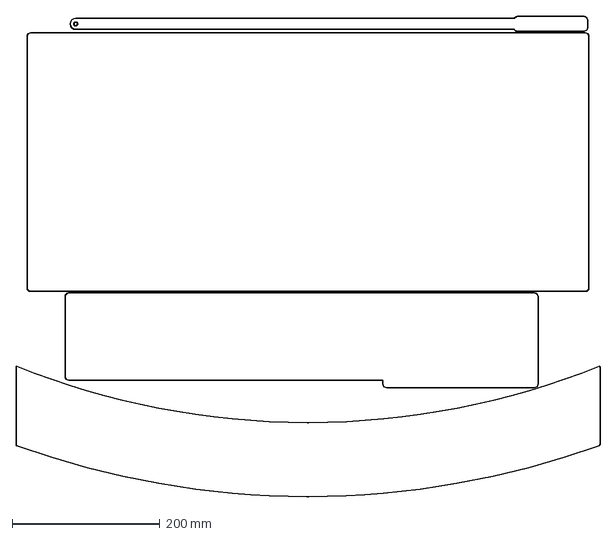
[picture p292: CAD file, 2024-04-01]
contenu/animations/plexi/trans3-6.dxf
790.0 x 649.3 mm
