LeonLenclos/camera-obscura/contenu/plans/fut.dxf

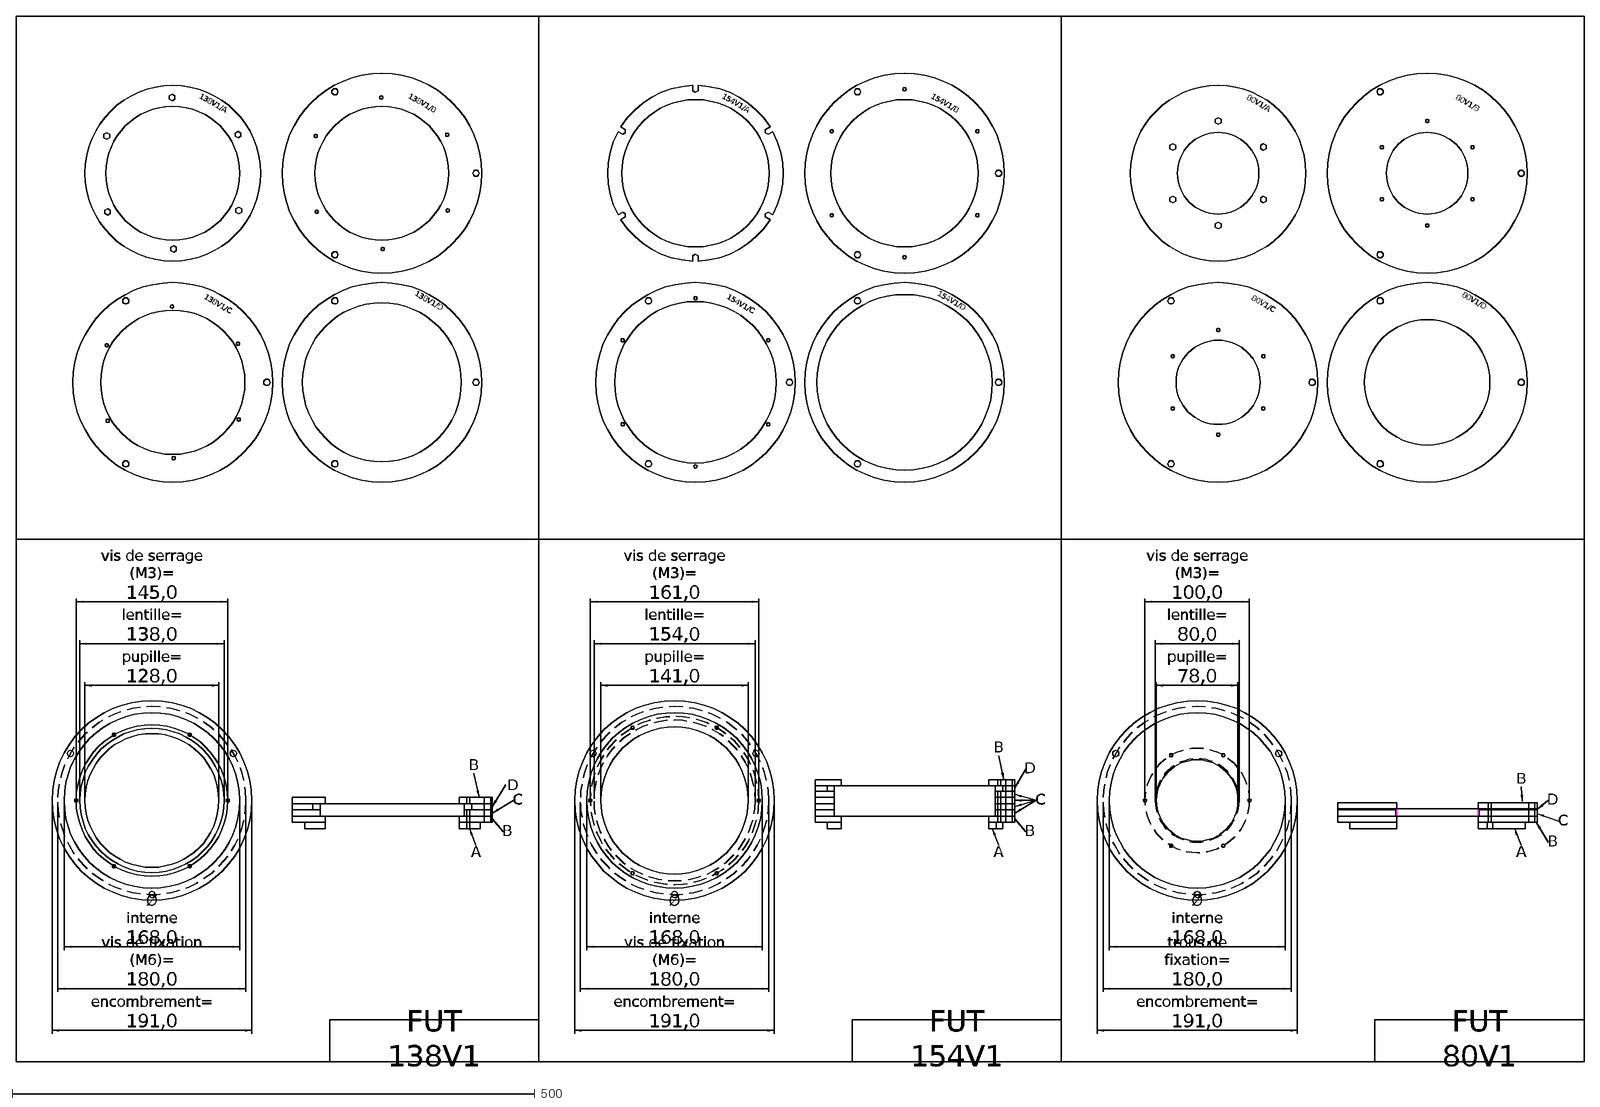
[picture p293: CAD file, 2024-06-03]
contenu/plans/fut.dxf
154,0
180,0
168,0
191,0
lentille=
encombrement=
141,0
pupille=
Ø interne
vis de fixation (M6)=
161,0
vis de serrage (M3)=
trous de fixation=
80,0
100,0
B
C
D
A
154V1/A
154V1/B
154V1/D
154V1/C
FUT 154V1
FUT 80V1
78,0
80V1/B
80V1/A
80V1/D
80V1/C
138,0
145,0
128,0
FUT 138V1
138V1/A
138V1/B
138V1/C
138V1/D
