LeonLenclos/camera-obscura/contenu/animations/colo/061-grand.dxf

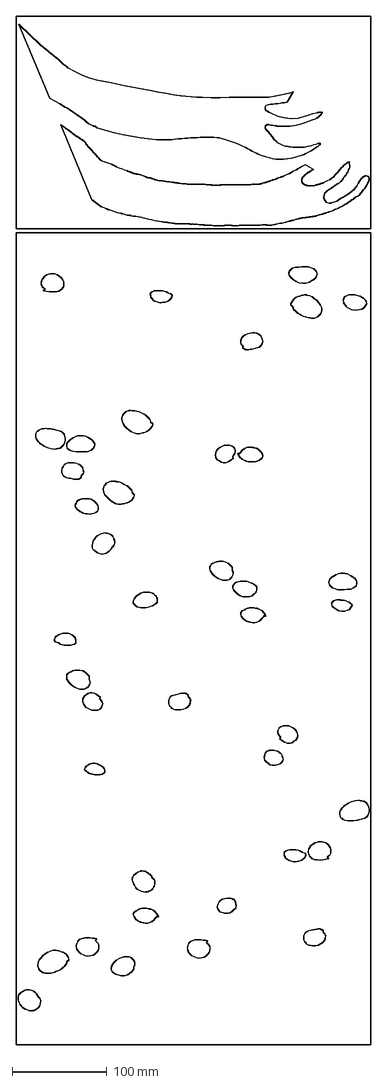
[picture p294: CAD file, 2024-04-03]
contenu/animations/colo/061-grand.dxf
374.0 x 1084.3 mm
