LeonLenclos/camera-obscura/contenu/animations/plexi-noir-session-mai.dxf

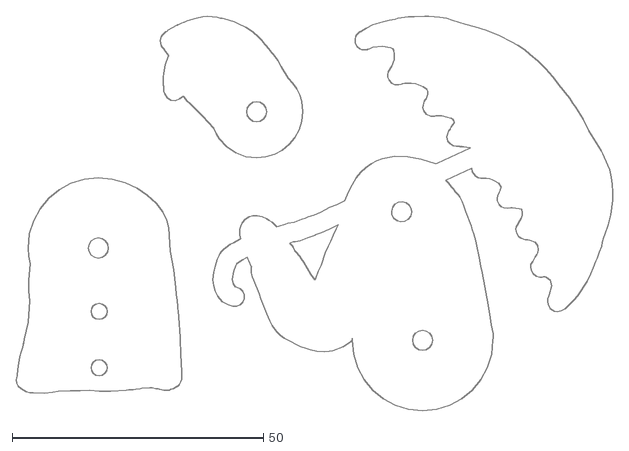
[picture p295: CAD file, 2024-05-27]
contenu/animations/plexi-noir-session-mai.dxf
118.8 x 78.5
