LeonLenclos/camera-obscura/contenu/animations/plexi/trans4-1.dxf

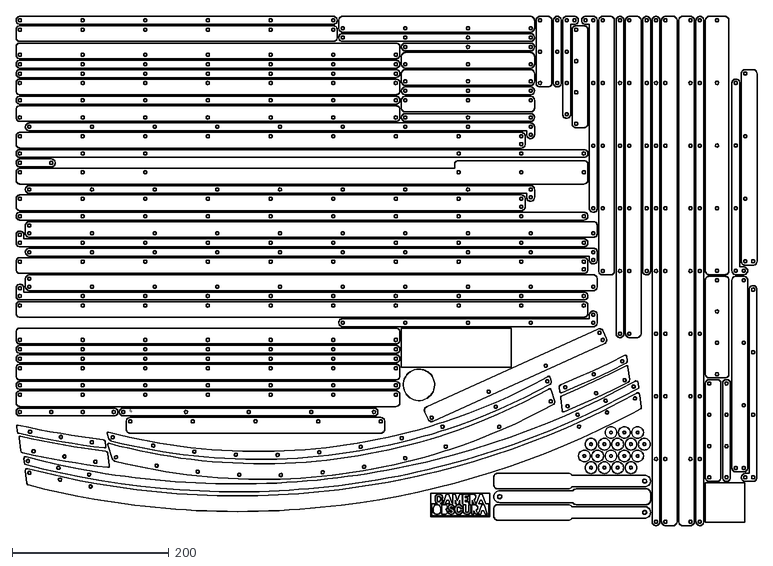
[picture p296: CAD file, 2024-04-01]
contenu/animations/plexi/trans4-1.dxf
945.9 x 650.0
