LeonLenclos/camera-obscura/contenu/plans/fut138V1-laser.dxf

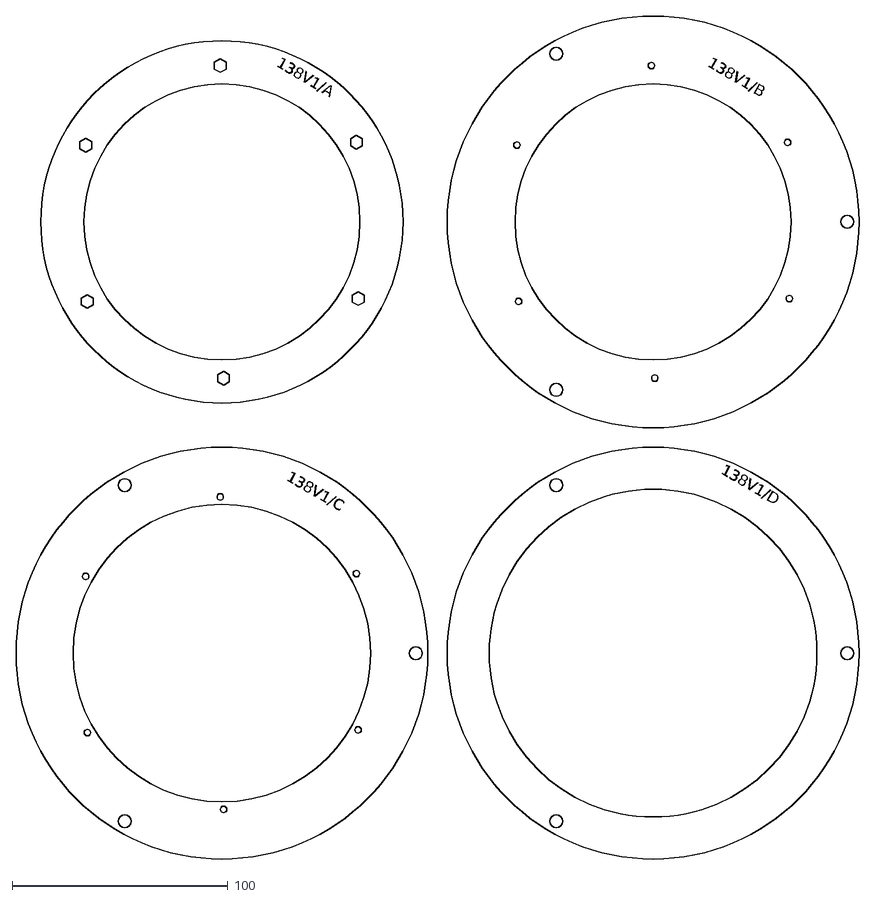
[picture p297: CAD file, 2024-06-03]
contenu/plans/fut138V1-laser.dxf
138V1/A
138V1/B
138V1/C
138V1/D
