LeonLenclos/camera-obscura/contenu/animations/colo/M_020.dxf

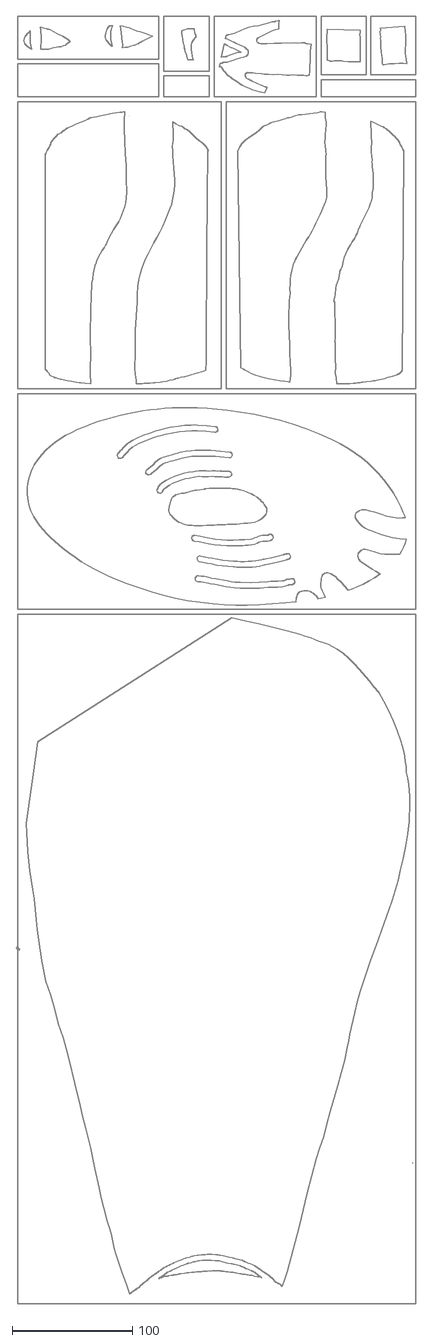
[picture p298: CAD file, 2024-04-03]
contenu/animations/colo/M_020.dxf
332.3 x 1071.8
