LeonLenclos/camera-obscura/contenu/animations/mecanique-animations-test.dxf

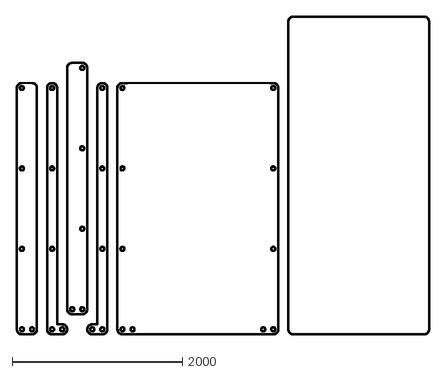
[picture p299: CAD file, 2024-04-01]
contenu/animations/mecanique-animations-test.dxf
4853.9 x 3743.6
