LeonLenclos/camera-obscura/contenu/animations/plexi/trans3-3.dxf

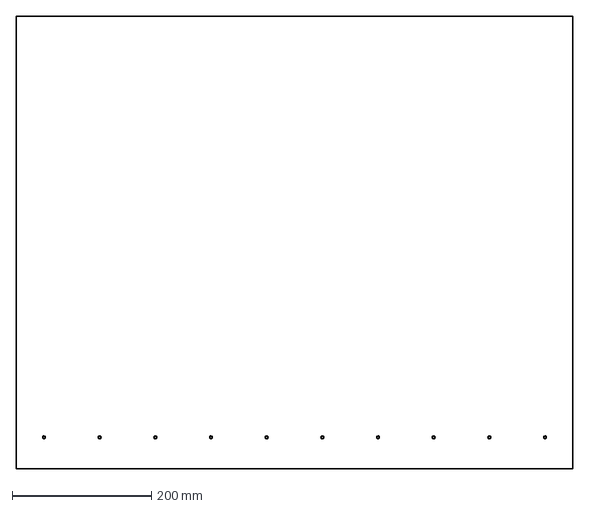
[picture p300: CAD file, 2024-04-01]
contenu/animations/plexi/trans3-3.dxf
800.0 x 650.0 mm
