LeonLenclos/camera-obscura/contenu/plans/toit-amici-decoupe-miroir-B.dxf

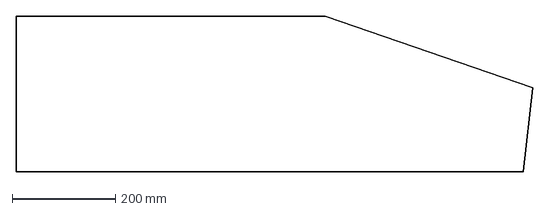
[picture p301: CAD file, 2024-05-07]
contenu/plans/toit-amici-decoupe-miroir-B.dxf
1000.0 x 300.0 mm
