LeonLenclos/camera-obscura/contenu/animations/colo/069.dxf

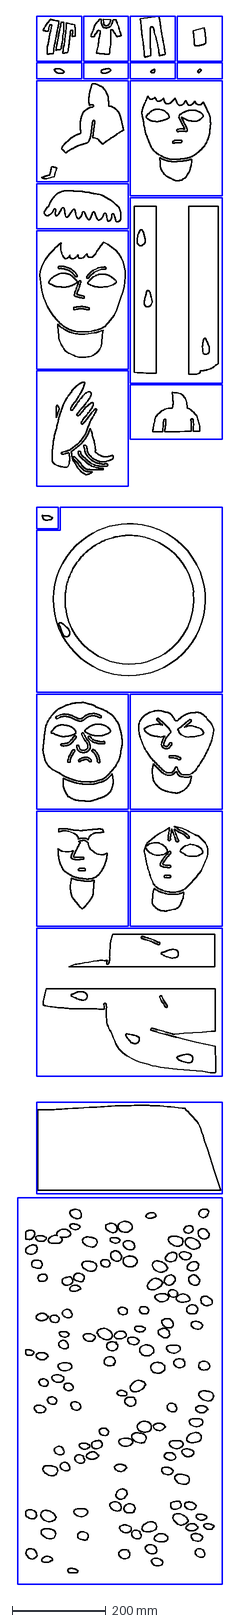
[picture p302: CAD file, 2024-04-03]
contenu/animations/colo/069.dxf
436.0 x 3351.2 mm
