LeonLenclos/camera-obscura/contenu/animations/plexi/trans4-2.dxf

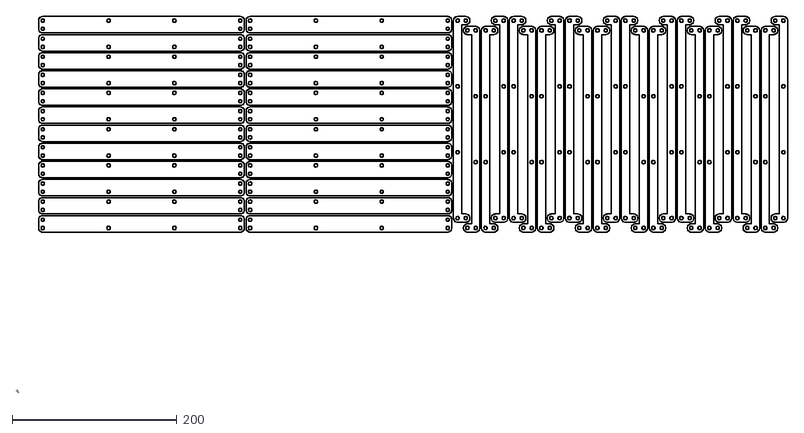
[picture p303: CAD file, 2024-04-01]
contenu/animations/plexi/trans4-2.dxf
936.9 x 457.0
