LeonLenclos/camera-obscura/contenu/plans/toit-amici-decoupe-miroir-A.dxf

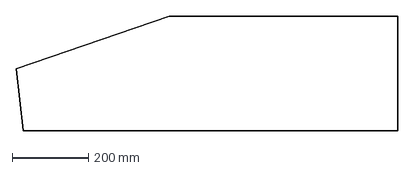
[picture p304: CAD file, 2024-05-07]
contenu/plans/toit-amici-decoupe-miroir-A.dxf
1000.0 x 300.0 mm
