LeonLenclos/camera-obscura/contenu/animations/colo/M_061.dxf

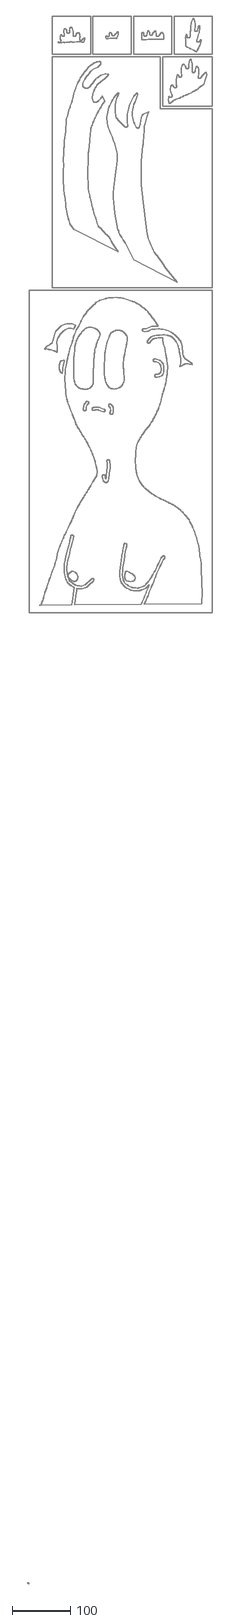
[picture p305: CAD file, 2024-04-03]
contenu/animations/colo/M_061.dxf
318.8 x 2703.1
