LeonLenclos/camera-obscura/contenu/animations/plexi/noir3-1.dxf

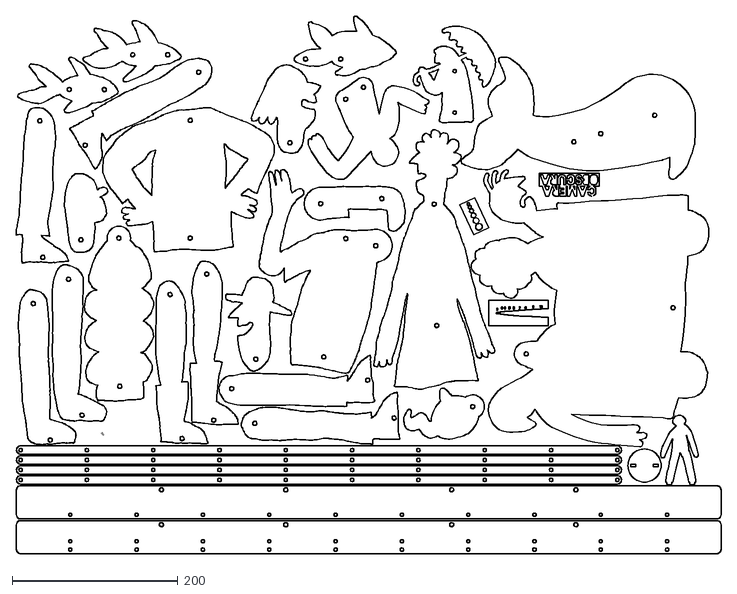
[picture p306: CAD file, 2024-04-01]
contenu/animations/plexi/noir3-1.dxf
850.5 x 648.3
