LeonLenclos/camera-obscura/contenu/plans/obturateur.dxf

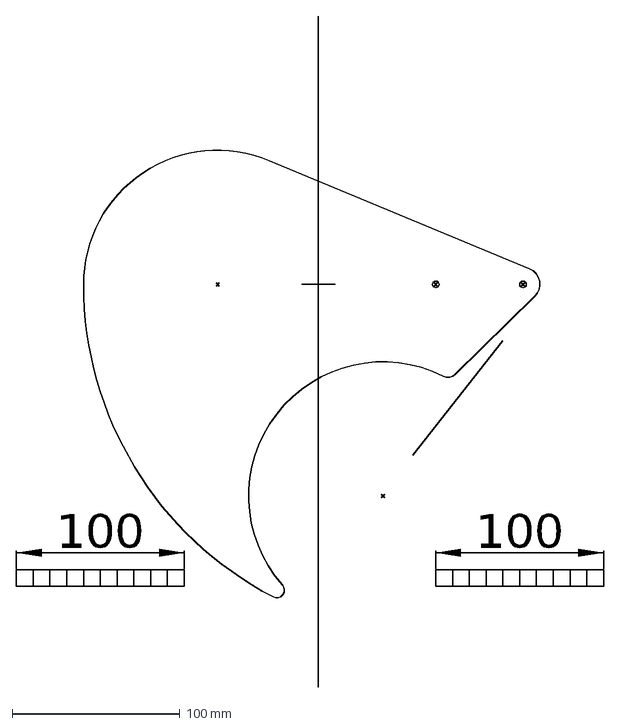
[picture p307: CAD file, 2024-03-08]
contenu/plans/obturateur.dxf
100
