LeonLenclos/camera-obscura/contenu/animations/colo/061-petit.dxf

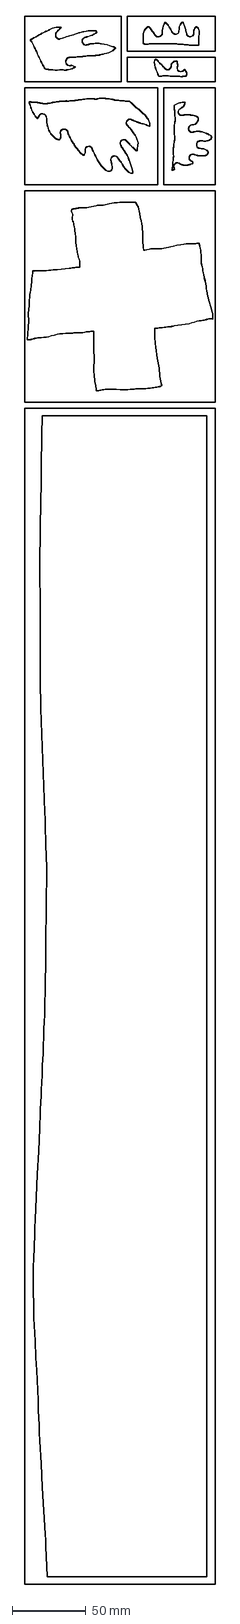
[picture p308: CAD file, 2024-04-03]
contenu/animations/colo/061-petit.dxf
129.8 x 1066.8 mm
