LeonLenclos/camera-obscura/contenu/animations/plexi/tout.dxf

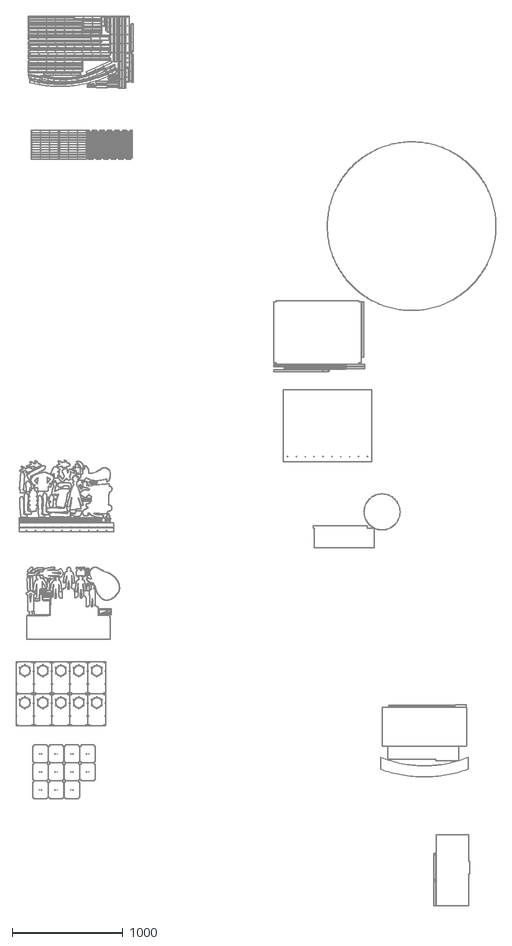
[picture p309: CAD file, 2024-04-01]
contenu/animations/plexi/tout.dxf
4325.9 x 8015.6
