LeonLenclos/camera-obscura/contenu/plans/plaques-reflecteurs.dxf

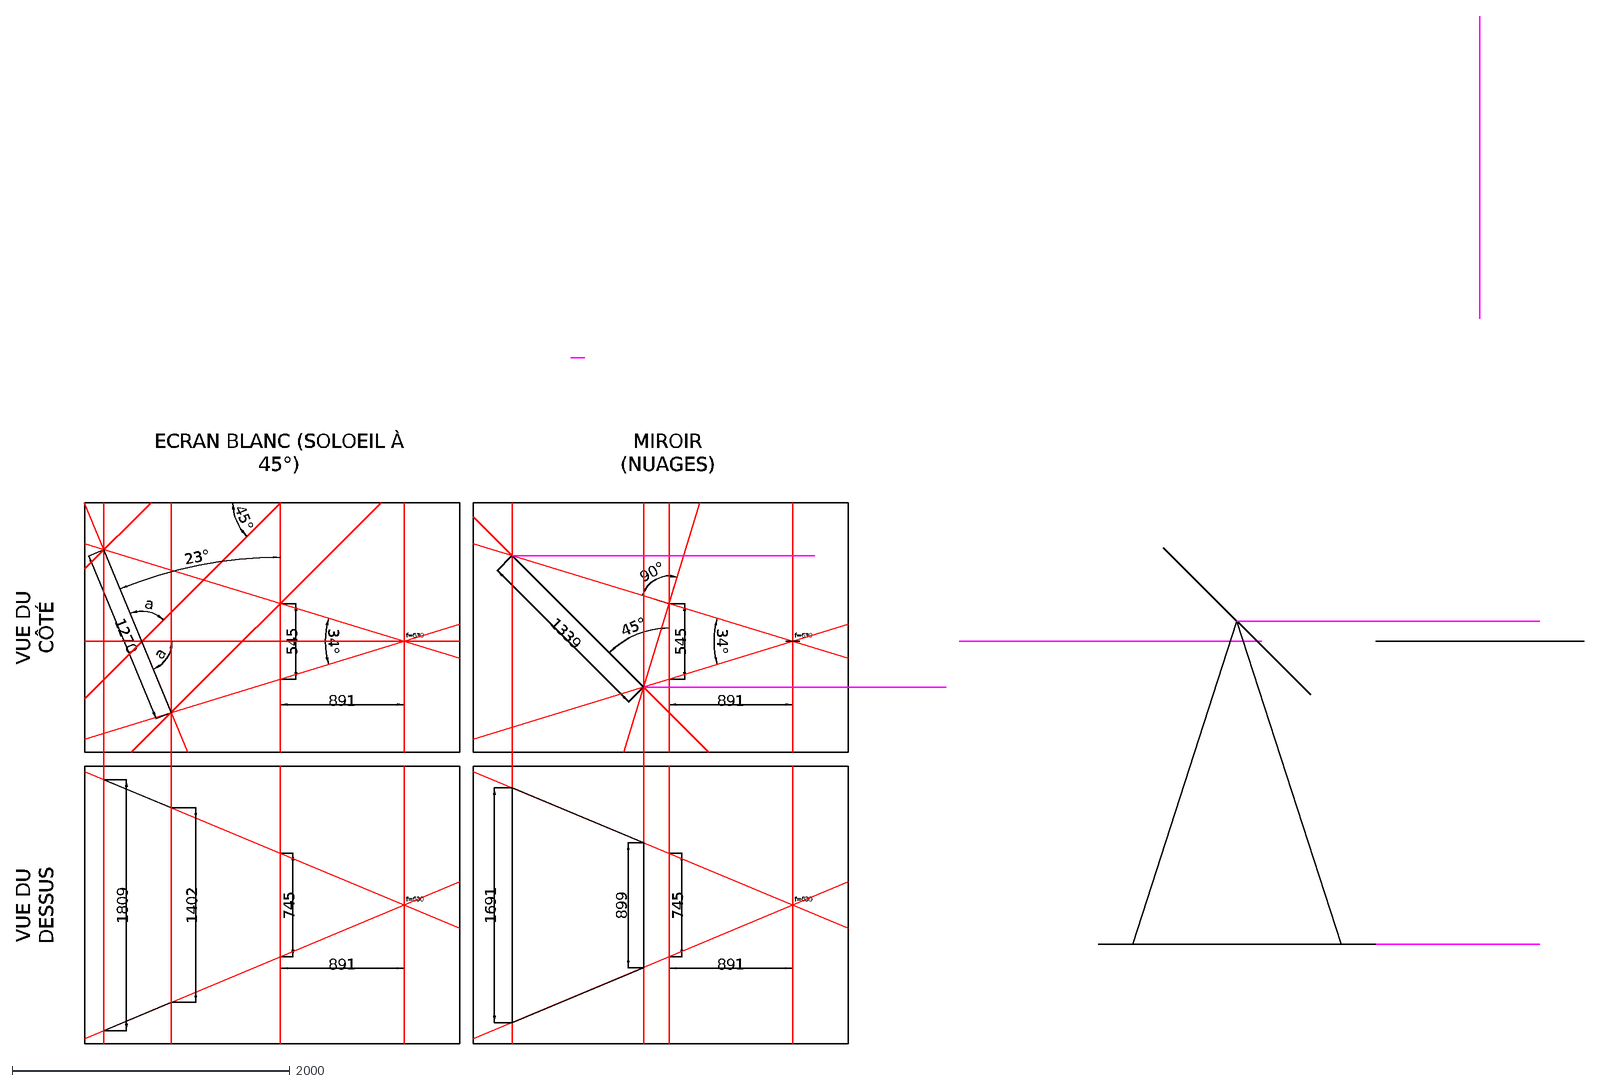
[picture p310: CAD file, 2024-03-05]
contenu/plans/plaques-reflecteurs.dxf
891
f=630
745
1339
545
34°
45°
90°
1691
1270
a
1809
1402
23°
VUE DU DESSUS
VUE DU CÔTÉ
MIROIR (NUAGES)
ECRAN BLANC (SOLOEIL À 45°)
899
