LeonLenclos/camera-obscura/contenu/animations/colo/020.dxf

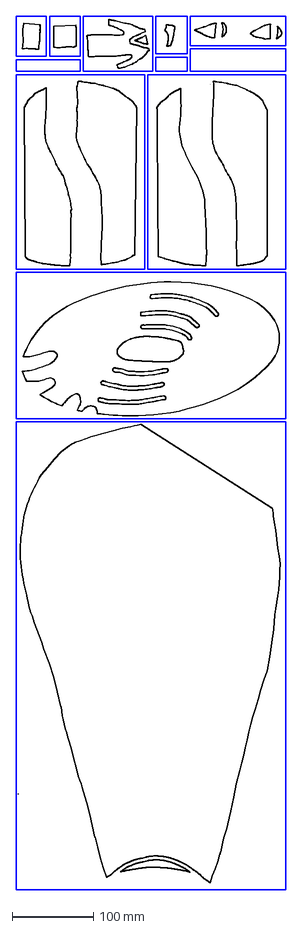
[picture p311: CAD file, 2024-04-03]
contenu/animations/colo/020.dxf
331.0 x 1071.8 mm
