LeonLenclos/camera-obscura/contenu/animations/plexi/trans3-7.dxf

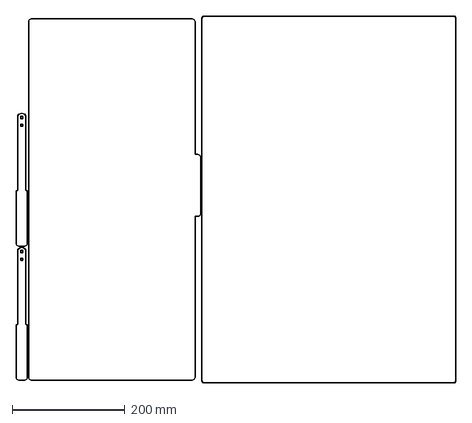
[picture p312: CAD file, 2024-04-01]
contenu/animations/plexi/trans3-7.dxf
779.0 x 650.0 mm
