LeonLenclos/camera-obscura/contenu/plans/fut80V1-laser.dxf

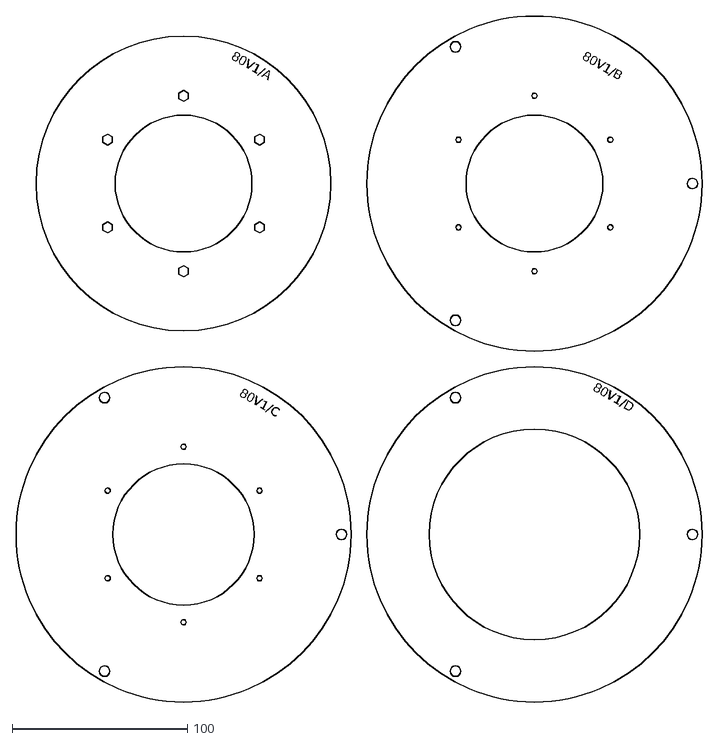
[picture p313: CAD file, 2024-03-05]
contenu/plans/fut80V1-laser.dxf
80V1/B
80V1/A
80V1/D
80V1/C
