LeonLenclos/camera-obscura/contenu/animations/colo/061-moyen.dxf

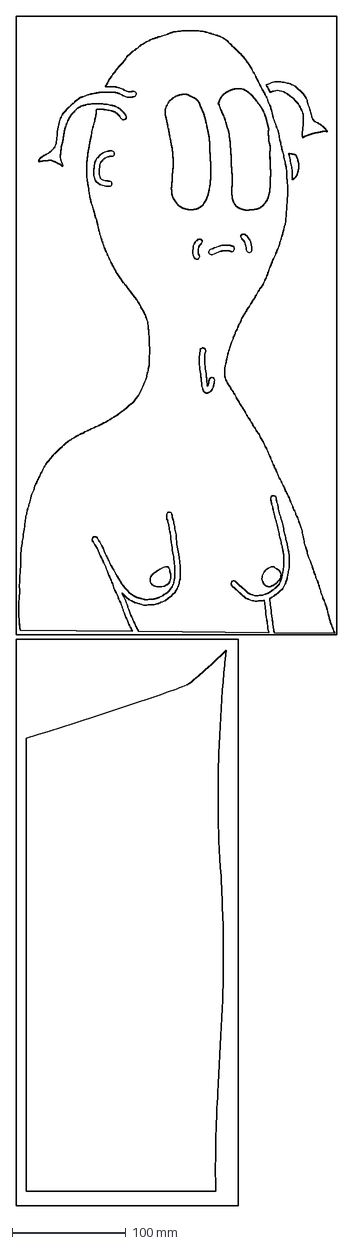
[picture p314: CAD file, 2024-04-03]
contenu/animations/colo/061-moyen.dxf
282.4 x 1047.5 mm
