LeonLenclos/camera-obscura/contenu/animations/plexi/trans3-4.dxf

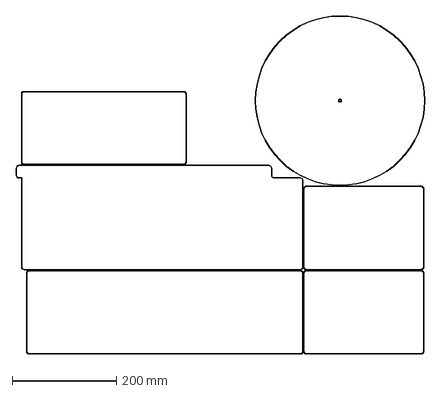
[picture p315: CAD file, 2024-04-01]
contenu/animations/plexi/trans3-4.dxf
784.0 x 649.0 mm
