LeonLenclos/camera-obscura/contenu/plans/fut154V1-laser.dxf

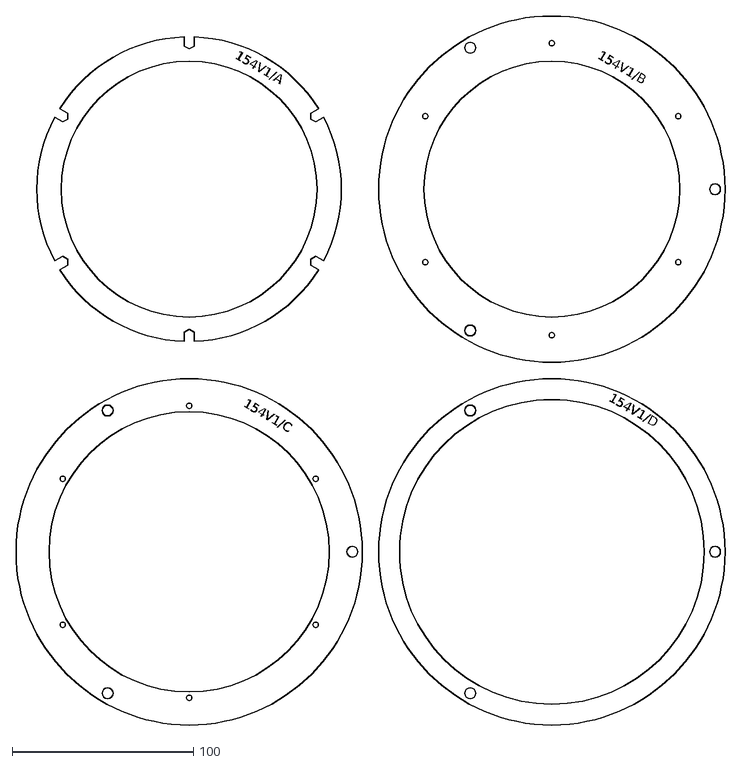
[picture p316: CAD file, 2024-03-05]
contenu/plans/fut154V1-laser.dxf
154V1/A
154V1/B
154V1/D
154V1/C
