LeonLenclos/camera-obscura/contenu/animations/colo/031.dxf

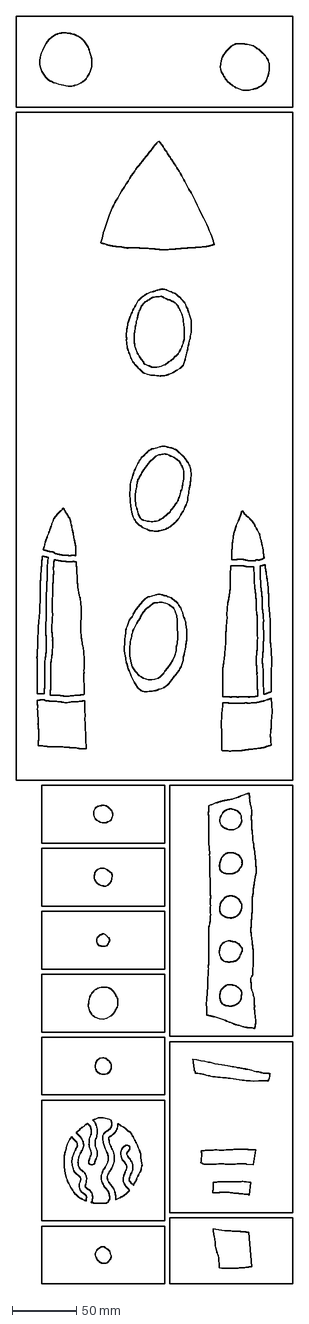
[picture p317: CAD file, 2024-04-03]
contenu/animations/colo/031.dxf
216.0 x 989.1 mm
