LeonLenclos/camera-obscura/contenu/animations/plexi/noir3-2.dxf

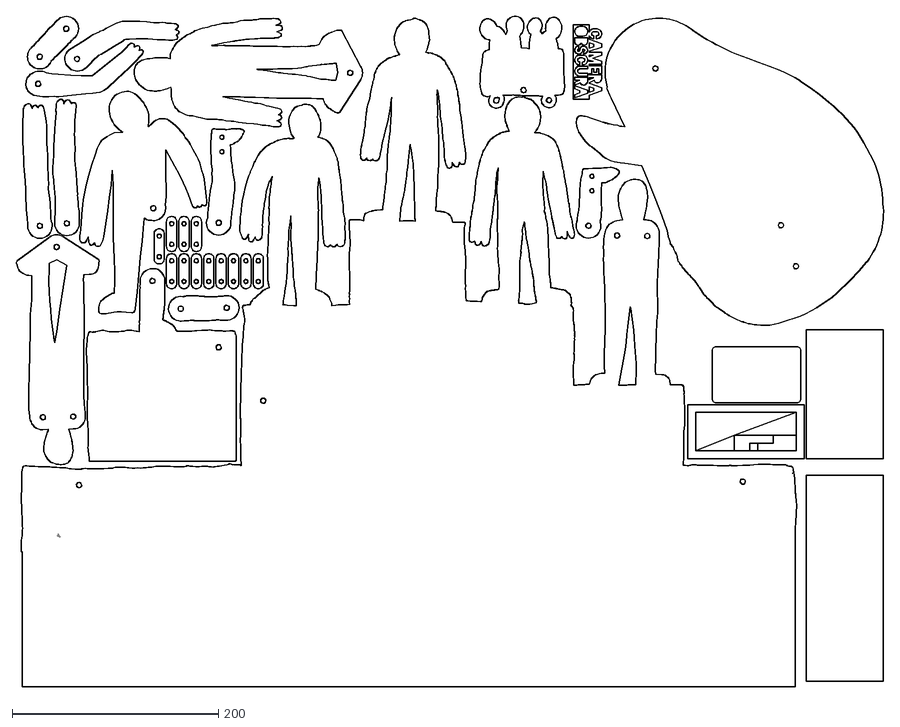
[picture p318: CAD file, 2024-04-01]
contenu/animations/plexi/noir3-2.dxf
840.3 x 649.9
