LeonLenclos/camera-obscura/contenu/plans/arbres-usinage.dxf

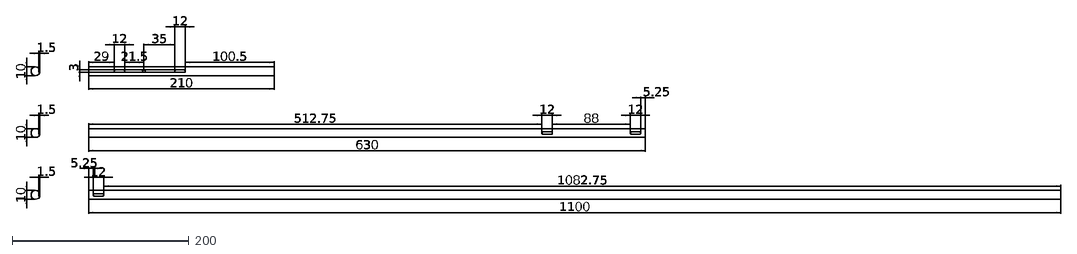
[picture p319: CAD file, 2024-03-02]
contenu/plans/arbres-usinage.dxf
210
21.5
29
12
512.75
88
5.25
630
1082.75
1100
1.5
10
3
35
100.5
