LeonLenclos/camera-obscura/contenu/animations/colo/M_031.dxf

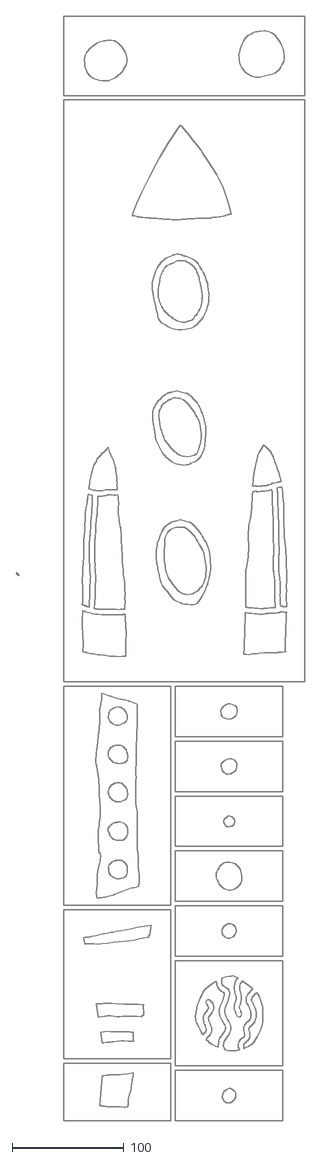
[picture p320: CAD file, 2024-04-03]
contenu/animations/colo/M_031.dxf
258.8 x 989.1
