LeonLenclos/camera-obscura/contenu/animations/plexi/trans3-2.dxf

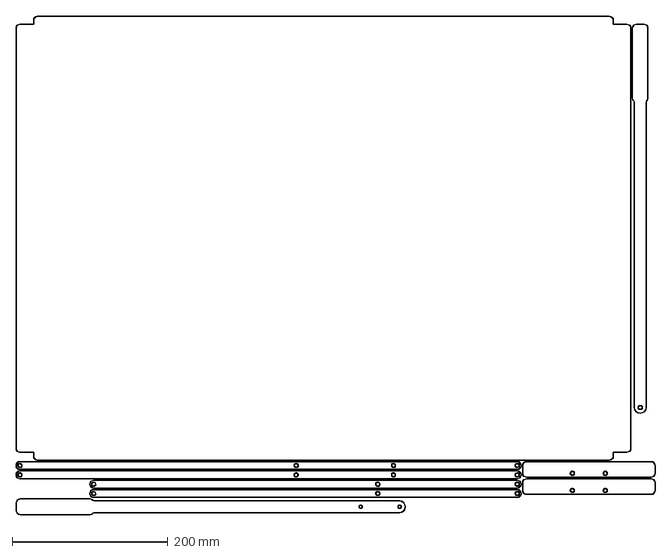
[picture p321: CAD file, 2024-04-01]
contenu/animations/plexi/trans3-2.dxf
821.0 x 640.0 mm
