LeonLenclos/camera-obscura/contenu/animations/colo/070.dxf

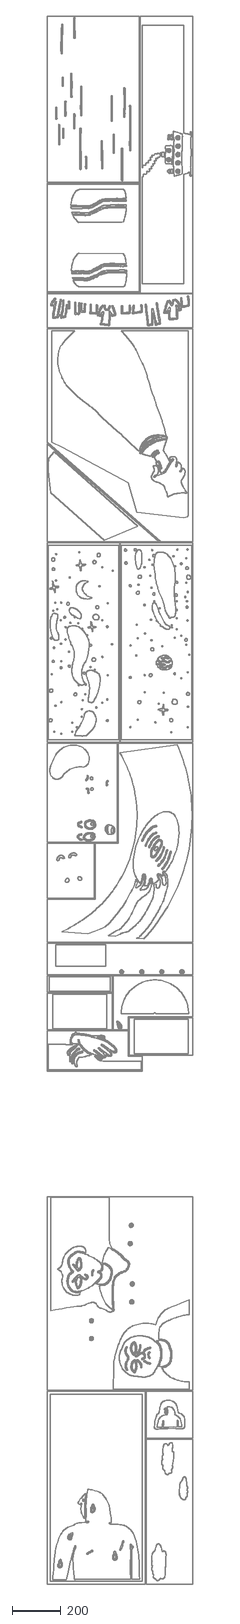
[picture p322: CAD file, 2024-04-01]
contenu/animations/colo/070.dxf
596.0 x 6409.8
