LeonLenclos/camera-obscura/contenu/plans/tourelle.dxf

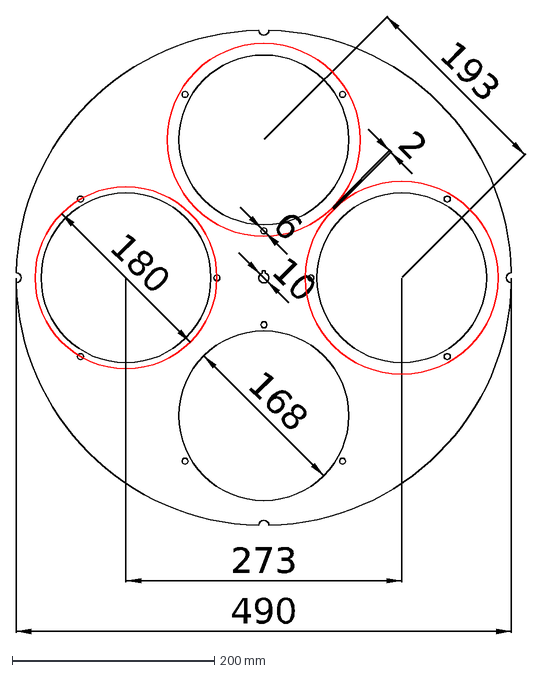
[picture p323: CAD file, 2024-02-23]
contenu/plans/tourelle.dxf
168
10
180
193
273
490
2
6
