LeonLenclos/camera-obscura/contenu/animations/colo/073.dxf

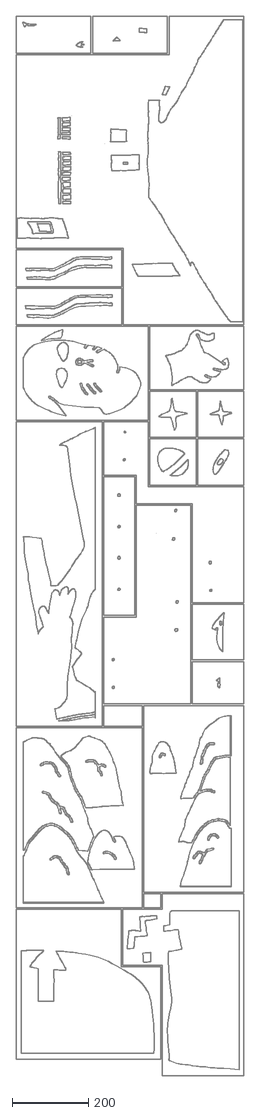
[picture p324: CAD file, 2024-04-01]
contenu/animations/colo/073.dxf
596.0 x 2770.0
