LeonLenclos/camera-obscura/contenu/plans/toit-amici-structure.dxf

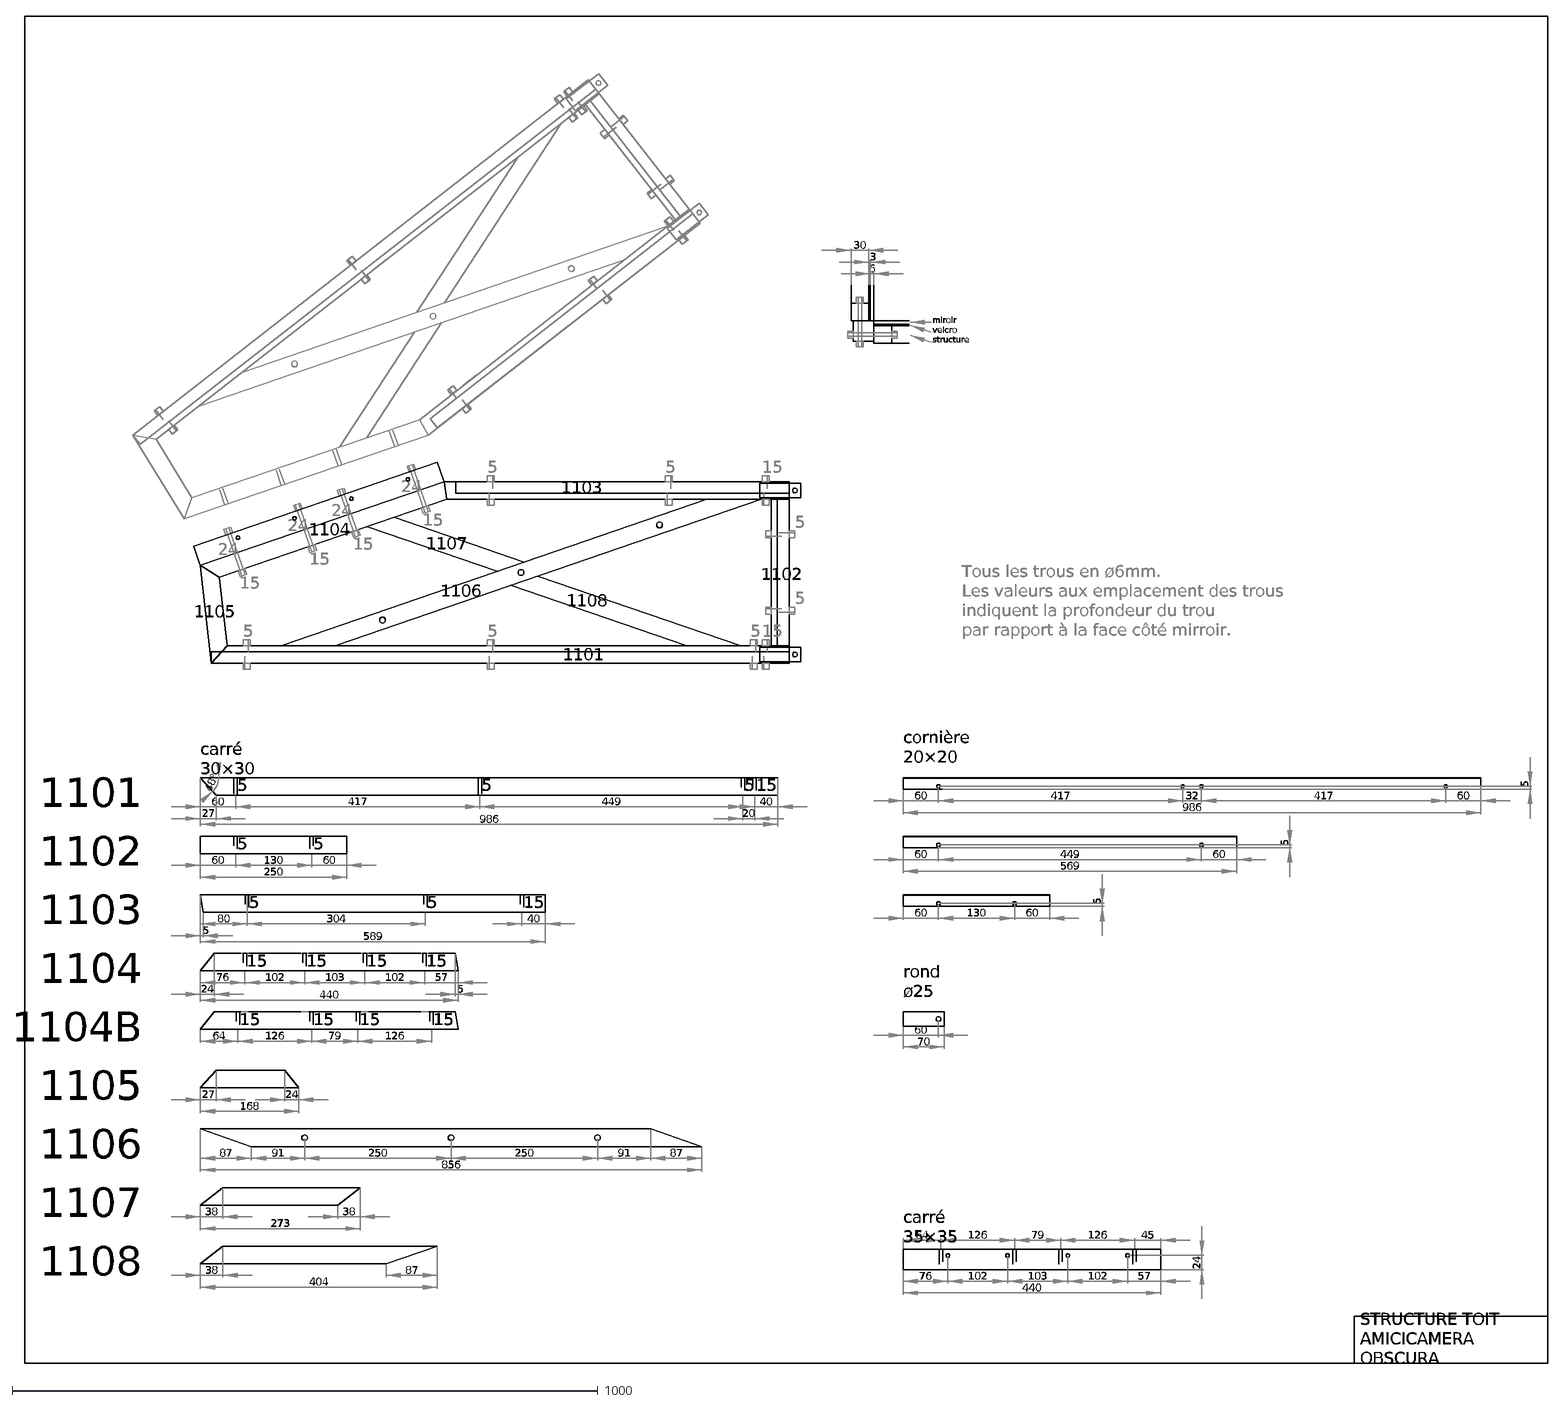
[picture p325: CAD file, 2024-02-17]
contenu/plans/toit-amici-structure.dxf
15
5
miroir velcro structure
6
3
30
60
417
449
40
20
27
986
48°
carré 30×30
32
569
130
70
76
102
103
57
440
cornière 20×20
rond ø25
Tous les trous en ø6mm. Les valeurs aux emplacement des trous indiquent la profondeur du trou par rapport à la face côté mirroir.
250
80
589
304
1101
1102
1103
1108
1107
1106
1105
1104
24
168
87
856
38
273
404
91
1104B
126
64
79
45
carré 35×35
STRUCTURE TOIT AMICI CAMERA OBSCURA
