LeonLenclos/camera-obscura/contenu/animations/colo/061.dxf

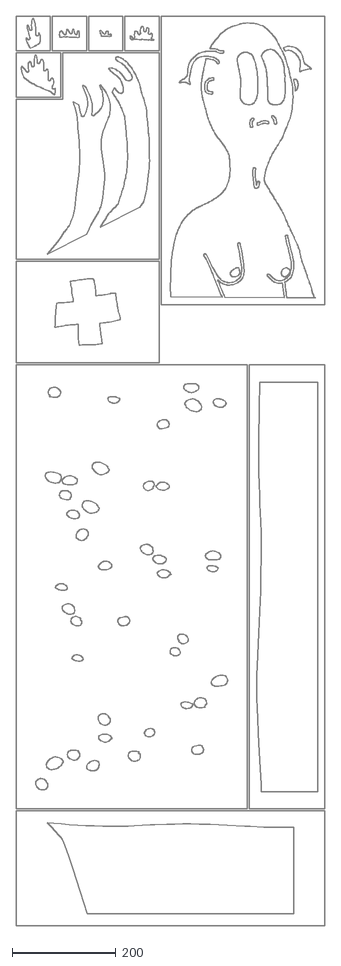
[picture p326: CAD file, 2024-04-01]
contenu/animations/colo/061.dxf
596.0 x 1754.3
