LeonLenclos/camera-obscura/contenu/plans/cage.dxf

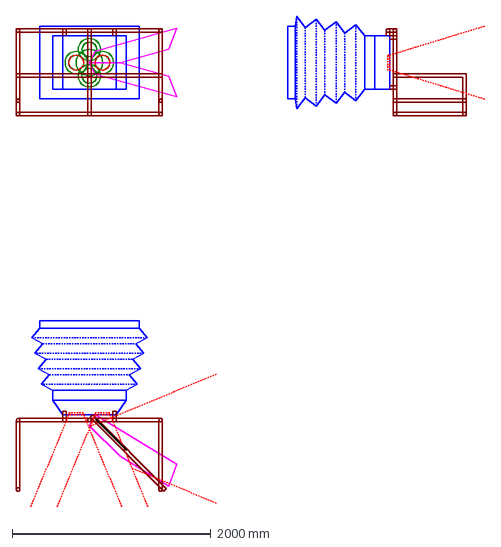
[picture p327: CAD file, 2024-02-14]
contenu/plans/cage.dxf
4716.3 x 4938.5 mm
