LeonLenclos/camera-obscura/contenu/animations/colo/074.dxf

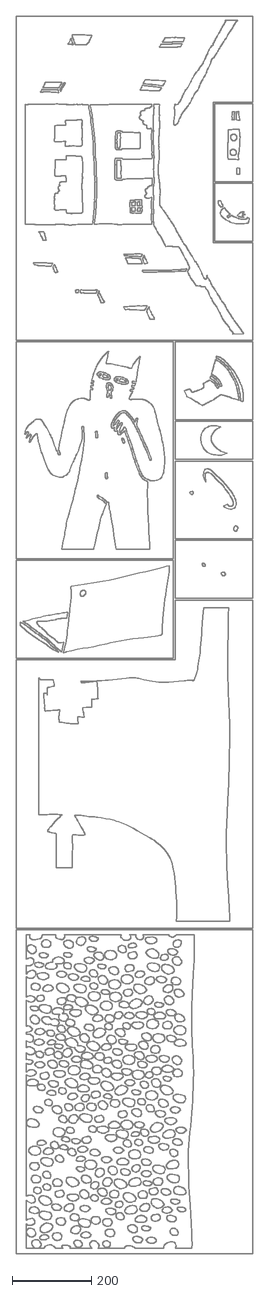
[picture p328: CAD file, 2024-04-01]
contenu/animations/colo/074.dxf
596.0 x 3116.0
