LeonLenclos/camera-obscura/contenu/plans/remorque-dimensions-constructeur.dxf

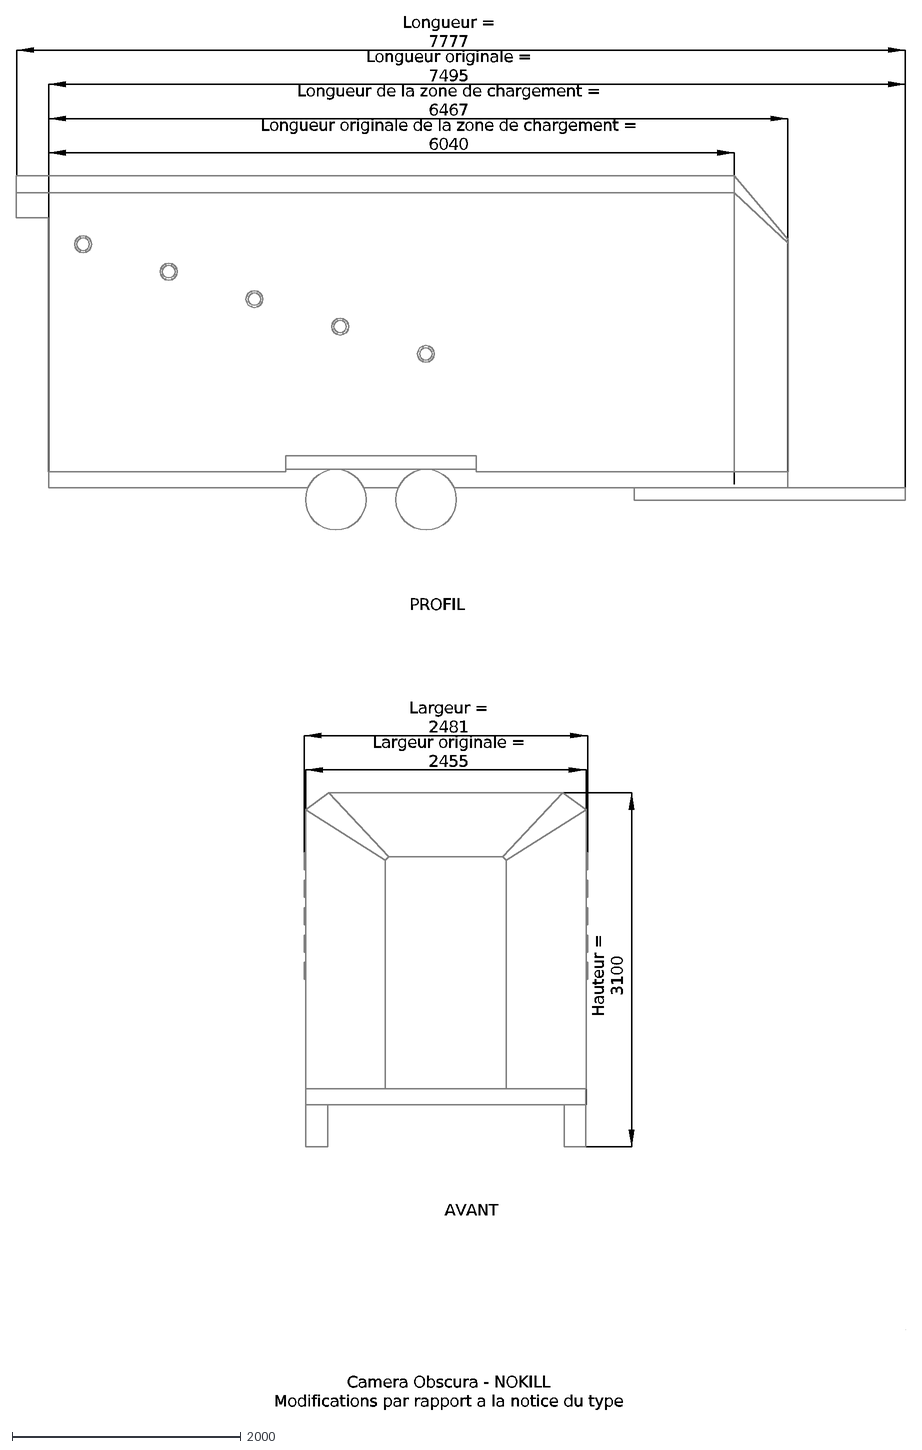
[picture p329: CAD file, 2024-01-15]
contenu/plans/remorque-dimensions-constructeur.dxf
PROFIL
2480
2455
Camera Obscura - NOKILL Modifications par rapport a la notice du type
3100
AVANT
6000
6467
7495
7777
Longueur = 7777
Longueur originale = 7495
Longueur de la zone de chargement = 6467
Longueur originale de la zone de chargement = 6040
Largeur = 2481
Largeur originale = 2455
Hauteur = 3100
