LeonLenclos/camera-obscura/contenu/animations/colo/053.dxf

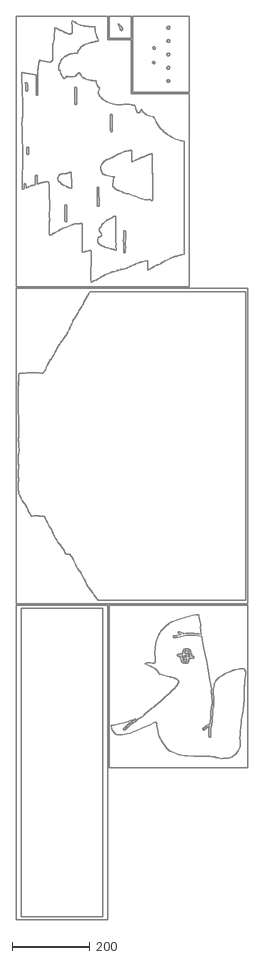
[picture p330: CAD file, 2024-04-01]
contenu/animations/colo/053.dxf
596.0 x 2325.4
