LeonLenclos/camera-obscura/contenu/plans/planchette-draft.dxf

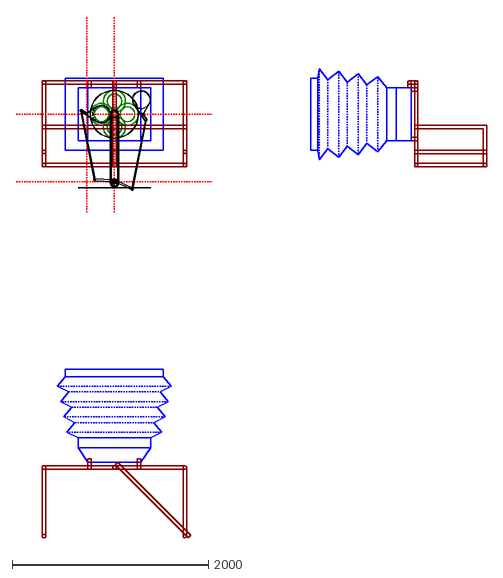
[picture p331: CAD file, 2024-01-10]
contenu/plans/planchette-draft.dxf
4795.0 x 5319.0
