LeonLenclos/camera-obscura/contenu/animations/colo/049.dxf

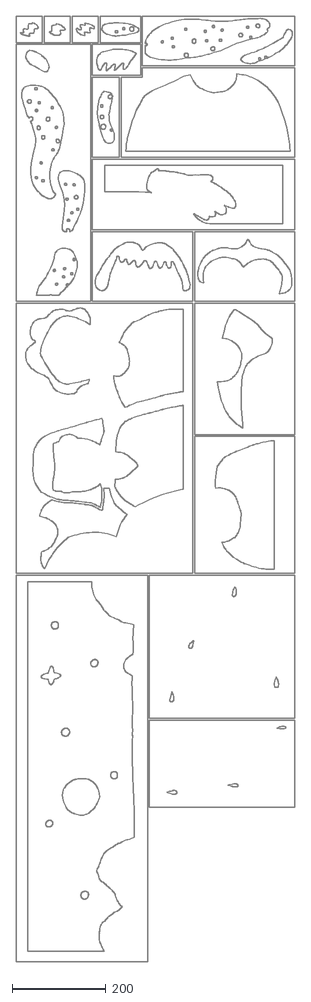
[picture p332: CAD file, 2024-04-01]
contenu/animations/colo/049.dxf
596.0 x 2020.8
