LeonLenclos/camera-obscura/contenu/plans/tapees.dxf

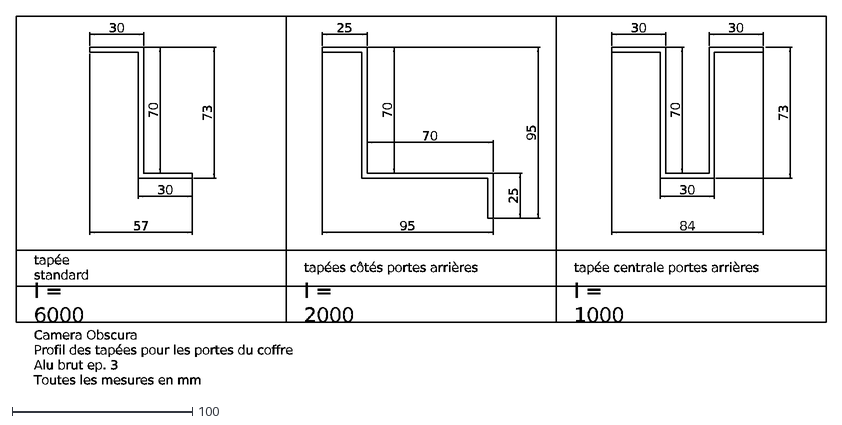
[picture p333: CAD file, 2023-12-10]
contenu/plans/tapees.dxf
25
70
95
30
tapées côtés portes arrières
tapée standard
tapée centrale portes arrières
l = 6000
l = 2000
l = 1000
73
57
84
Camera Obscura Profil des tapées pour les portes du coffre Alu brut ep. 3 Toutes les mesures en mm
