LeonLenclos/camera-obscura/contenu/plans/pieces-par-plaque-aquabriasion.dxf

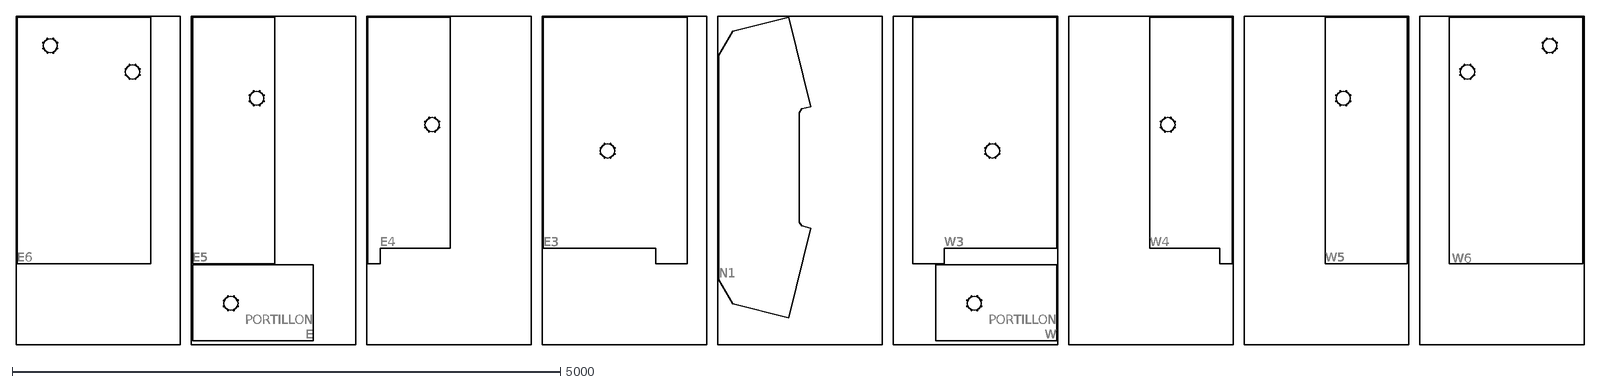
[picture p334: CAD file, 2023-10-09]
contenu/plans/pieces-par-plaque-aquabriasion.dxf
E6
E5
E4
E3
W3
W6
N1
PORTILLON E
PORTILLON W
W4
W5
