LeonLenclos/camera-obscura/contenu/plans/pieces-par-plaque-schiavon.dxf

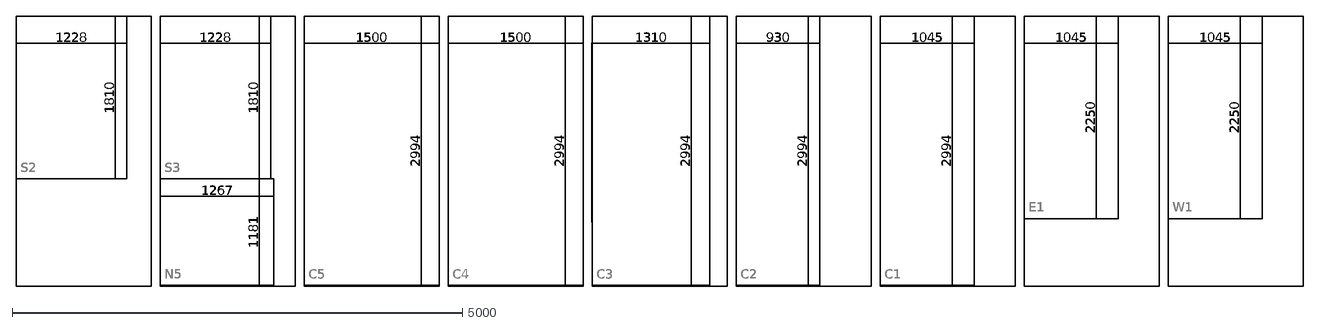
[picture p335: CAD file, 2023-10-09]
contenu/plans/pieces-par-plaque-schiavon.dxf
S2
S3
N5
C5
C4
C3
C2
C1
E1
W1
1810
1267
1181
2994
2250
1228
1500
1310
930
1045
