LeonLenclos/camera-obscura/contenu/plans/pieces-toles-schiavon.dxf

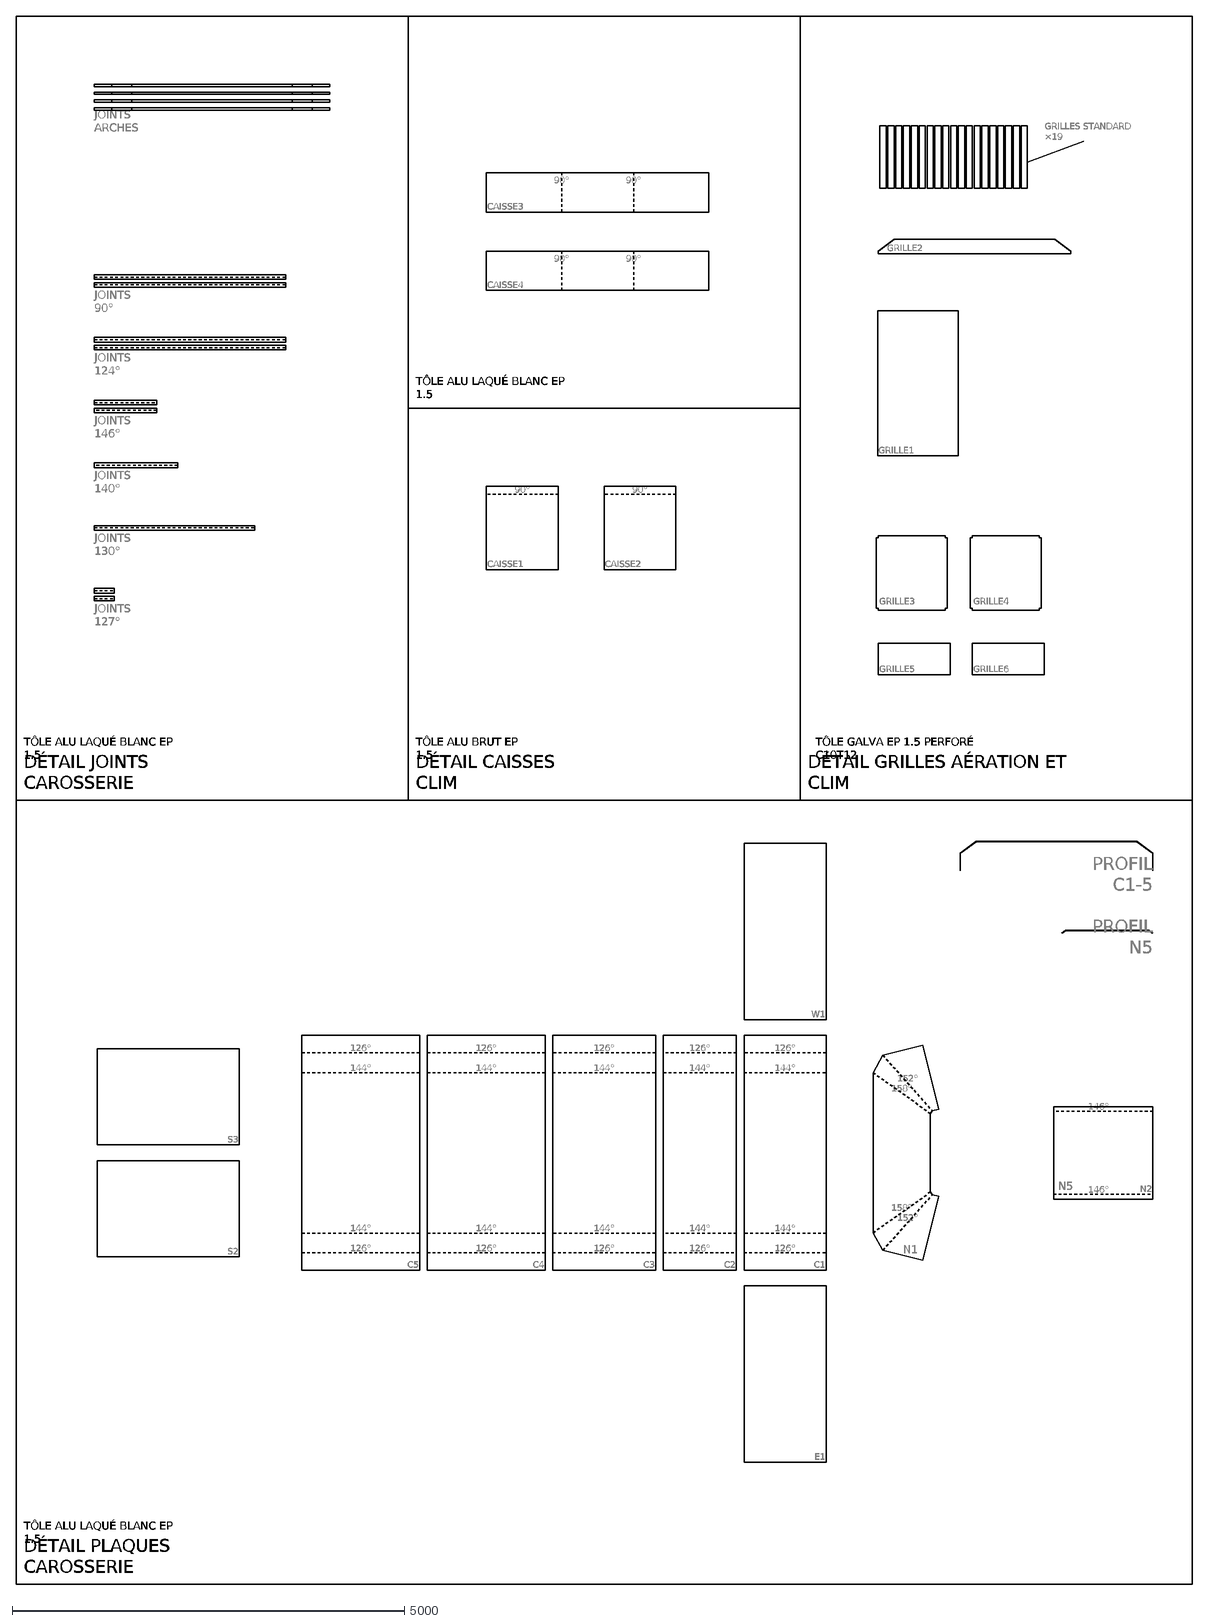
[picture p336: CAD file, 2023-10-06]
contenu/plans/pieces-toles-schiavon.dxf
C5
144°
126°
158°
152°
S2
S3
N2
146°
C4
C3
C2
C1
E1
W1
N1
N5
TÔLE ALU LAQUÉ BLANC EP 1.5
DÉTAIL PLAQUES CAROSSERIE
PROFIL C1-5
PROFIL N5
JOINTS 90°
JOINTS 124°
JOINTS 146°
JOINTS 140°
JOINTS 130°
JOINTS 127°
TÔLE ALU BRUT EP 1.5
TÔLE GALVA EP 1.5 PERFORÉ C10T12
DÉTAIL CAISSES CLIM
DÉTAIL JOINTS CAROSSERIE
DÉTAIL GRILLES AÉRATION ET CLIM
90°
CAISSE3
CAISSE4
GRILLE2
GRILLE1
GRILLE3
GRILLE4
GRILLE5
GRILLE6
GRILLES STANDARD ×19
JOINTS ARCHES
CAISSE1
CAISSE2
