LeonLenclos/camera-obscura/contenu/plans/remorque.dxf

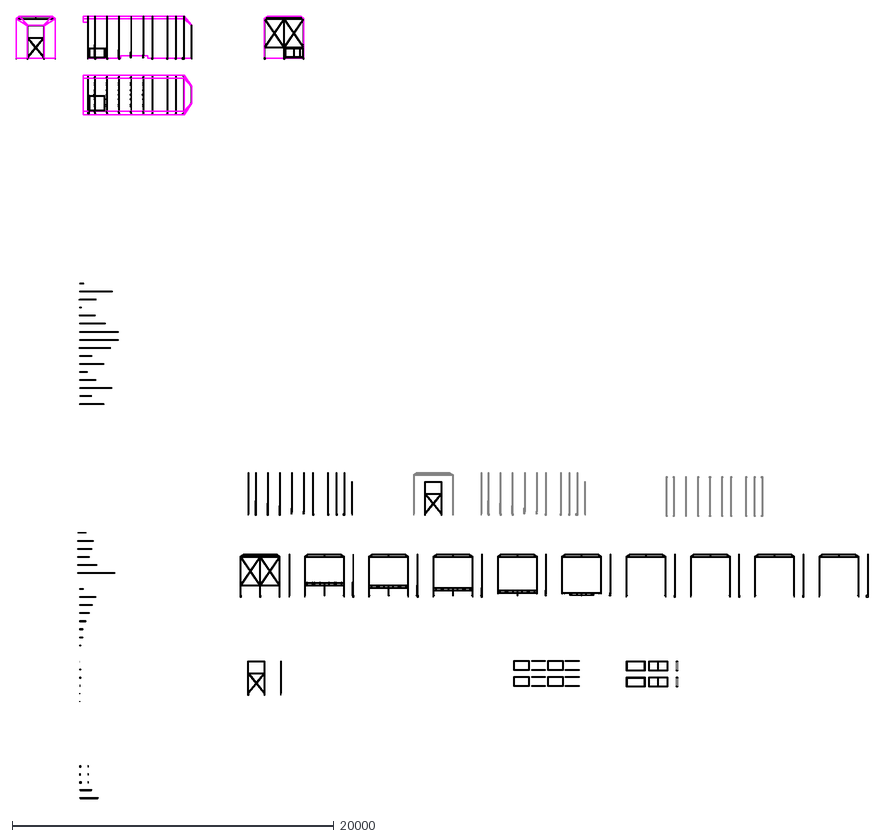
[picture p337: CAD file, 2023-09-22]
contenu/plans/remorque.dxf
52990.0 x 48650.0
