LeonLenclos/camera-obscura/contenu/plans/hublots.dxf

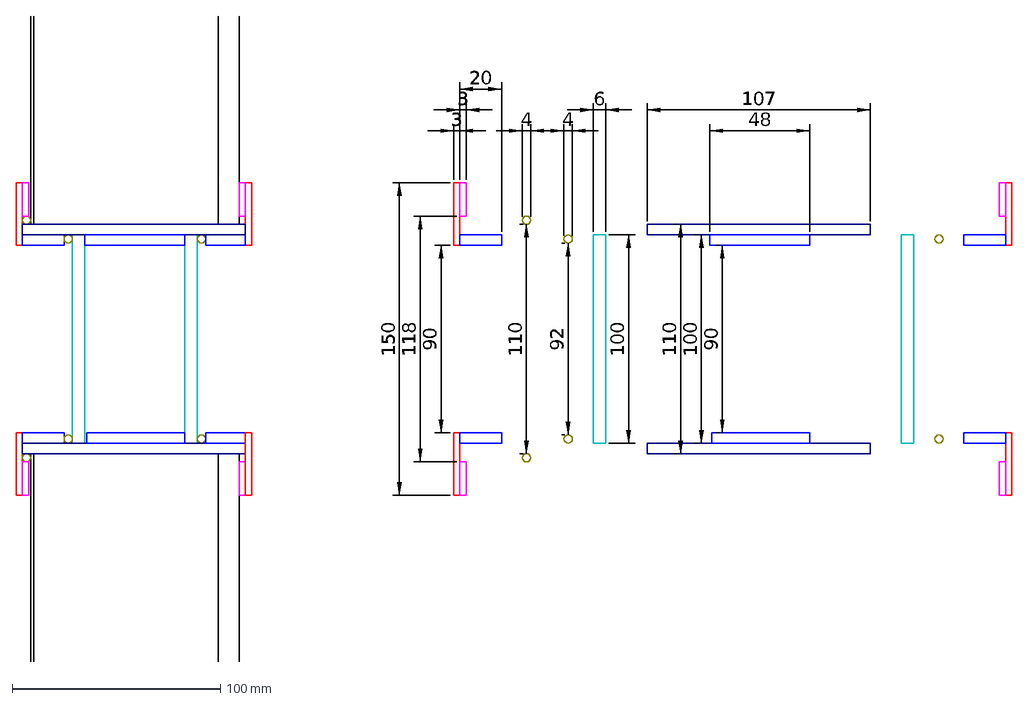
[picture p338: CAD file, 2023-09-20]
contenu/plans/hublots.dxf
92
110
100
90
118
150
3
20
4
6
48
107
