LeonLenclos/camera-obscura/contenu/plans/fauteuil.dxf

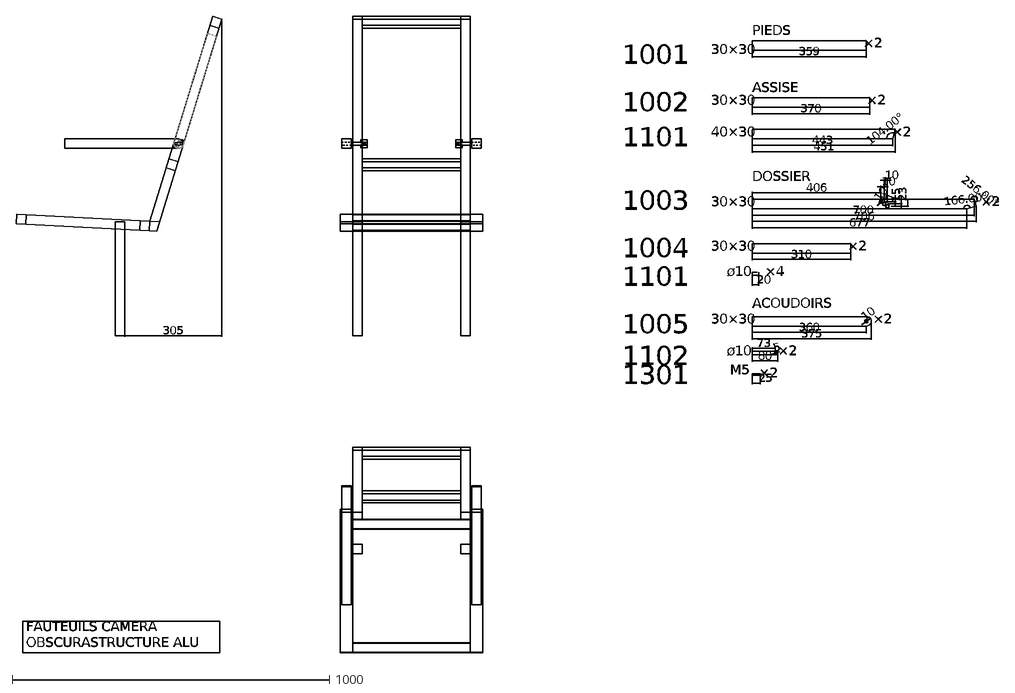
[picture p339: CAD file, 2023-09-05]
contenu/plans/fauteuil.dxf
×2
PIEDS
ASSISE
359
370
443
451
104.00°
40×30
30×30
700
677
706
166.00°
256.00°
310
406
10
7
15
23
20
ø10
×4
DOSSIER
360
375
80
73
5
25
ACOUDOIRS
FAUTEUILS CAMERA OBSCURA STRUCTURE ALU
305
1001
1002
1101
1003
1004
1005
1102
1301
M5
