LeonLenclos/camera-obscura/contenu/plans/toit-amici-2.dxf

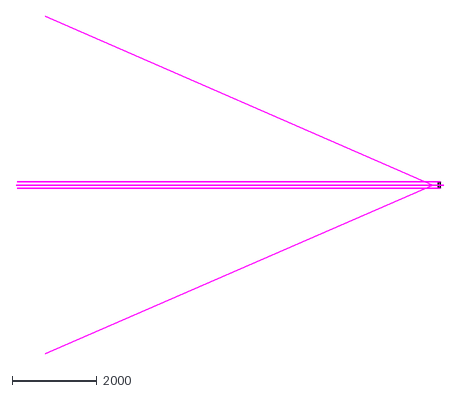
[picture p340: CAD file, 2023-07-27]
contenu/plans/toit-amici-2.dxf
10100.0 x 7975.0
