LeonLenclos/camera-obscura/contenu/plans/maquette.dxf

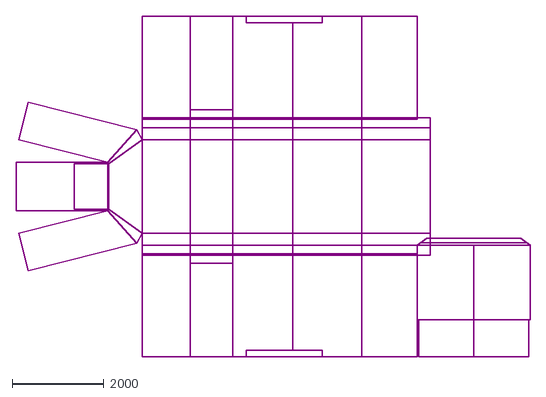
[picture p341: CAD file, 2023-07-27]
contenu/plans/maquette.dxf
11220.0 x 7434.0
