LeonLenclos/camera-obscura/contenu/plans/mirroir-a-45-structure.dxf

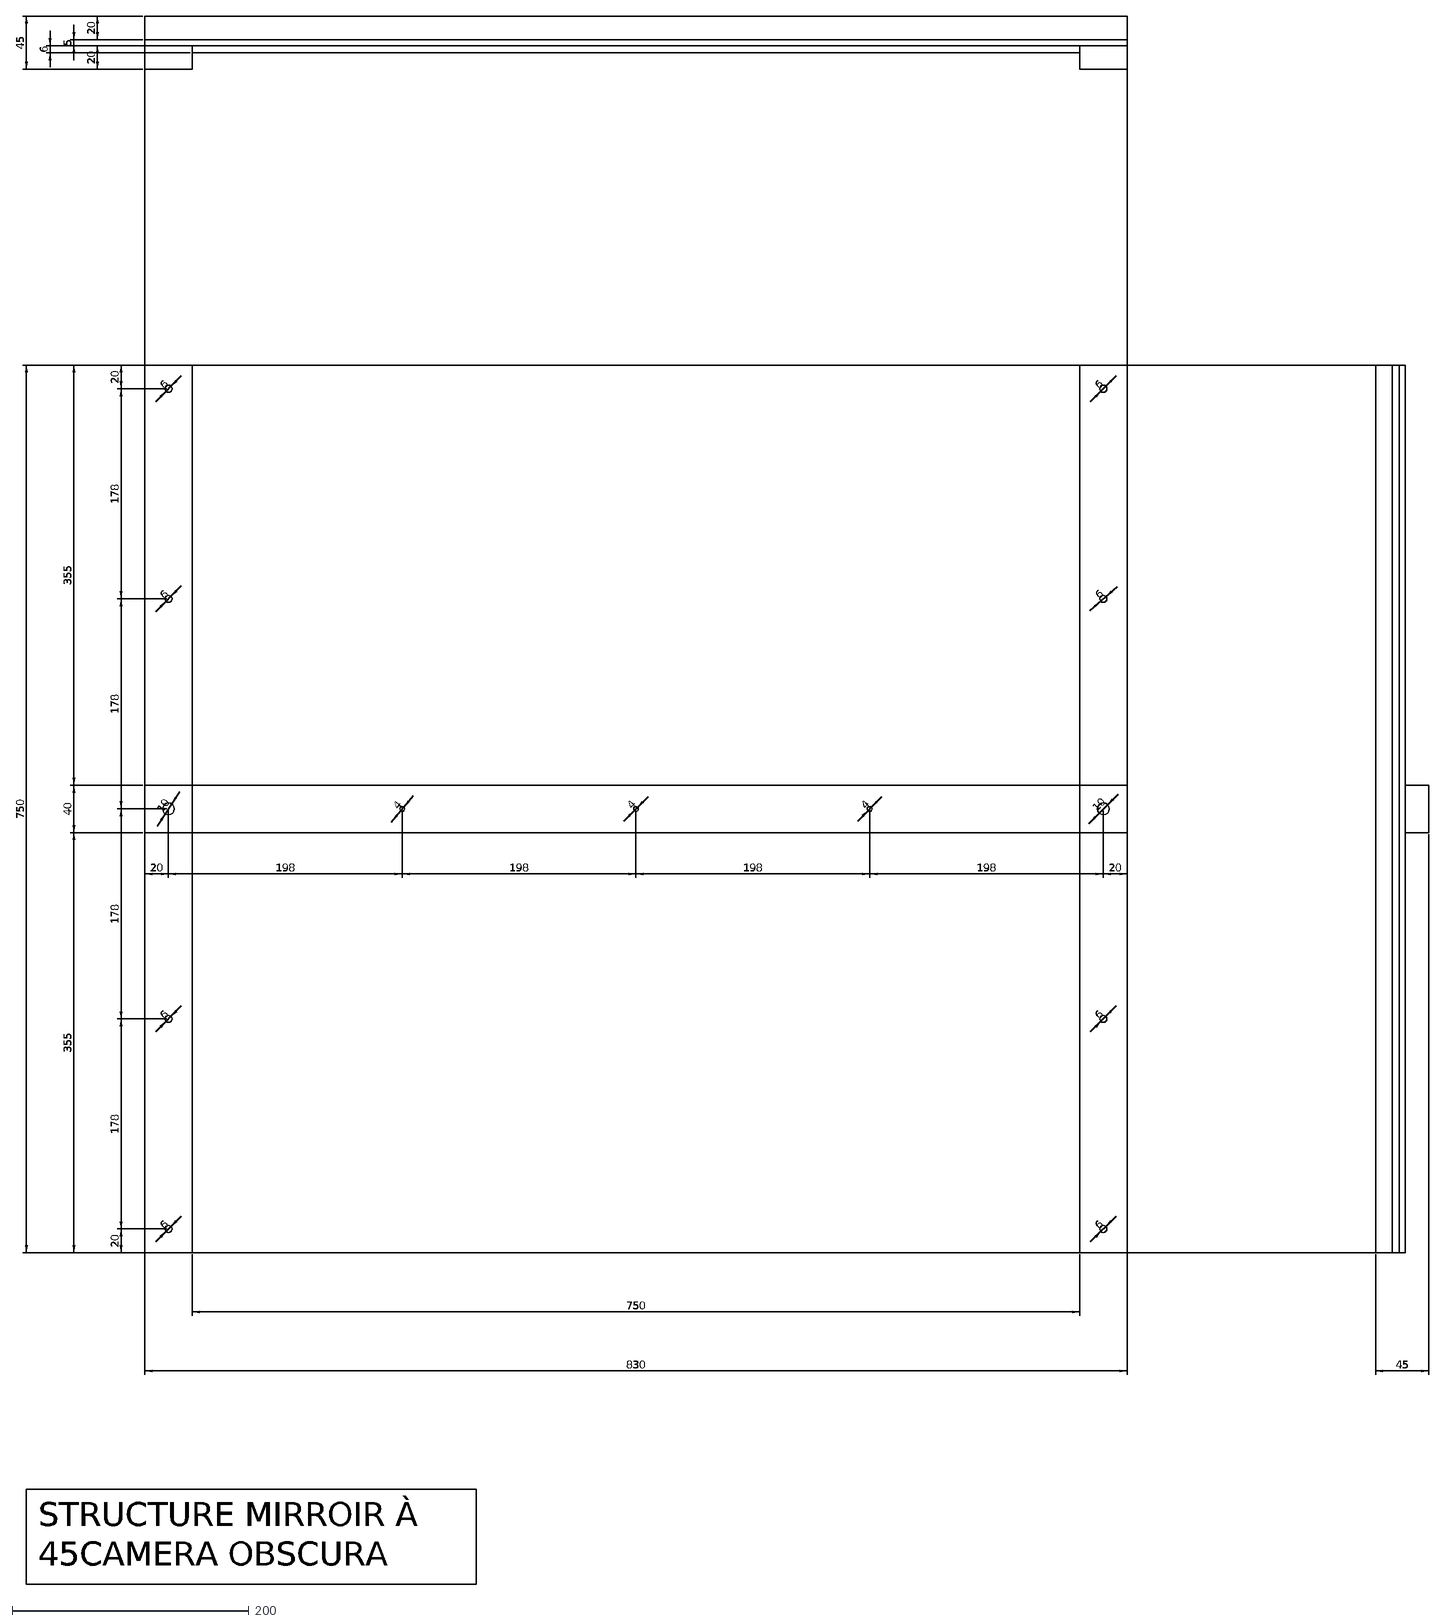
[picture p342: CAD file, 2023-07-14]
contenu/plans/mirroir-a-45-structure.dxf
830
750
20
178
6
5
198
45
355
40
10
4
STRUCTURE MIRROIR À 45 CAMERA OBSCURA
