LeonLenclos/camera-obscura/contenu/plans/mirroir-a-45.dxf

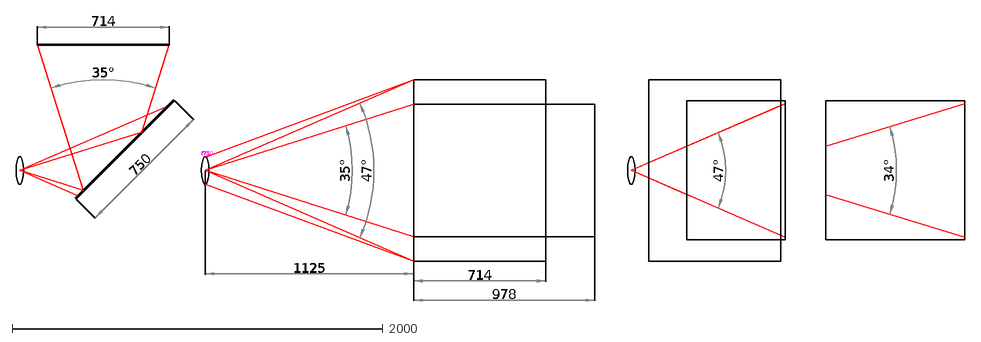
[picture p343: CAD file, 2023-06-07]
contenu/plans/mirroir-a-45.dxf
35°
714
750
47°
1125
978
34°
f750
