LeonLenclos/camera-obscura/contenu/plans/toit-amici-decoupe-miroir.dxf

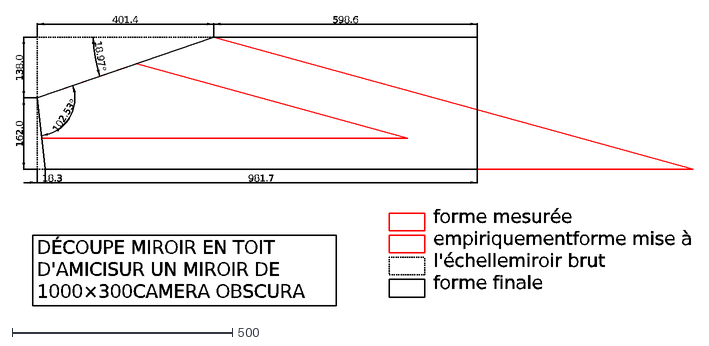
[picture p344: CAD file, 2023-06-07]
contenu/plans/toit-amici-decoupe-miroir.dxf
forme mesurée empiriquement forme mise à l'échelle miroir brut forme finale
DÉCOUPE MIROIR EN TOIT D'AMICI SUR UN MIROIR DE 1000×300 CAMERA OBSCURA
162.0
138.0
401.4
598.6
18.97°
18.3
981.7
102.53°
