LeonLenclos/camera-obscura/contenu/plans/decoupe-miroir-en-toit.dxf

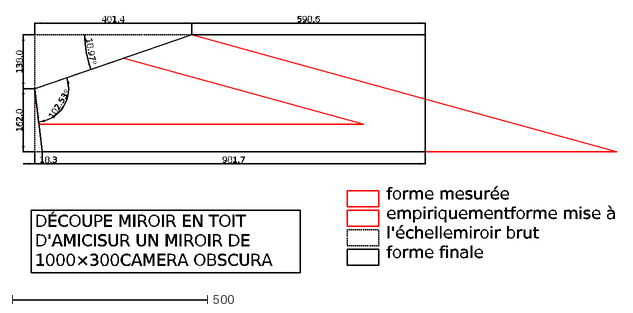
[picture p345: CAD file, 2023-06-07]
contenu/plans/decoupe-miroir-en-toit.dxf
forme mesurée empiriquement forme mise à l'échelle miroir brut forme finale
DÉCOUPE MIROIR EN TOIT D'AMICI SUR UN MIROIR DE 1000×300 CAMERA OBSCURA
162.0
138.0
401.4
598.6
18.97°
18.3
981.7
102.53°
