LeonLenclos/camera-obscura/contenu/objet/journal/img1.png

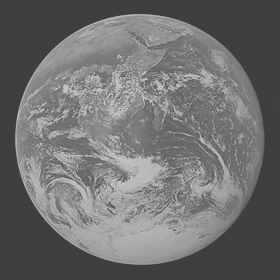
contenu/objet/journal/img1.png
