LeonLenclos/camera-obscura/contenu/objet/journal/img2.png

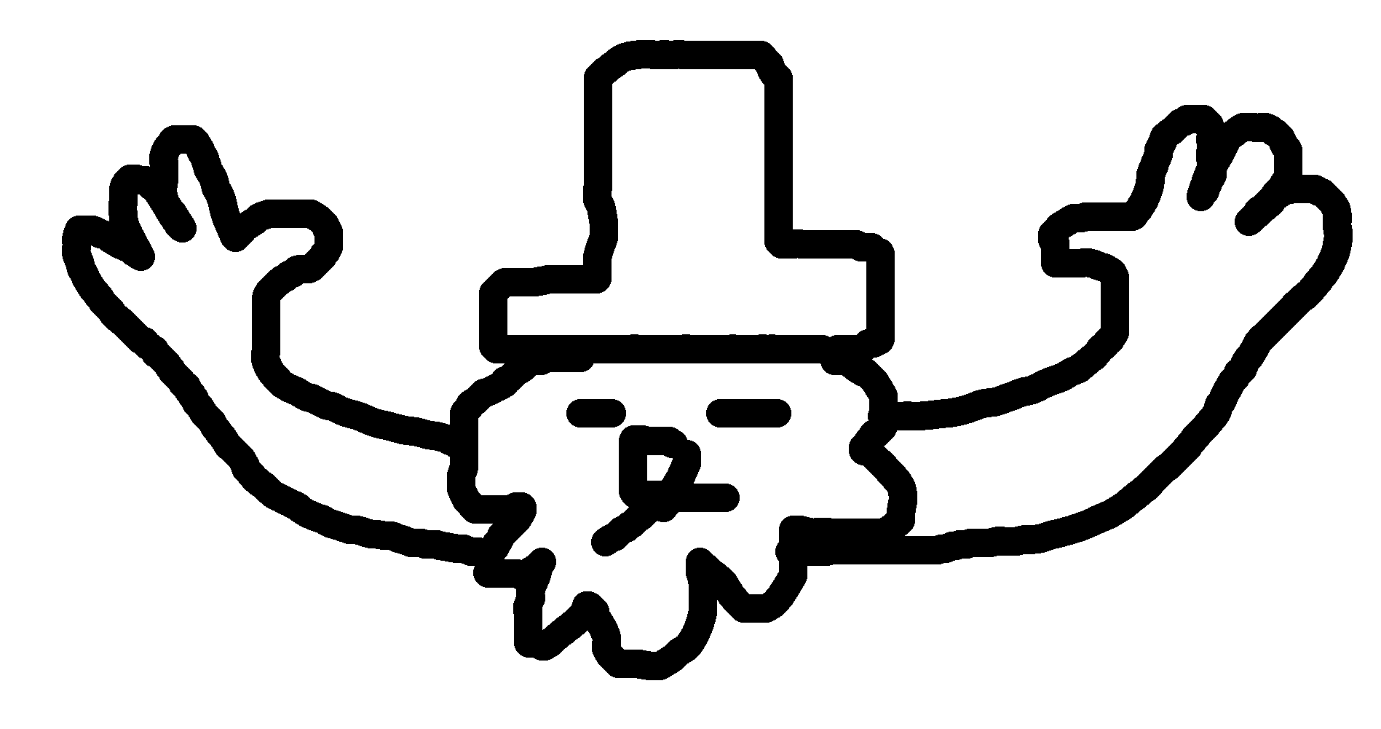
contenu/objet/journal/img2.png
