LeonLenclos/camera-obscura/contenu/objet/journal/img3.jpg

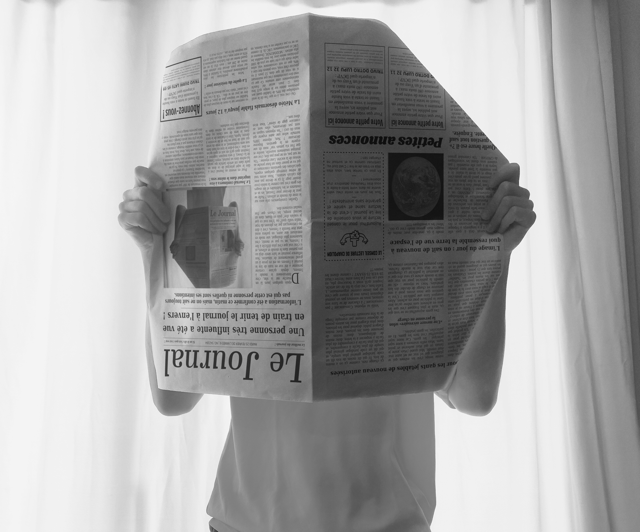
contenu/objet/journal/img3.jpg
