LeonLenclos/camera-obscura/contenu/plans/implantation-orientation-NO.pdf

## Schéma orientation NO — Implantation Camera Obscura — Cie NOKILL

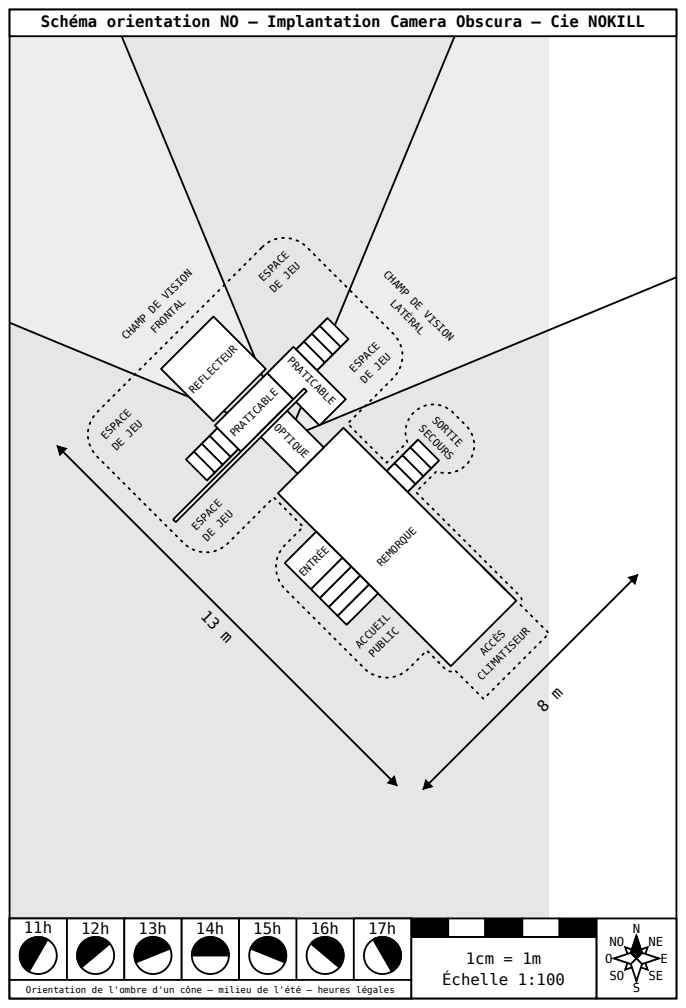
[picture p353: page 1]
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

CHAMP DE VISION

Orientation de l'ombre d'un cône — milieu de l'été — heures légales
