LeonLenclos/camera-obscura/contenu/plans/implantation-orientation-NE.pdf

## Schéma orientation NE — Implantation Camera Obscura — Cie NOKILL

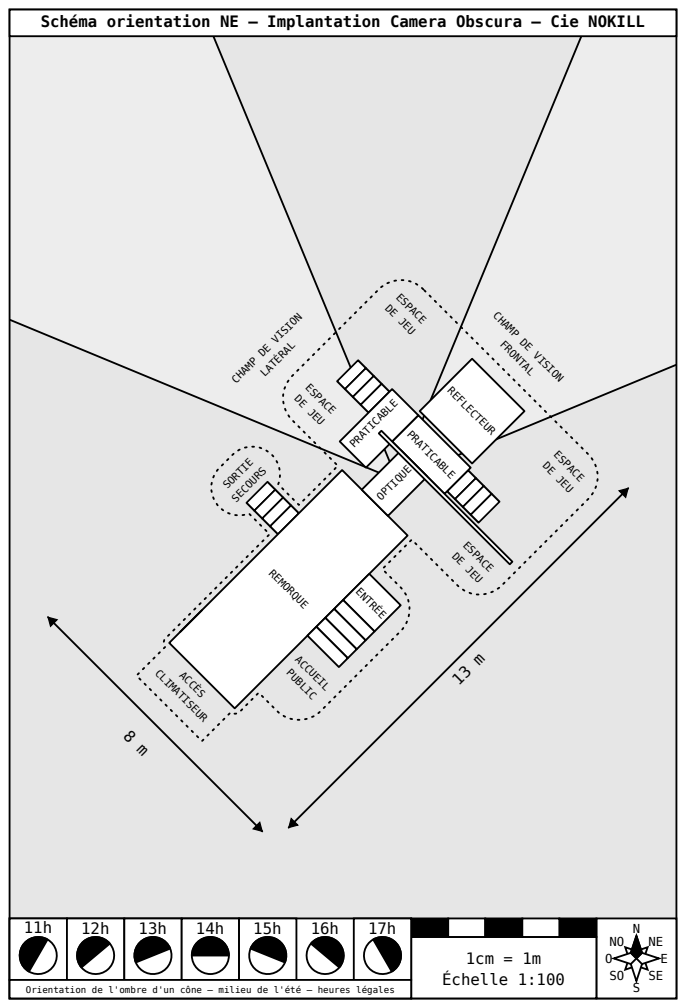
[picture p354: page 1]
PRATICABLE; REMORQUE; ENTRÉE; REFLECTEUR; OPTIQUE; ESPACE DE JEU; SORTIE SECOURS; ACCUEIL; CLIMATISEUR ACCÈS; PUBLIC; FRONTAL; LATÉRAL; Échelle 1:100

CHAMP DE VISION

Orientation de l'ombre d'un cône — milieu de l'été — heures légales
