LeonLenclos/camera-obscura/contenu/plans/remorque-aspect-doc.pdf

# rouleau_1 rouleau_2 rouleau_3 rouleau_4 rouleau_5

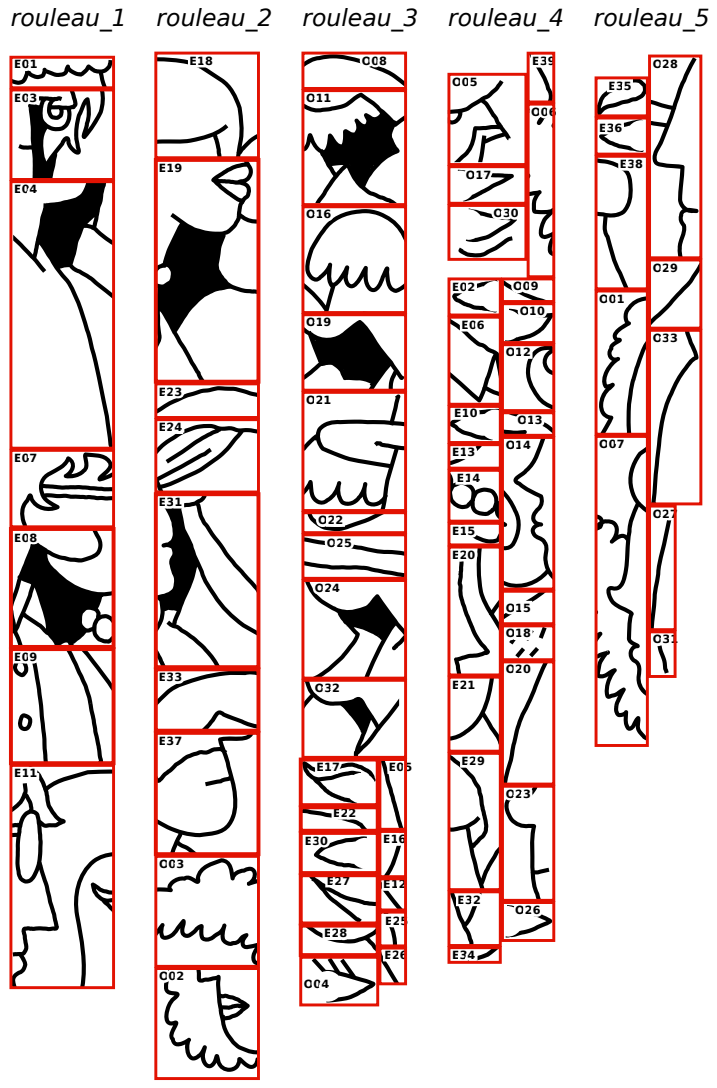
[picture p356: page 1]

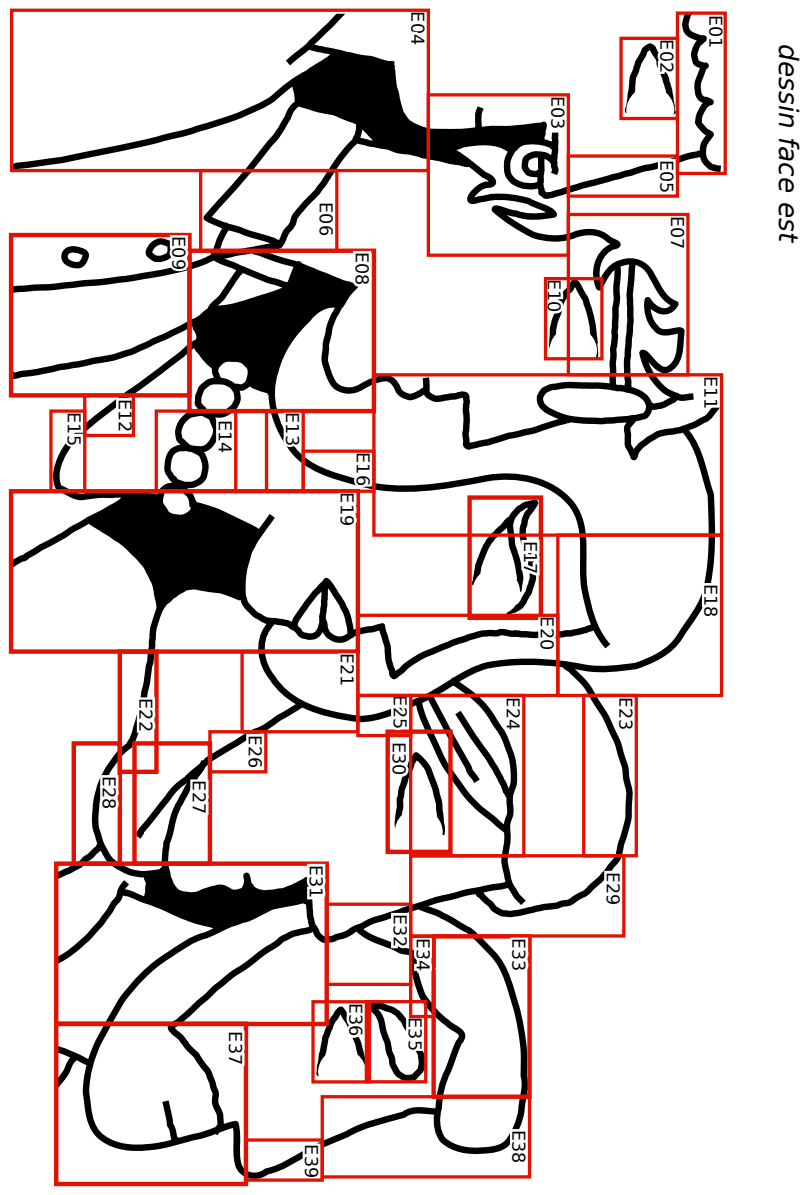
[picture p357: page 2]

dessin face est

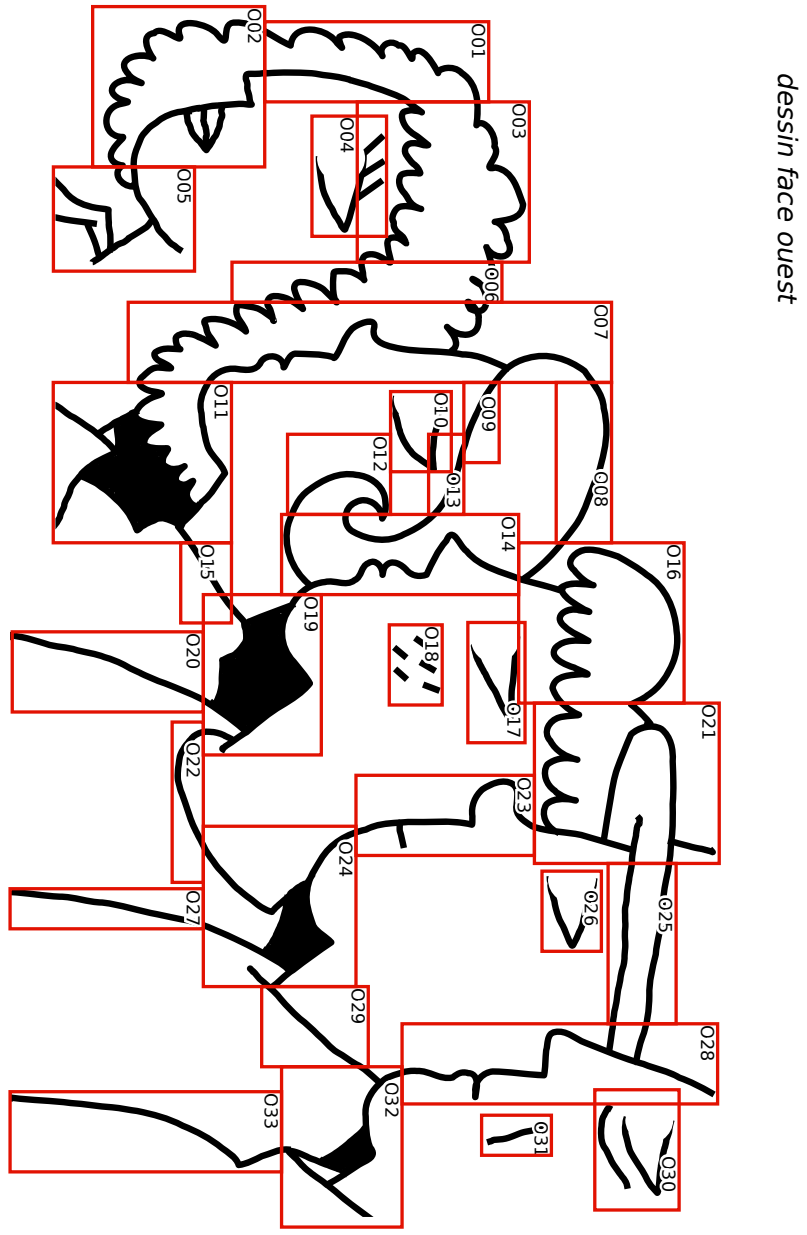
[picture p358: page 3]

dessin face ouest
