LeonLenclos/camera-obscura/contenu/plans/fut.pdf

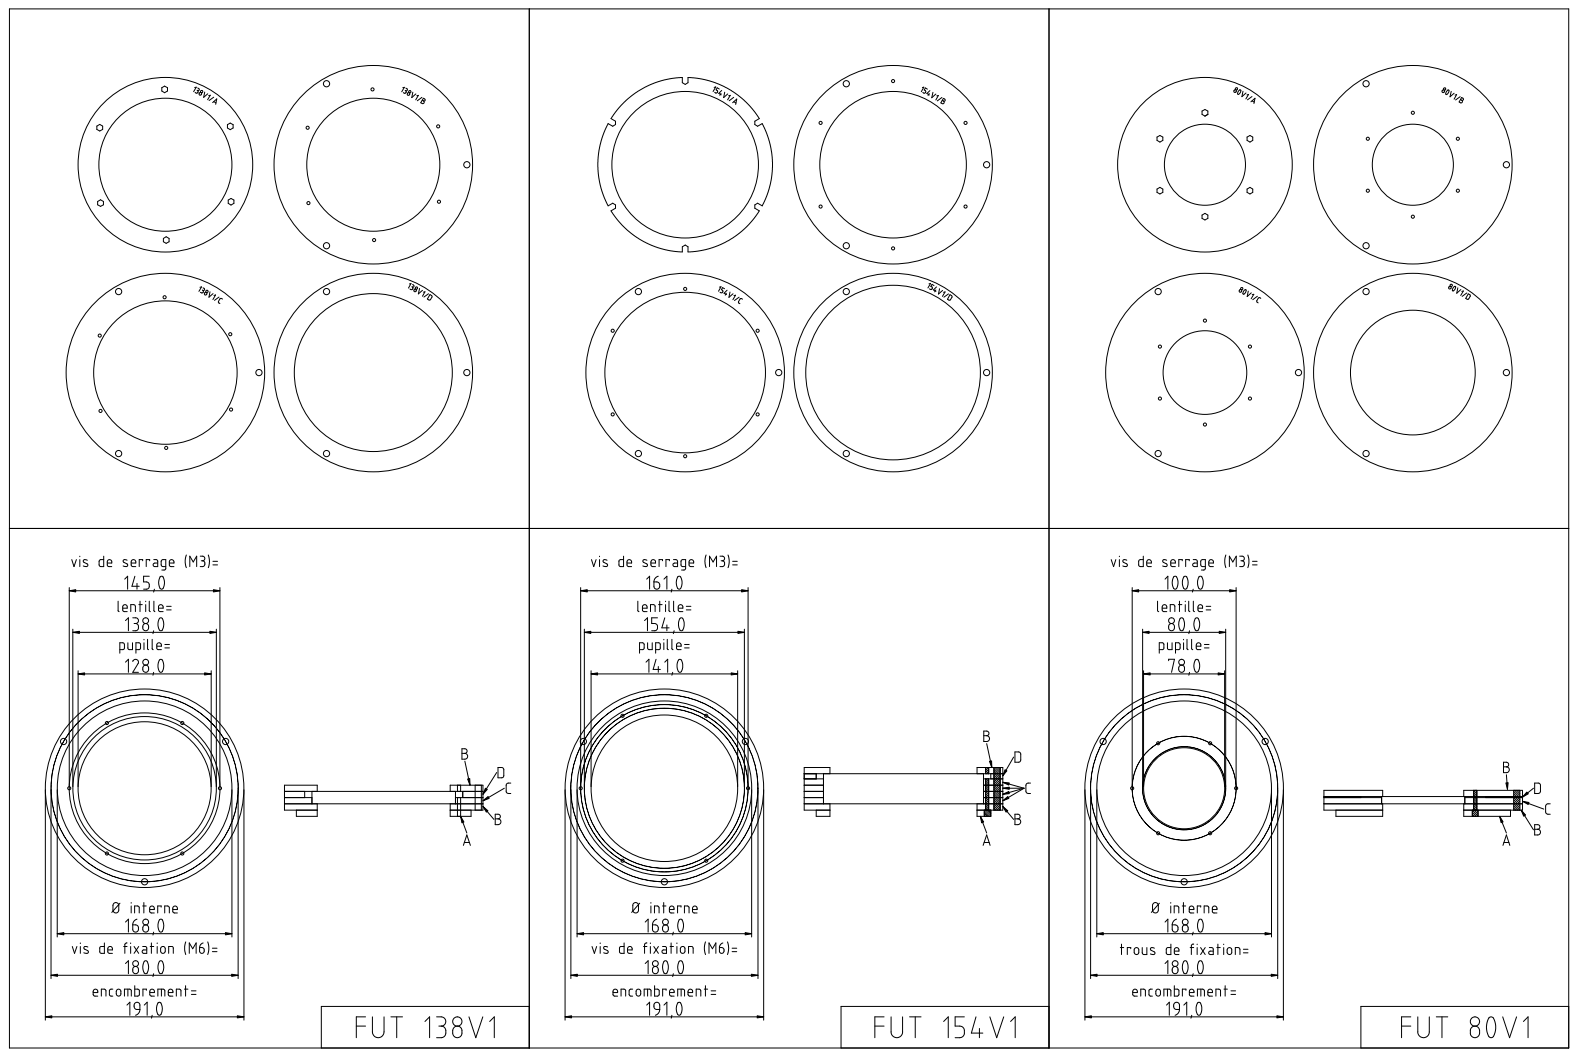
[picture p359: page 1]
