LeonLenclos/camera-obscura/contenu/plans/obturateur-patron-1.pdf

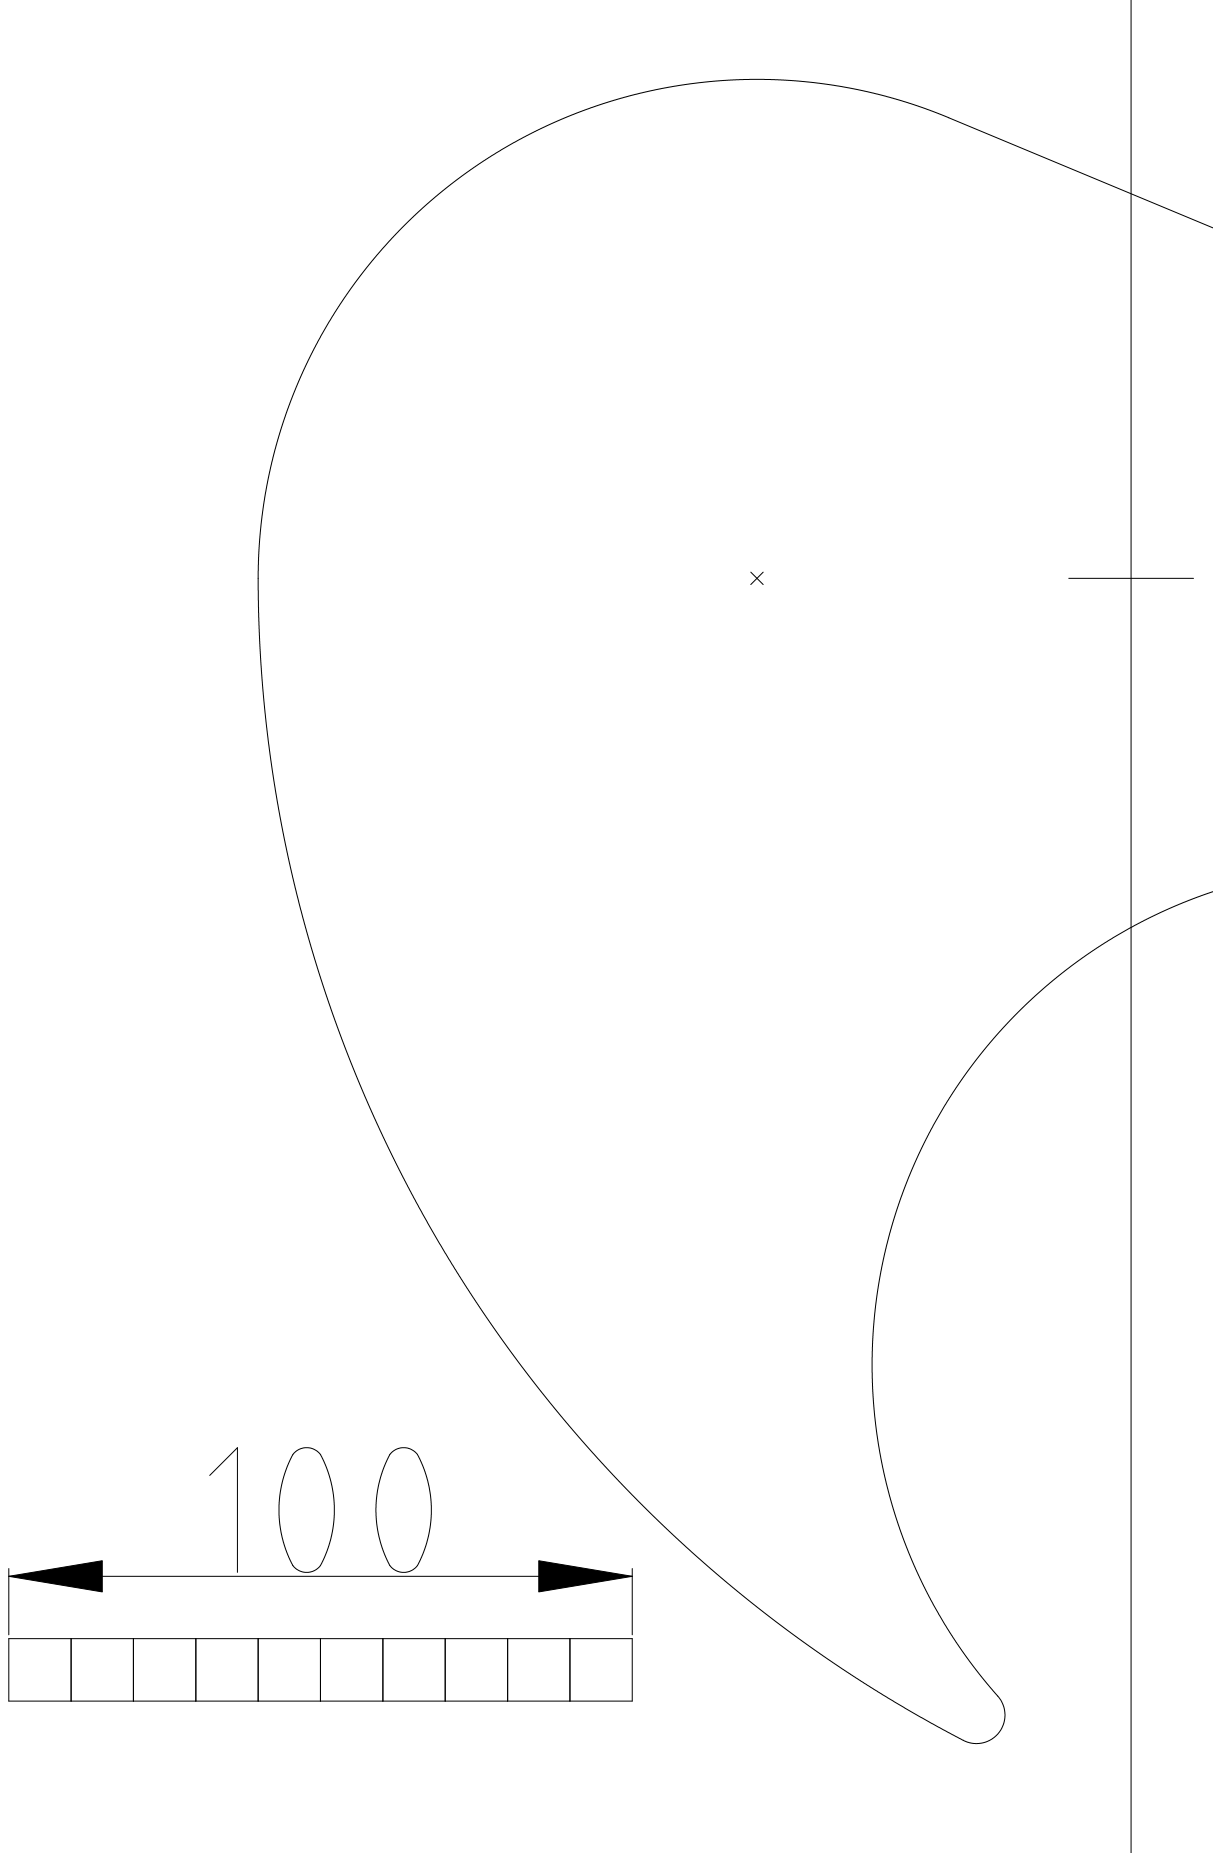
[picture p360: page 1]
