LeonLenclos/camera-obscura/contenu/plans/obturateur-patron-2.pdf

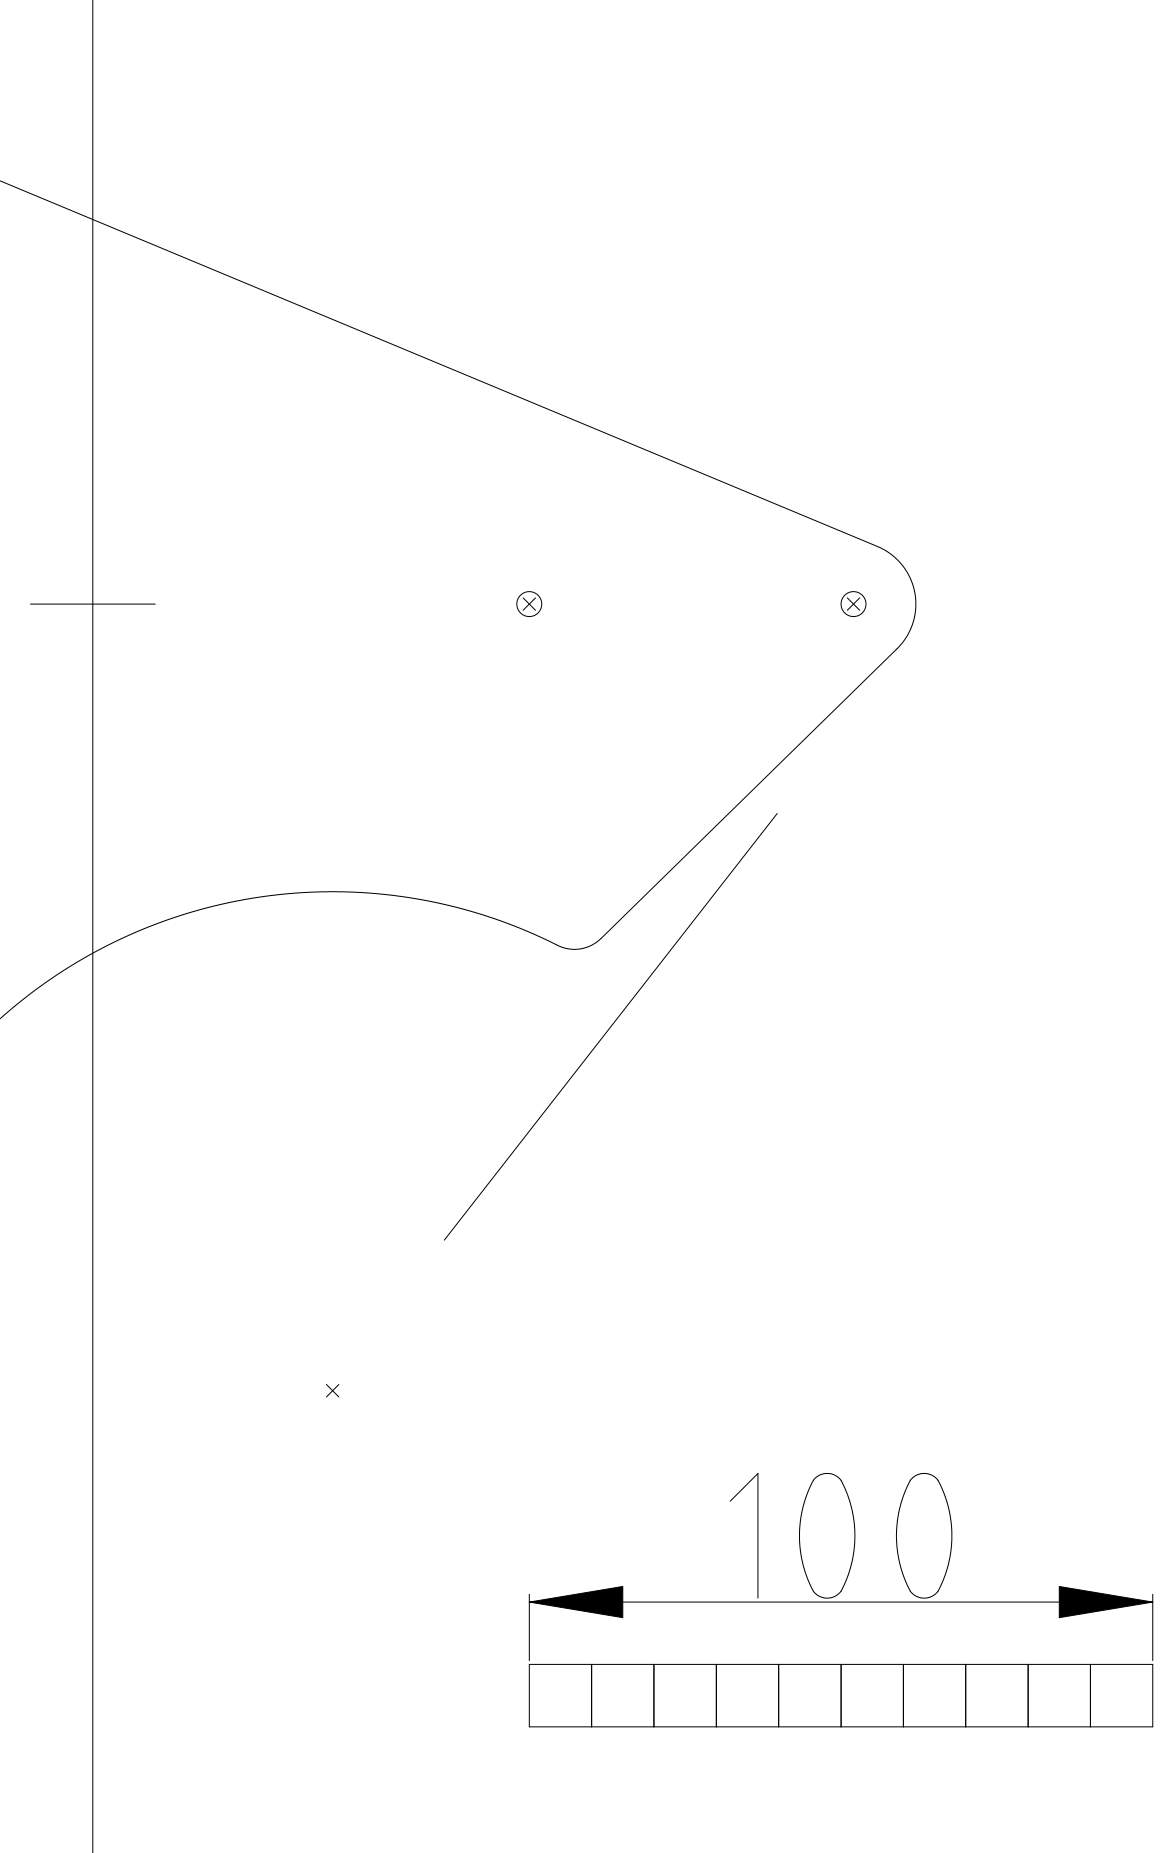
[picture p361: page 1]
