LeonLenclos/camera-obscura/contenu/plans/obturateur.pdf

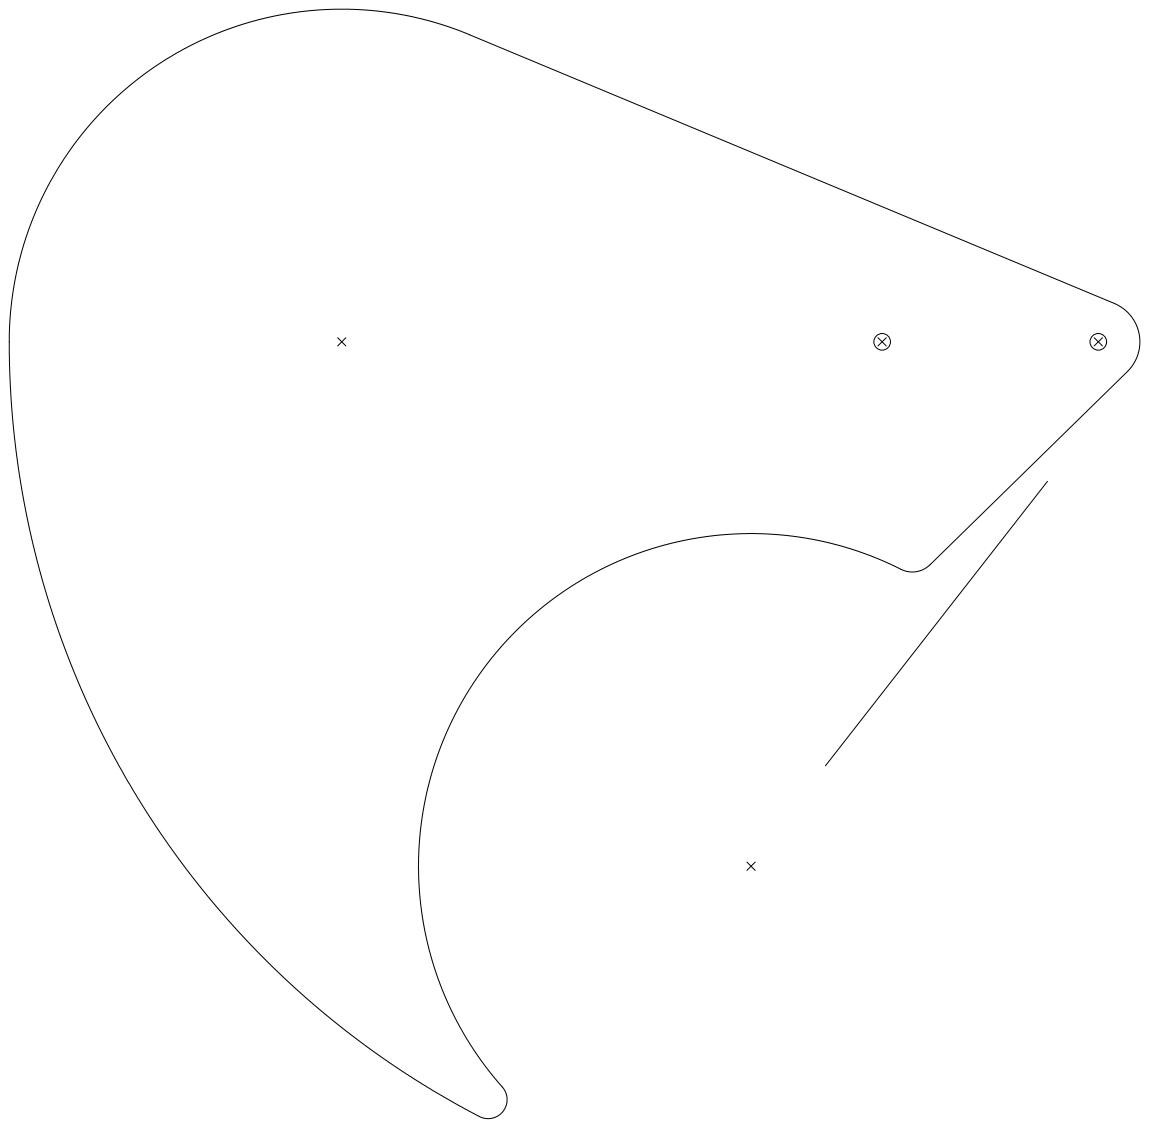
[picture p362: page 1]
