LeonLenclos/camera-obscura/contenu/plans/plaques-reflecteurs.pdf

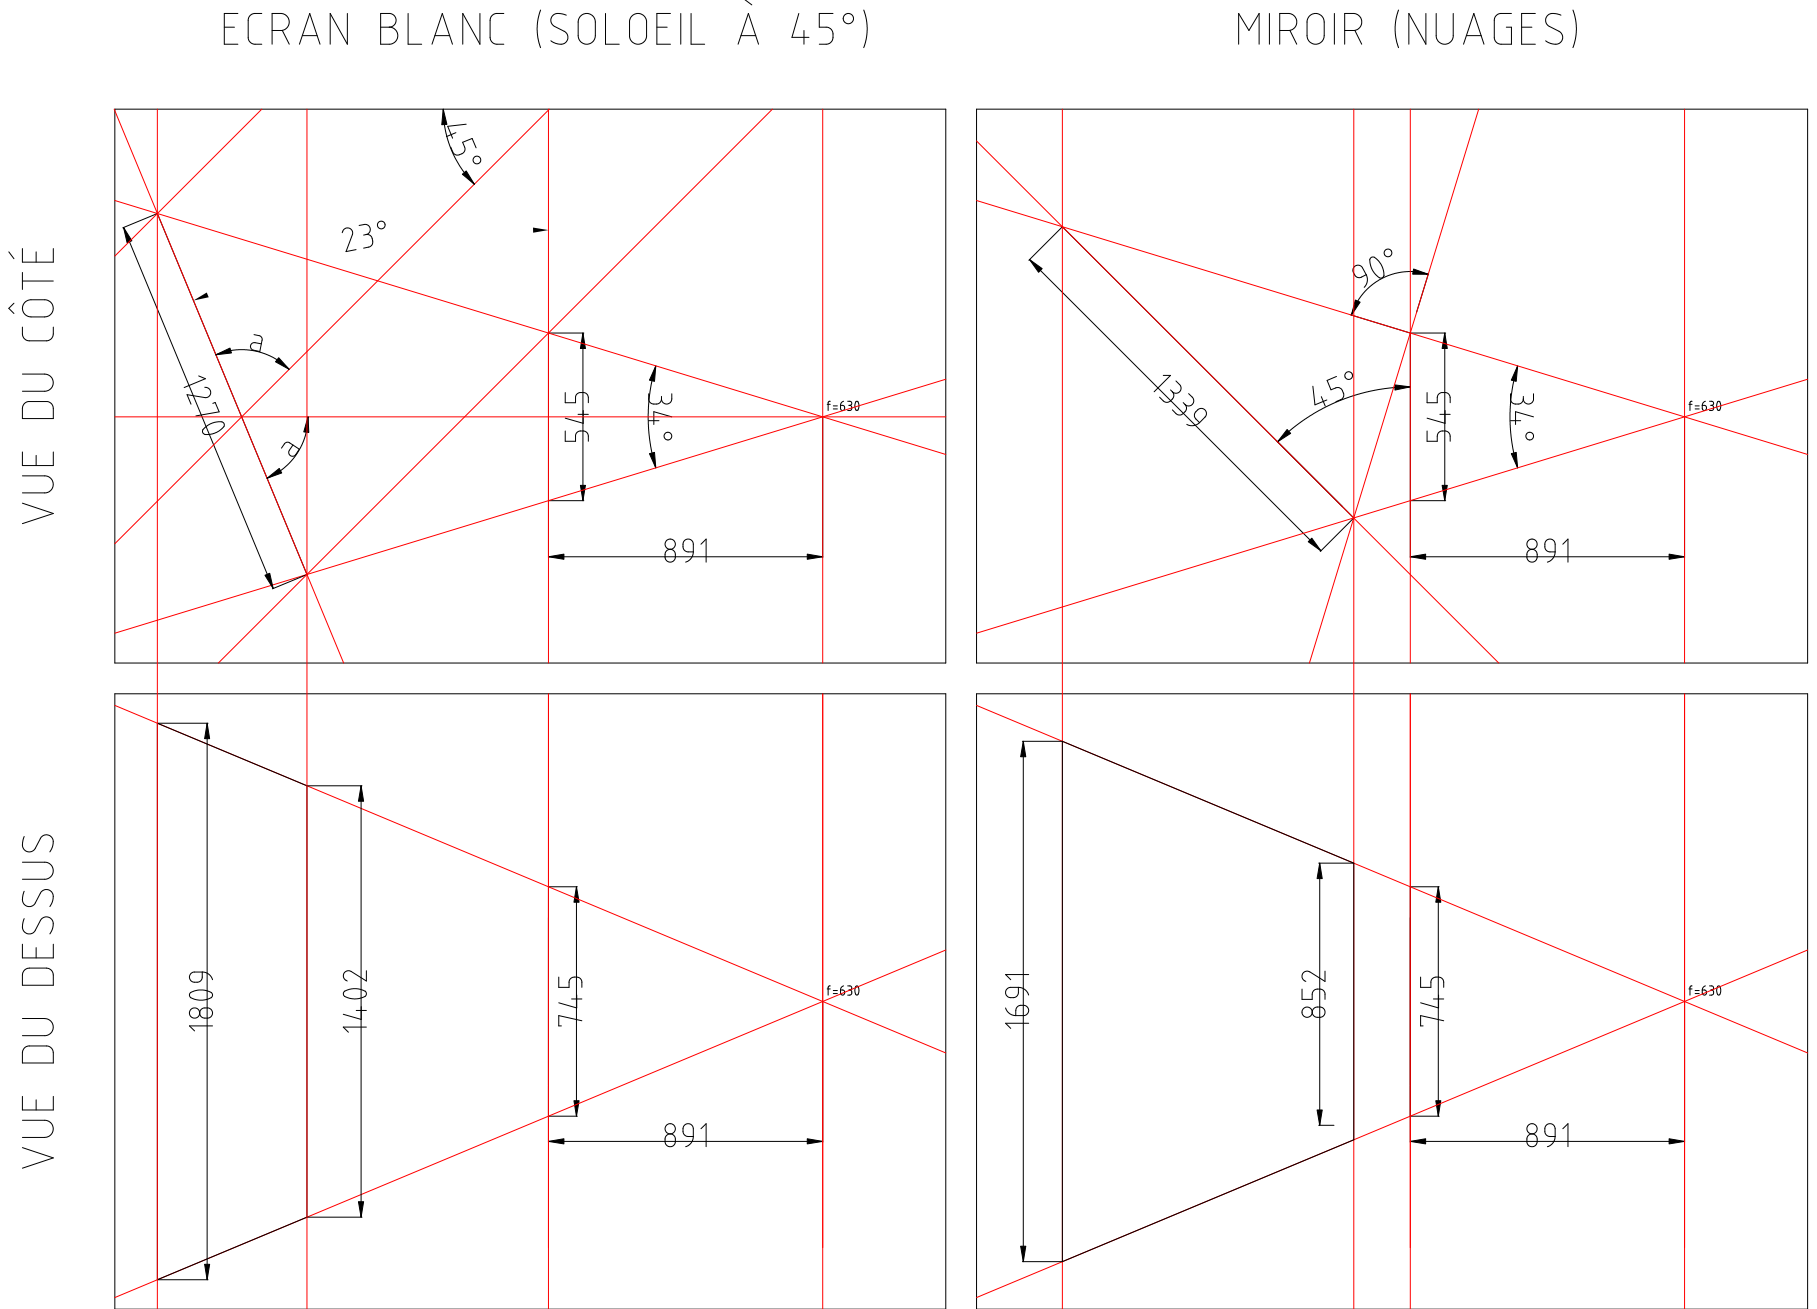
[picture p363: page 1]
