LeonLenclos/camera-obscura/contenu/plans/arbres-usinage.pdf

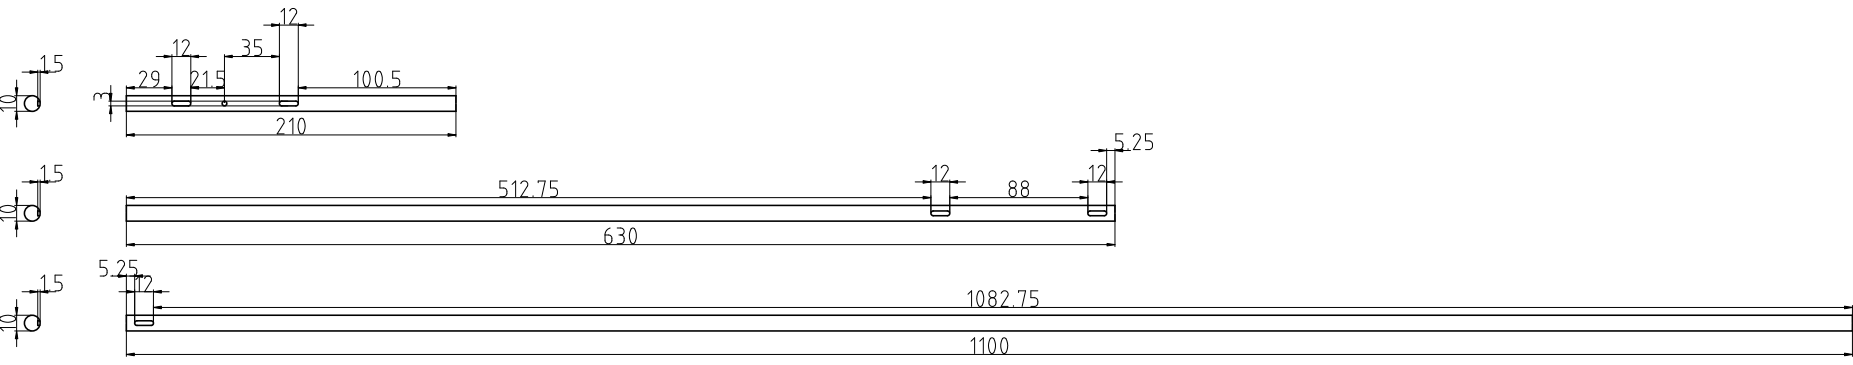
[picture p364: page 1]
