LeonLenclos/camera-obscura/contenu/plans/tourelle.pdf

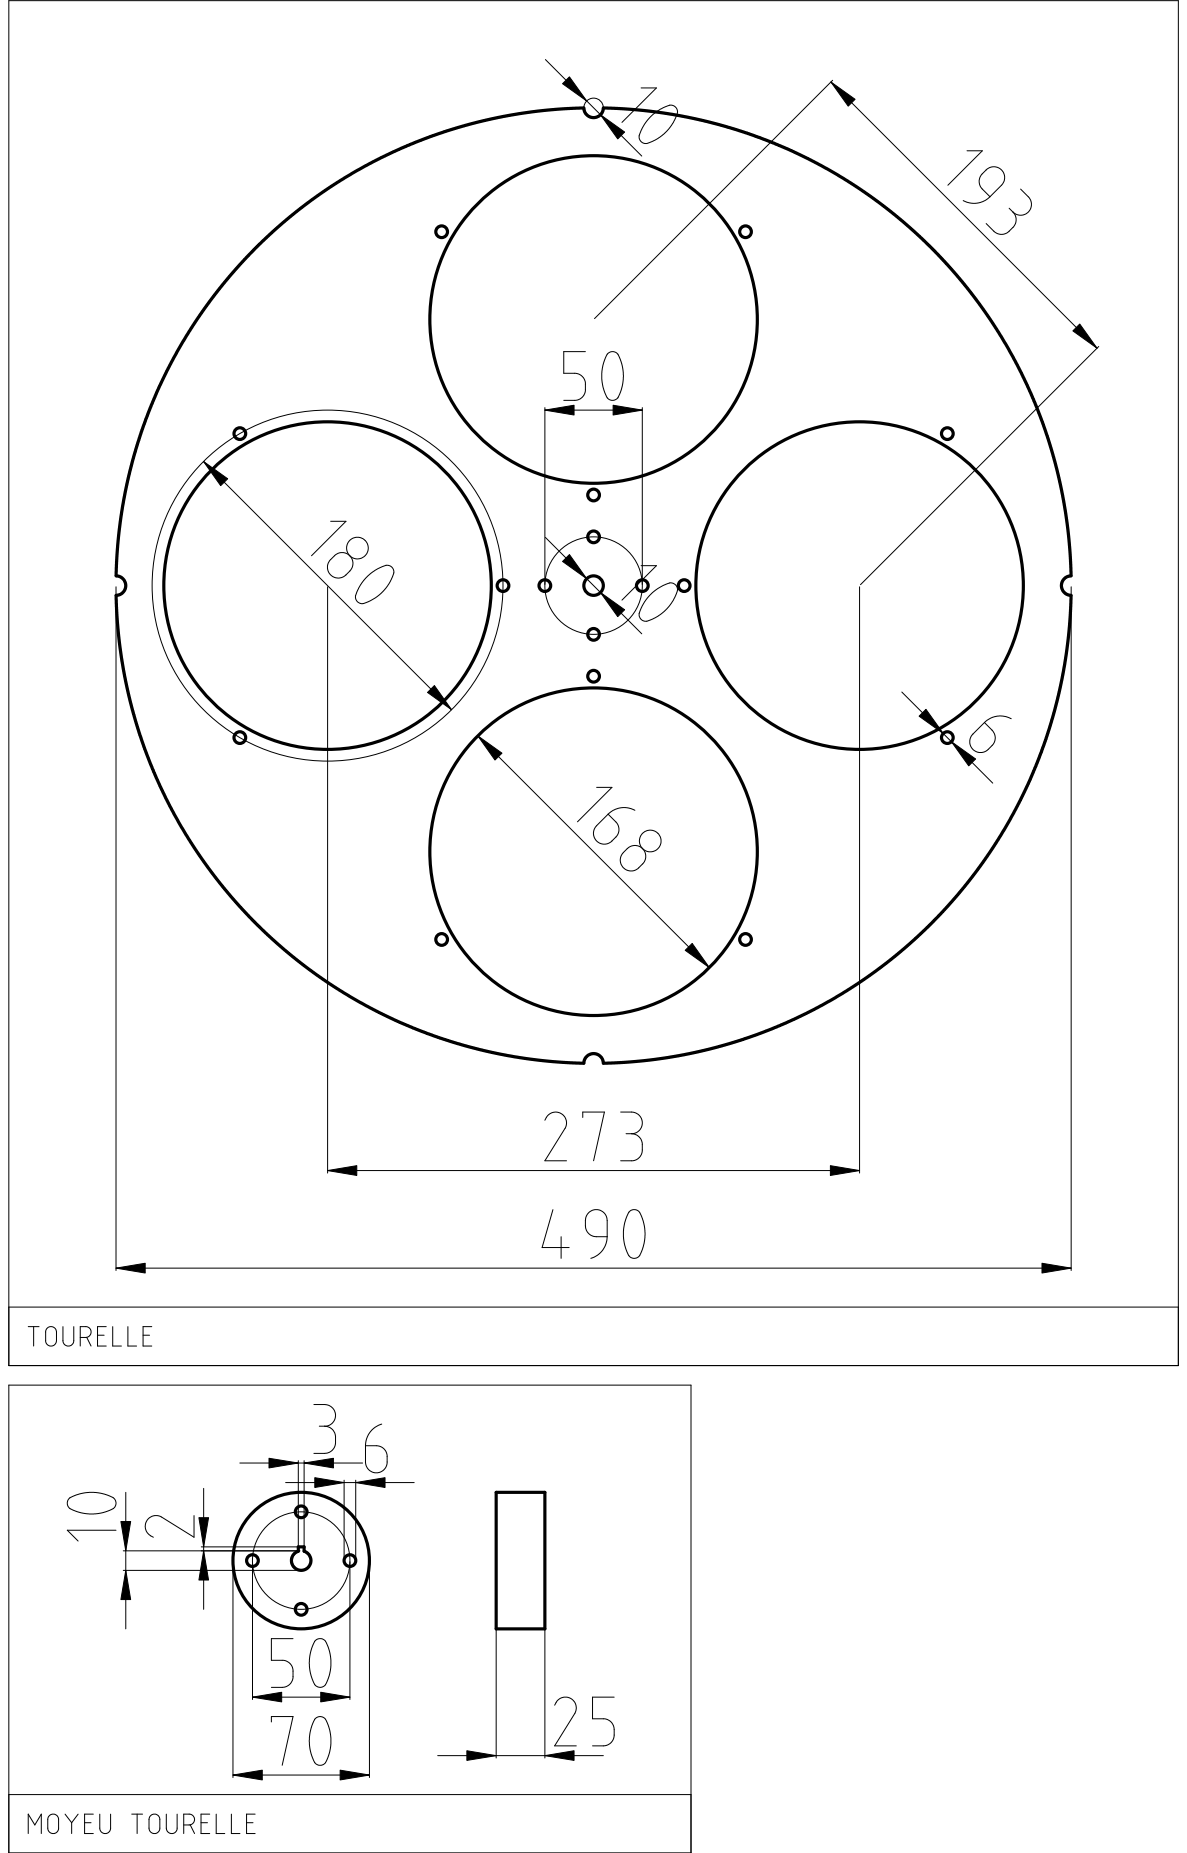
[picture p365: page 1]
