LeonLenclos/camera-obscura/contenu/plans/fut-154V1-bagues.pdf

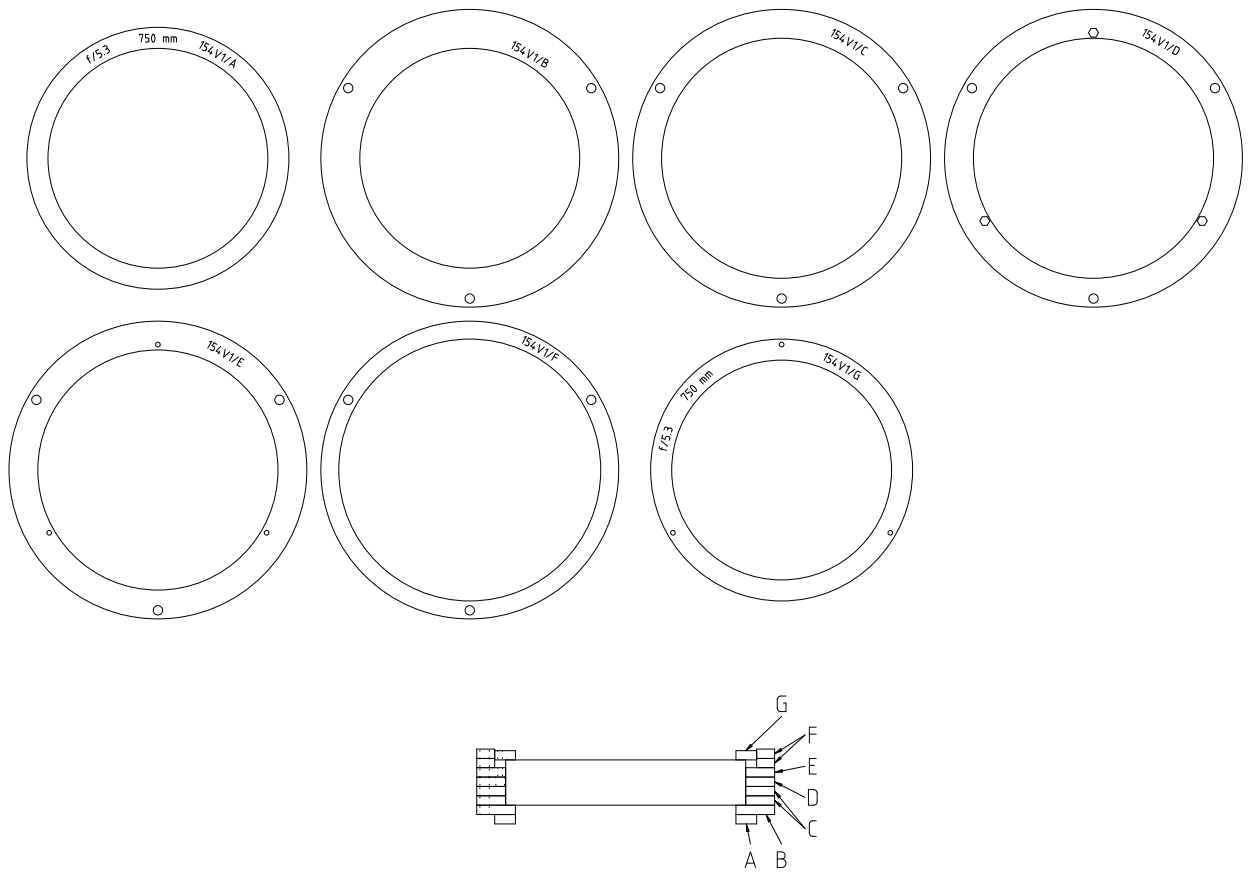
[picture p366: page 1]
