LeonLenclos/camera-obscura/contenu/plans/toit-amici-structure.pdf

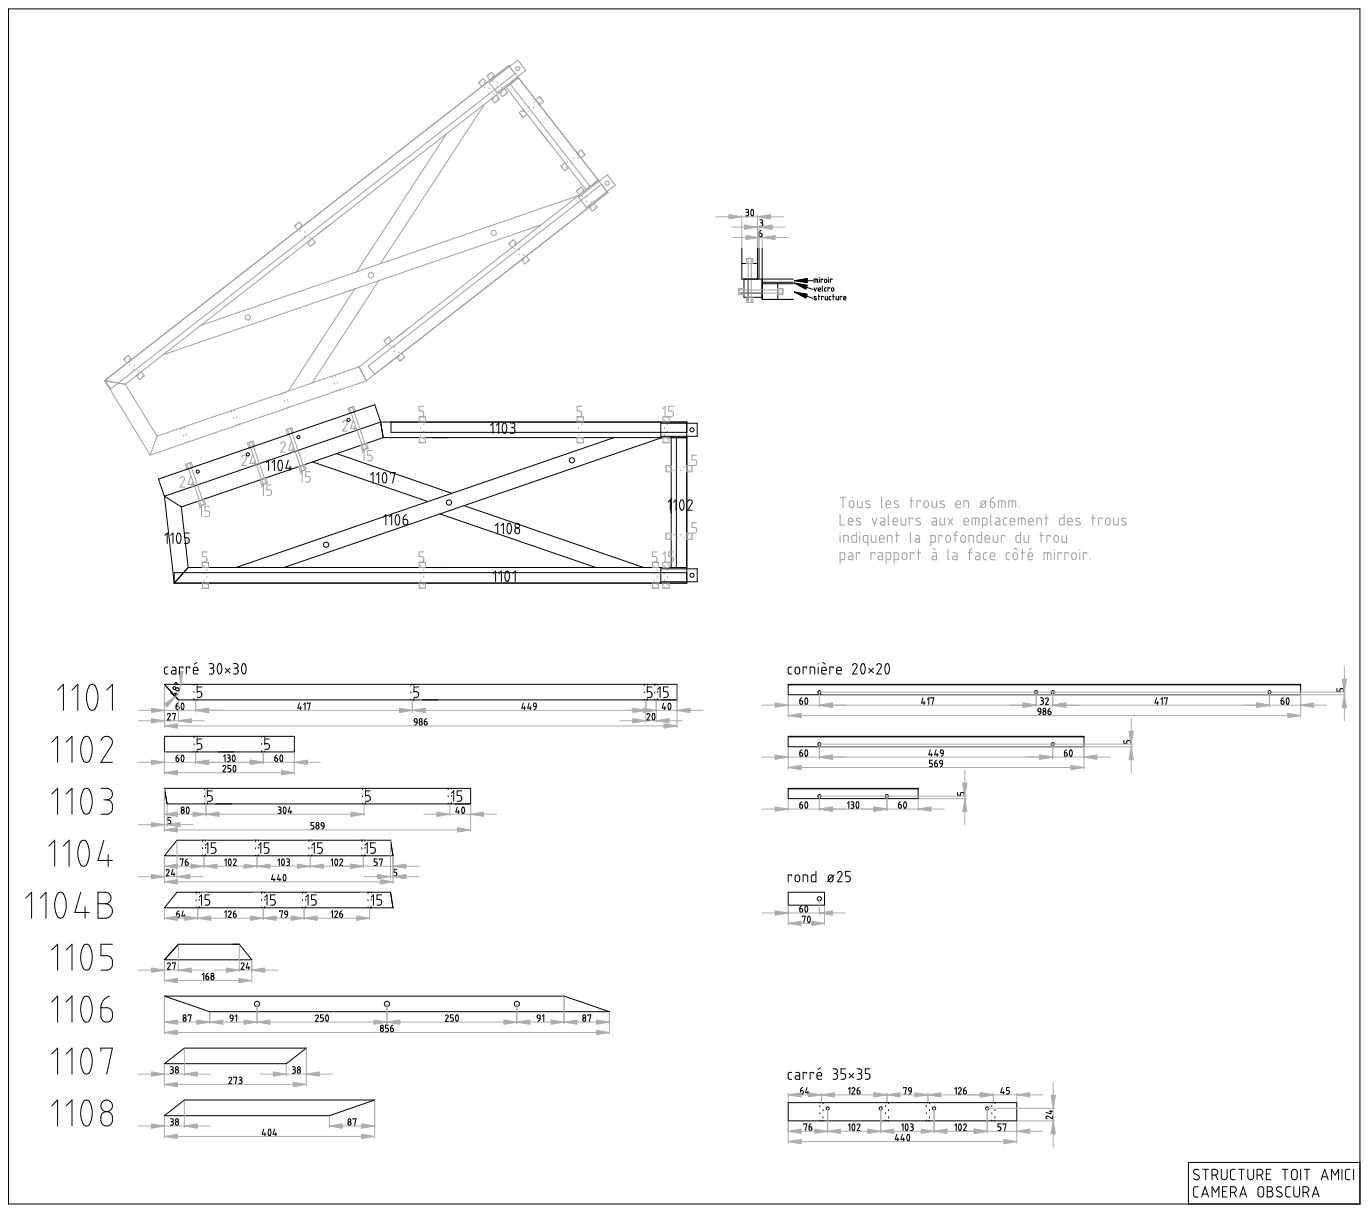
[picture p367: page 1]
