LeonLenclos/camera-obscura/contenu/plans/tapees.pdf

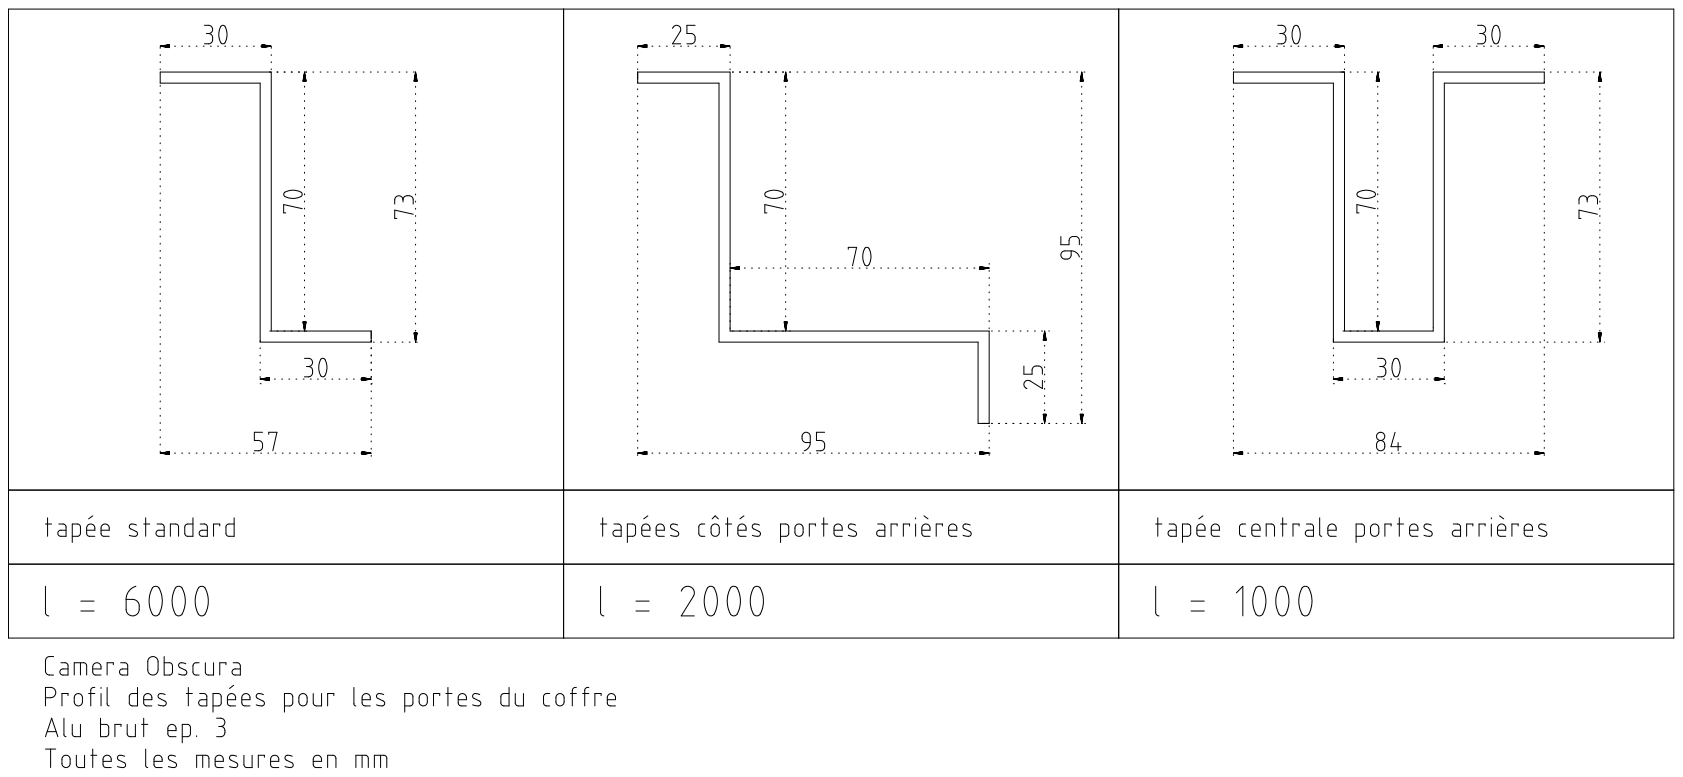
[picture p368: page 1]
