LeonLenclos/camera-obscura/contenu/plans/remorque-detail-divers-toles-schiavon.pdf

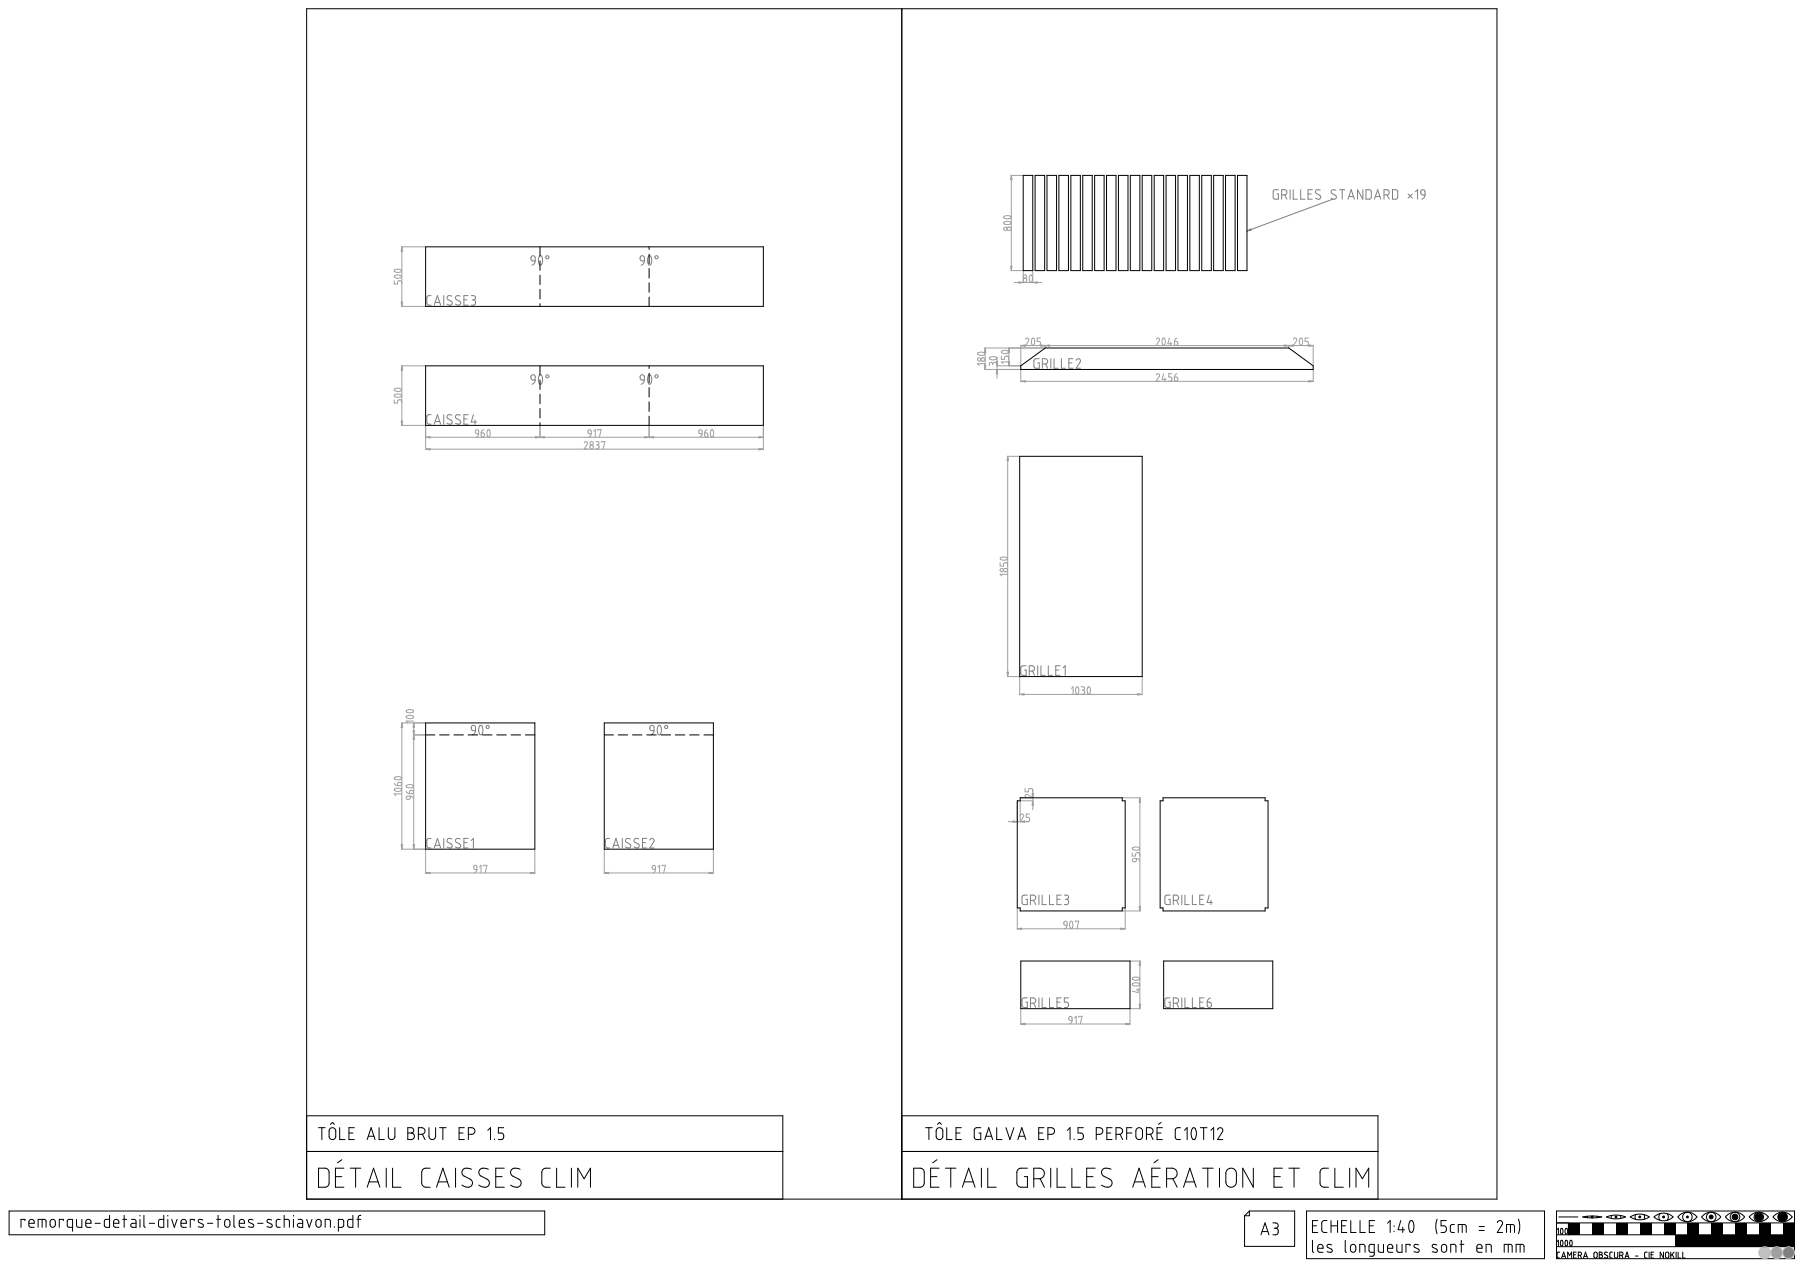
[picture p369: page 1]
