LeonLenclos/camera-obscura/contenu/plans/remorque-pieces-tole-laquee-schiavon.pdf

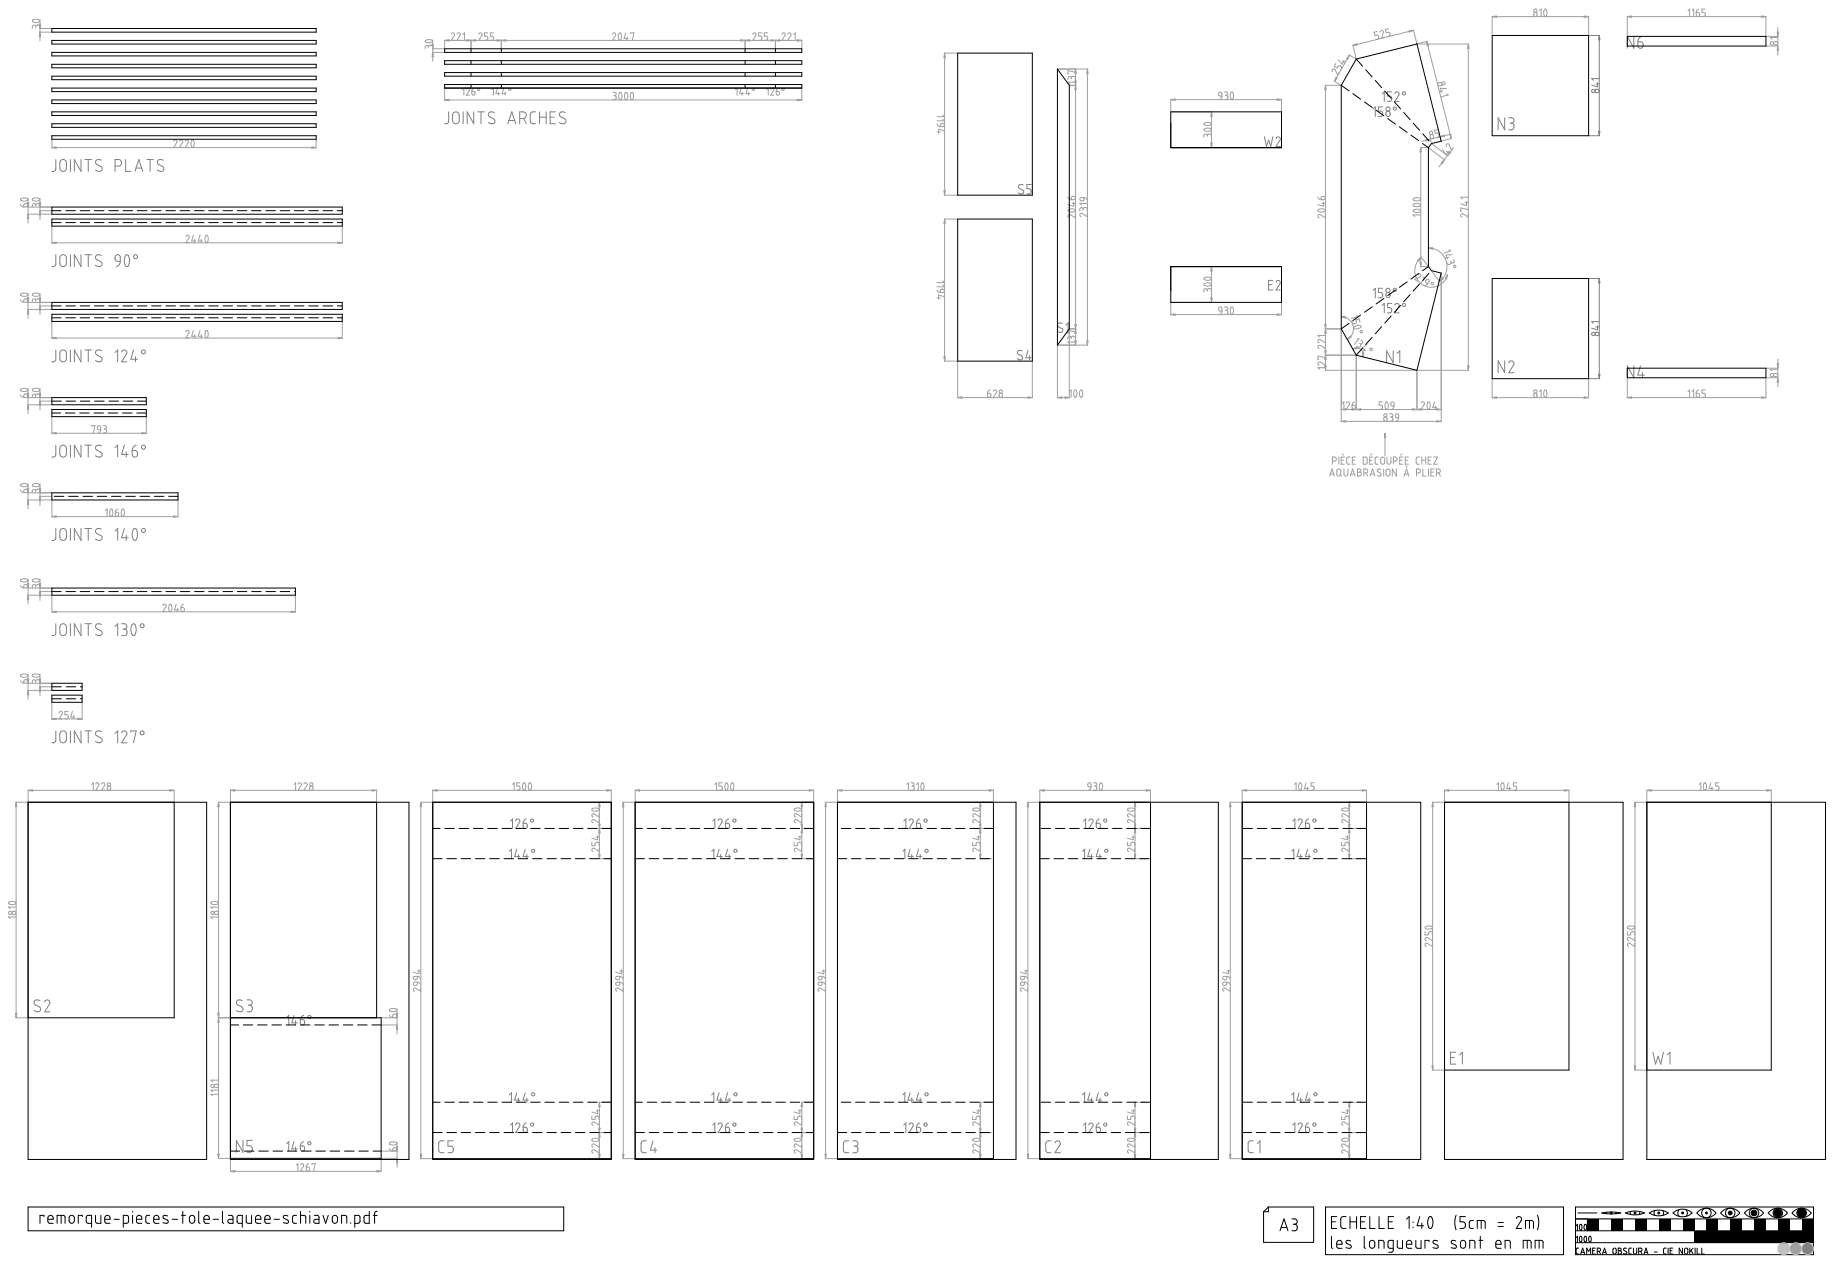
[picture p370: page 1]
