LeonLenclos/camera-obscura/contenu/plans/remorque-carosserie.pdf

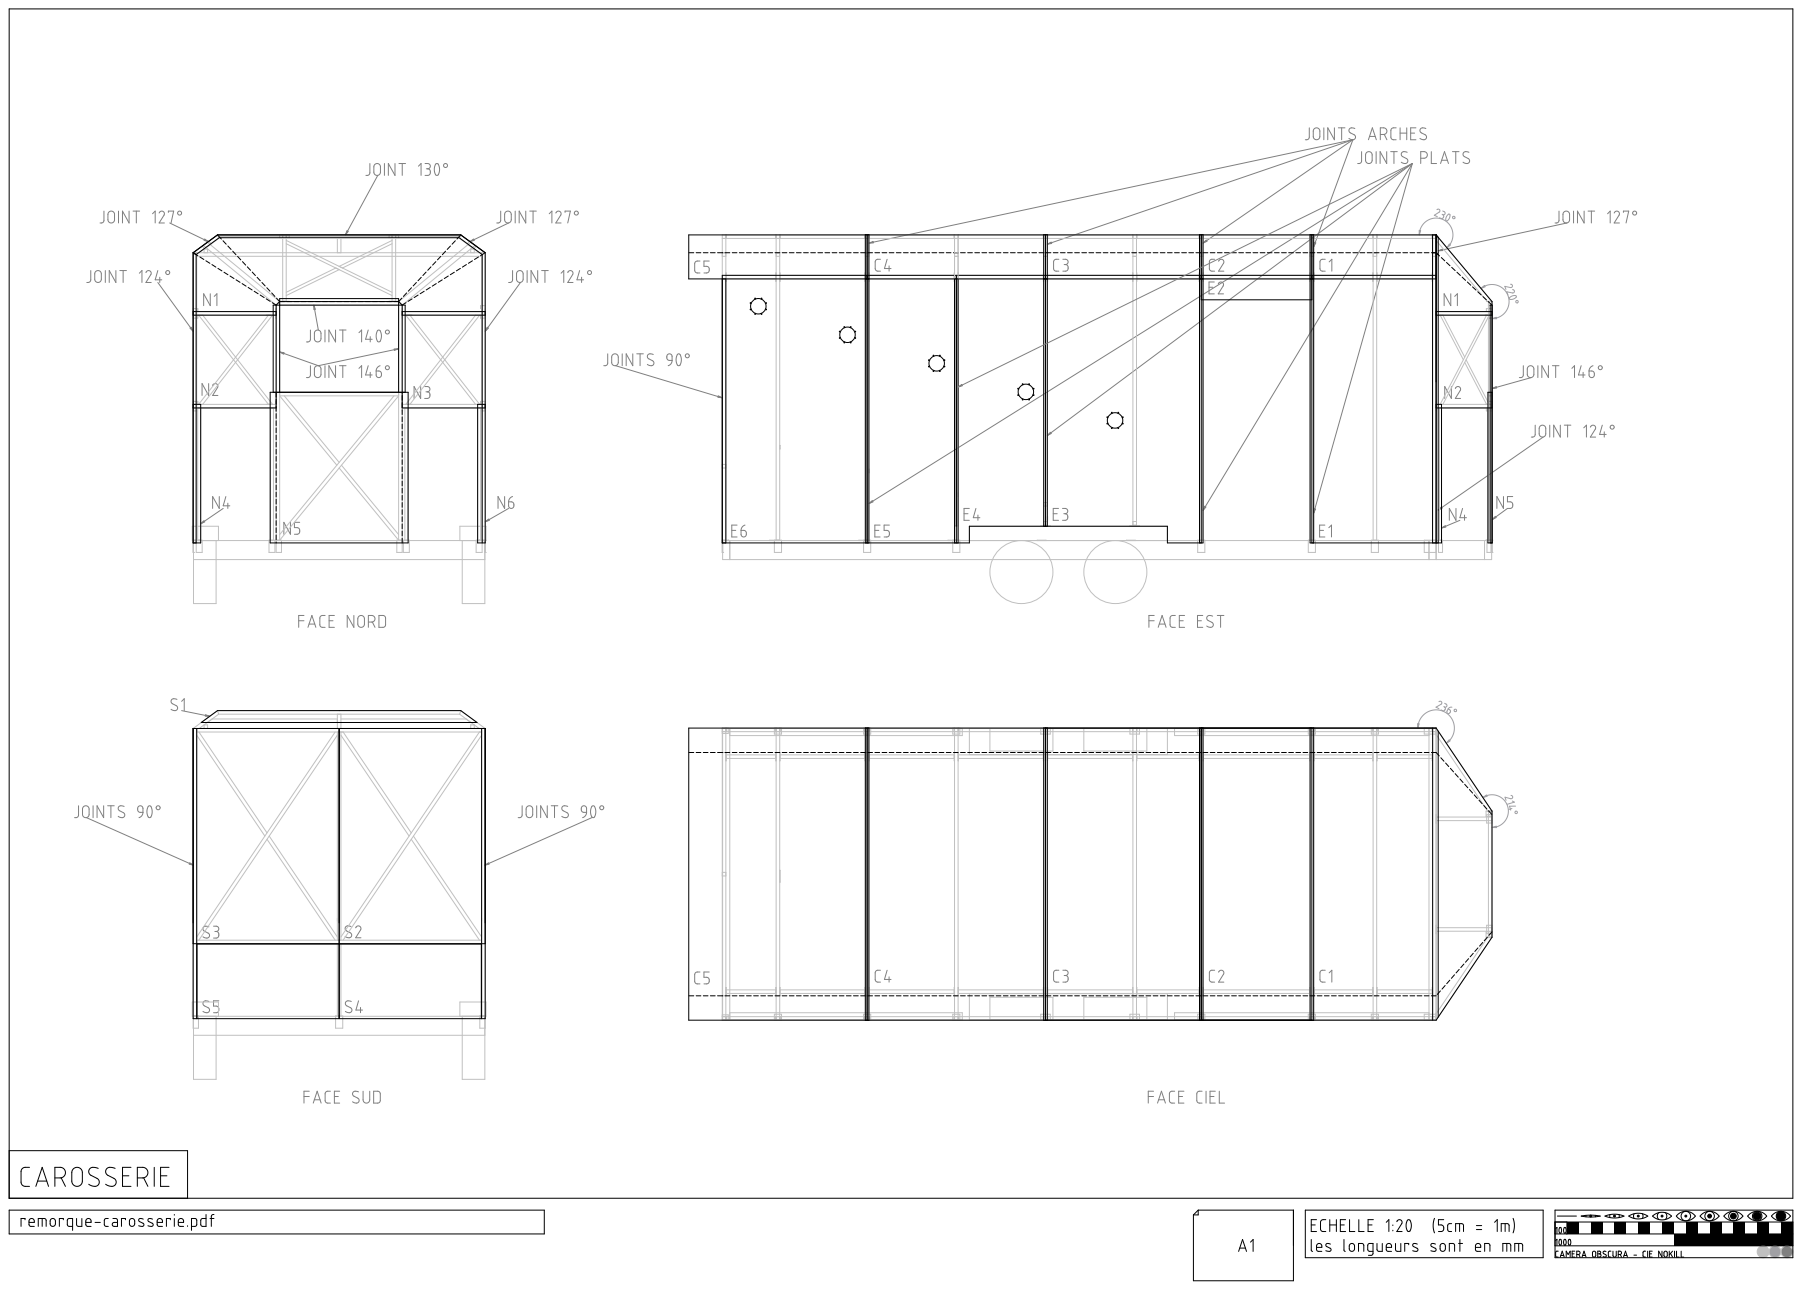
[picture p371: page 1]
