LeonLenclos/camera-obscura/contenu/plans/remorque-detail-divers-toles.pdf

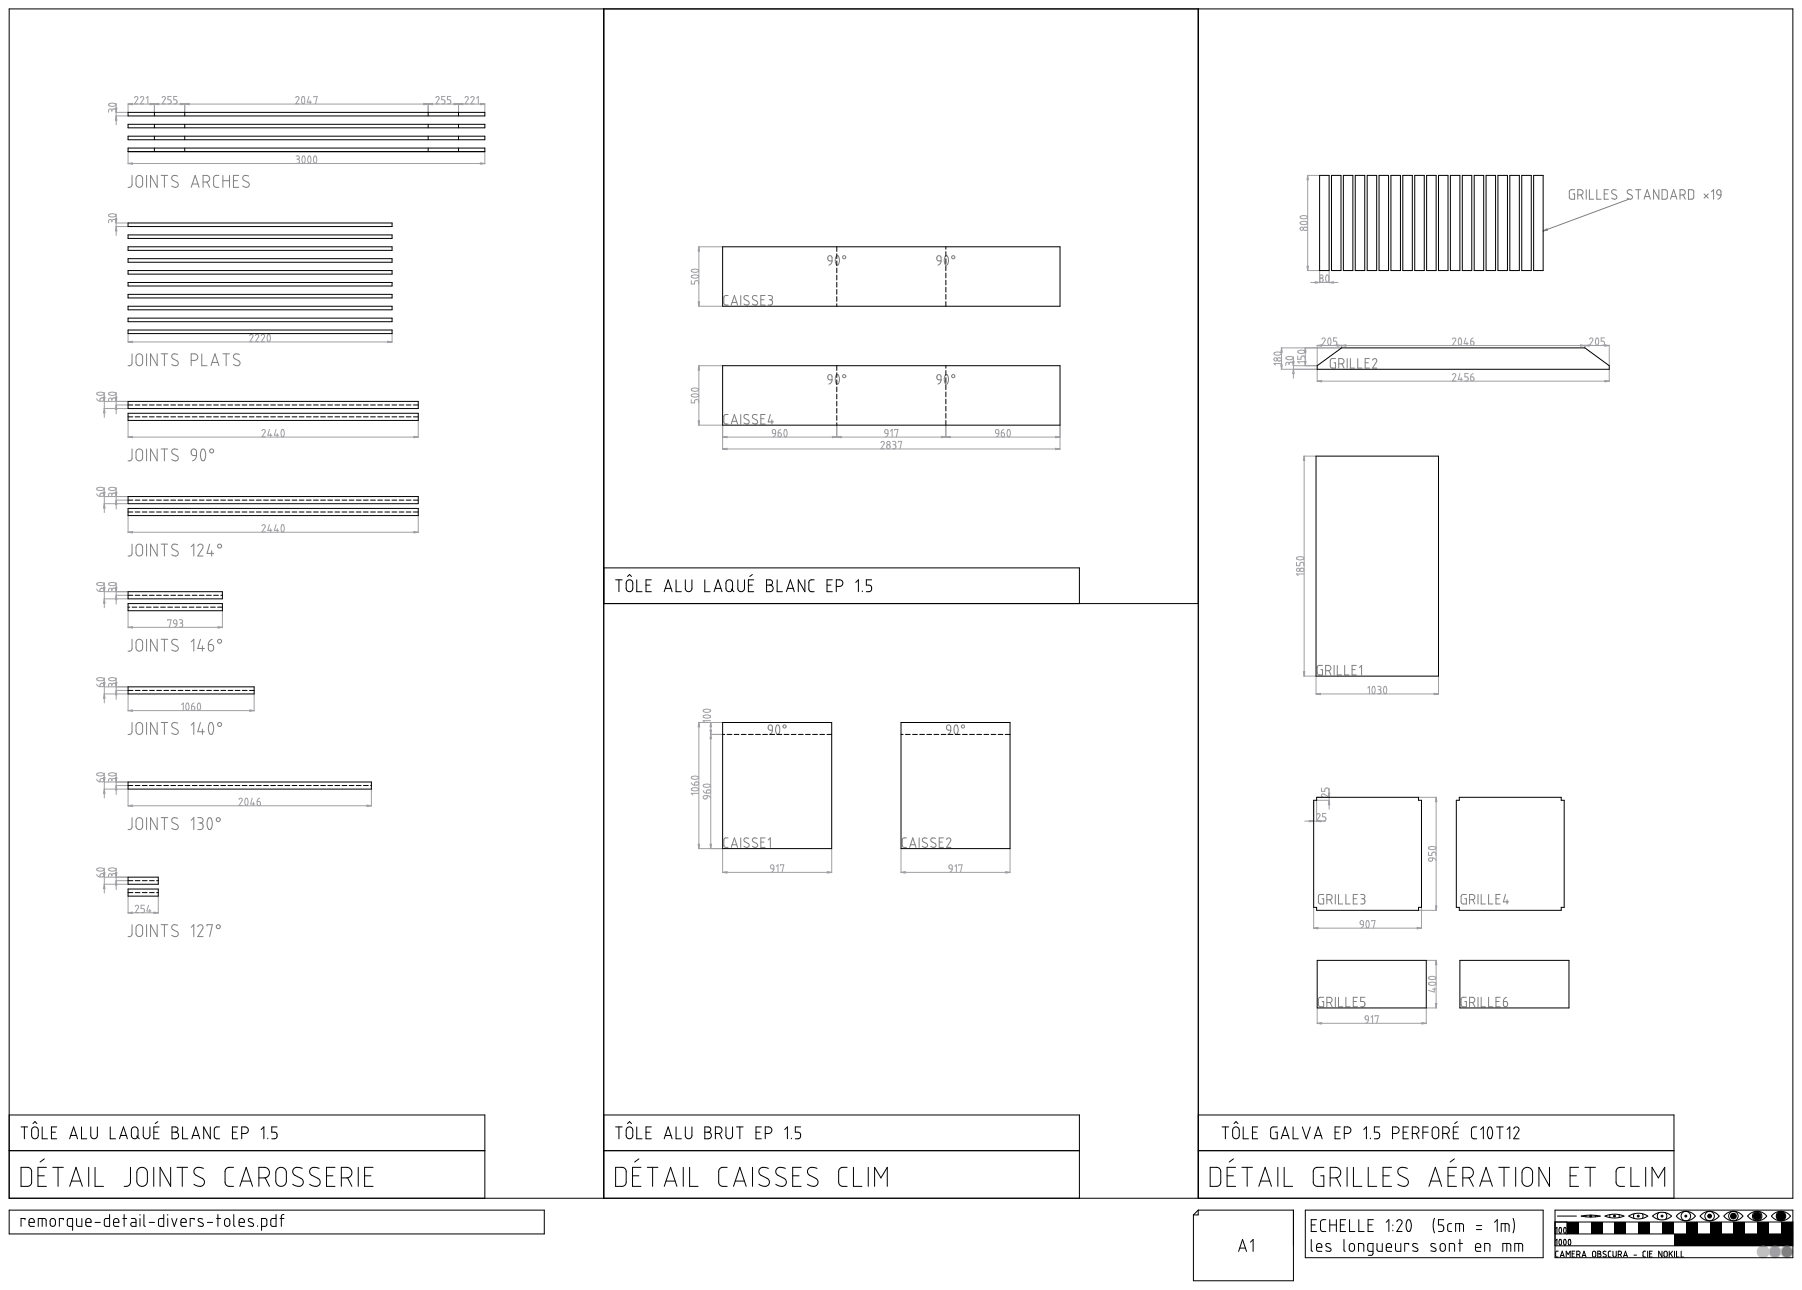
[picture p372: page 1]
