LeonLenclos/camera-obscura/contenu/plans/remorque-detail-plaques-carosserie.pdf

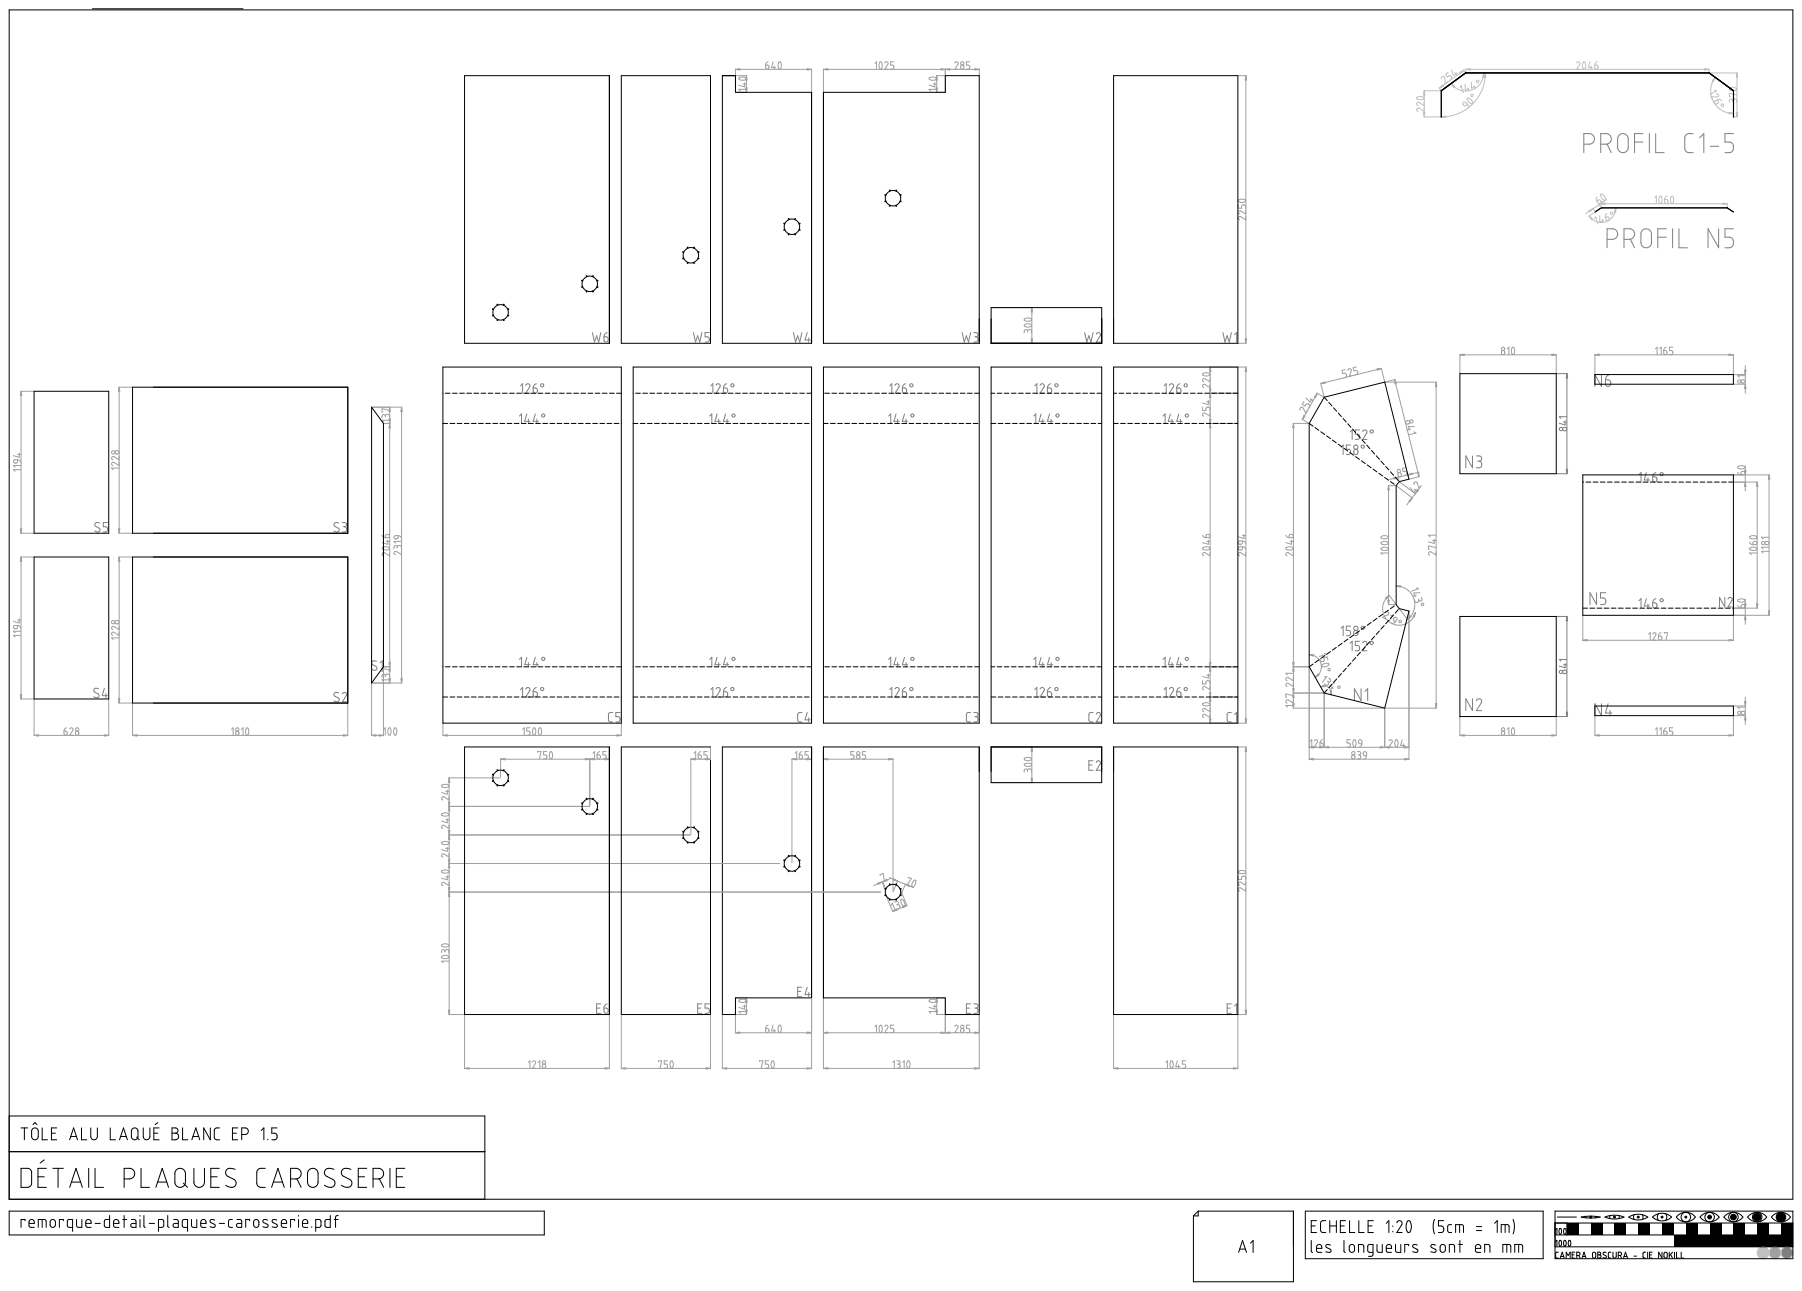
[picture p373: page 1]
