LeonLenclos/camera-obscura/contenu/plans/remorque-repartition-pieces-plaques.pdf

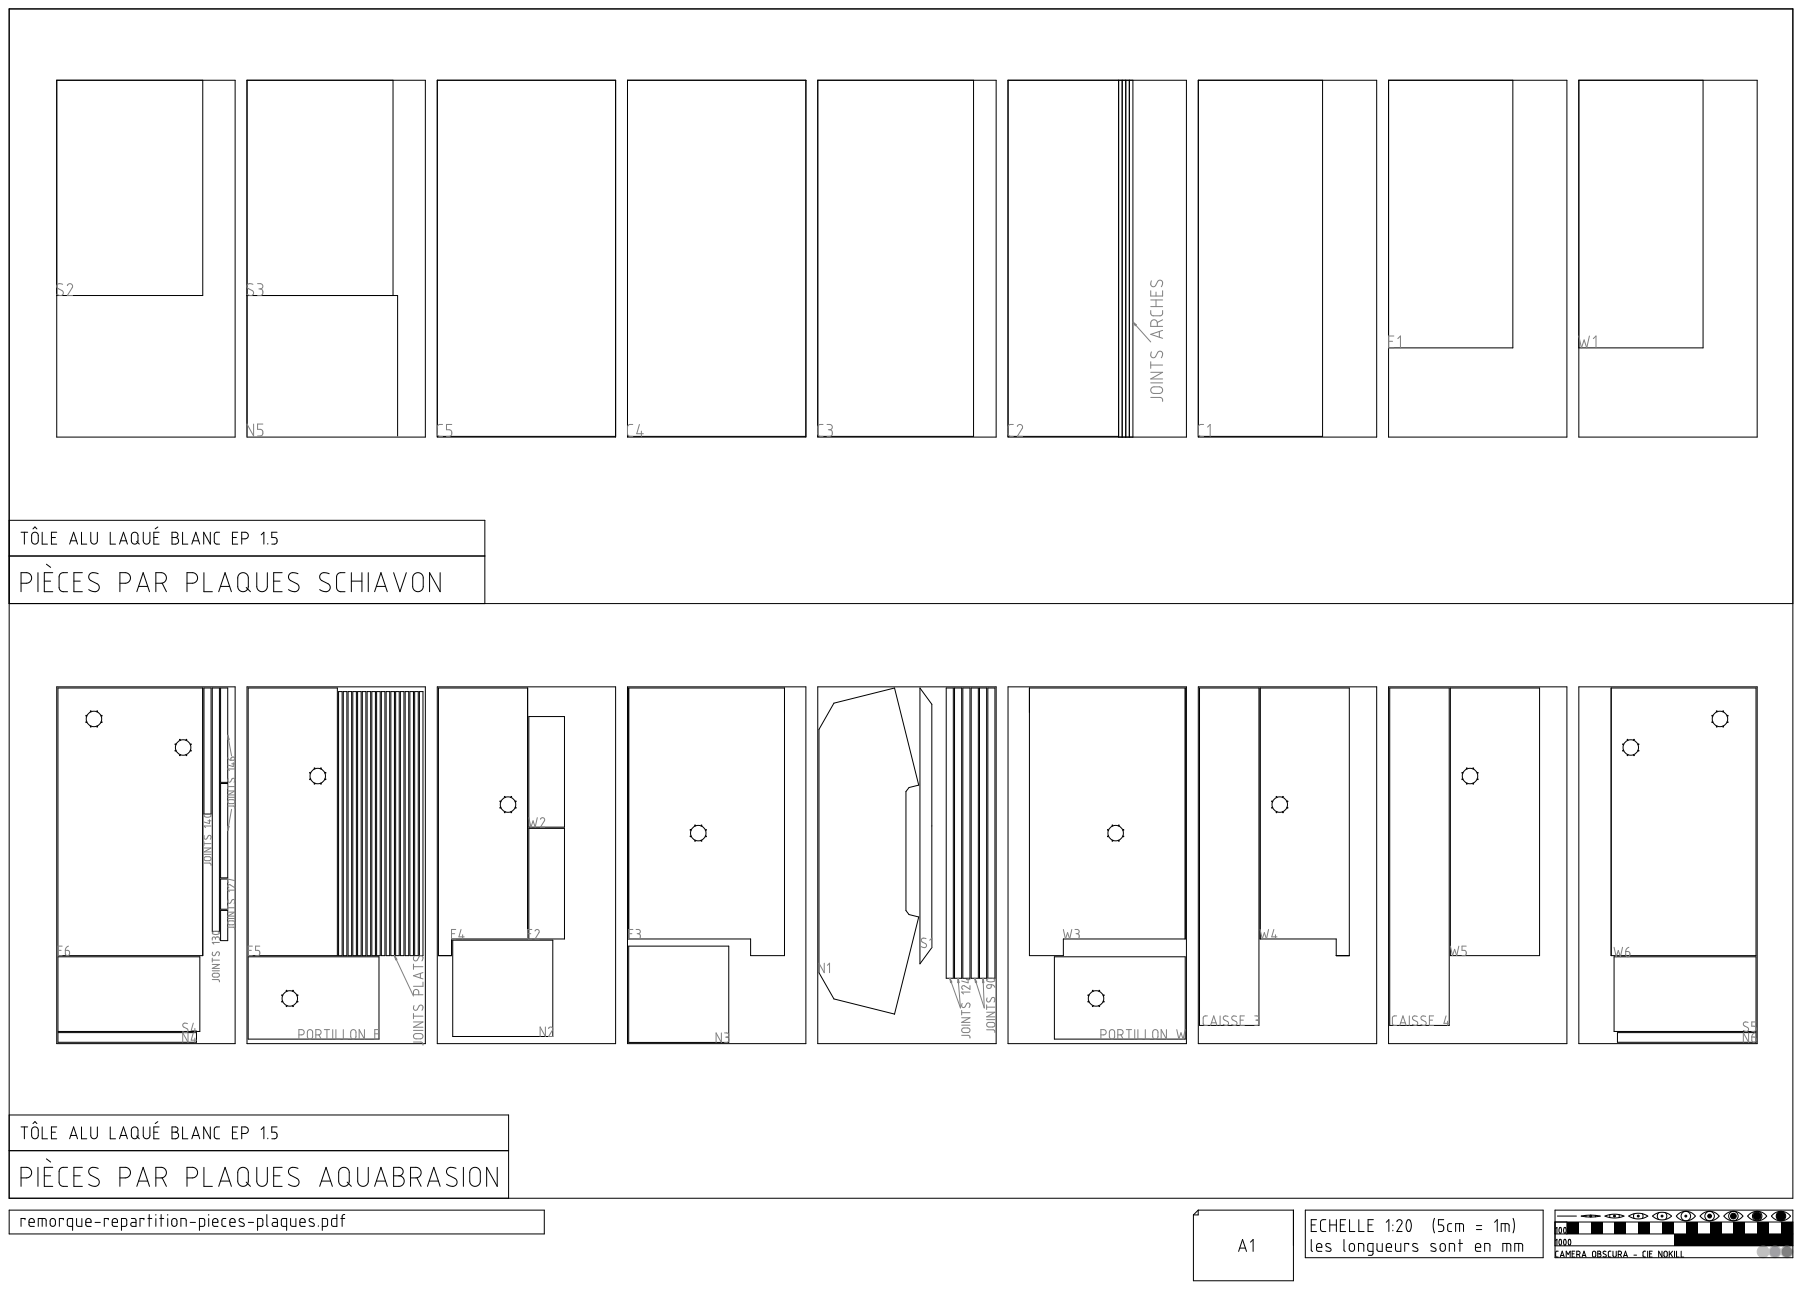
[picture p374: page 1]
