LeonLenclos/camera-obscura/contenu/plans/remorque-structure.pdf

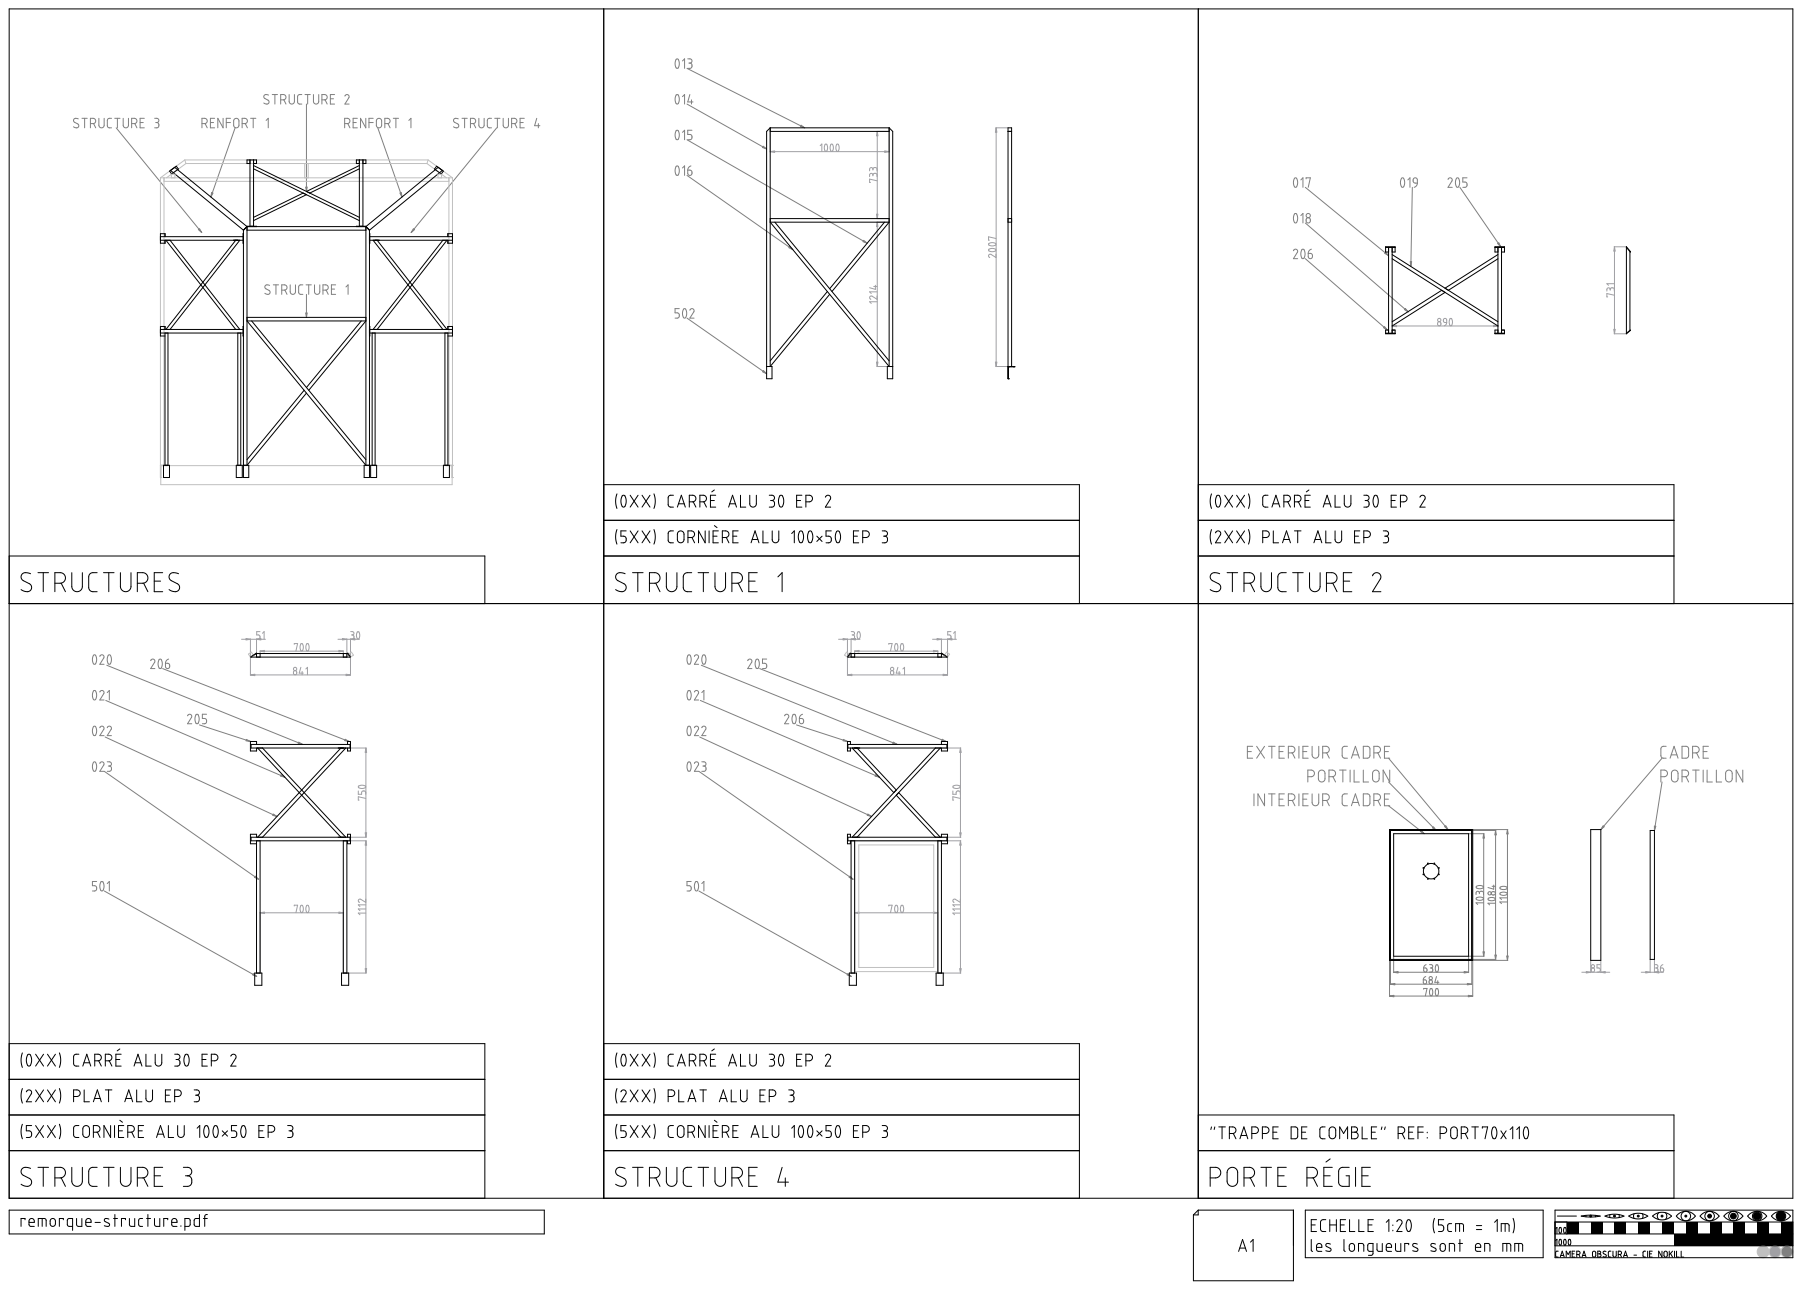
[picture p375: page 1]
