LeonLenclos/camera-obscura/contenu/plans/remorque-arches.pdf

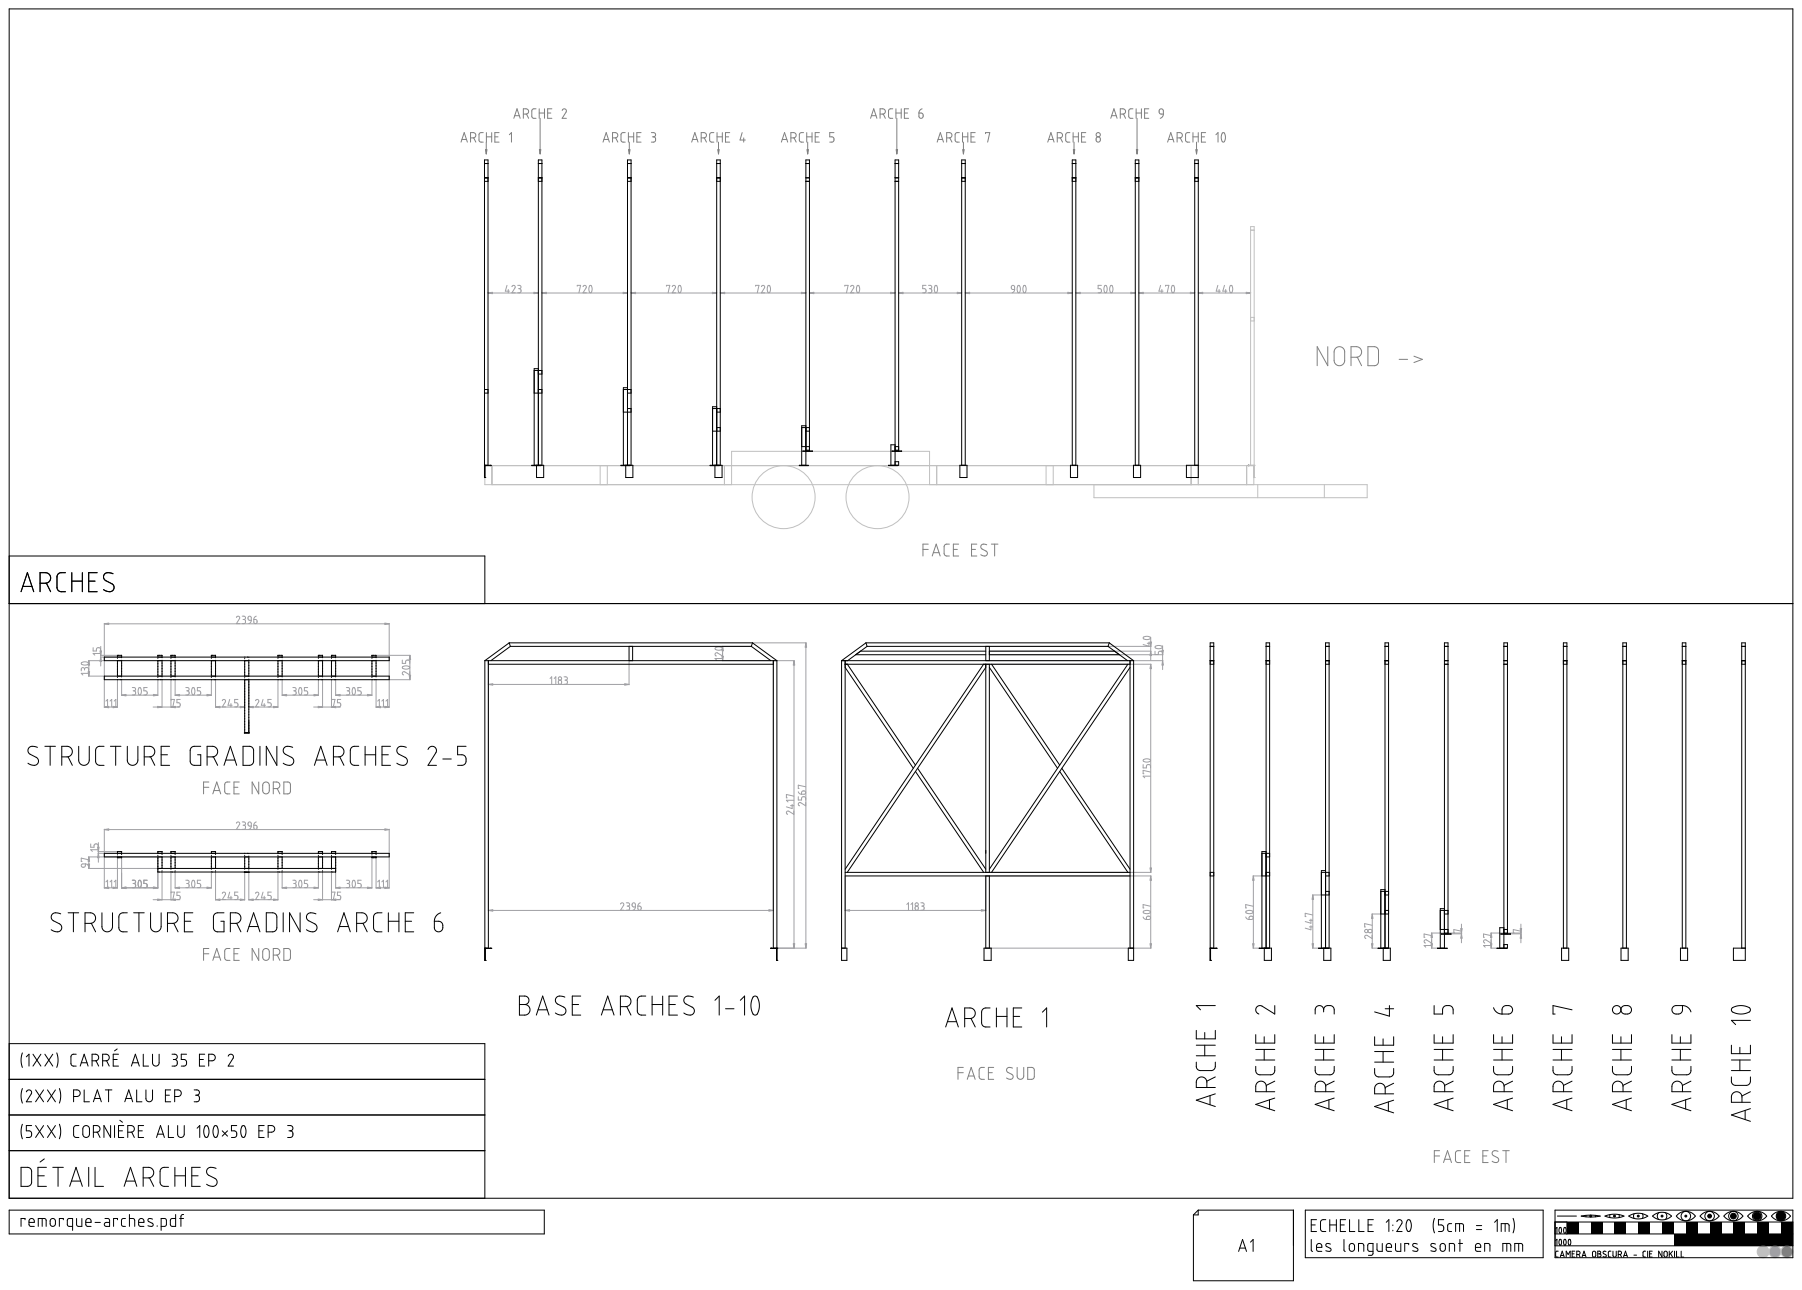
[picture p376: page 1]
