LeonLenclos/camera-obscura/contenu/plans/remorque-aspect.pdf

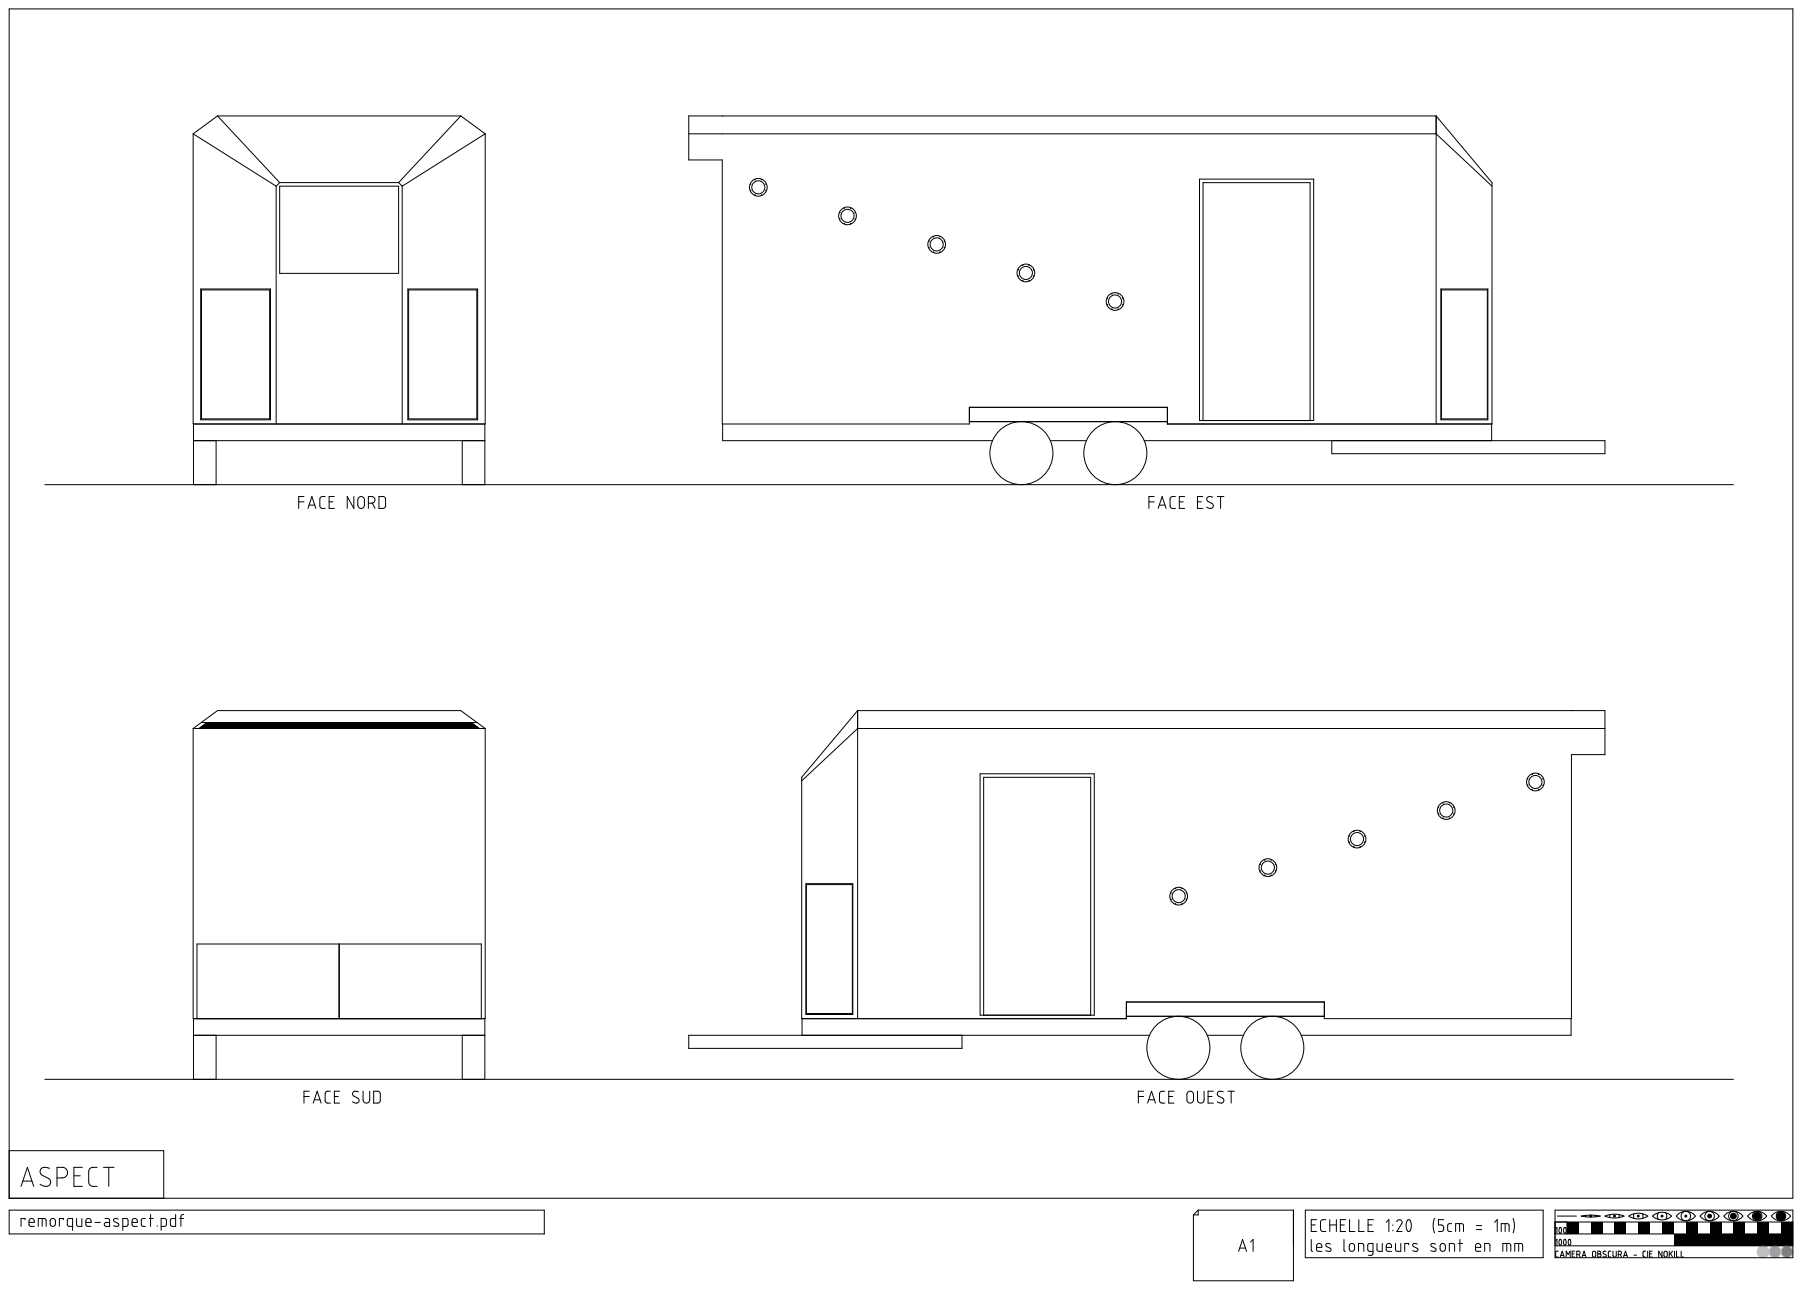
[picture p377: page 1]
