LeonLenclos/camera-obscura/contenu/plans/remorque-caisses-clim.pdf

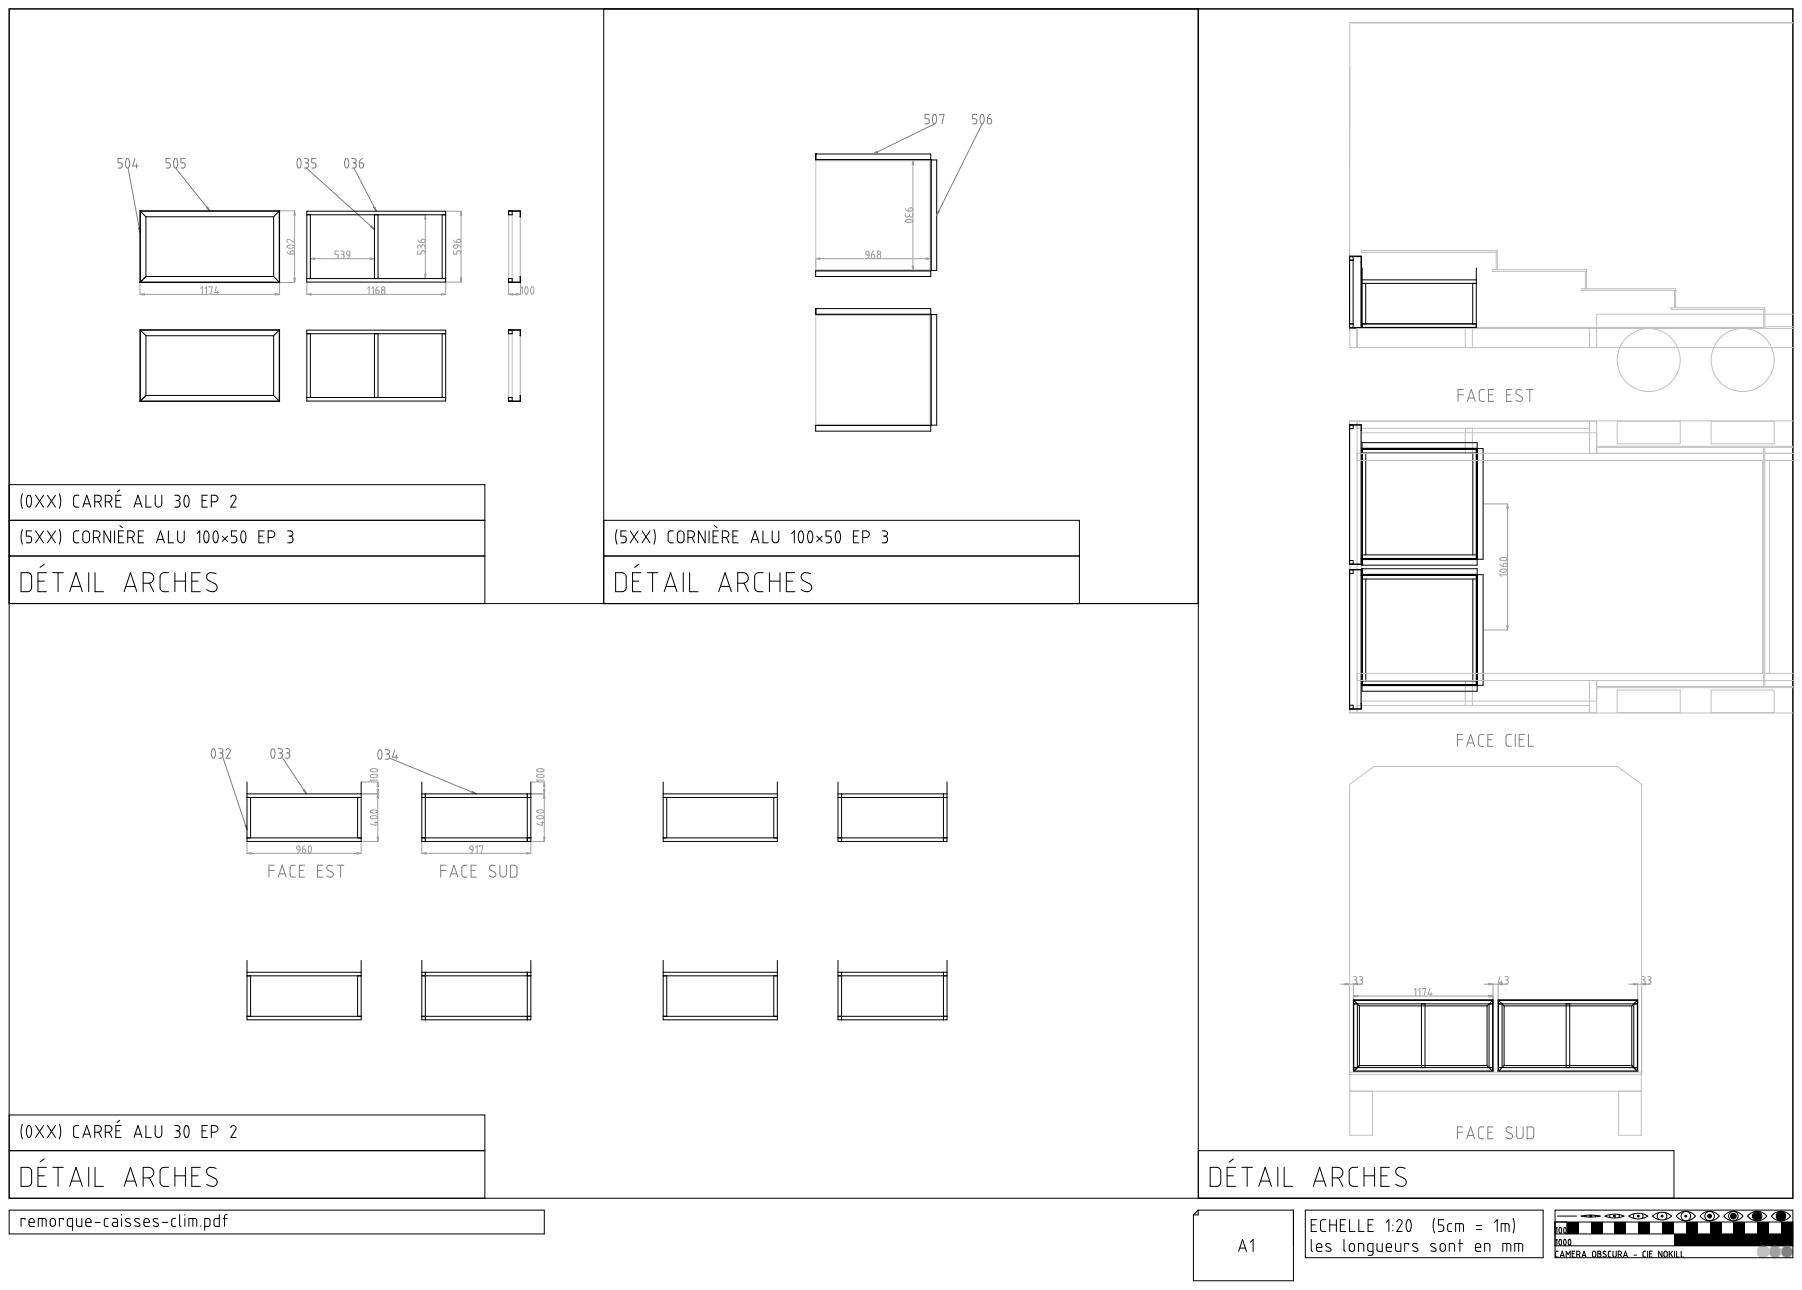
[picture p378: page 1]
