LeonLenclos/camera-obscura/contenu/plans/remorque-detail-arches.pdf

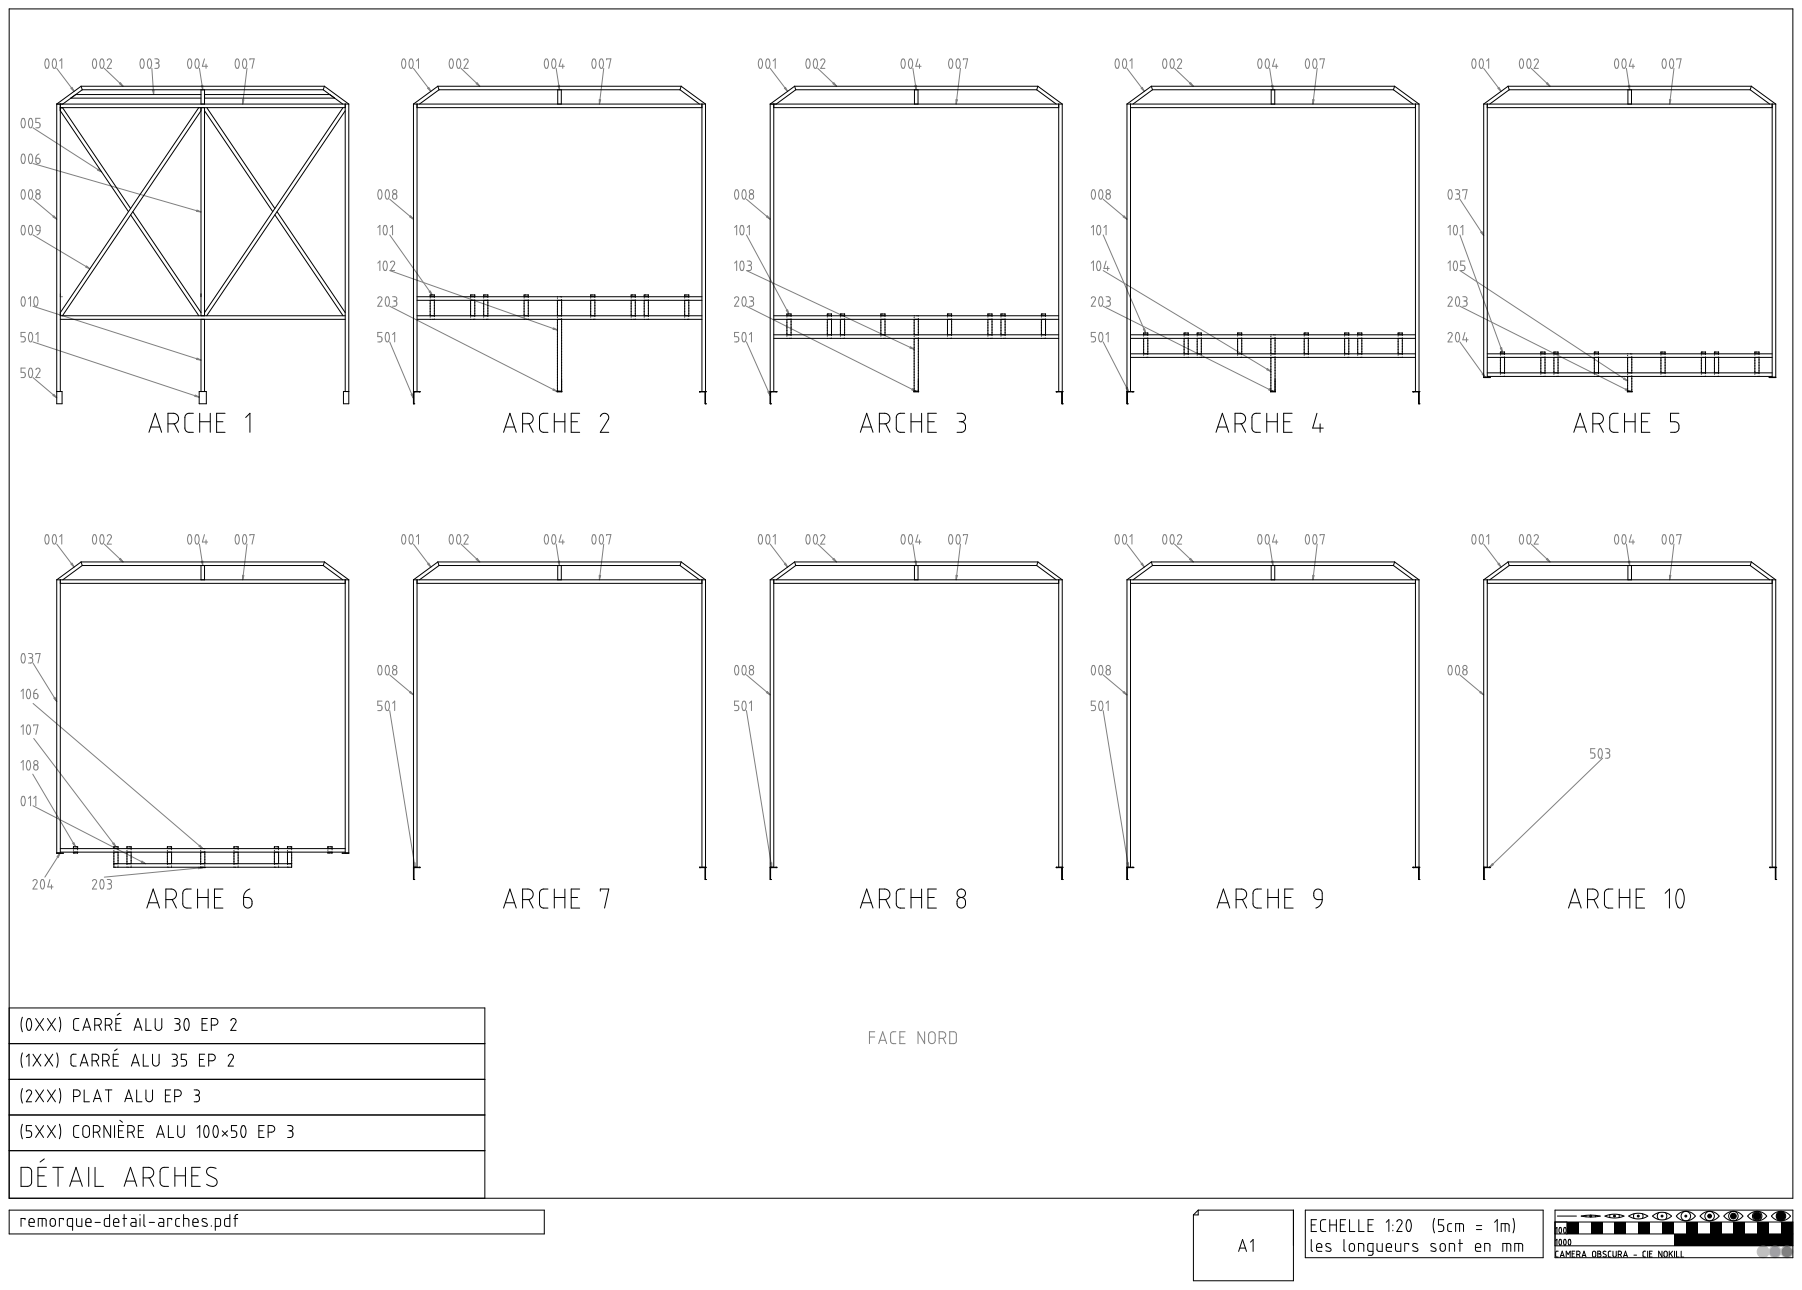
[picture p379: page 1]
