LeonLenclos/camera-obscura/contenu/plans/remorque-listes.pdf

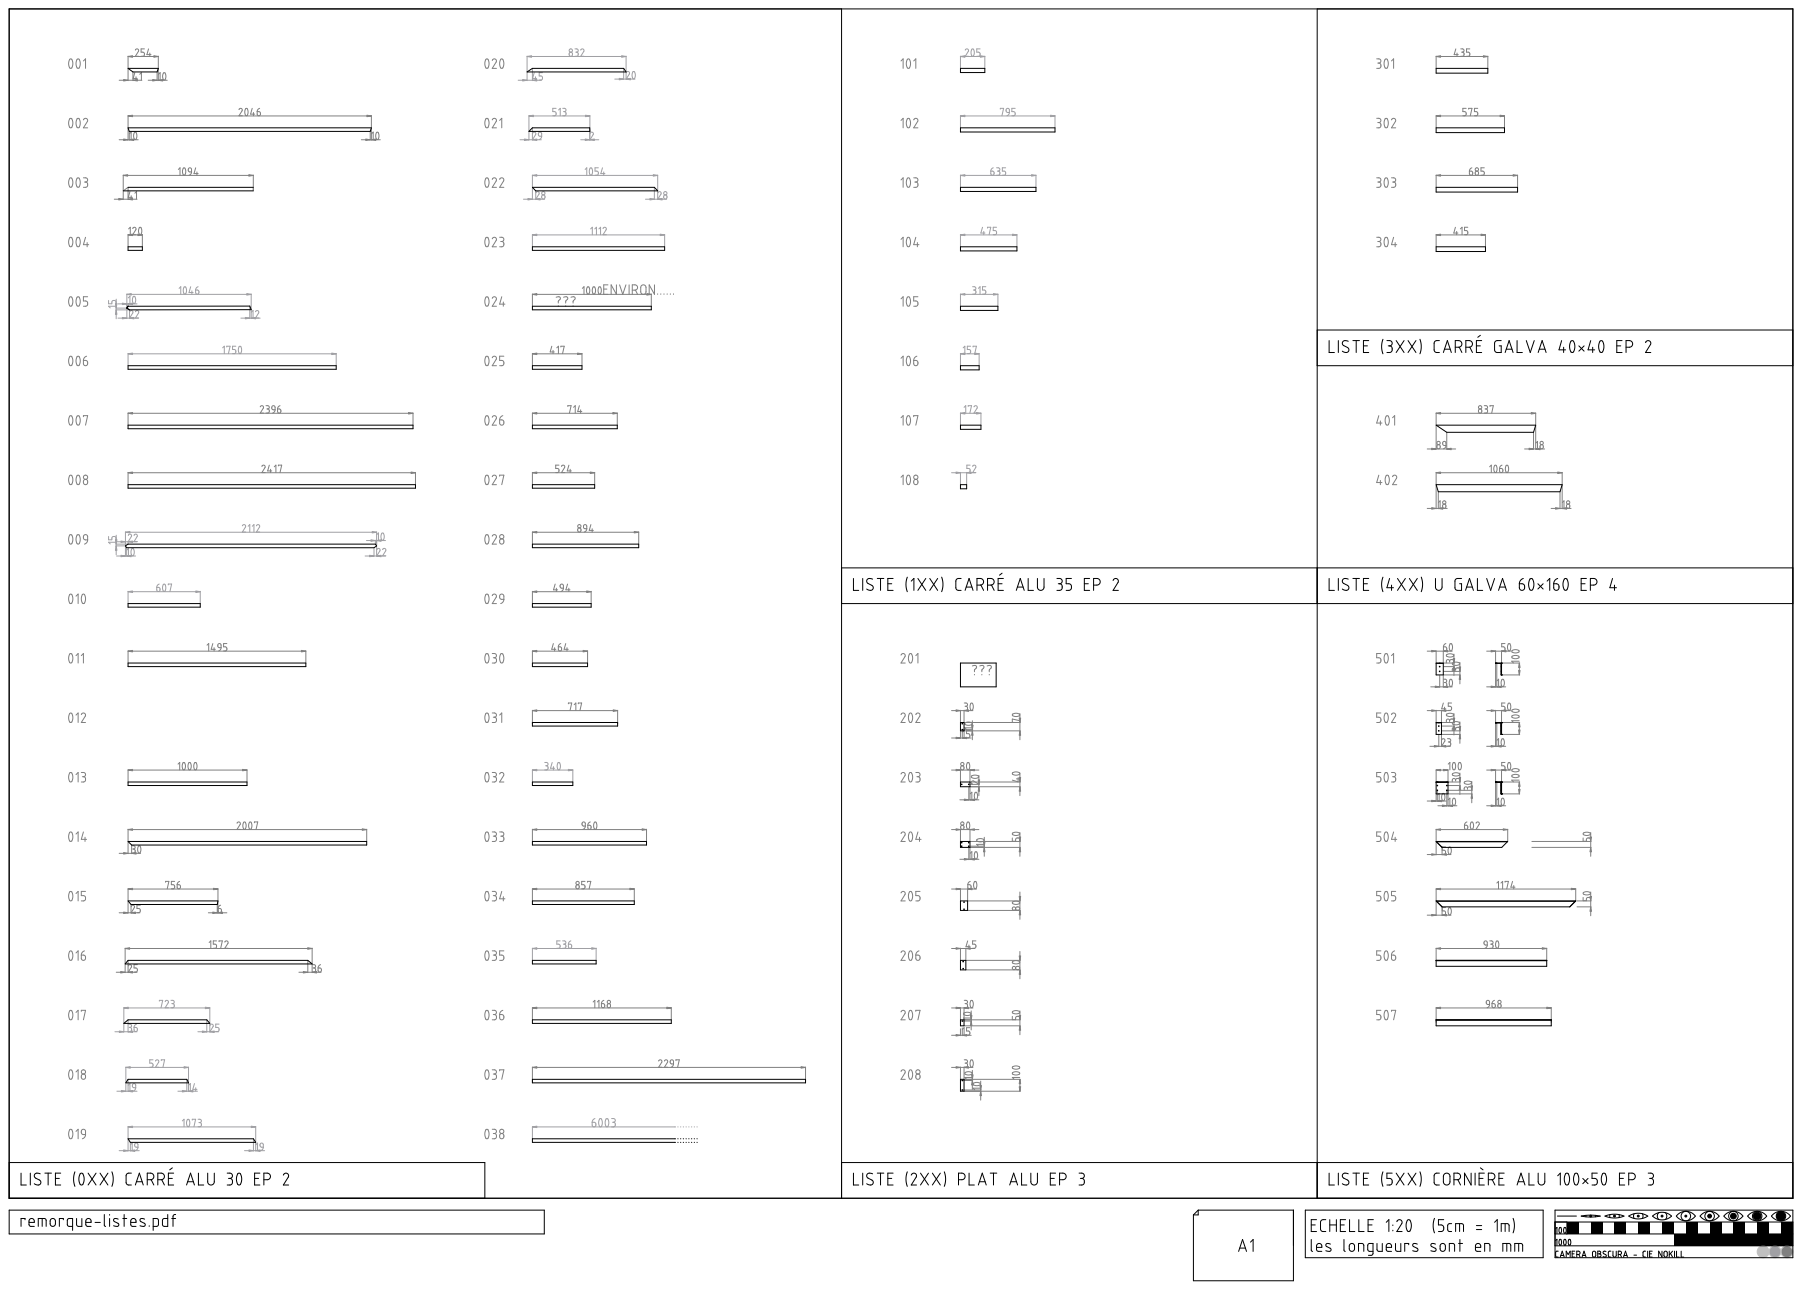
[picture p380: page 1]
