LeonLenclos/camera-obscura/contenu/plans/remorque-plateau.pdf

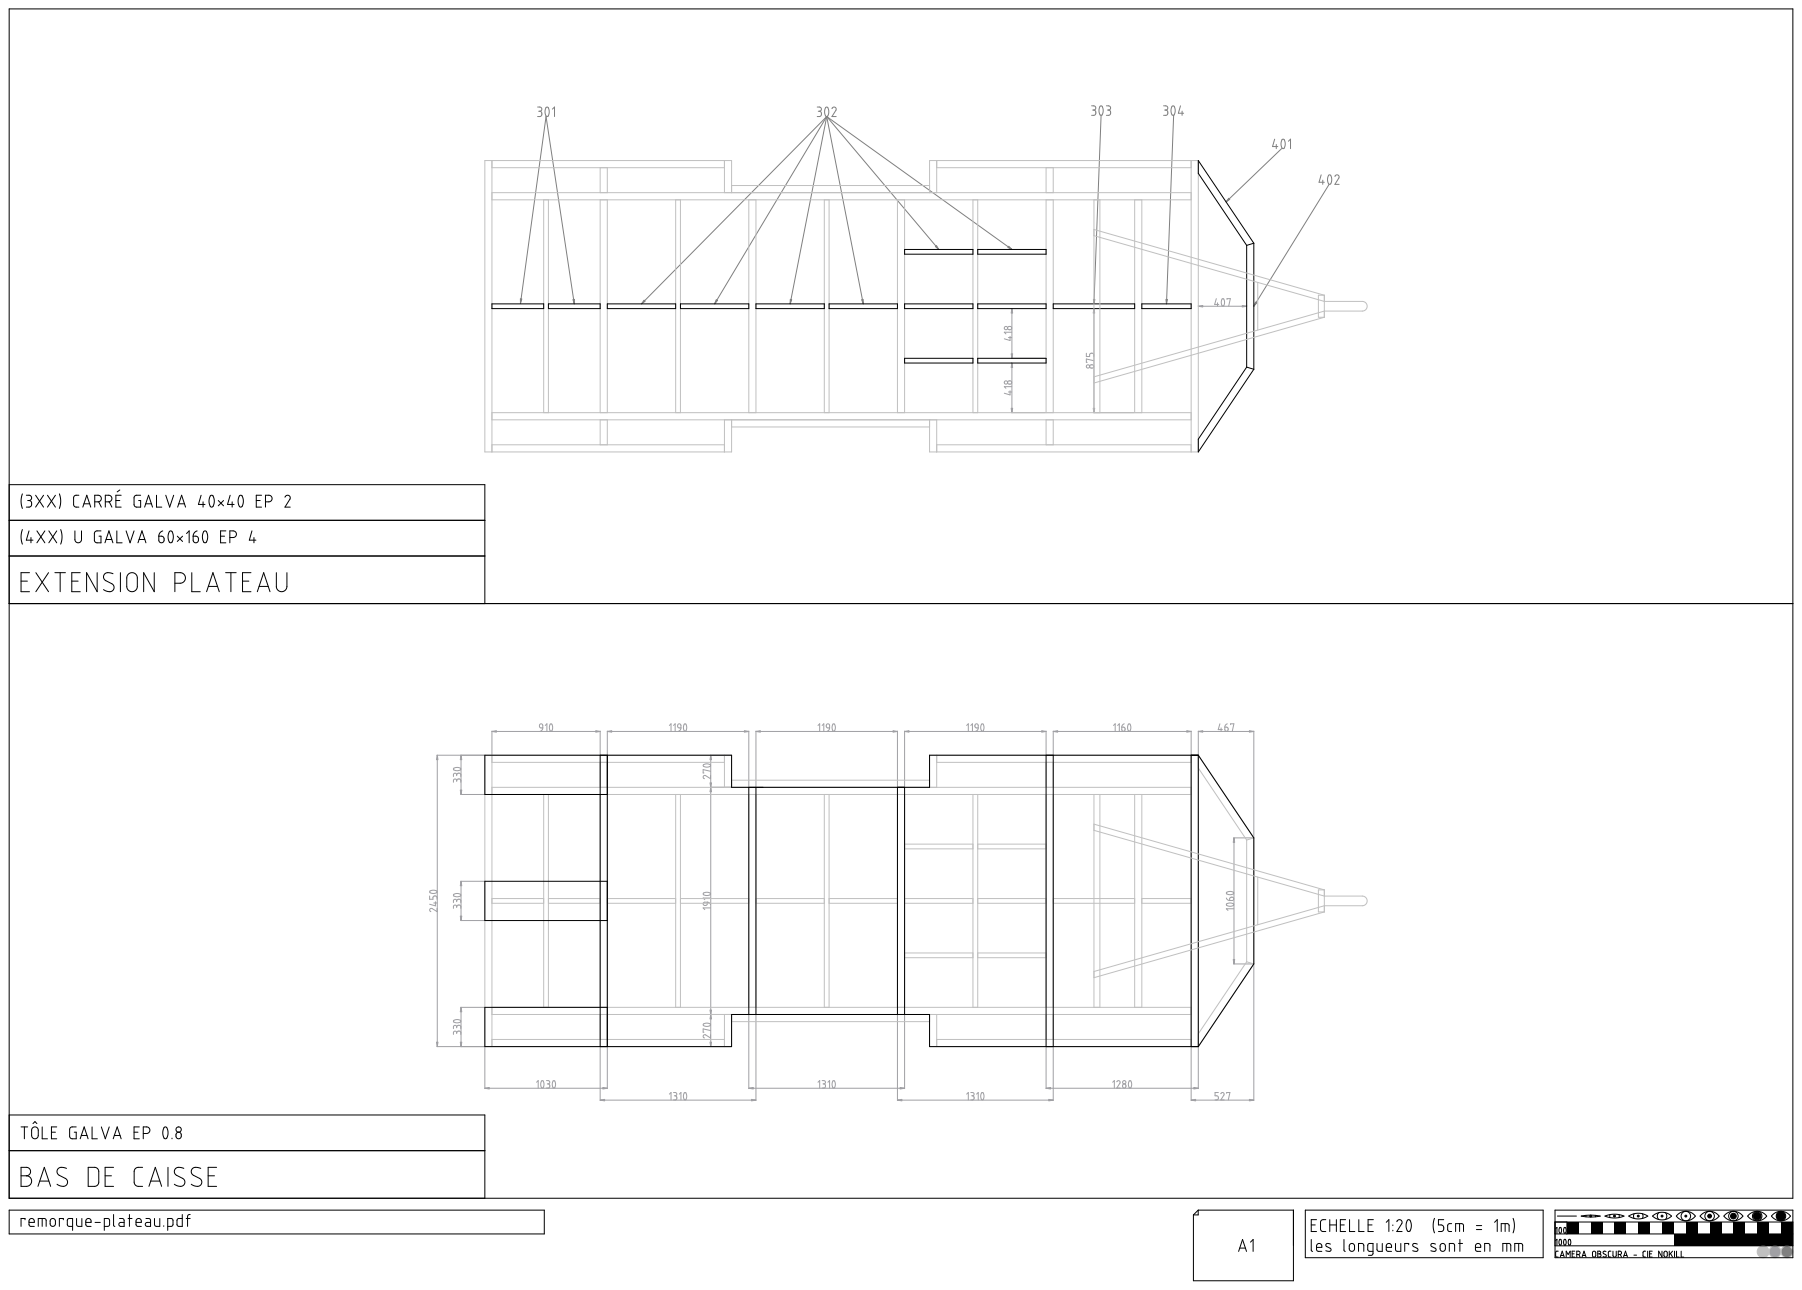
[picture p381: page 1]
