LeonLenclos/camera-obscura/contenu/plans/remorque-renforts.pdf

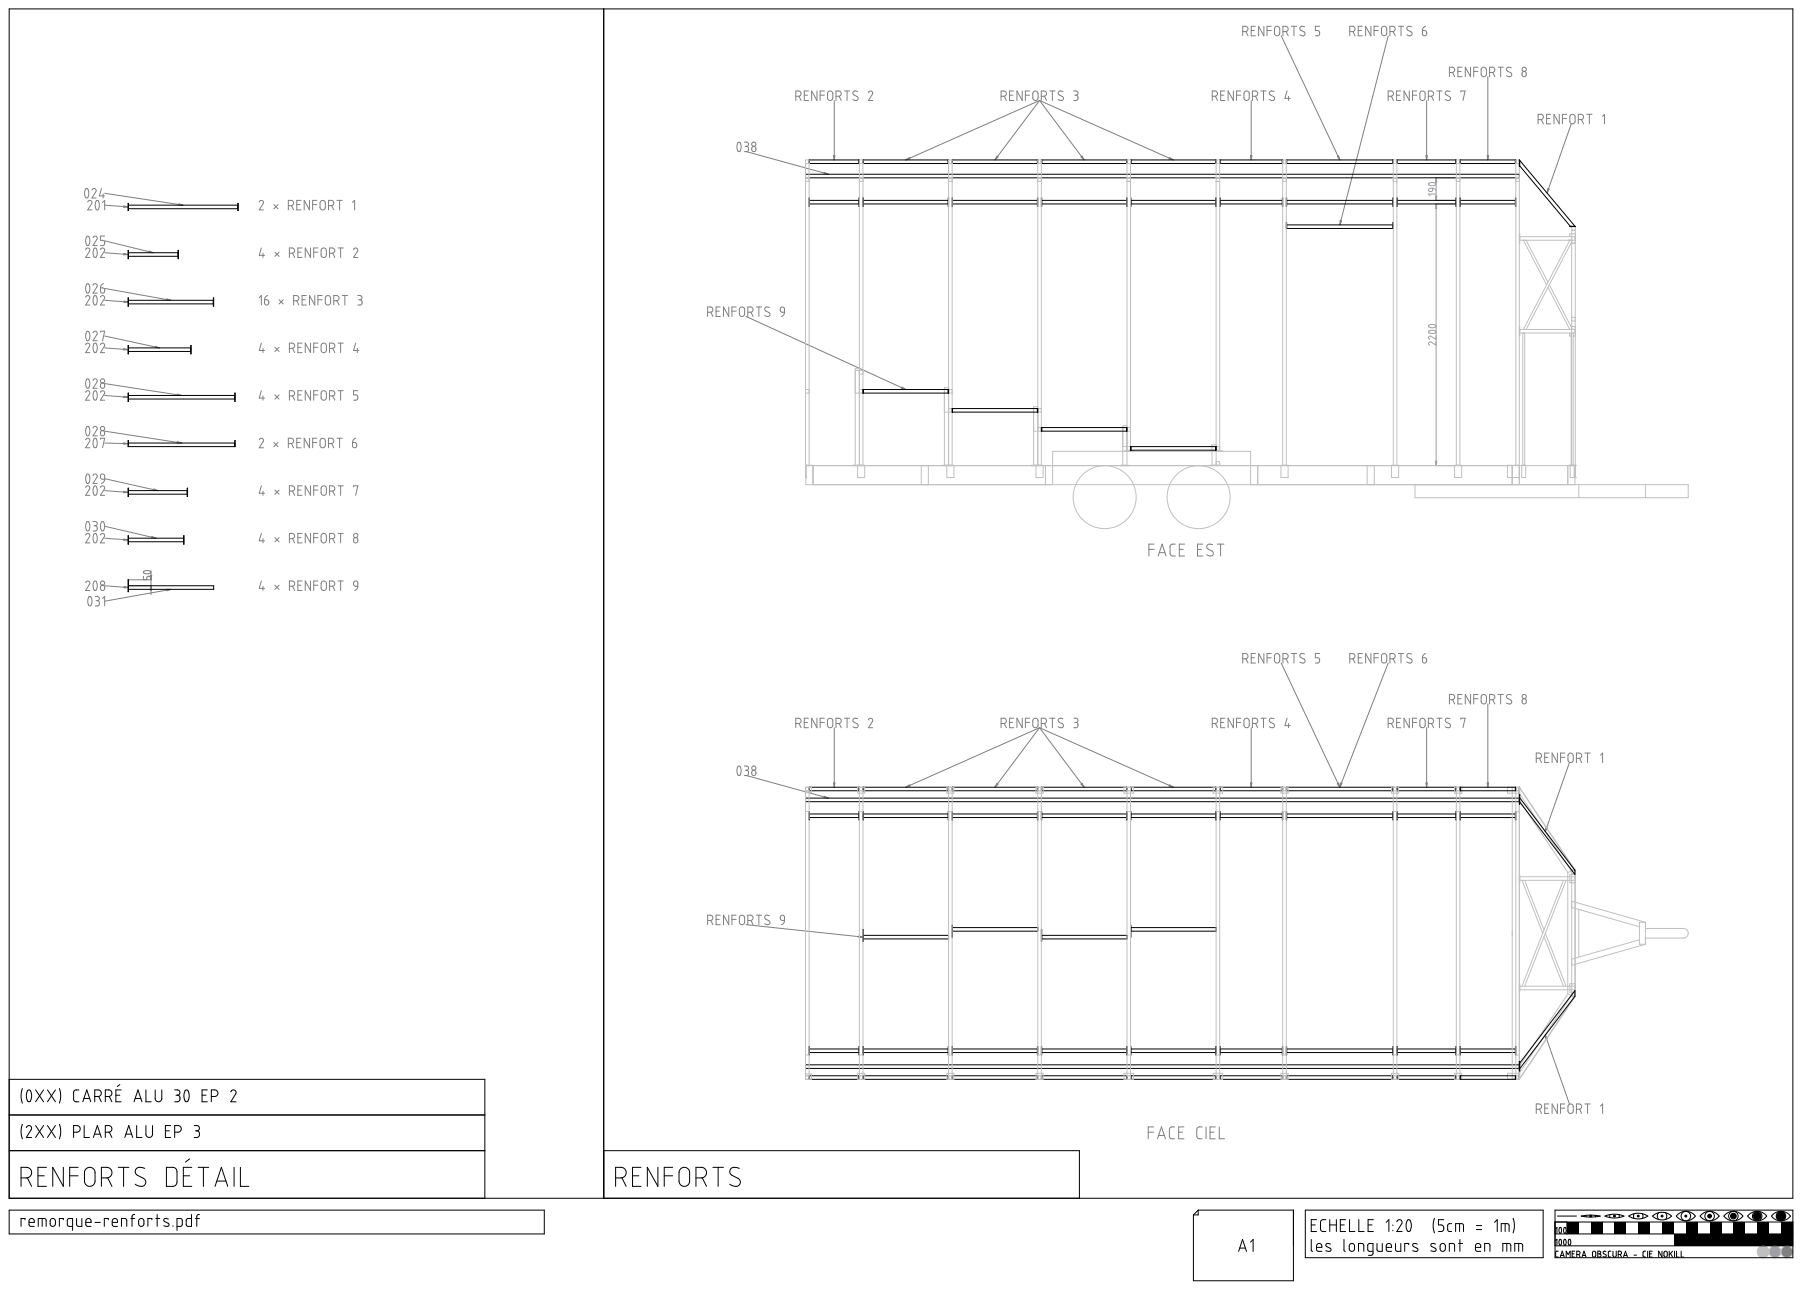
[picture p382: page 1]
