LeonLenclos/camera-obscura/contenu/plans/remorque-sieges.pdf

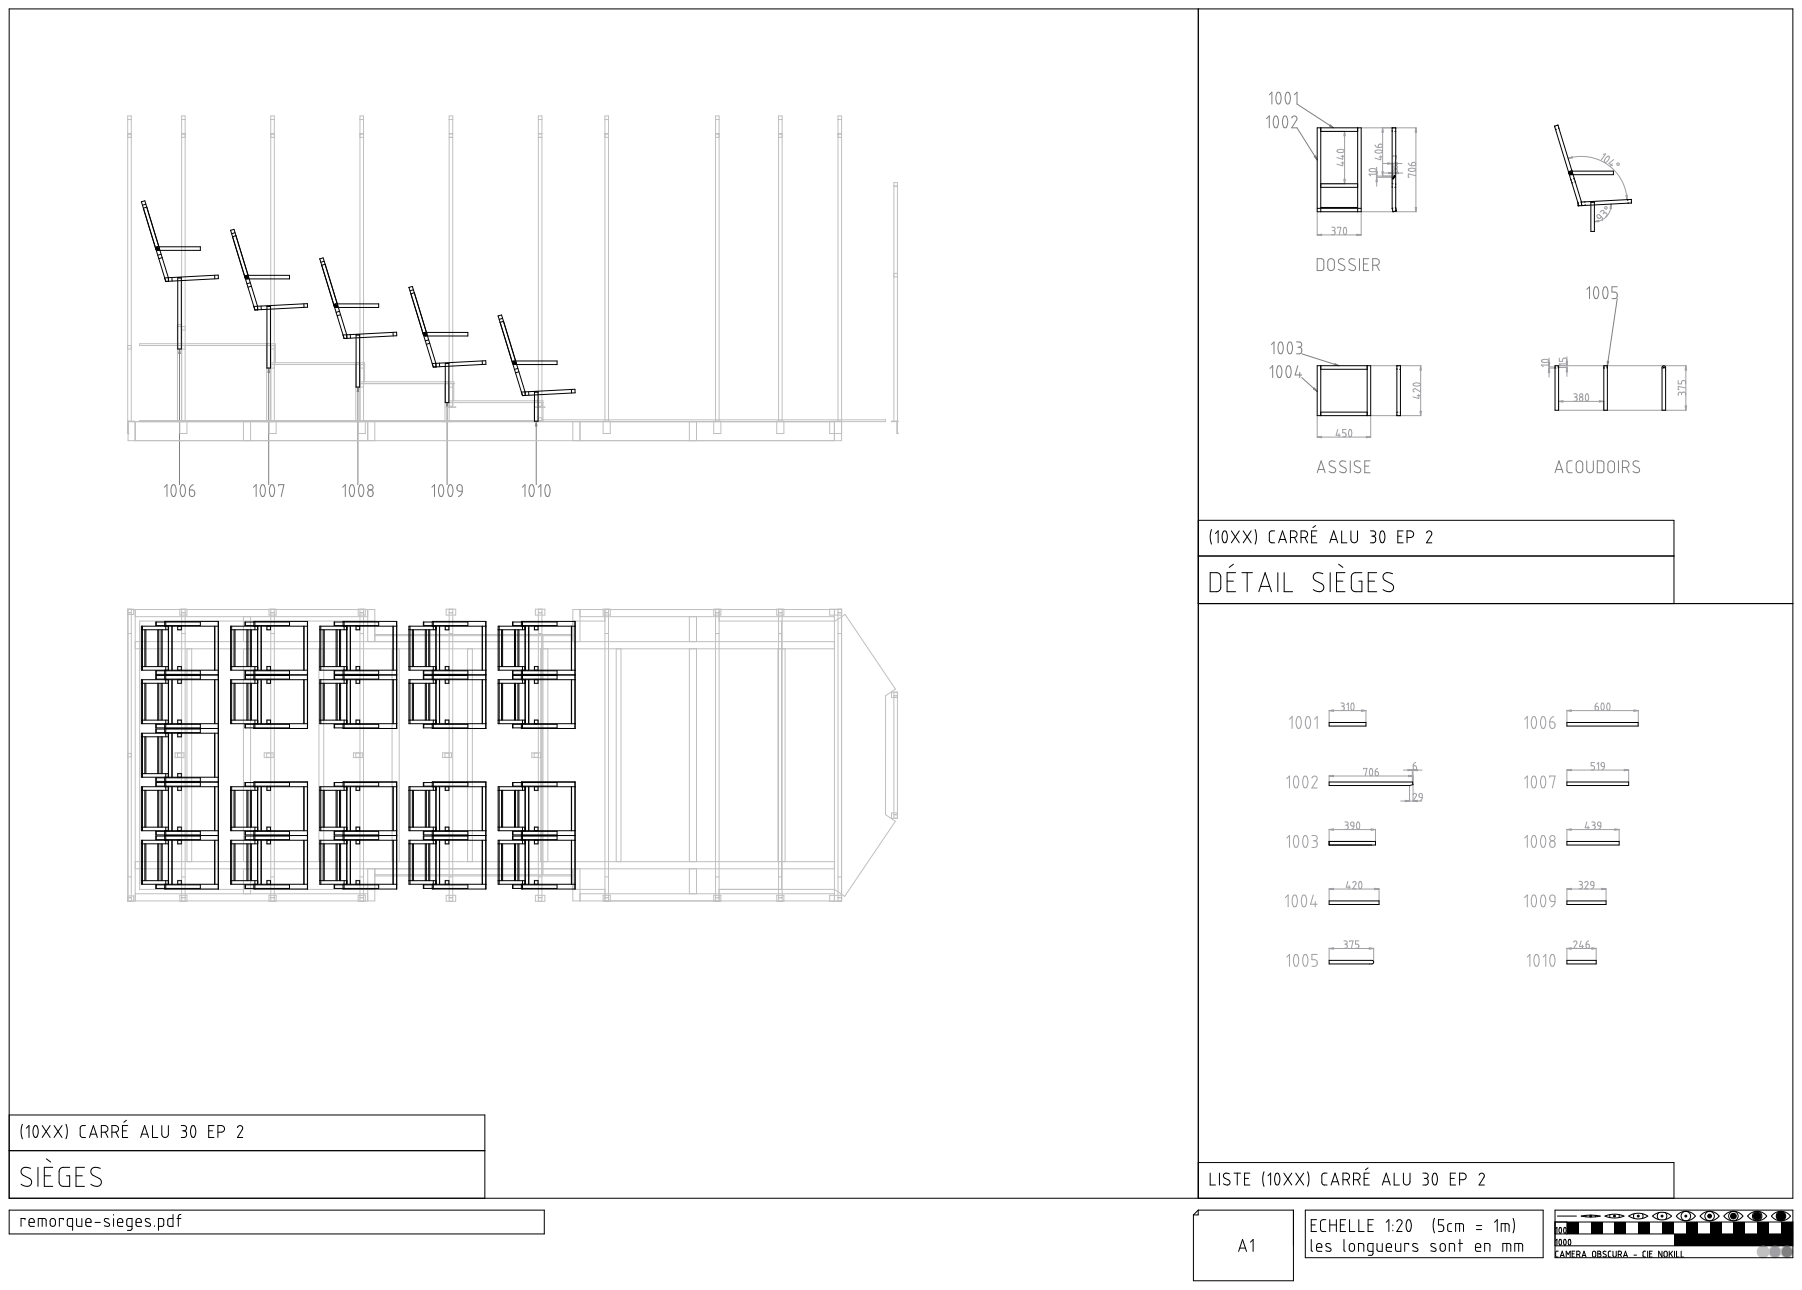
[picture p383: page 1]
