LeonLenclos/camera-obscura/contenu/plans/remorque-sol.pdf

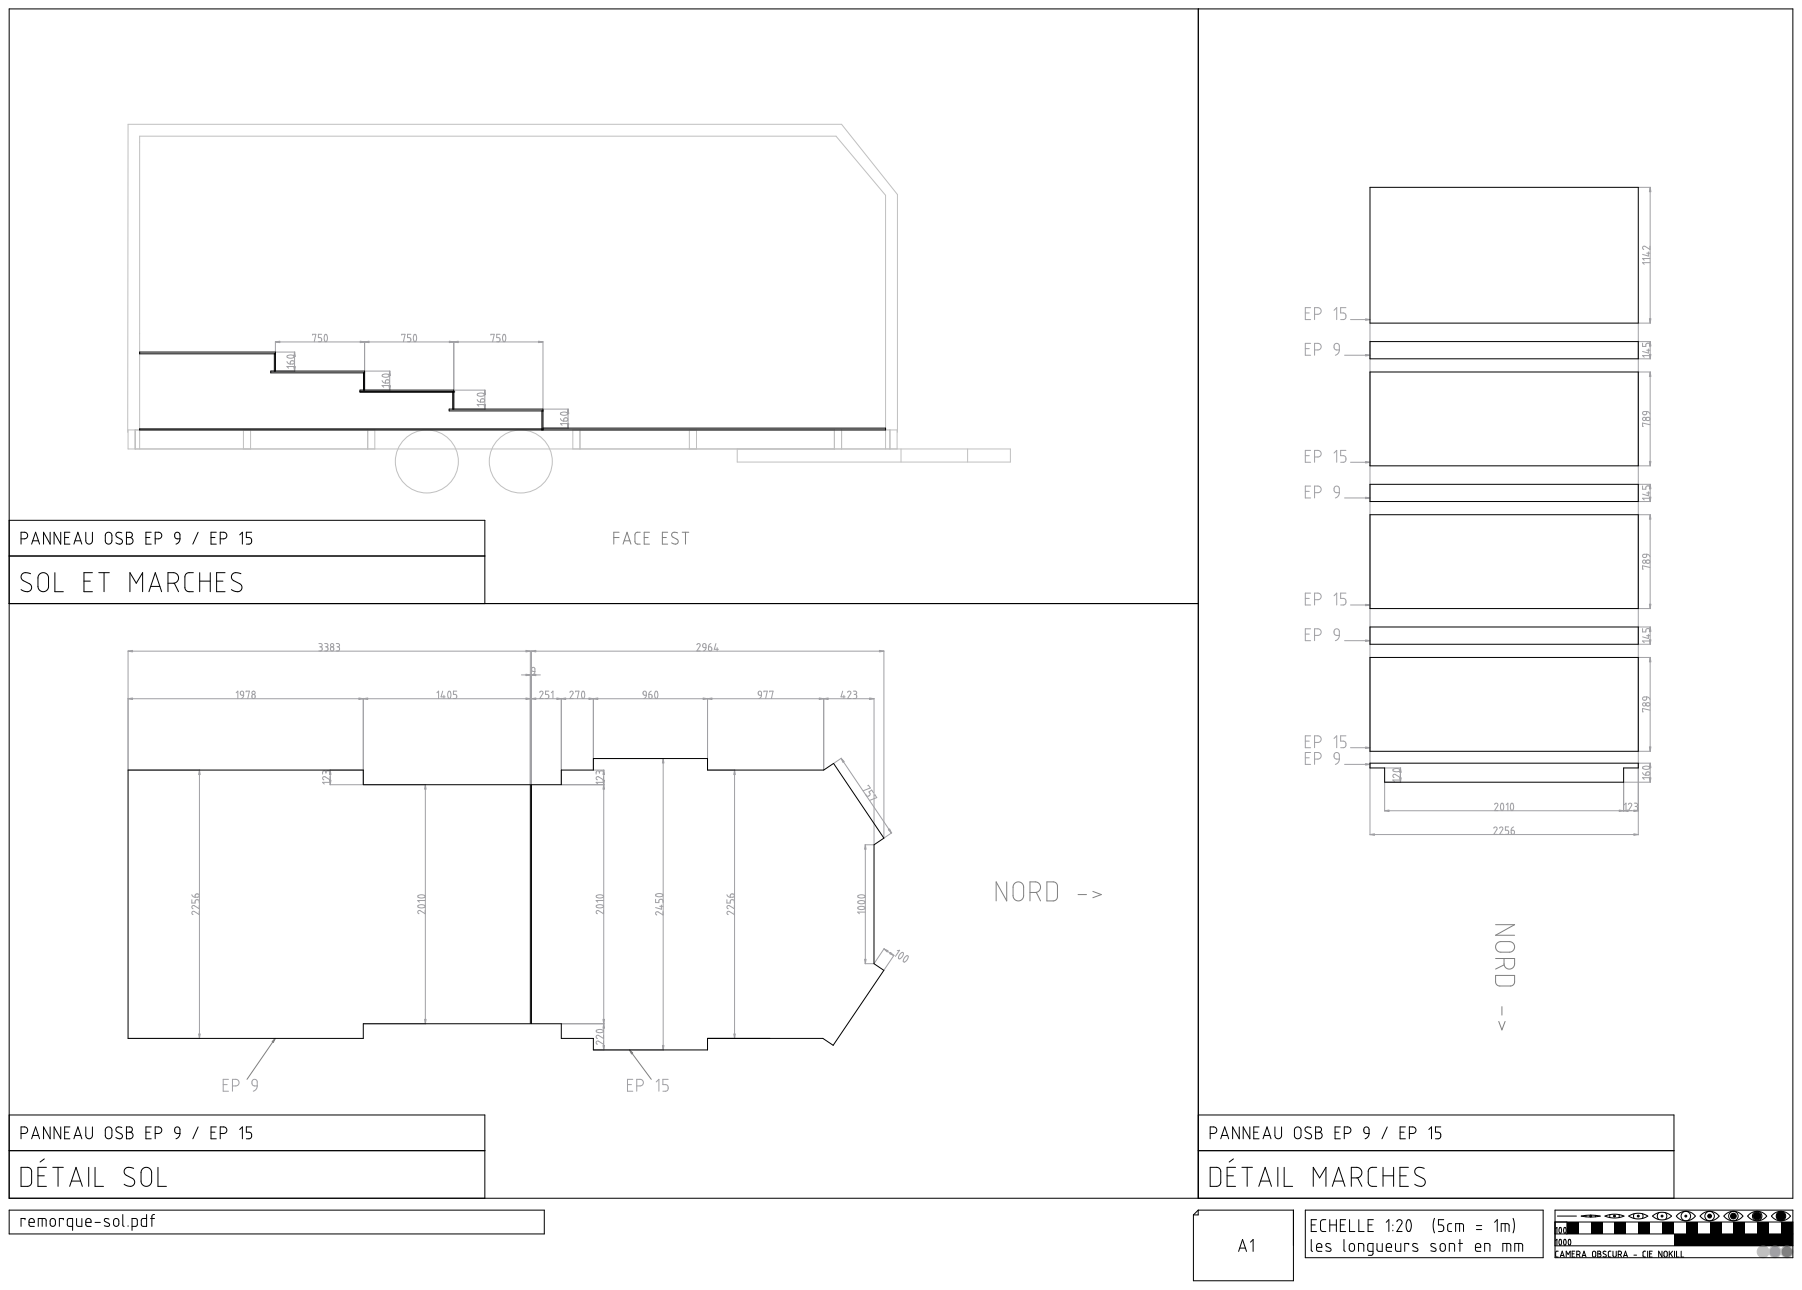
[picture p384: page 1]
