LeonLenclos/camera-obscura/contenu/plans/remorque.pdf

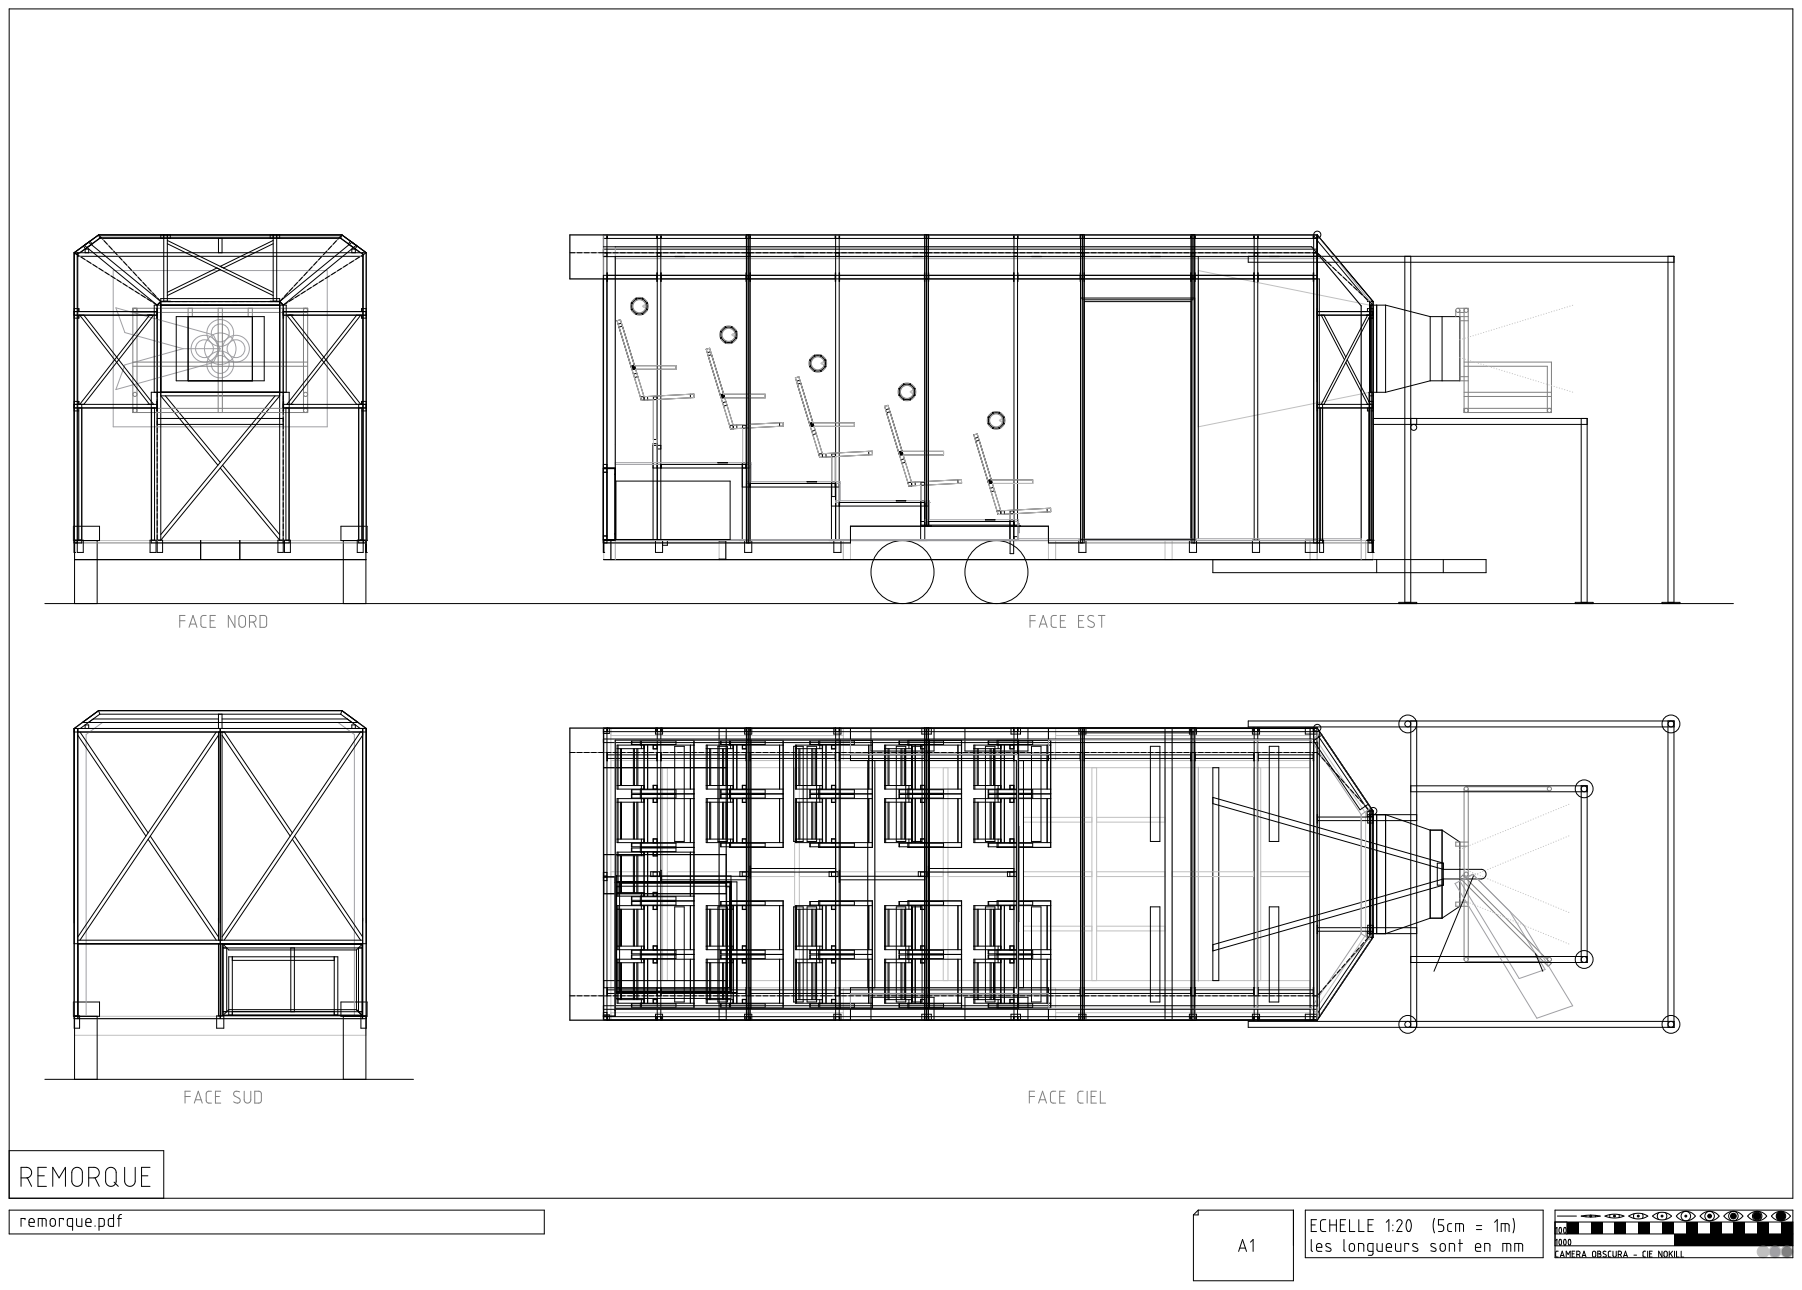
[picture p385: page 1]
