LeonLenclos/camera-obscura/contenu/plans/hublots.pdf

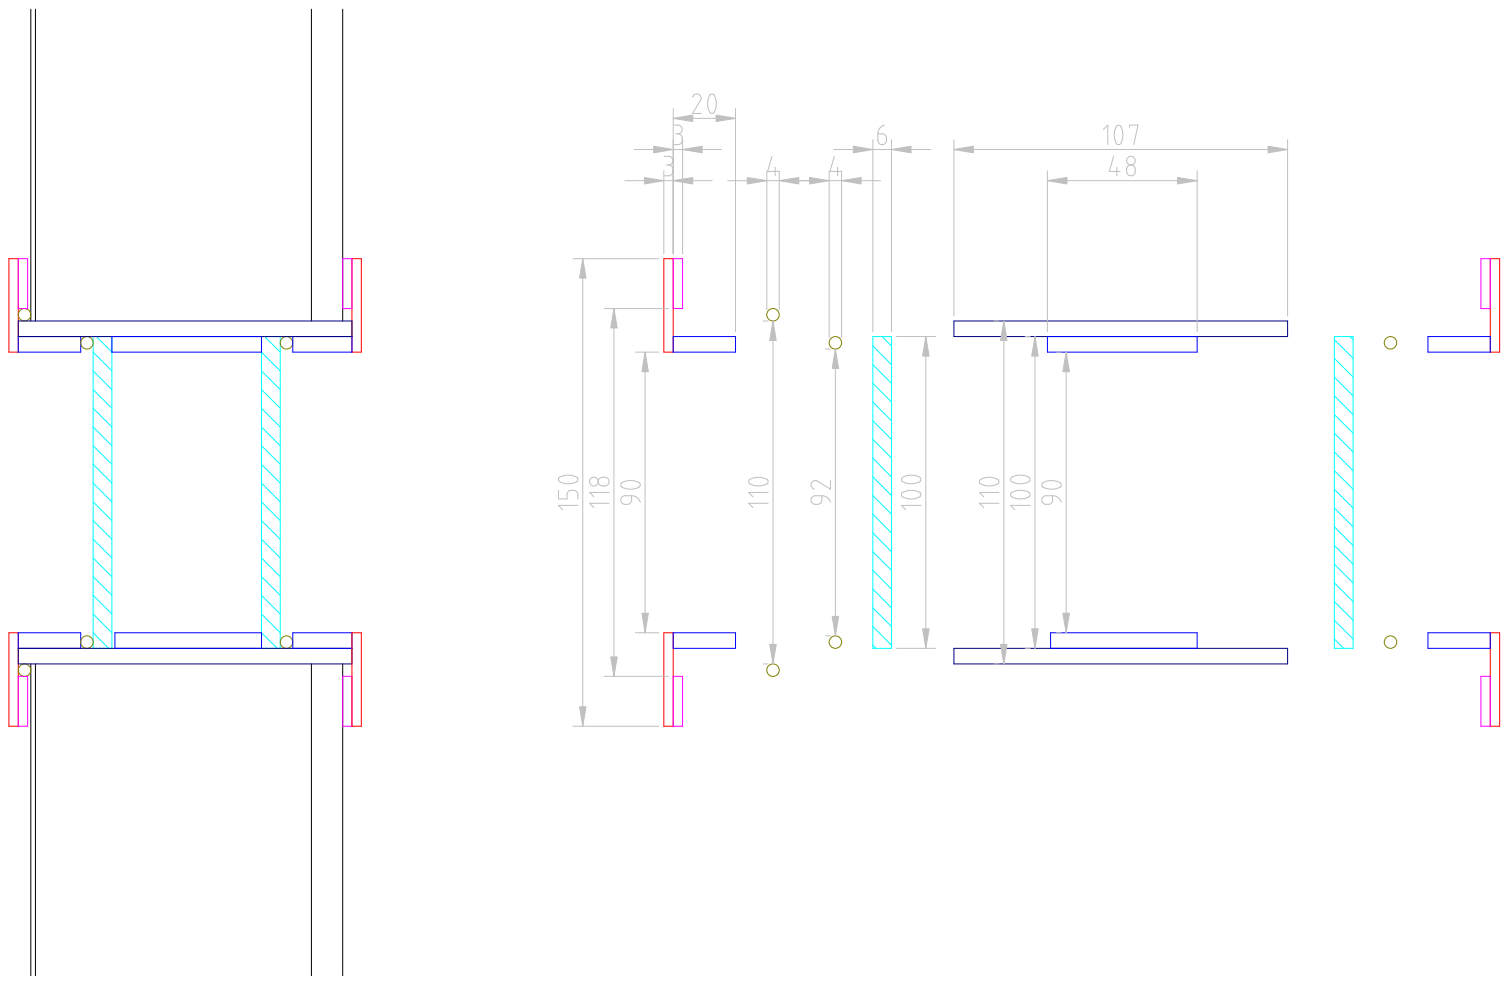
[picture p386: page 1]
