LeonLenclos/camera-obscura/contenu/plans/mirroir-a-45-structure.pdf

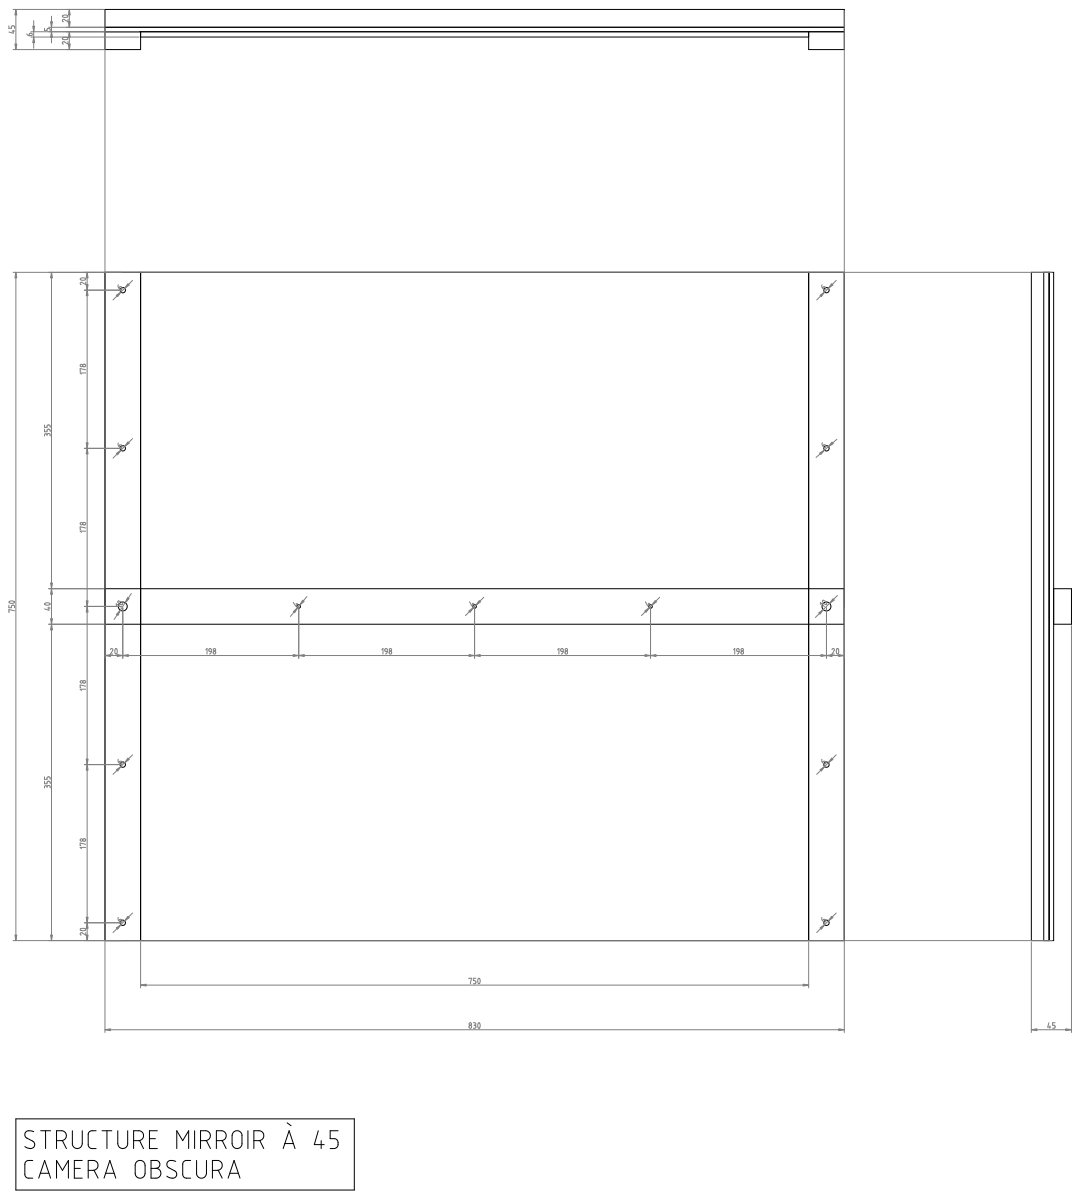
[picture p387: page 1]
