LeonLenclos/camera-obscura/contenu/animations/pixart/comportement-1-pixart-artwork.pdf

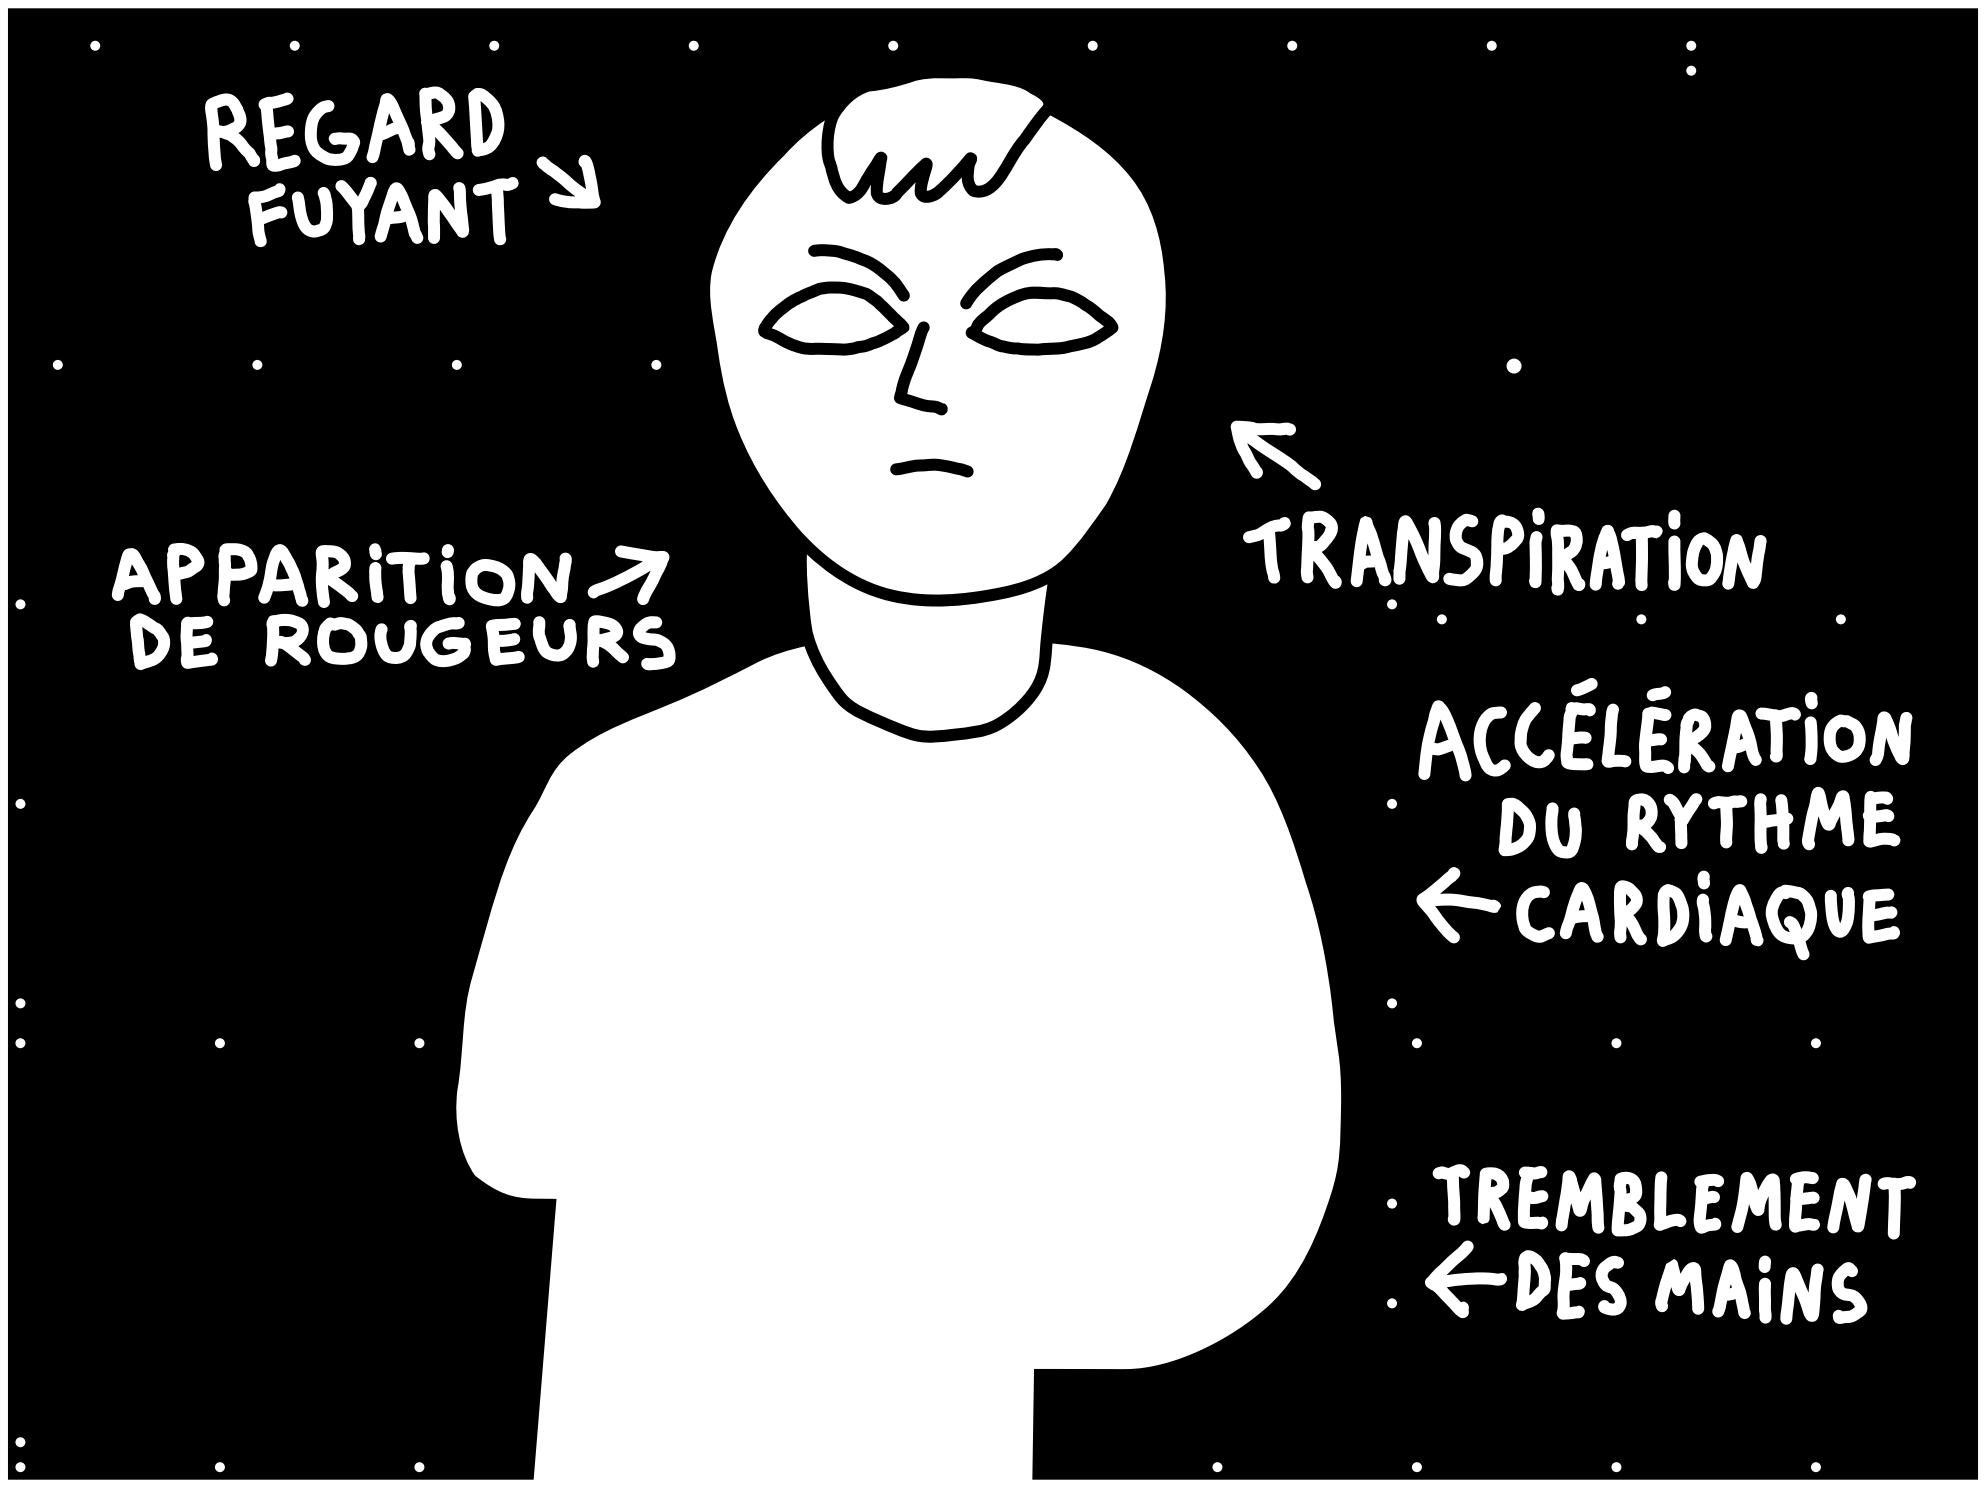
[picture p388: page 1]
