LeonLenclos/camera-obscura/contenu/animations/pixart/comportement-1-pixart-white.pdf

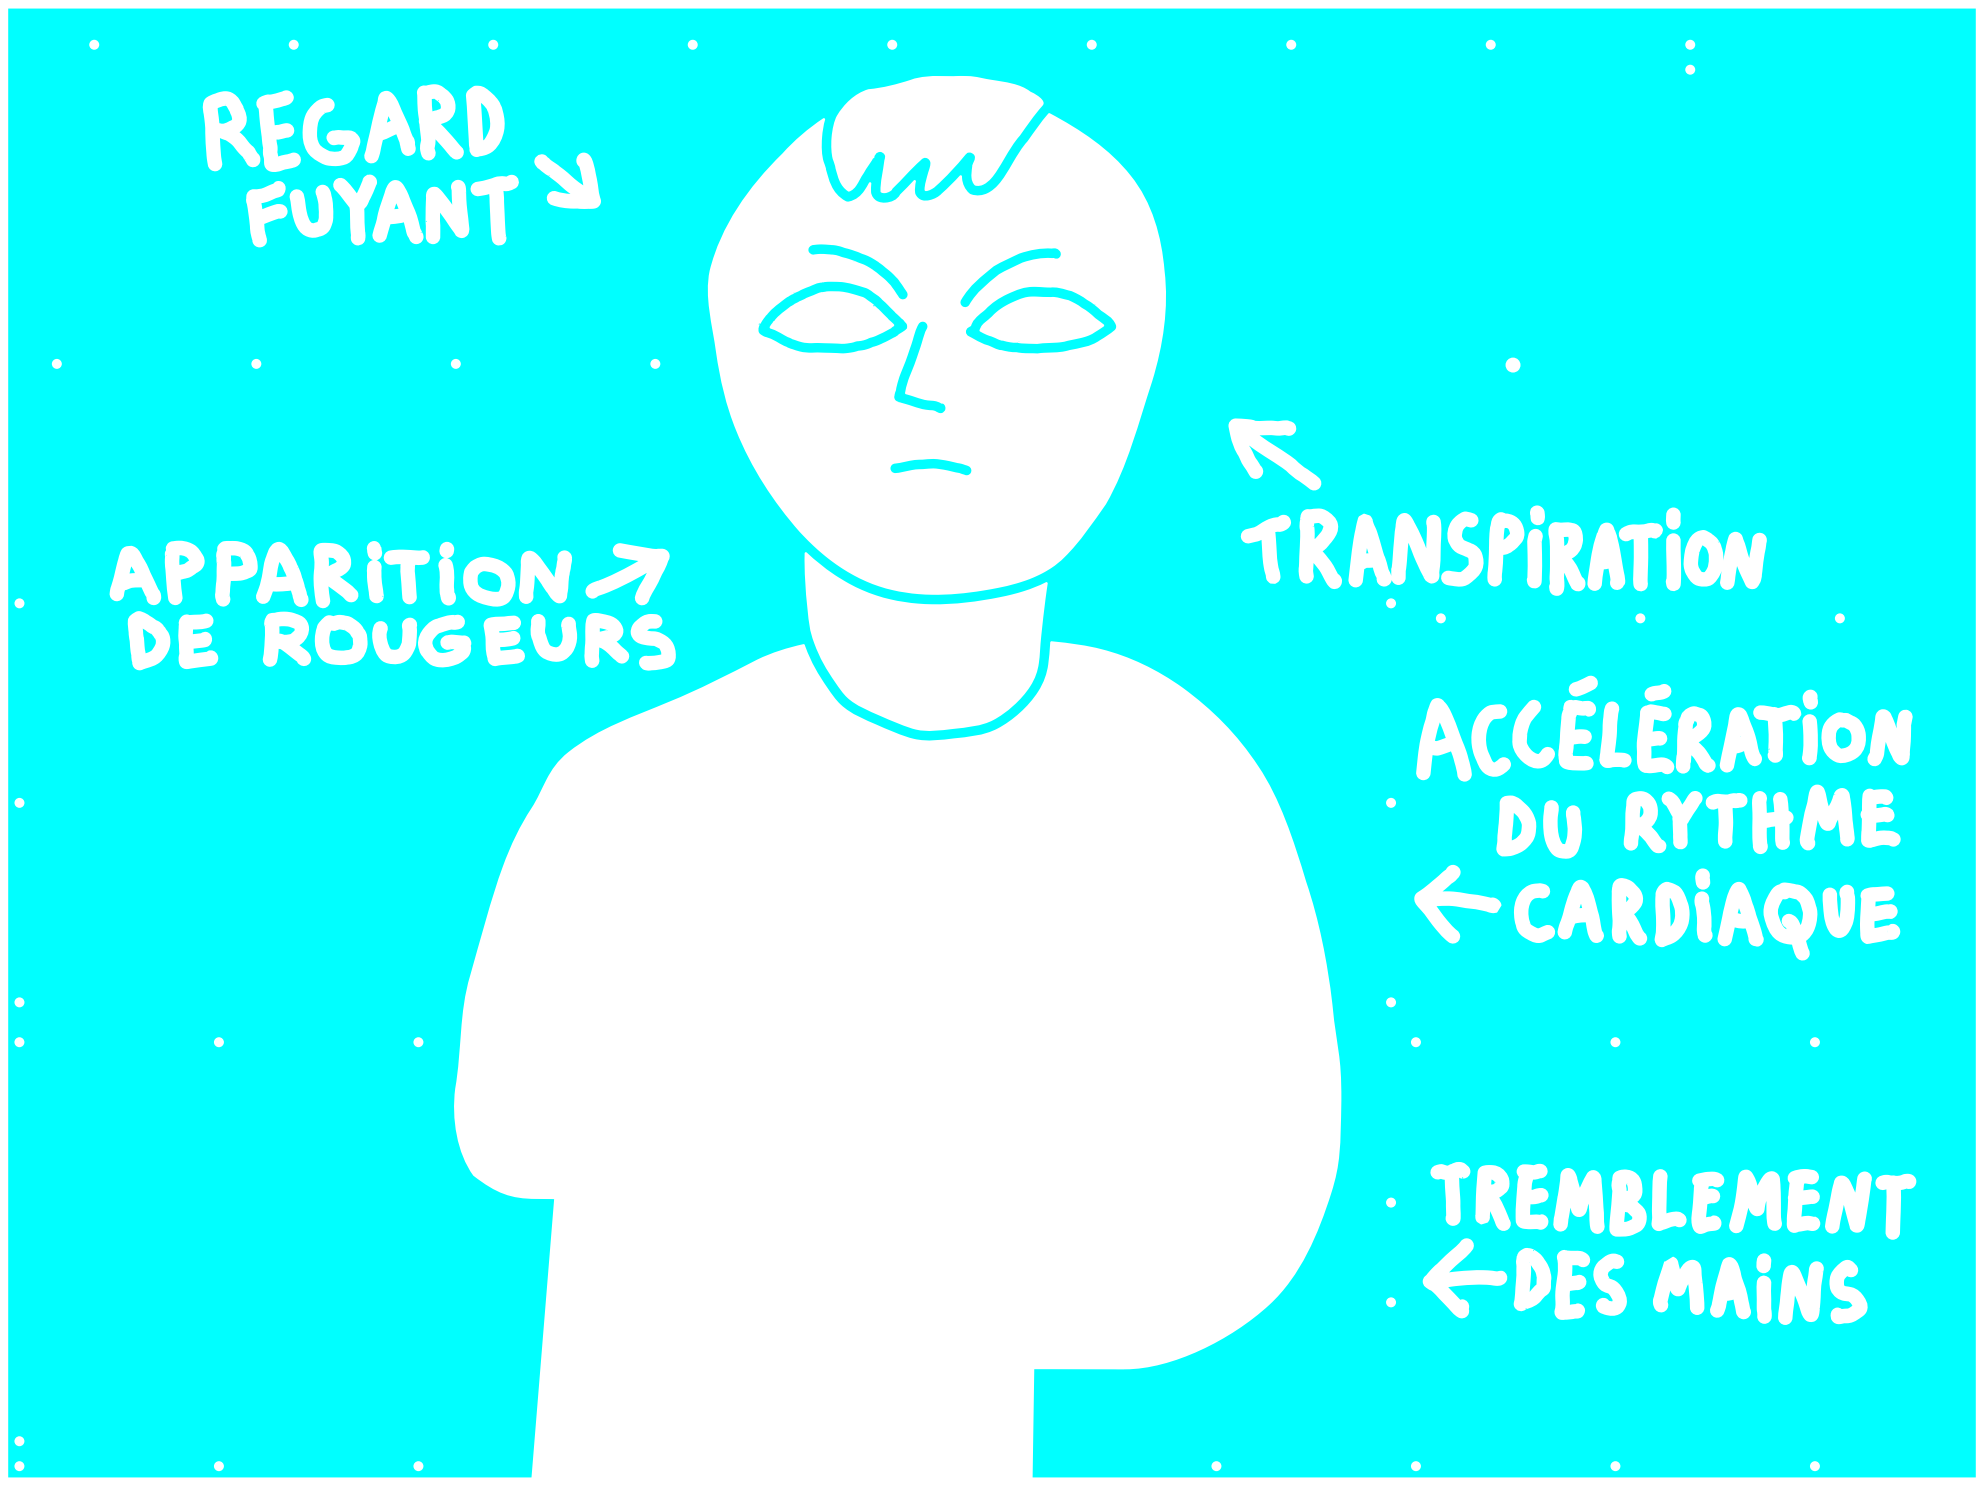
[picture p389: page 1]
