LeonLenclos/camera-obscura/contenu/animations/pixart/comportement-1-pixart.pdf

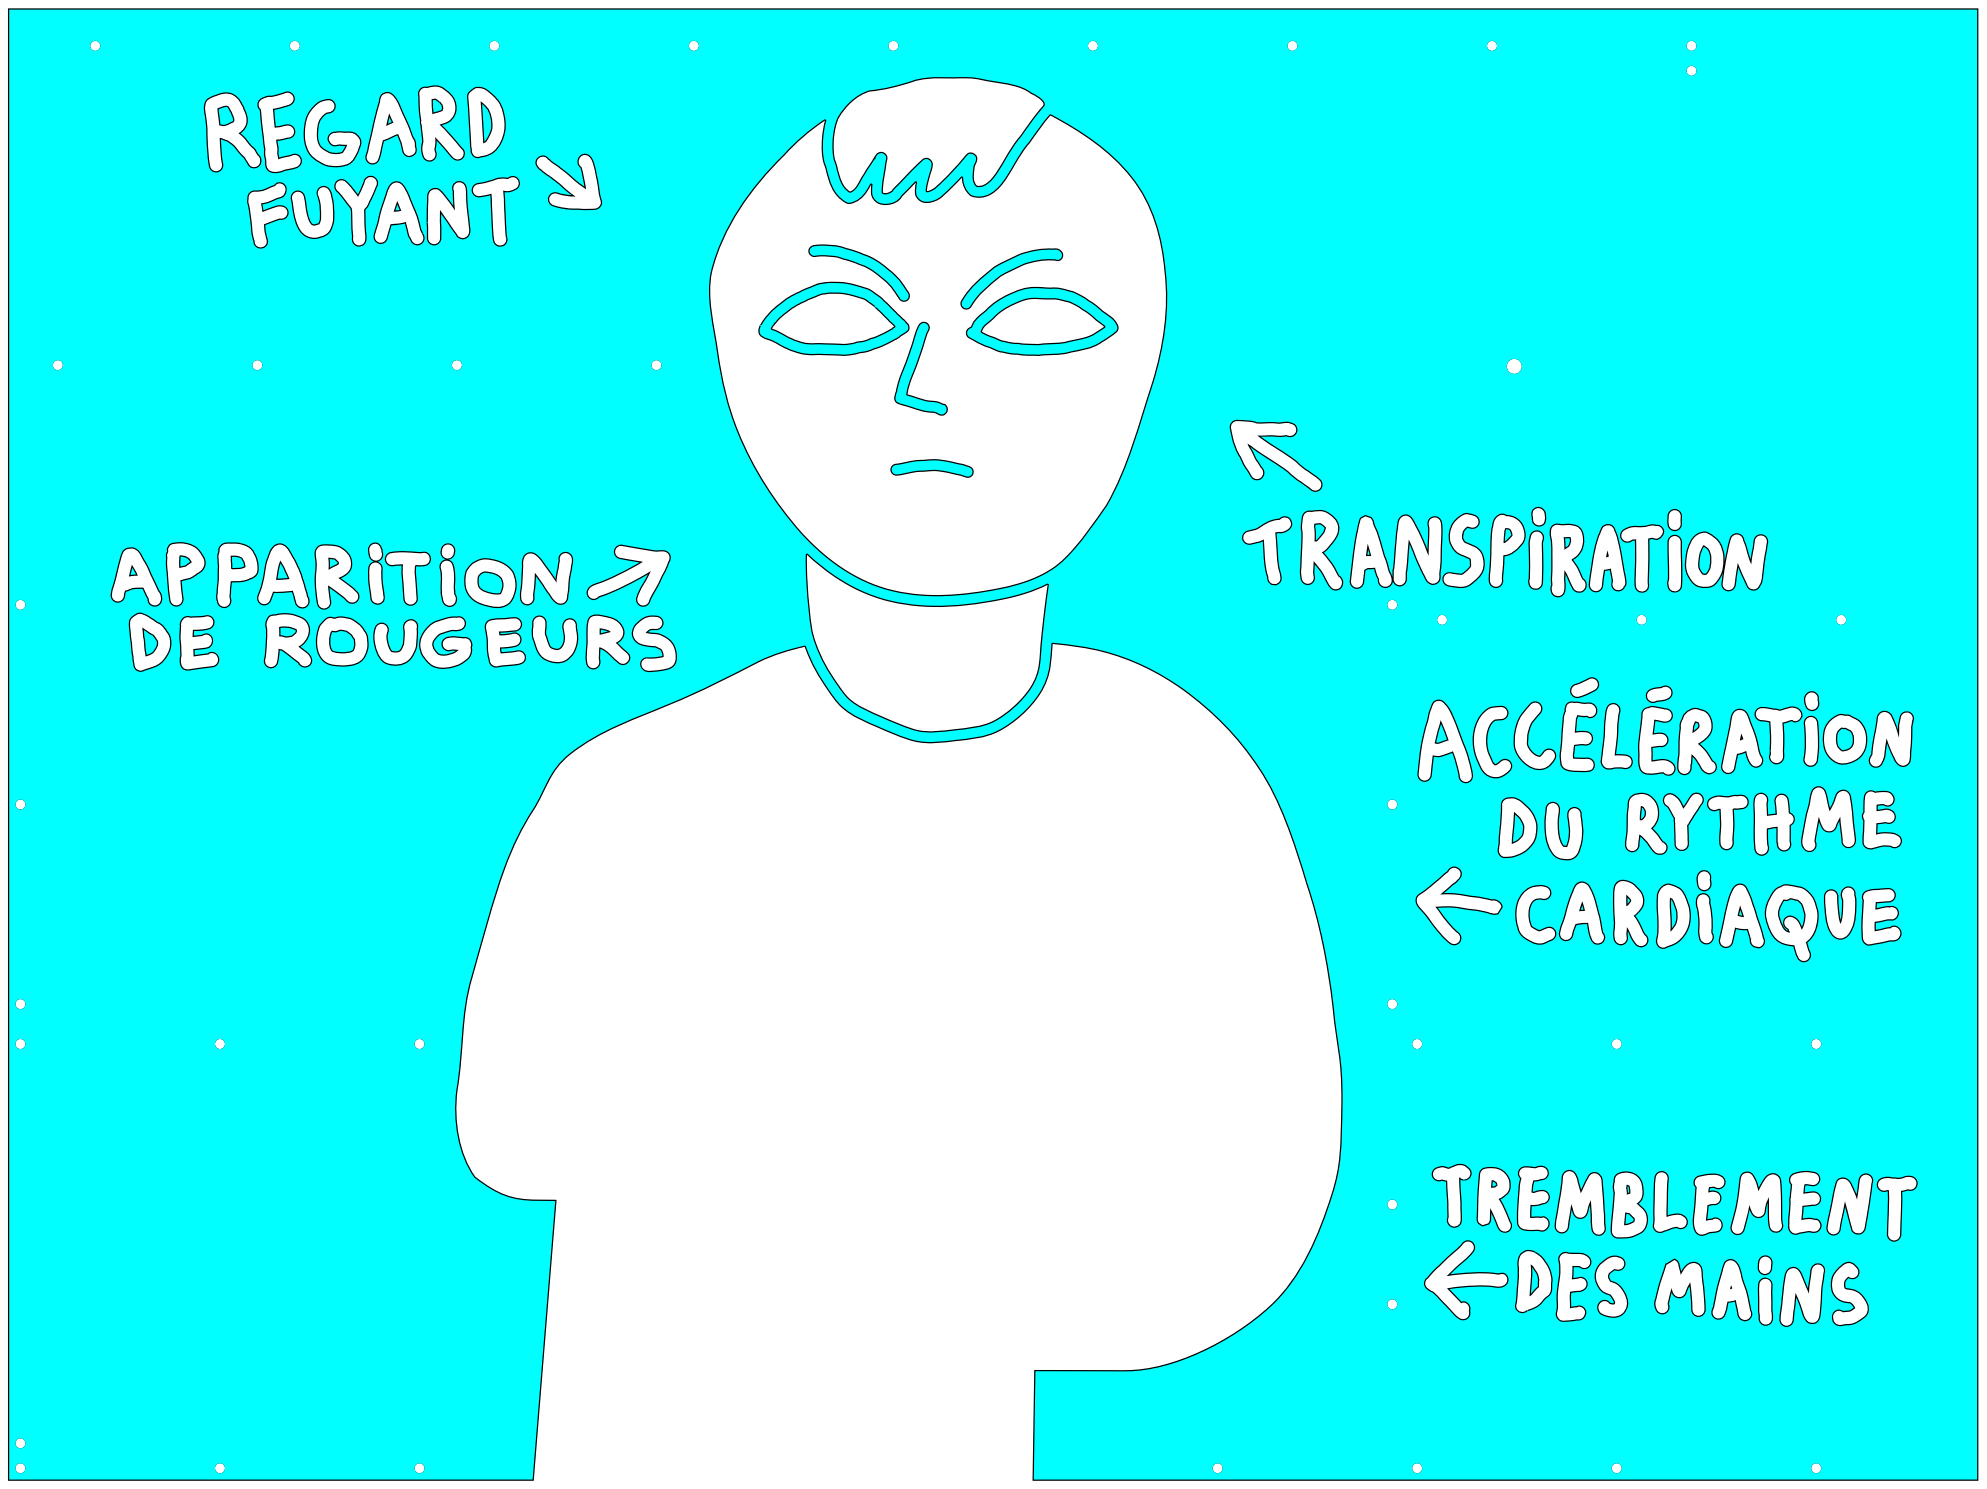
[picture p390: page 1]
