LeonLenclos/camera-obscura/contenu/animations/pixart/comportement-2-pixart-artwork.pdf

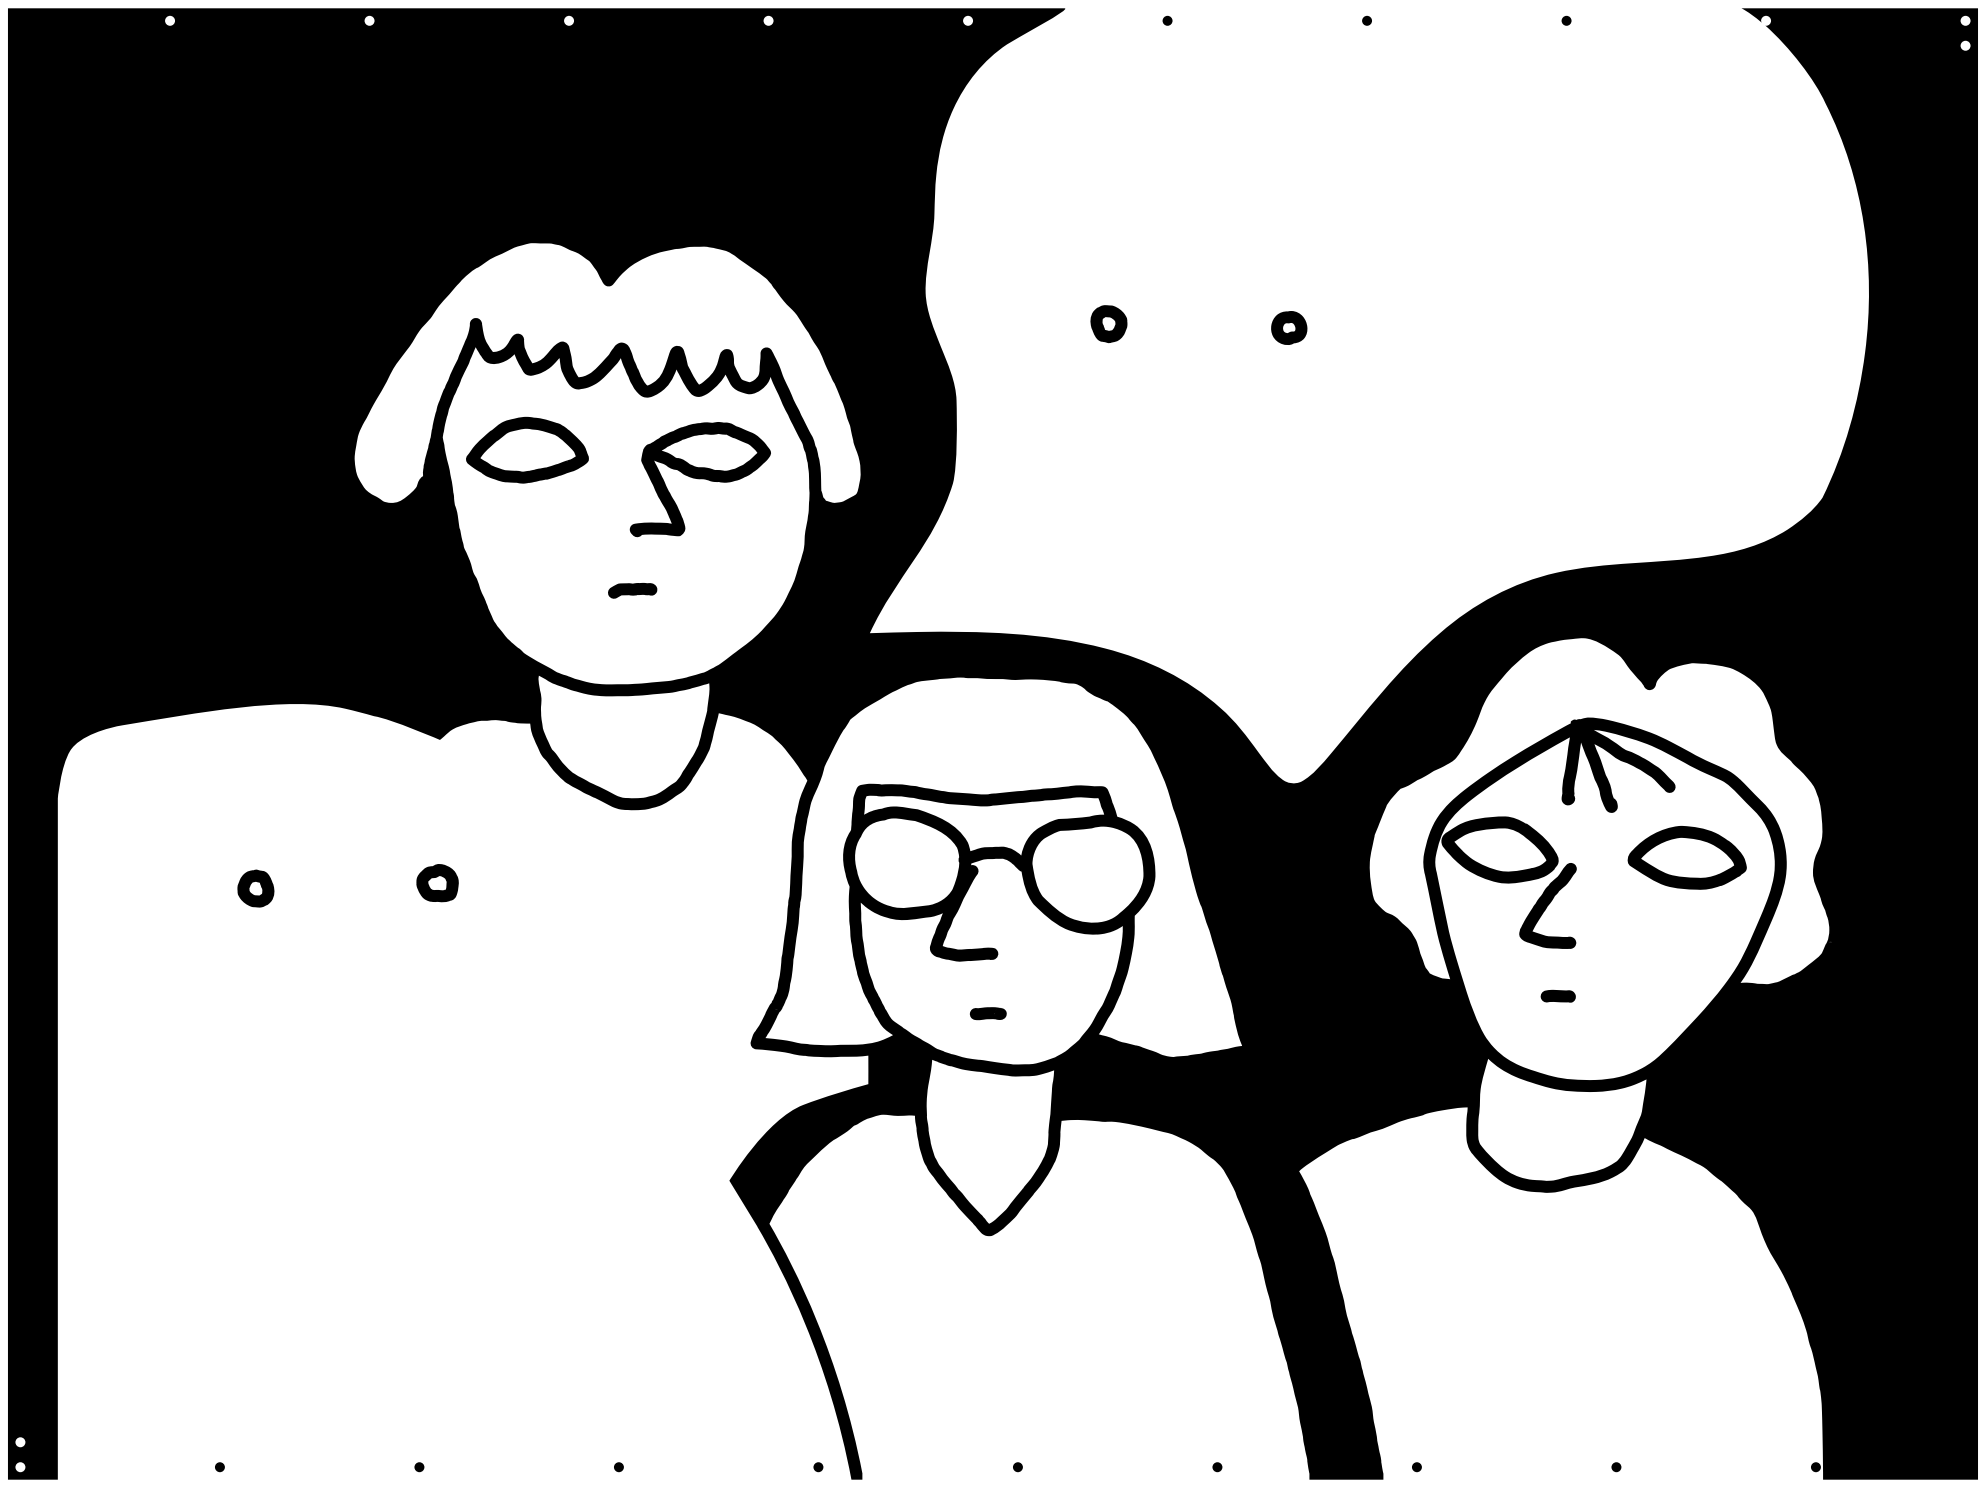
[picture p391: page 1]
