LeonLenclos/camera-obscura/contenu/animations/pixart/comportement-2-pixart-white.pdf

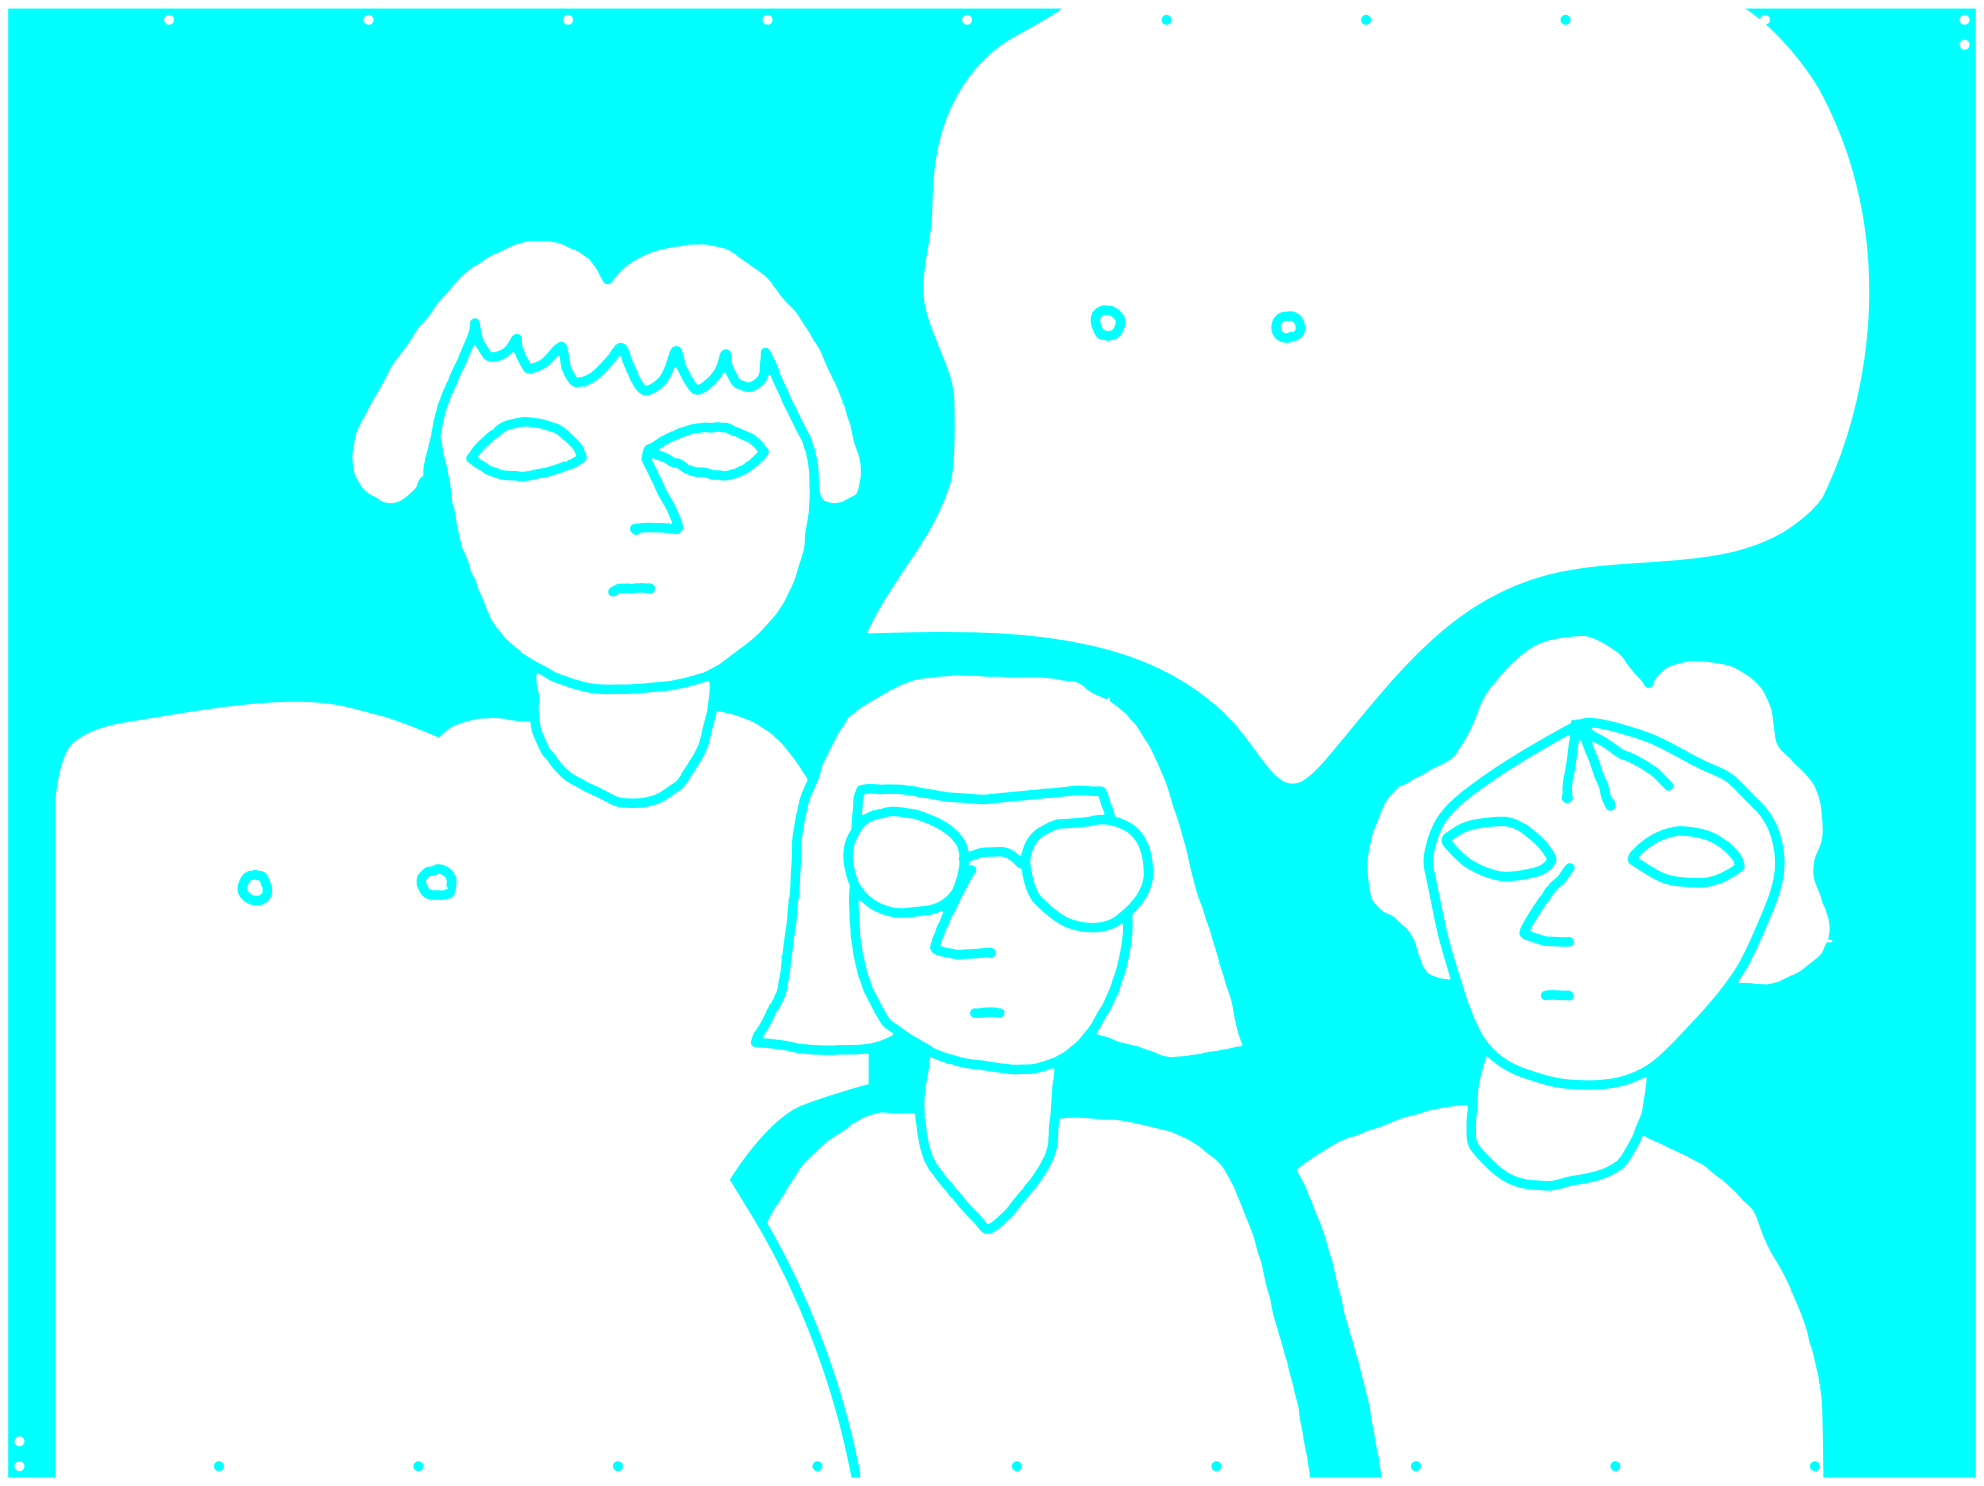
[picture p392: page 1]
