LeonLenclos/camera-obscura/contenu/animations/pixart/comportement-2-pixart.pdf

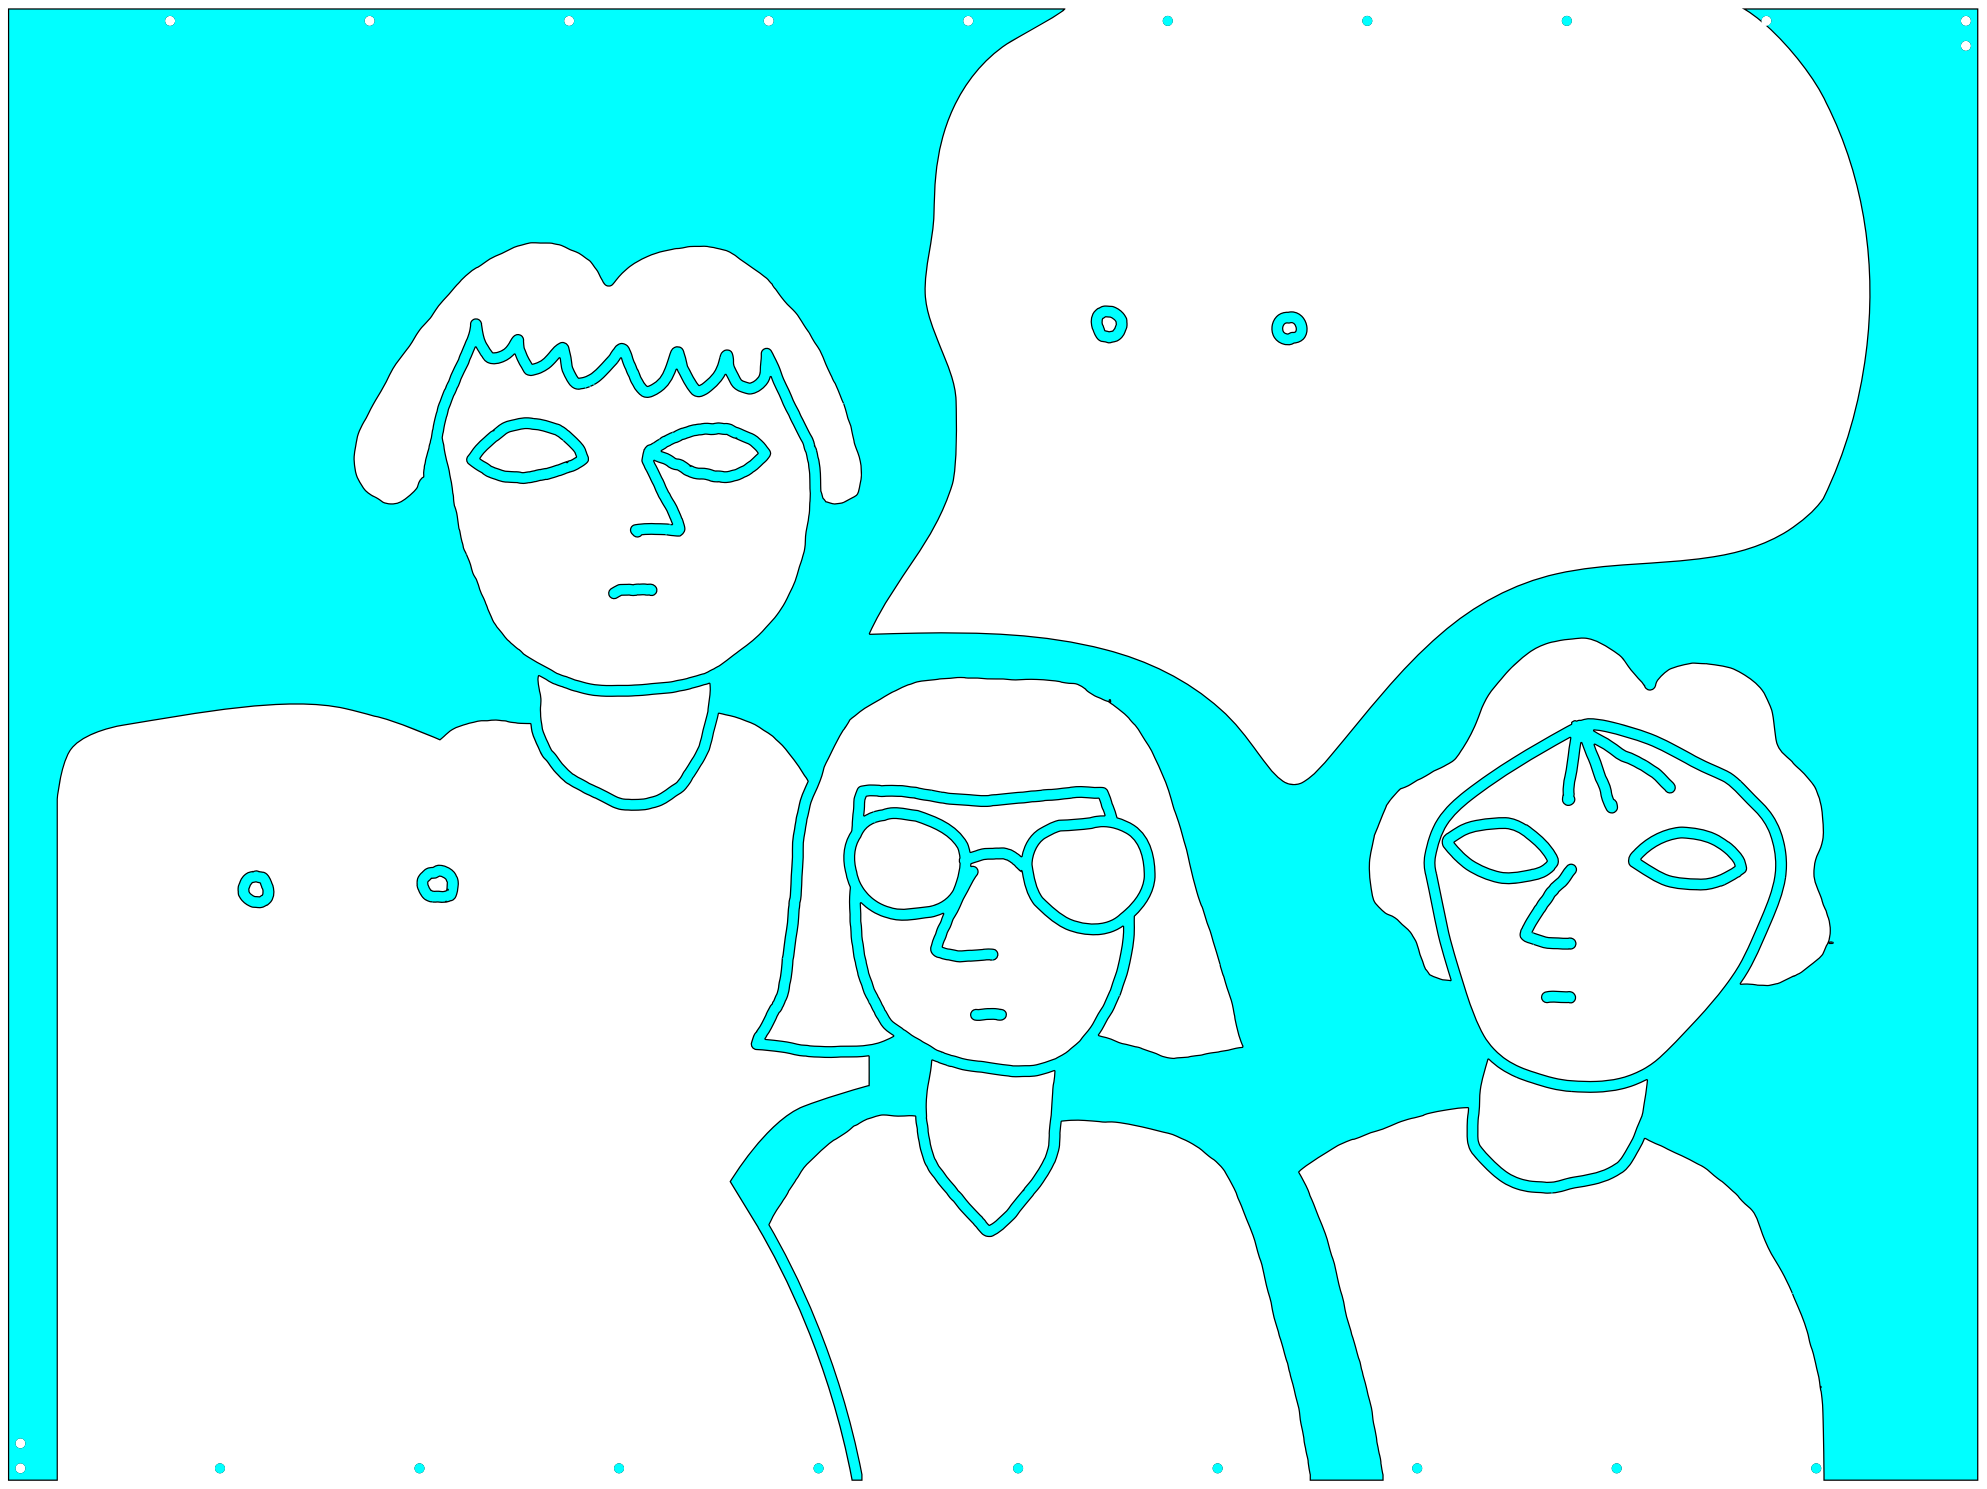
[picture p393: page 1]
