LeonLenclos/camera-obscura/contenu/animations/pixart/epilogue-1-pixart-artwork.pdf

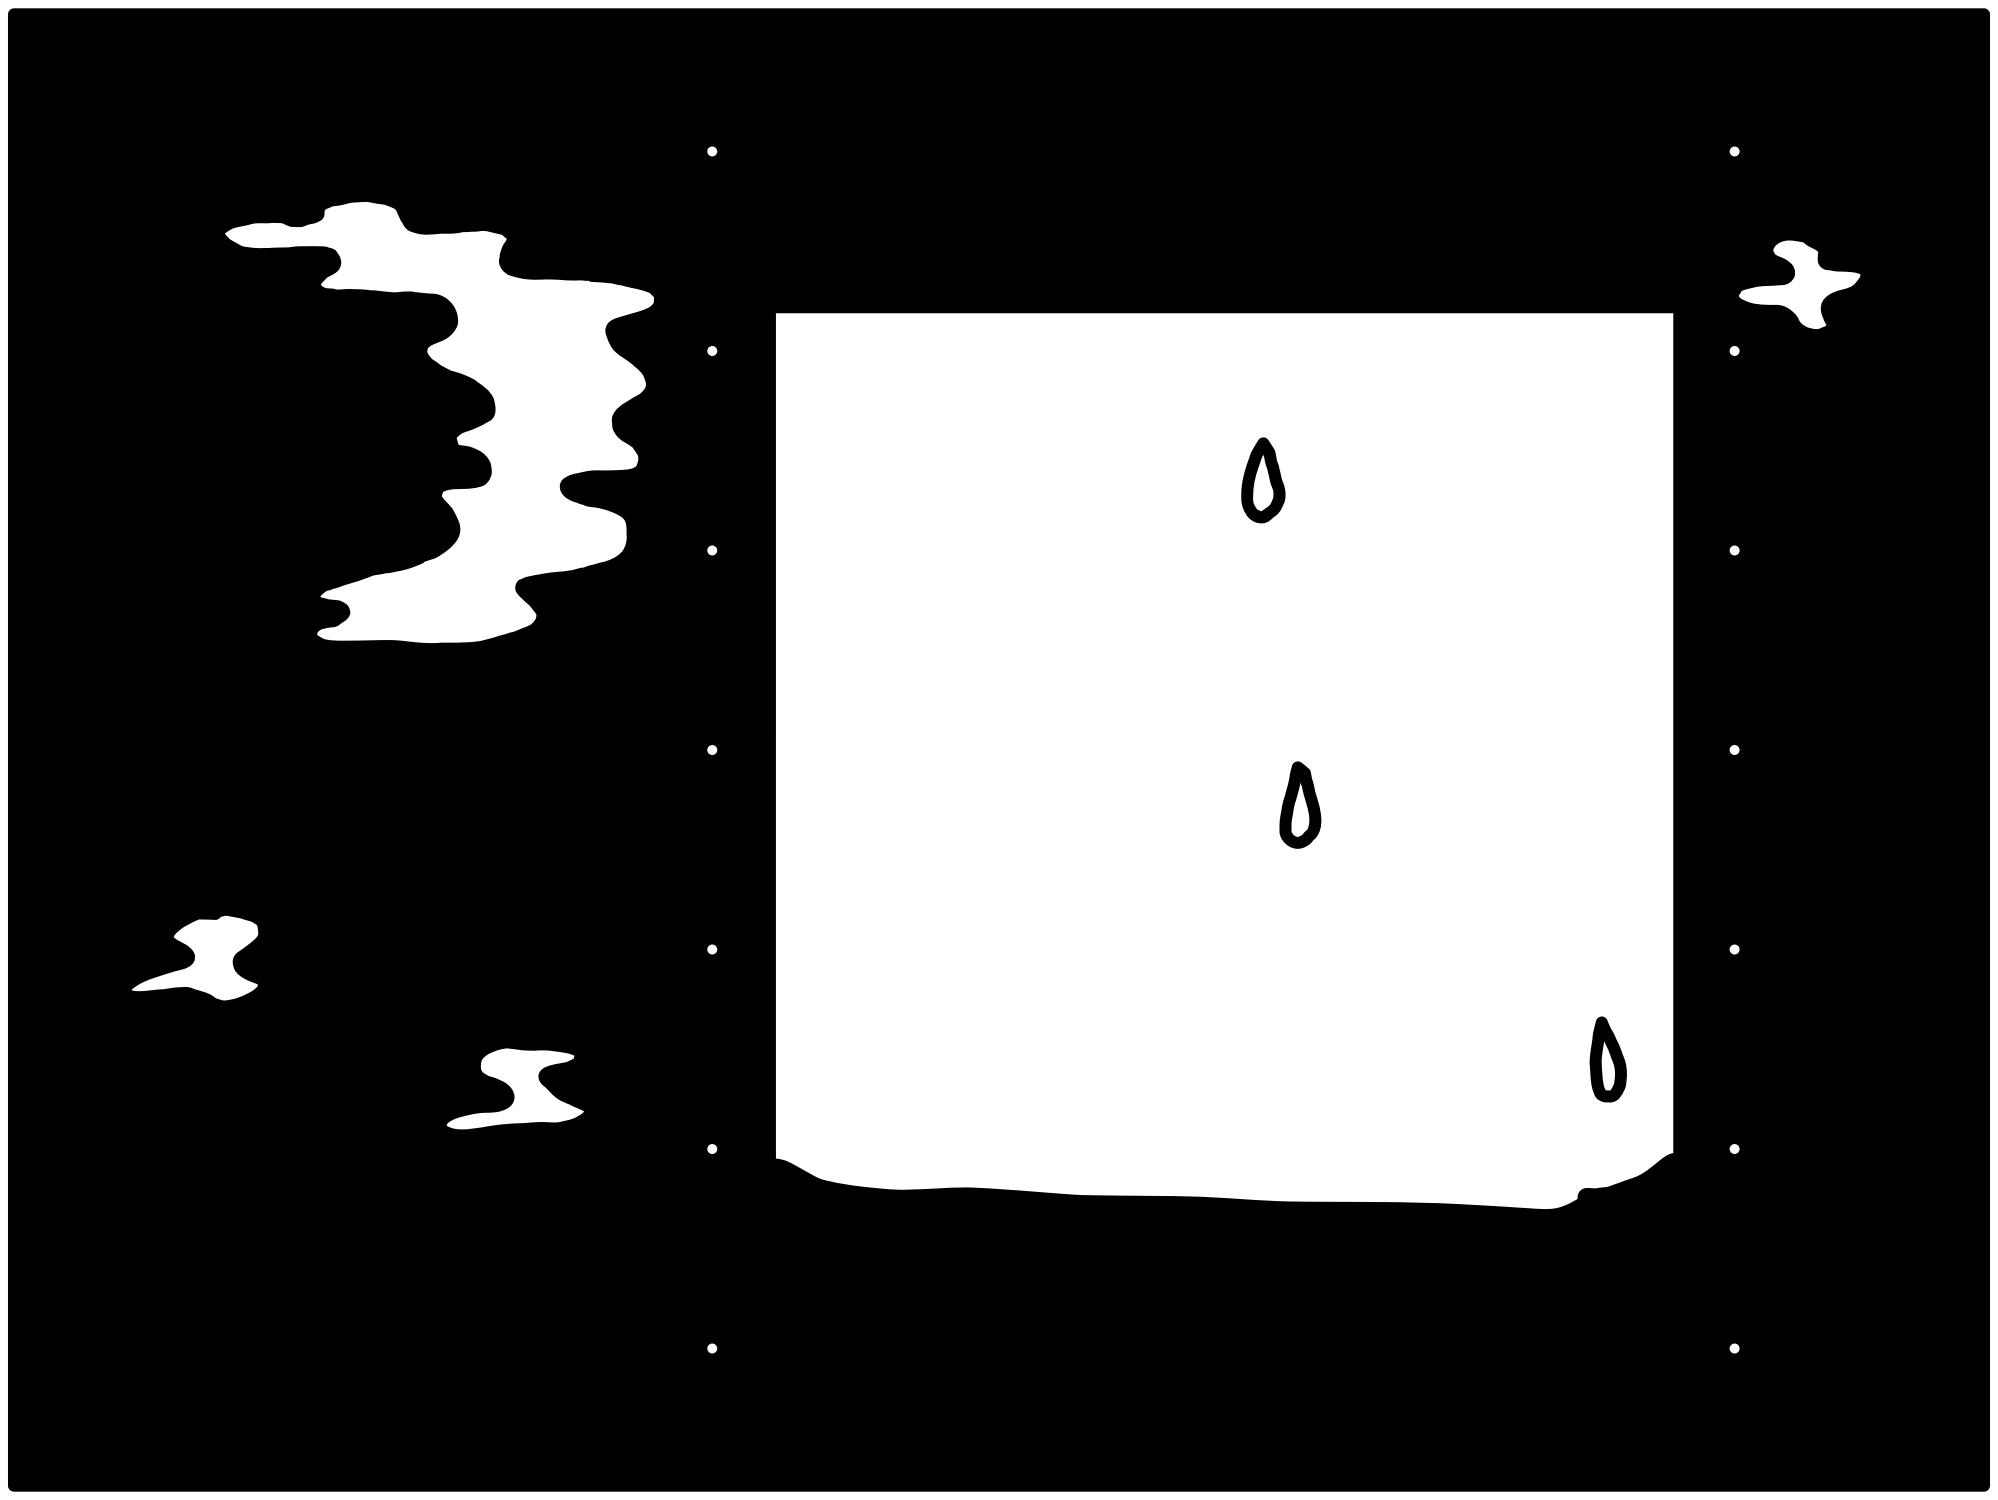
[picture p394: page 1]
