LeonLenclos/camera-obscura/contenu/animations/pixart/epilogue-1-pixart-white.pdf

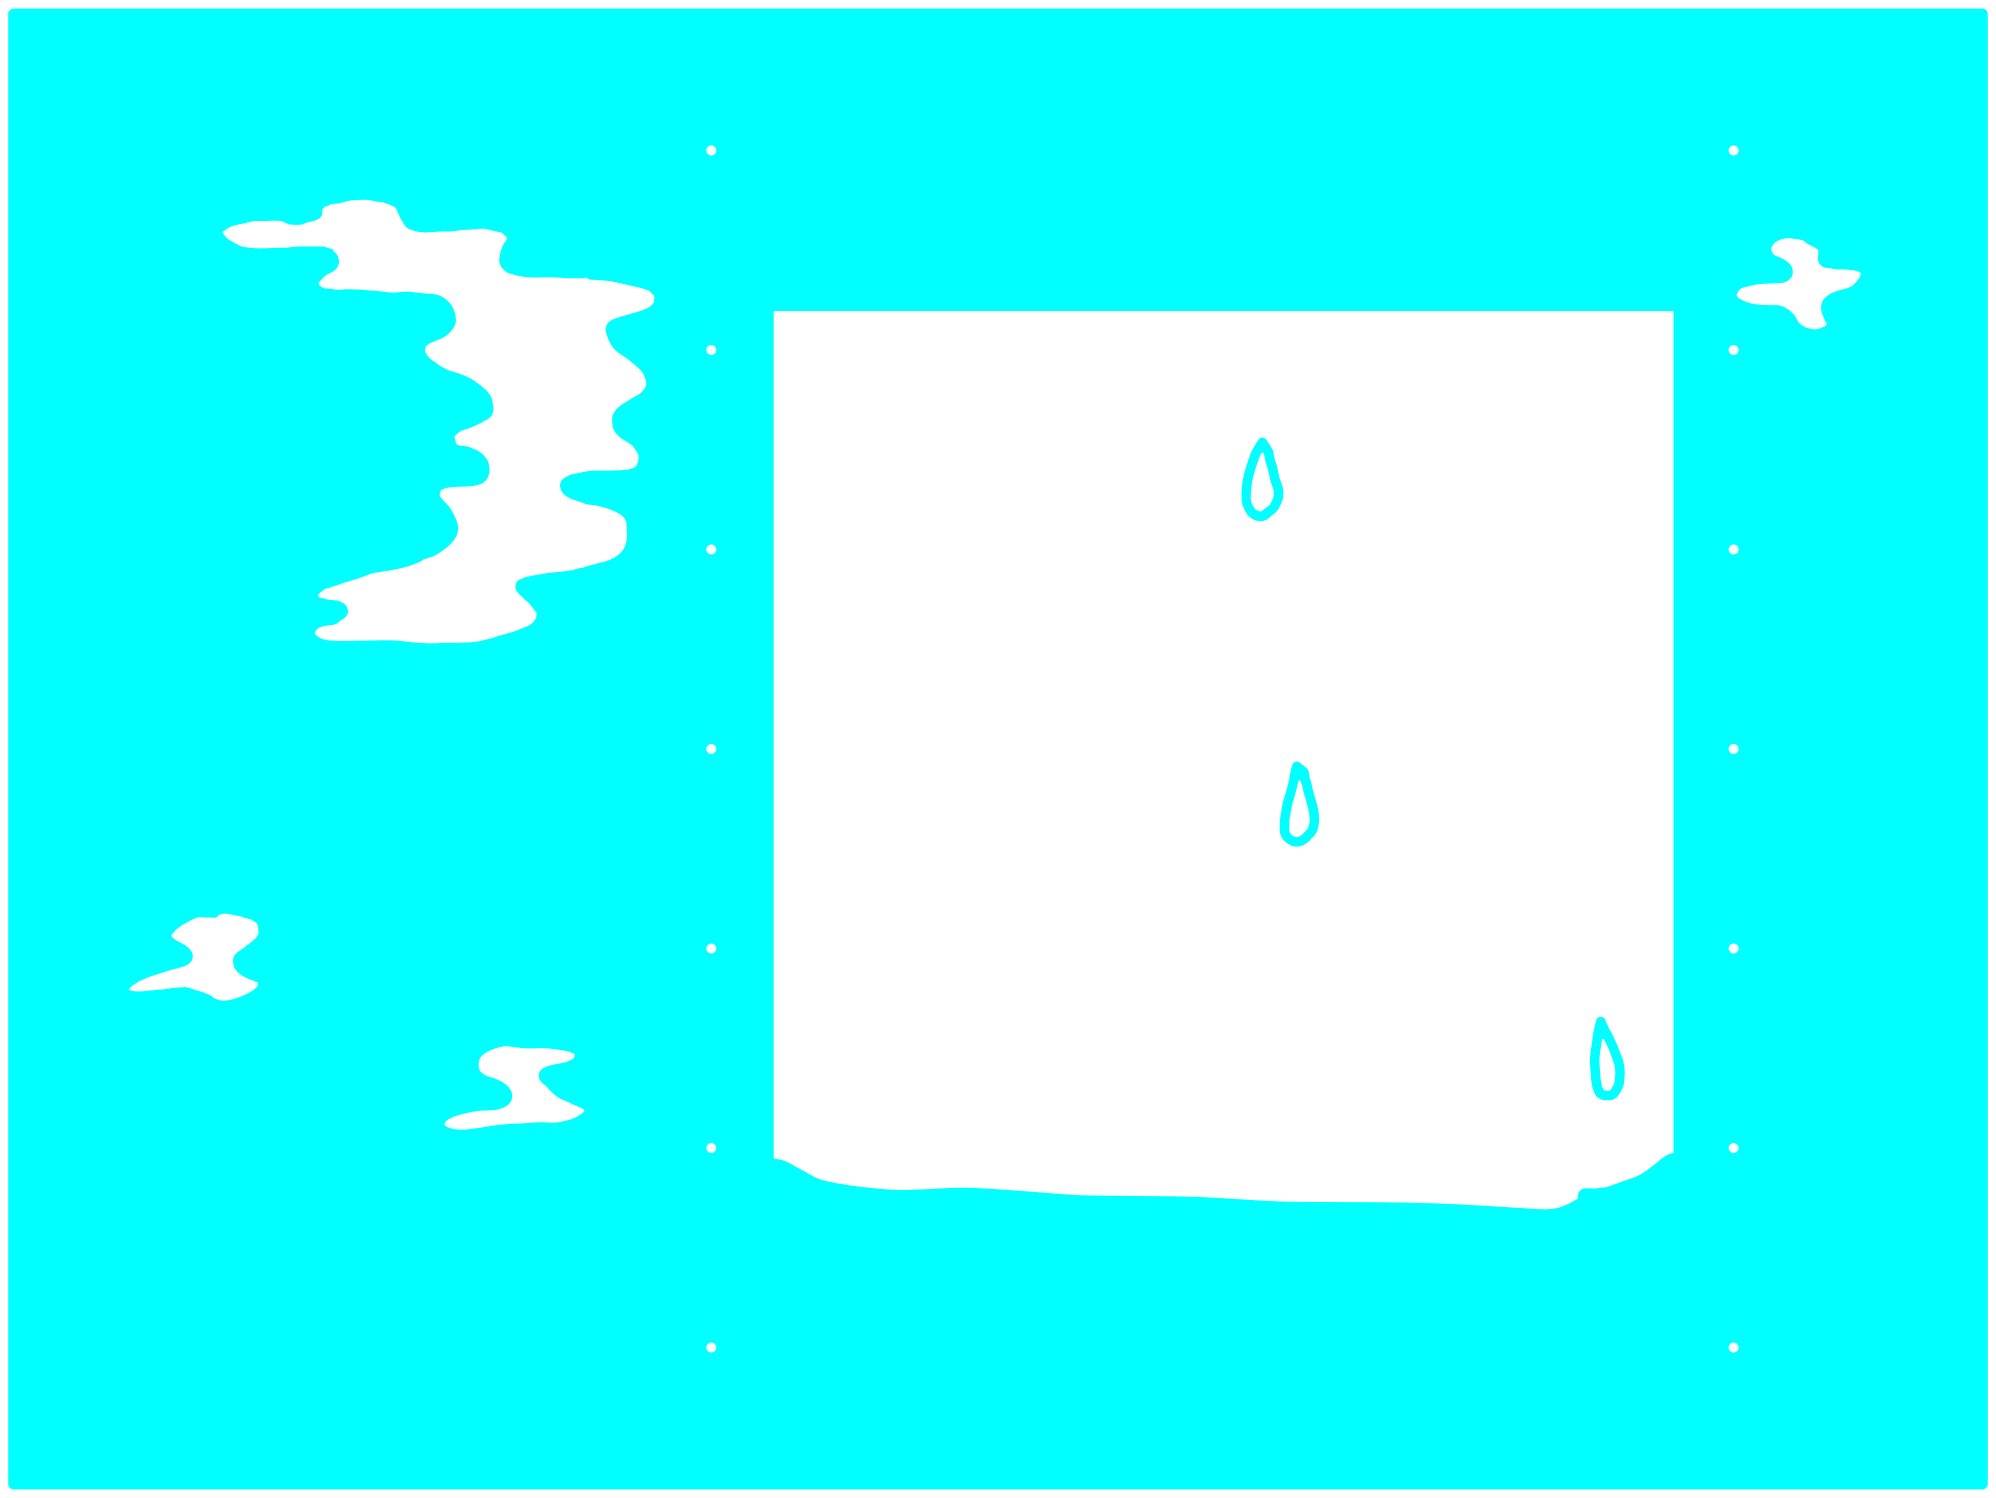
[picture p395: page 1]
