LeonLenclos/camera-obscura/contenu/animations/pixart/epilogue-1-pixart.pdf

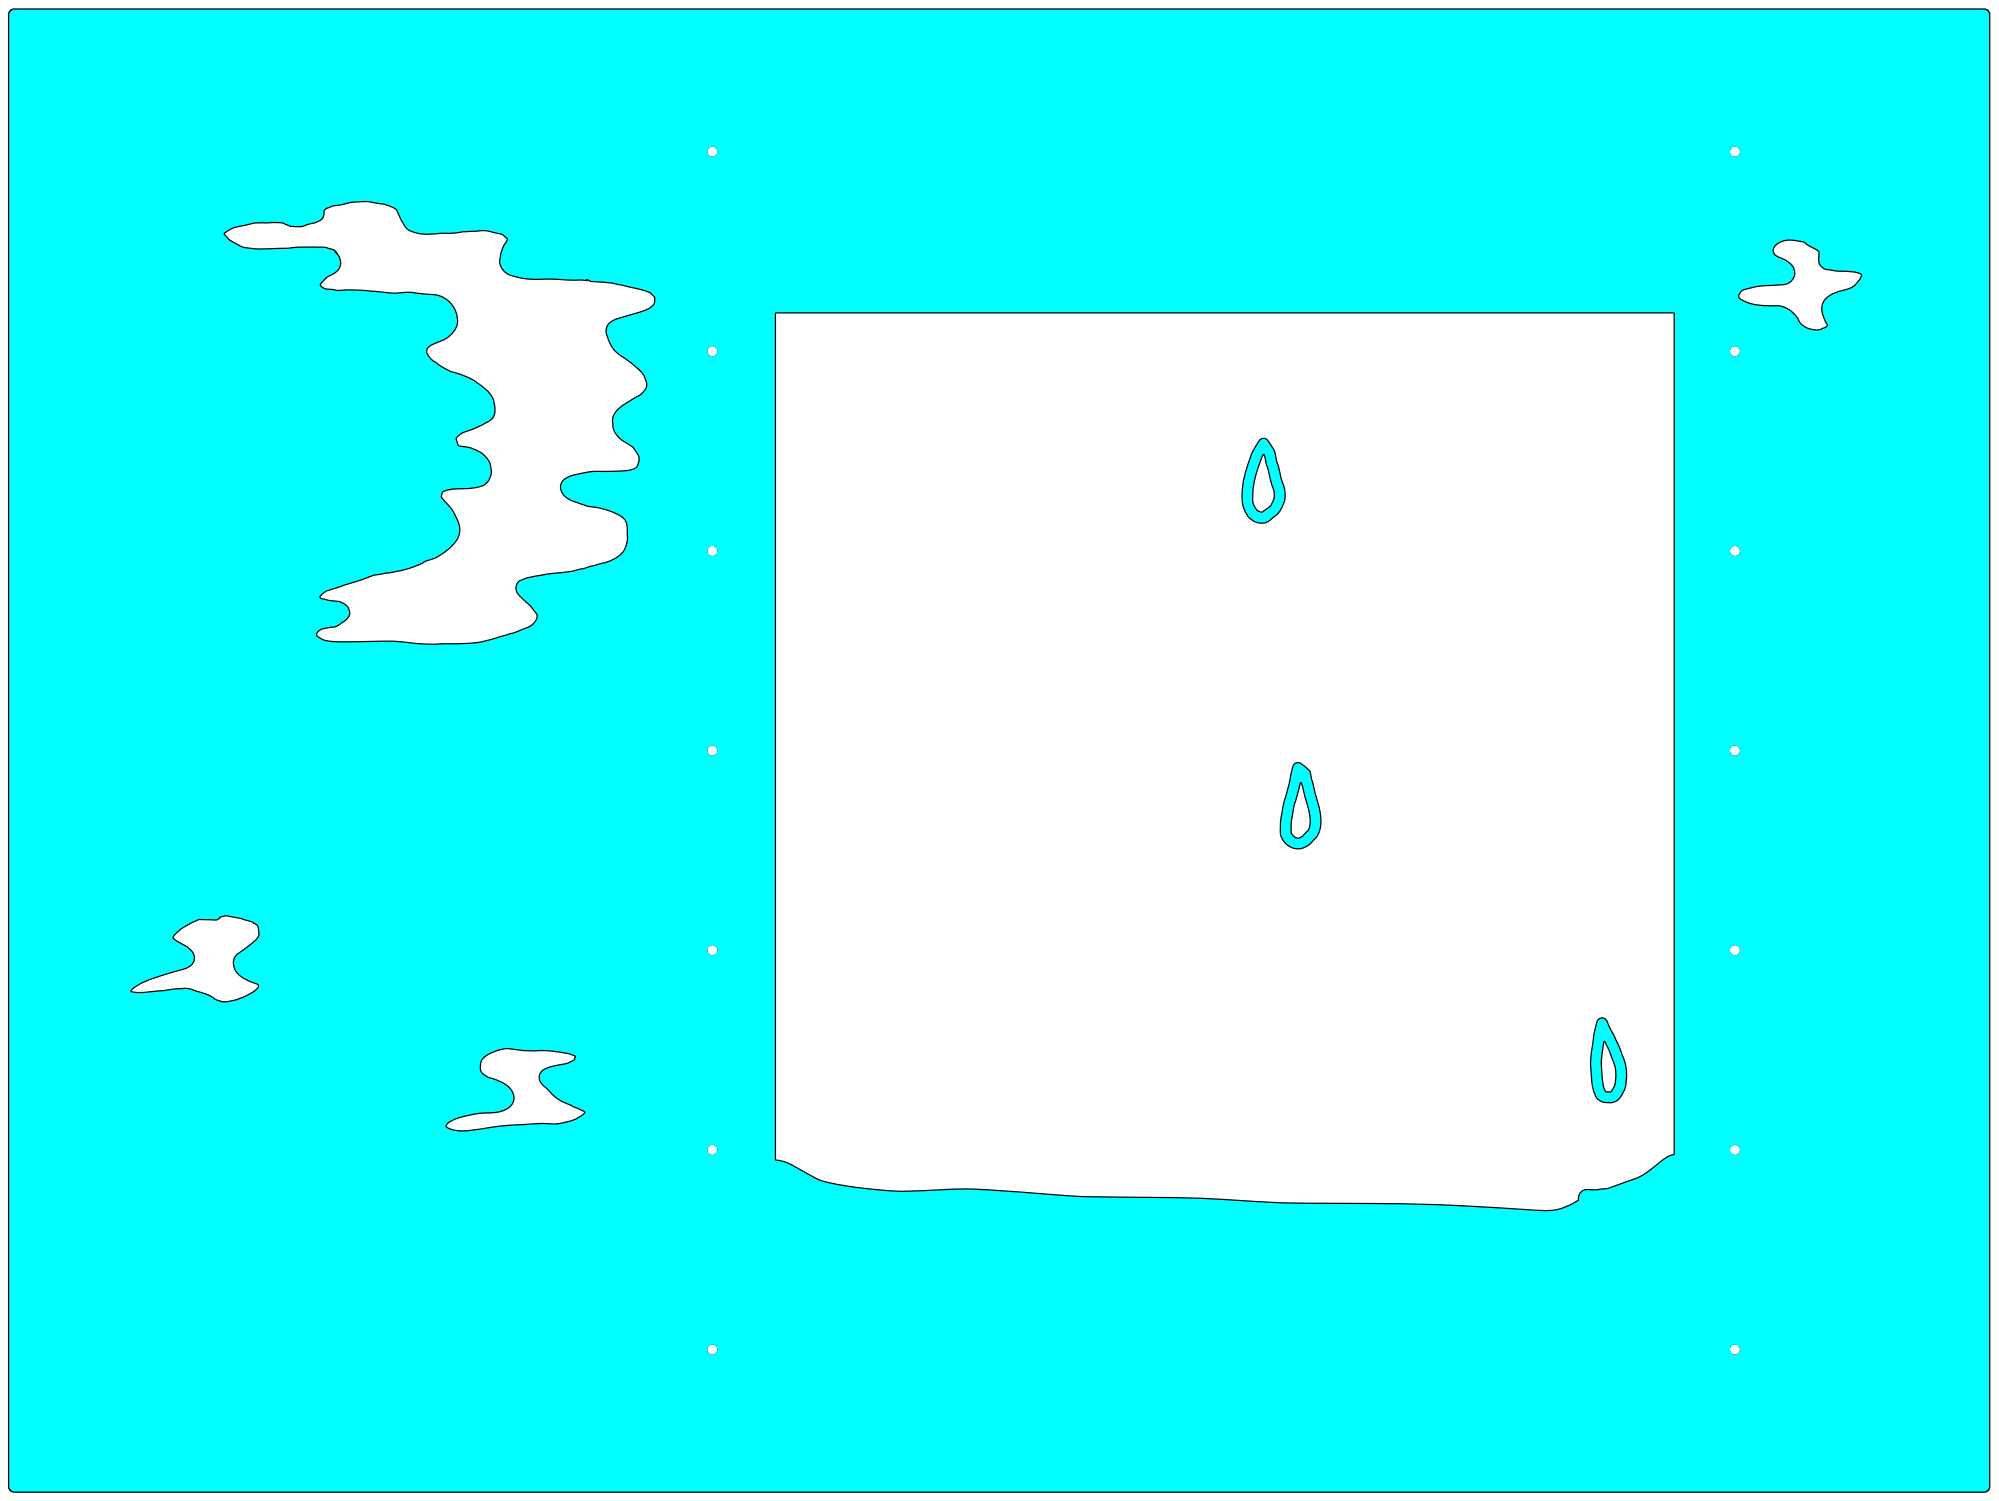
[picture p396: page 1]
