LeonLenclos/camera-obscura/contenu/animations/pixart/epilogue-2-pixart-artwork.pdf

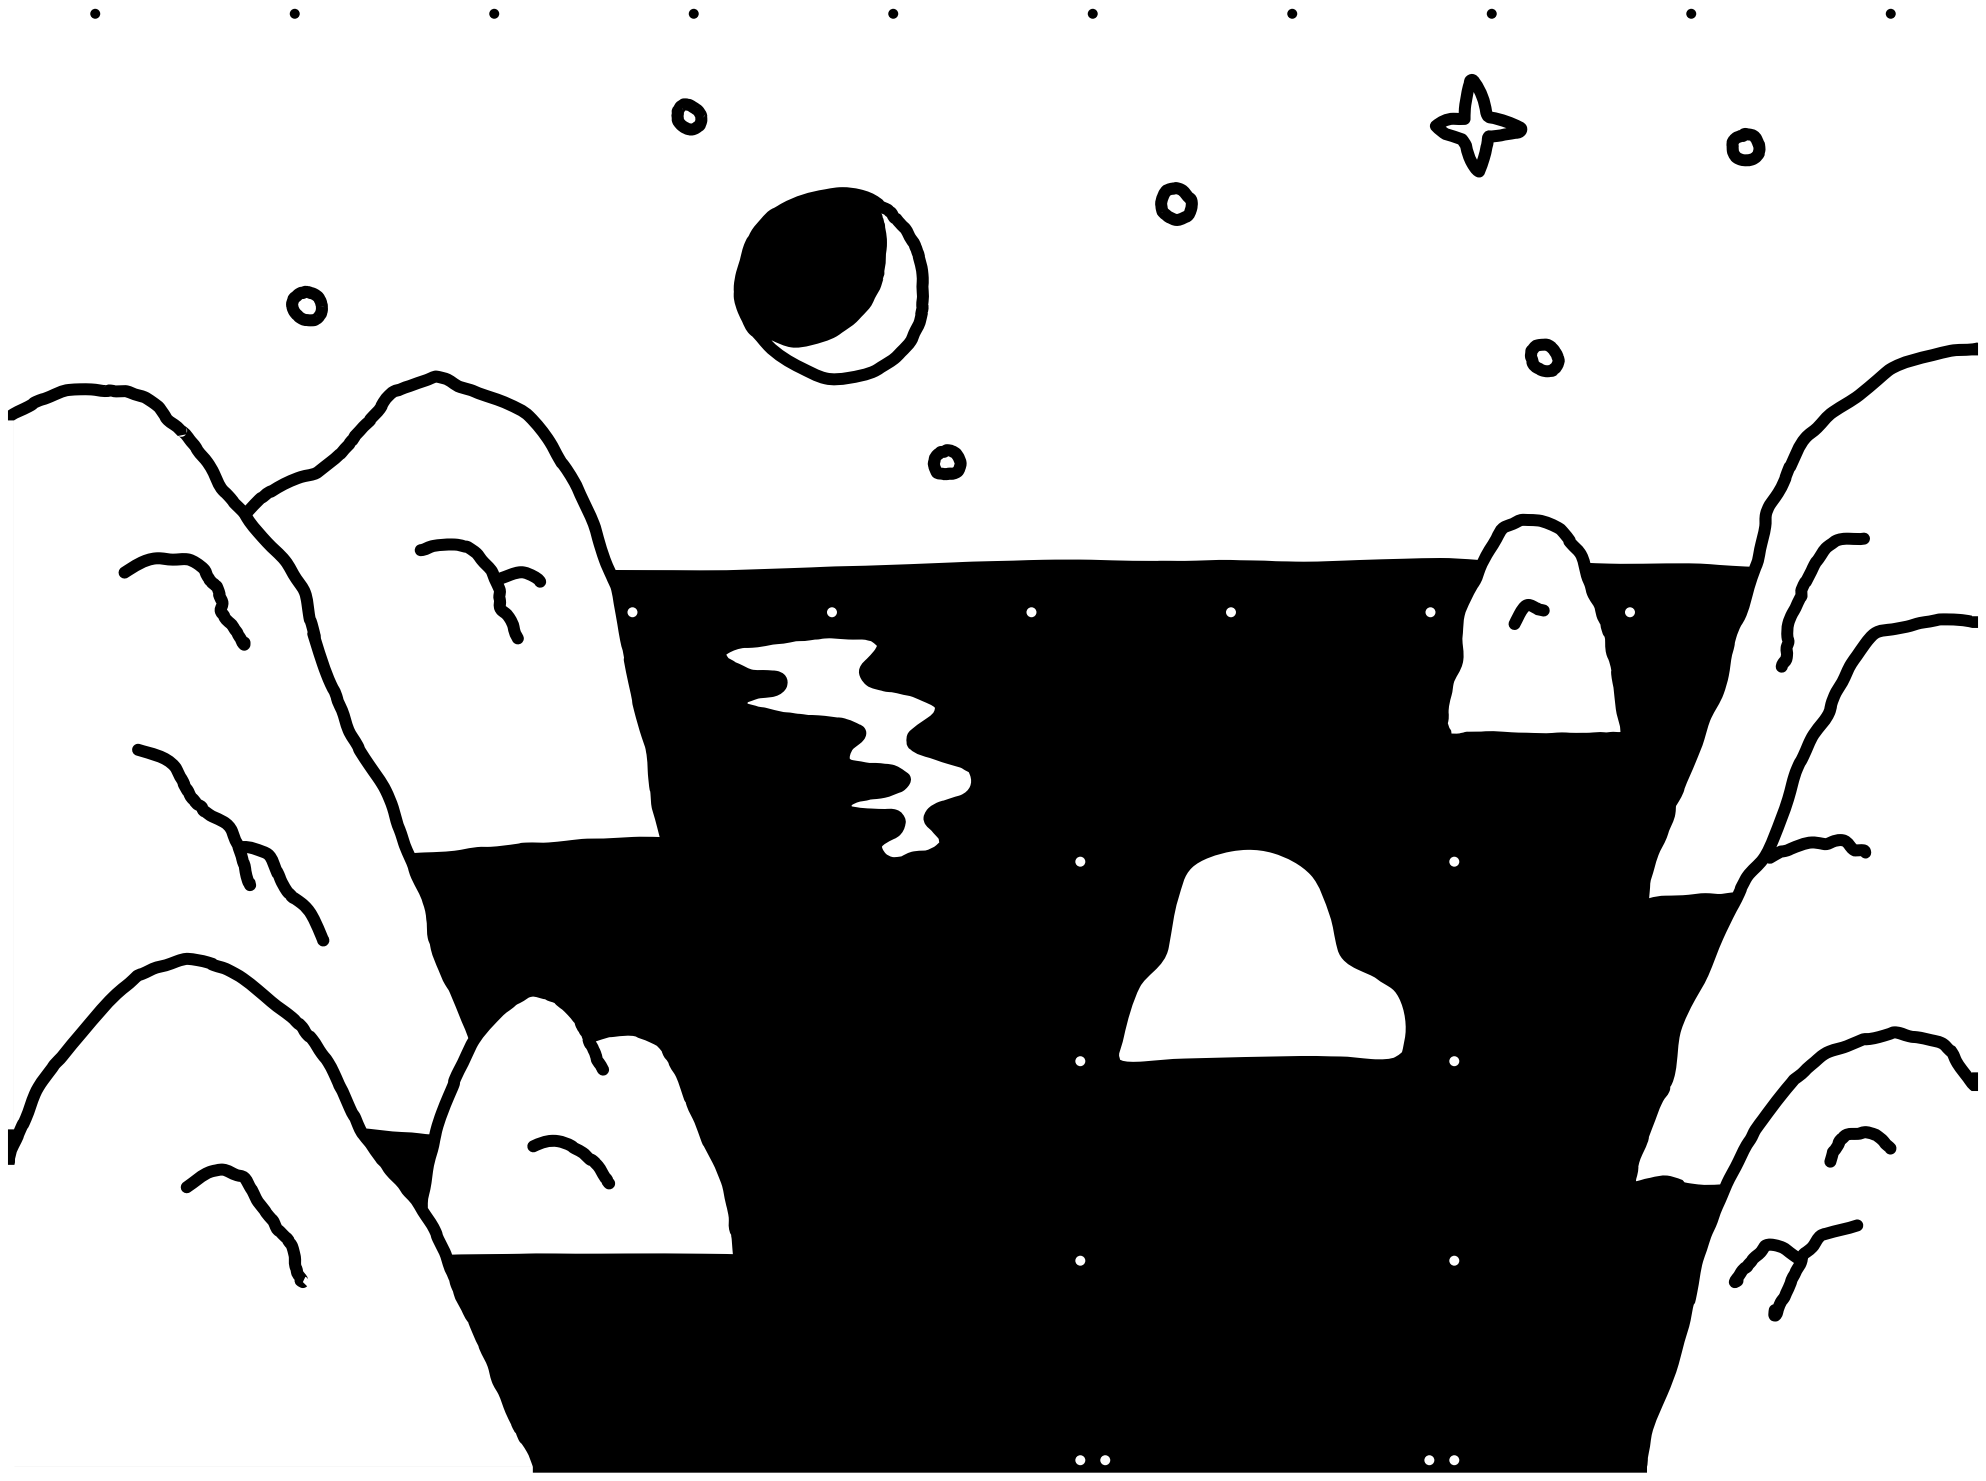
[picture p397: page 1]
