LeonLenclos/camera-obscura/contenu/animations/pixart/epilogue-2-pixart.pdf

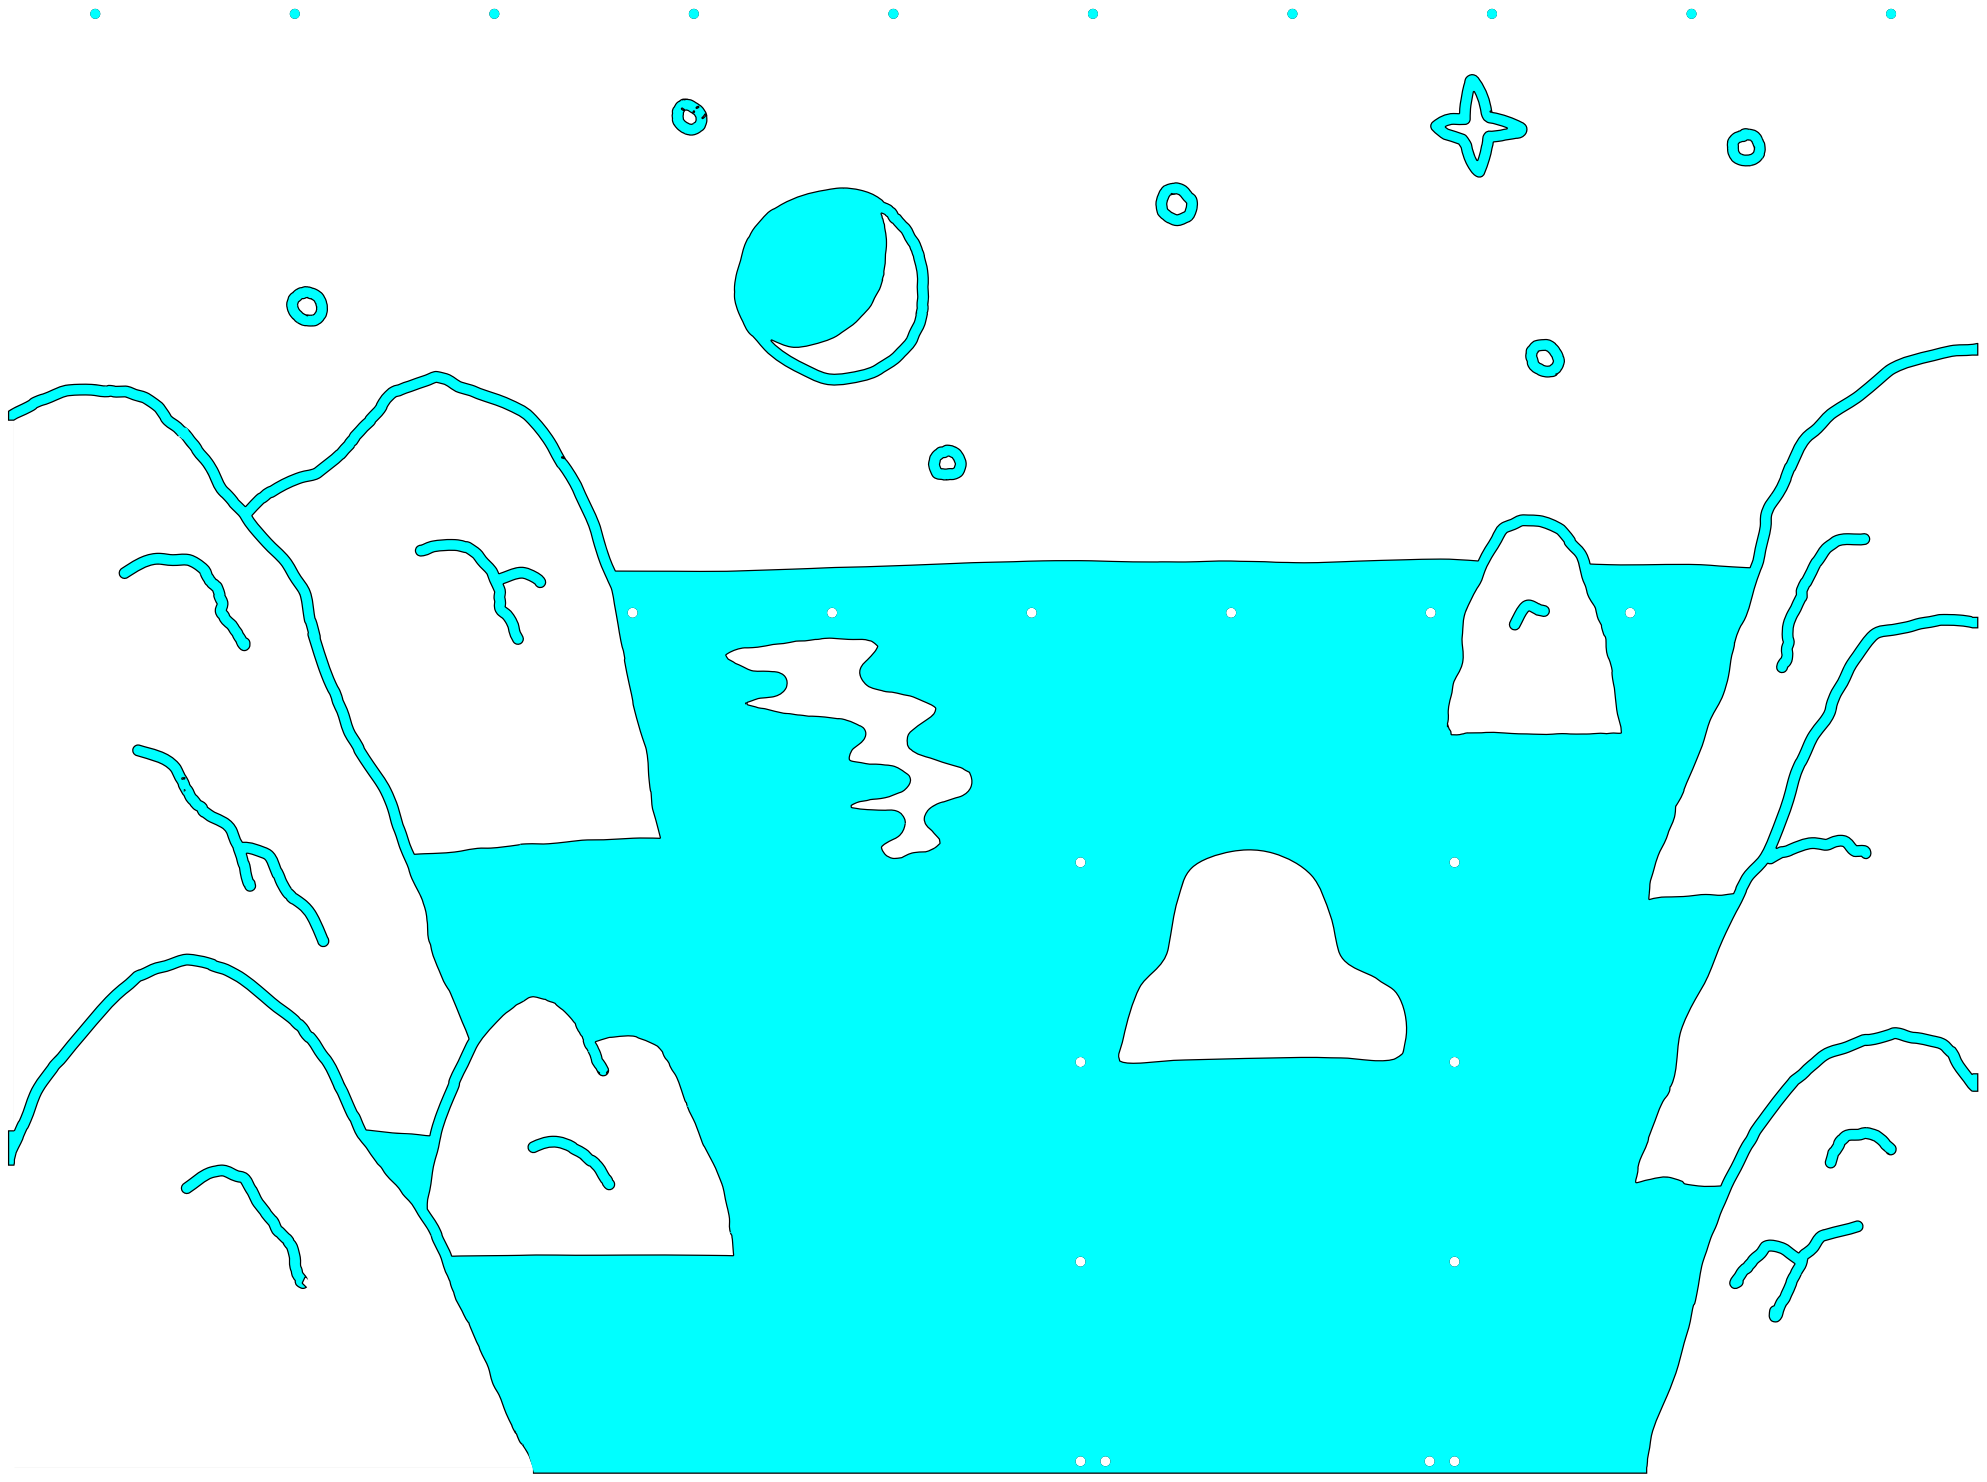
[picture p398: page 1]
